ElDominio/rusefi/.junie/ts-readme.md

- files: `firmware/tunerstudio/readme.md`
- TunerStudio Help Documentation: `.junie/ts-help-topic.md`
- TunerStudio Persistence: `firmware/tunerstudio/readme-persistence.md`
- Validation: Scan `firmware/tunerstudio/generated/rusefi_uaefi.ini` to verify final field names, gauge mappings, and output channel logic.
- UI Pattern: Prefer wrapping 3D tables/curves into a `dialog` with `border` layout, placing the table (West) and a status `panel` (East) side-by-side. The status panel should contain relevant gauges and calibration fields (e.g., offsets, PID status).
- TS templating: Names defined in `rusefi_config.txt` using `#define SOME_NAME "String Value"` can be used in `tunerstudio.template.ini` as `@@SOME_NAME@@`.
- Dialog/Panel validation: The build tool strictly validates that all referenced panels exist. Suffixes starting with `@@` (used for conditional visibility) are automatically ignored during name comparison.
- [UserDefined] section: Dialog and panel definitions should generally be placed in this section of the template to maintain organization.
- Gauge templates (`firmware/tunerstudio/gauge_declarations.ini`, `[GaugeConfigurations]`): `name = channel, title, units, Lo, Hi, LoD, LoW, HiW, HiD, vd, ld`. Lo/Hi are the scale limits; below LoD or above HiD TunerStudio renders the danger (error) color, below LoW / above HiW the warning color; vd/ld are value/label decimal places. To flag an out-of-range value as error with no warning band, set LoD=LoW and HiW=HiD (e.g. raw 5V sensor gauges use 0.2/0.2 and 4.8/4.8 so <0.2V or >4.8V shows as error). Source of truth: "EFI Analytics ECU Definition files" PDF at https://www.efianalytics.com/TunerStudio/docs/ (section 12, GaugeConfigurations).
