ElDominio/rusefi/firmware/controllers/lua/generated/value_lookup_generated.md

### startButtonSuppressOnStartUpMs
null

### launchRpm
The target engine speed (RPM) to maintain during launch.

### rpmHardLimit
set rpm_hard_limit X

### engineSnifferRpmThreshold
Engine sniffer would be disabled above this rpm\nset engineSnifferRpmThreshold X

### ltitEnabled
Enable LTIT (Long Term Idle Trim) learning

### useMetricOnInterface

### useLambdaOnInterface

### multisparkMaxRpm
Disable multispark above this engine speed.

### maxAcRpm
Above this RPM, disable AC. Set to 0 to disable check.

### maxAcTps
Above this TPS, disable AC. Set to 0 to disable check.

### maxAcClt
Above this CLT, disable AC to prevent overheating the engine. Set to 0 to disable check.

### compressionRatio
Just for reference really, not taken into account by any logic at this point

### idlePositionMin
Voltage when the idle valve is closed.\nYou probably don't have one of these!

### idlePositionMax
Voltage when the idle valve is open.\nYou probably don't have one of these!\n1 volt = 1000 units

### ltitEmaAlpha
EMA filter constant for LTIT (0-255)

### ltitStableRpmThreshold
RPM range to consider stable idle

### ltitStableTime
Minimum time of stable idle before learning

### ltitCorrectionRate
LTIT learning rate

### ltitIgnitionOnDelay
Delay after ignition ON before LTIT learning/application

### ltitIgnitionOffSaveDelay
Delay after ignition OFF before LTIT save

### ltitClampMin
Minimum LTIT multiplicative correction value

### ltitClampMax
Maximum LTIT multiplicative correction value

### ltitSmoothingIntensity
LTIT table regional smoothing intensity (0=no smoothing)

### ltitIntegratorThreshold
Minimum threshold of PID integrator for LTIT correction

### launchFuelAdderPercent
Fuel enrichment adder percentage.

### etbJamTimeout
Time after which the throttle is considered jammed.

### primingTriggerTeeth
Number of primary trigger teeth to see (since ignition-on) before firing the priming pulse. Counting is raw and does not require trigger sync. Only used when 'primeOnTriggerTeeth' is enabled.

### multisparkMaxSparkingAngle
This parameter sets the latest that the last multispark can occur after the main ignition event. For example, if the ignition timing is 30 degrees BTDC, and this parameter is set to 45, no multispark will ever be fired after 15 degrees ATDC.

### multisparkMaxExtraSparkCount
Configures the maximum number of extra sparks to fire (does not include main spark)

### vvtControlMinRpm

### injector.flow
This is your injector flow at the fuel pressure used in the vehicle\nSee units setting below

### injectorSecondary.flow
This is your injector flow at the fuel pressure used in the vehicle\nSee units setting below

### isForcedInduction
Does the vehicle have a turbo or supercharger?

### useFordRedundantTps
On some Ford and Toyota vehicles one of the throttle sensors is not linear on the full range, i.e. in the specific range of the positions we effectively have only one sensor.

### enableKline

### overrideTriggerGaps

### chtSensorPulldown

### useLinearChtSensor

### enableTrailingSparks
Enable secondary spark outputs that fire after the primary (rotaries, twin plug engines).

### etb_use_two_wires
TLE7209 and L6205 use two-wire mode. TLE9201 and VNH2SP30 do NOT use two wire mode.

### isDoubleSolenoidIdle
Subaru/BMW style where default valve position is somewhere in the middle. First solenoid opens it more while second can close it more than default position.

### useEeprom

### useCicPidForIdle
Switch between Industrial and Cic PID implementation

### useTLE8888_cranking_hack

### kickStartCranking
Kick-start cranking mode: below 800 RPM both coils are charged right at the trigger mark and fired a dwell-time later, normal spark scheduling is suppressed.

### useSeparateIdleTablesForCrankingTaper
This uses separate ignition timing and VE tables not only for idle conditions, also during the postcranking-to-idle taper transition (See also afterCrankingIACtaperDuration).

### launchControlEnabled

### antiLagEnabled

### useRunningMathForCranking
For cranking either use the specified fixed base fuel mass, or use the normal running math (VE table). Note: in 'Fuel Map' (running math) mode the base mass already reflects the flex-adjusted stoich ratio, so the cranking flex multipliers act as ADDITIONAL enrichment on top of that - do not re-apply the full ethanol correction there.

### crankingAirAmountEnabled
Enable CLT-based cranking air amount table. During cranking, open-loop valve position is taken from this table instead of the running idle tables.

### crankingIdleRpmFlareEnabled
Enable CLT-based cranking idle RPM flare. An RPM adder from the table is applied during cranking, tapering to zero as the engine transitions to idle.

### displayLogicLevelsInEngineSniffer
Shall we display real life signal or just the part consumed by trigger decoder.\nApplies to both trigger and cam/vvt input.

### useTLE8888_stepper

### usescriptTableForCanSniffingFiltering

### verboseCan
Print incoming and outgoing first bus CAN messages in rusEFI console

### artificialTestMisfire
Experimental setting that will cause a misfire\nDO NOT ENABLE.

### useFordRedundantPps
On some Ford and Toyota vehicles one of the pedal sensors is not linear on the full range, i.e. in the specific range of the positions we effectively have only one sensor.

### cltSensorPulldown

### iatSensorPulldown

### allowIdenticalPps

### overrideVvtTriggerGaps

### useSpiImu
If enabled - use onboard SPI Accelerometer, otherwise listen for CAN messages

### enableStagedInjection

### useIdleAdvanceWhileCoasting

### tpsErrorDetectionTooLow
TPS error detection: what throttle % is unrealistically low?\nAlso used for accelerator pedal error detection if so equipped.

### tpsErrorDetectionTooHigh
TPS error detection: what throttle % is unrealistically high?\nAlso used for accelerator pedal error detection if so equipped.

### cranking.rpm
This sets the RPM limit below which the ECU will use cranking fuel and ignition logic, typically this is around 350-450rpm. \nset cranking_rpm X

### ignitionDwellForCrankingMs
Dwell duration while cranking

### etbRevLimitRange
RPM below the hard RPM limit at which the ETB rev limiter PID starts managing throttle position. Below this window throttle control is normal.

### etbRevLimitSeedTps
Throttle position the ETB rev limiter PID seeds itself with as soon as it engages, so it starts near the right operating point instead of ramping up from zero.

### etbRevLimitKp
Proportional gain for the ETB rev limiter PID.

### etbRevLimitKi
Integral gain for the ETB rev limiter PID.

### etbRevLimitKd
Derivative gain for the ETB rev limiter PID.

### map.sensor.lowValue
kPa/psi value at low volts

### map.sensor.highValue
kPa/psi value at high volts

### clt.config.tempC_1

### clt.config.tempC_2

### clt.config.tempC_3

### clt.config.resistance_1

### clt.config.resistance_2

### clt.config.resistance_3

### clt.config.bias_resistor
Pull-up resistor value on your board

### iat.config.tempC_1

### iat.config.tempC_2

### iat.config.tempC_3

### iat.config.resistance_1

### iat.config.resistance_2

### iat.config.resistance_3

### iat.config.bias_resistor
Pull-up resistor value on your board

### launchTimingRetard
The target absolute ignition timing value (e.g., -10 means -10 degrees, not 10 degrees of retard relative to base timing).

### idleMaximumAirmass
Maximum commanded airmass for the idle controller.

### alternator_iTermMin
iTerm min value

### alternator_iTermMax
iTerm max value

### displacement
@@DISPLACEMENT_TOOLTIP@@

### triggerSimulatorRpm

### cylindersCount
Number of cylinder the engine has.

### justATempTest
null

### mapSyncThreshold
Delta kPa/psi for MAP sync

### cylinderBore
@@CYLINDER_BORE_TOOLTIP@@

### ALSMaxTPS

### boostControlMinRpm
Minimum RPM to enable boost control. Use this to avoid solenoid noise at idle, and help spool in some cases.

### boostControlMinTps
Minimum TPS to enable boost control. Use this to avoid solenoid noise at idle, and help spool in some cases.

### boostControlMinMap
Minimum MAP to enable boost control. Use this to avoid solenoid noise at idle, and help spool in some cases.

### crankingTimingAngle
Ignition advance angle used during engine cranking, 5-10 degrees will work as a base setting for most engines.\nThere is tapering towards running timing advance\nset cranking_timing_angle X

### gapTrackingLengthOverride
How many consecutive gap rations have to match expected ranges for sync to happen

### maxIdleVss
Above this speed, disable closed loop idle control. Set to 0 to disable (allow closed loop idle at any speed).

### camDecoder2jzPrecision
Allowed range around detection position

### minOilPressureAfterStart
Expected oil pressure after starting the engine. If oil pressure does not reach this level within 5 seconds of engine start, fuel will be cut. Set to 0 to disable and always allow starting.

### fixedModeTiming
This value is the ignition timing used when in 'fixed timing' mode, i.e. constant timing\nThis mode is useful when adjusting distributor location.

### globalTriggerAngleOffset
Angle between Top Dead Center (TDC) and the first trigger event.\nPositive value in case of synchronization point before TDC and negative in case of synchronization point after TDC\n.Knowing this angle allows us to control timing and other angles in reference to TDC.\nHOWTO:\n1: Switch to fixed timing mode on 'ignition setting' dialog\n2: use an actual timing light to calibrate\n3: add/subtract until timing light confirms desired fixed timing value!'

### analogInputDividerCoefficient
Ratio/coefficient of input voltage dividers on your PCB. For example, use '2' if your board divides 5v into 2.5v. Use '1.66' if your board divides 5v into 3v.

### vbattDividerCoeff
This is the ratio of the resistors for the battery voltage, measure the voltage at the battery and then adjust this number until the gauge matches the reading.

### fanOnTemperature
Cooling fan turn-on temperature threshold, in Celsius

### fanOffTemperature
Cooling fan turn-off temperature threshold, in Celsius

### fan2OnTemperature
Cooling fan turn-on temperature threshold, in Celsius

### fan2OffTemperature
Cooling fan turn-off temperature threshold, in Celsius

### disableFan1AtSpeed
null

### disableFan2AtSpeed
null

### disableFan1AtSpeedHysteresis
Hysteresis below the disable-at-speed threshold before the fan is allowed back on. Prevents rapid on/off cycling at the threshold speed.

### disableFan2AtSpeedHysteresis
Hysteresis below the disable-at-speed threshold before the fan is allowed back on. Prevents rapid on/off cycling at the threshold speed.

### disableFan1WhenStopped
Inhibit operation of this fan while the engine is not running.

### disableFan2WhenStopped
Inhibit operation of this fan while the engine is not running.

### fan1PwmEnabled
Enable PWM mode for Fan 1. When enabled, the fan output is driven by the PWM curve instead of on/off relay logic.

### fan2PwmEnabled
Enable PWM mode for Fan 2. When enabled, the fan output is driven by the PWM curve instead of on/off relay logic.

### fan1PwmFrequency
Fan 1 PWM frequency

### fan2PwmFrequency
Fan 2 PWM frequency

### fan1MinPwm
Minimum PWM output clamp (Fan 1)

### fan1MaxPwm
Maximum PWM output clamp (Fan 1)

### fan2MinPwm
Minimum PWM output clamp (Fan 2)

### fan2MaxPwm
Maximum PWM output clamp (Fan 2)

### fan1AcAdder
PWM adder when AC compressor is active (Fan 1)

### fan2AcAdder
PWM adder when AC compressor is active (Fan 2)

### fan1SoftStartSec
Soft-start ramp time ? how long to ramp from 0 to target PWM (Fan 1)

### fan2SoftStartSec
Soft-start ramp time ? how long to ramp from 0 to target PWM (Fan 2)

### wizardPanelToShow

### driveWheelRevPerKm
Number of revolutions per kilometer for the wheels your vehicle speed sensor is connected to. Use an online calculator to determine this based on your tire size.

### canSleepPeriodMs
CANbus thread period in ms

### byFirmwareVersion

### idle_derivativeFilterLoss
0.1 is a good default value

### trigger.customTotalToothCount

### trigger.customSkippedToothCount

### airByRpmTaper
Extra air taper amount

### boostControlSafeDutyCycle
Duty cycle to use in case of a sensor failure. This duty cycle should produce the minimum possible amount of boost. This duty is also used in case any of the minimum RPM/TPS/MAP conditions are not met.

### acrRevolutions

### calibrationBirthday
null

### adcVcc

### mapCamDetectionAnglePosition
Magic engine phase: we compare instant MAP at X to instant MAP at x+360 angle in one complete cycle

### afr.v1

### afr.value1

### afr.v2

### afr.value2

### etbSplit
TPS/PPS error threshold

### baroSensor.lowValue
kPa/psi value at low volts

### baroSensor.highValue
kPa/psi value at high volts

### idle.solenoidFrequency

### knockRetardAggression
Ignition timing to remove when a knock event occurs. Advice: 5% (mild), 10% (turbo/high comp.), 15% (high knock, e.g. GDI), 20% (spicy lump),

### knockRetardReapplyRate
After a knock event, reapply timing at this rate.

### vssGearRatio
Number of turns of your vehicle speed sensor per turn of the wheels. For example if your sensor is on the transmission output, enter your axle/differential ratio. If you are using a hub-mounted sensor, enter a value of 1.0.

### vssFilterReciprocal
Set this so your vehicle speed signal is responsive, but not noisy. Larger value give smoother but slower response.

### vssToothCount
Number of pulses output per revolution of the shaft where your VSS is mounted. For example, GM applications of the T56 output 17 pulses per revolution of the transmission output shaft.

### vssMaxAcceleration
Reject VSS pulses that imply a faster acceleration or deceleration than this, and dead-reckon speed from the last known rate of change instead. Helps reject a single noisy tooth. Set to 0 to disable.

### fuelPumpControl.pFactor

### fuelPumpControl.iFactor

### fuelPumpControl.dFactor

### fuelPumpControl.offset
Linear addition to PID logic\nAlso known as feedforward.

### fuelPumpControl.periodMs
PID dTime

### fuelPumpControl.minValue
Output Min Duty Cycle

### fuelPumpControl.maxValue
Output Max Duty Cycle

### gapVvtTrackingLengthOverride
How many consecutive VVT gap rations have to match expected ranges for sync to happen

### idle_antiwindupFreq
0.1 is a good default value

### mc33_t_min_boost
Minimum allowed time for the boost phase. If the boost target current is reached before this time elapses, it is assumed that the injector has failed short circuit.

### finalGearRatio
Ratio between the wheels and your transmission output.

### tcuInputSpeedSensorTeeth
null

### fordInjectorSmallPulseSlope

### lambdaProtectionMinRpm

### lambdaProtectionMinLoad

### is_enabled_spi_1

### is_enabled_spi_2

### is_enabled_spi_3

### isSdCardEnabled

### rusefiVerbose29b
Use 11 bit (standard) or 29 bit (extended) IDs for rusEFI verbose CAN format.

### rethrowHardFault

### verboseQuad

### useStepperIdle
This setting should only be used if you have a stepper motor idle valve and a stepper motor driver installed.

### lambdaProtectionEnable

### verboseTLE8888

### enableVerboseCanTx
CAN broadcast using custom rusEFI protocol

### externalRusEfiGdiModule

### measureMapOnlyInOneCylinder
Useful for individual intakes

### stepperForceParkingEveryRestart

### isFasterEngineSpinUpEnabled
If enabled, RPM is estimated from ~90 degrees of rotation using tooth timestamps collected even before trigger sync, and fuel/ignition scheduling starts as soon as the trigger syncs (sequential ignition temporarily runs as wasted spark until full phase sync). As soon as the trigger syncs plus 90 degrees rotation, fuel and ignition events will occur. If disabled, worst case may require up to 4 full crank rotations before any events are scheduled.

### coastingFuelCutEnabled
This setting disables fuel injection while the engine is in overrun, this is useful as a fuel saving measure and to prevent back firing.

### useIacTableForCoasting
Override the IAC position during overrun conditions to help reduce engine breaking, this can be helpful for large engines in light weight cars or engines that have trouble returning to idle.

### useNoiselessTriggerDecoder

### useIdleTimingPidControl

### disableEtbWhenEngineStopped
Allows disabling the ETB when the engine is stopped. You may not like the power draw or PWM noise from the motor, so this lets you turn it off until it's necessary.

### is_enabled_spi_4

### pauseEtbControl
Disable the electronic throttle motor and DC idle motor for testing.\nThis mode is for testing ETB/DC idle position sensors, etc without actually driving the throttle.

### verboseKLine

### idleIncrementalPidCic

### enableAemXSeries
AEM X-Series or rusEFI Wideband

### modeledFlowIdle

### isTuningDetectorEnabled

### useAbsolutePressureForLagTime

### idleReturnTargetRamp
Ramp the idle target down from the entry threshold over N seconds when returning to idle. Helps prevent overshooting (below) the idle target while returning to idle from coasting.

### useInjectorFlowLinearizationTable

### useHbridgesToDriveIdleStepper
If enabled we use two H-bridges to drive stepper idle air valve

### multisparkEnable

### enableLaunchRetard
Enables absolute ignition timing control during launch (sets timing to the "Absolute Timing at Launch" value).

### canInputBCM

### consumeObdSensors
This property is useful if using rusEFI as TCM or BCM only

### enableCanVss
Read VSS from OEM CAN bus according to selected CAN vehicle configuration.

### stftIgnoreErrorMagnitude
If enabled, adjust at a constant rate instead of a rate proportional to the current lambda error. This mode may be easier to tune, and more tolerant of sensor noise.

### vvtBooleanForVerySpecialCases

### enableSoftwareKnock

### verboseVVTDecoding
Verbose info in console below engineSnifferRpmThreshold

### invertCamVVTSignal

### alphaNUseIat
When set to yes, it enables intake air temperature-based corrections for Alpha-N tuning strategies.

### knockBankCyl1

### knockBankCyl2

### knockBankCyl3

### knockBankCyl4

### knockBankCyl5

### knockBankCyl6

### knockBankCyl7

### knockBankCyl8

### knockBankCyl9

### knockBankCyl10

### knockBankCyl11

### knockBankCyl12

### tcuEnabled

### useRawOutputToDriveIdleStepper
If enabled we use four Push-Pull outputs to directly drive stepper idle air valve coils

### verboseCan2
Print incoming and outgoing second bus CAN messages in rusEFI console

### mainRelayDisableTime
Time after ignition turn-off before the main relay is disabled.

### verboseCanBaseAddress

### mc33_hvolt
Boost Voltage

### minimumBoostClosedLoopMap
Minimum MAP before closed loop boost is enabled. Use to prevent misbehavior upon entering boost.

### initialIgnitionCutPercent
The percentage of ignition events to cut when entering the launch control window (e.g., at Launch RPM minus Launch Control Window).

### finalIgnitionCutPercentBeforeLaunch
The percentage of ignition events to cut when the engine speed reaches the end of the corrections RPM (Launch RPM minus Launch Corrections End RPM). Between the start of the window and the end of corrections RPM, the cut percentage interpolates linearly from initial to final cut percentage.

### idlePidRpmUpperLimit
How far above idle speed do we consider idling, i.e. coasting detection threshold.\nFor example, if target = 800, this param = 200, then anything below 1000 RPM is considered idle.

### applyNonlinearBelowPulse
Apply nonlinearity correction below a pulse of this duration. Pulses longer than this duration will receive no adjustment.

### torqueReductionArmingRpm
Since torque reduction pin is usually shared with launch control, most people have an RPM where behavior under that is Launch Control, over that is Flat Shift/Torque Reduction

### stoichRatioSecondary
Stoichiometric ratio for your secondary fuel. This value is used when the Flex Fuel sensor indicates E100, typically 9.0

### etbMaximumPosition
Maximum allowed ETB position. Some throttles go past fully open, so this allows you to limit it to fully open.

### sdCardLogFrequency
Rate the ECU will log to the SD card, in hz (log lines per second).

### launchCorrectionsEndRpm
The RPM difference below the Launch RPM at which corrections (timing retard interpolation and/or ignition cut ramp) reach their final/maximum target. For example, if Launch RPM is 4000, and this is 50, corrections reach their final target at 3950 RPM.

### lambdaProtectionRestoreRpm

### mapMinBufferLength
This many MAP samples are used to estimate the current MAP. This many samples are considered, and the minimum taken. Recommended value is 1 for single-throttle engines, and your number of cylinders for individual throttle bodies.

### idlePidDeactivationTpsThreshold
Below this throttle position, the engine is considered idling. If you have an electronic throttle, this checks accelerator pedal position instead of throttle position, and should be set to 1-2%.

### stepperParkingExtraSteps

### startCrankingDuration
Maximum time to crank starter when start/stop button is pressed

### lambdaProtectionMinTps

### lambdaProtectionTimeout
Only respond once lambda is out of range for this period of time. Use to avoid transients triggering lambda protection when not needed

### disableLaunchWithClutchUp
When Launch Control is NOT activated by Clutch Up, use the Clutch Up switch to positively confirm the clutch has been released and disable launch.

### boostPid.pFactor

### boostPid.iFactor

### boostPid.dFactor

### boostPid.offset
Linear addition to PID logic\nAlso known as feedforward.

### boostPid.periodMs
PID dTime

### boostPid.minValue
Output Min Duty Cycle

### boostPid.maxValue
Output Max Duty Cycle

### boostPwmFrequency

### tpsAccelLookback
How long to look back for TPS-based acceleration enrichment. Increasing this time will trigger enrichment for longer when a throttle position change occurs.

### tpsDecelEnleanmentThreshold
For decel we simply multiply delta of TPS and tFor decel we do not use table?!

### tpsDecelEnleanmentMultiplier
Magic multiplier, we multiply delta of TPS and get fuel squirt duration

### noFuelTrimAfterDfcoTime
Pause closed loop fueling after deceleration fuel cut occurs. Set this to a little longer than however long is required for normal fueling behavior to resume after fuel cut.

### noFuelTrimAfterAccelTime
Pause closed loop fueling after acceleration fuel occurs. Set this to a little longer than however long is required for normal fueling behavior to resume after fuel accel.

### launchSpeedThreshold
Launch disabled above this speed if setting is above zero

### launchRpmWindow
The RPM window before the Launch RPM where launch control strategies (like retard/cut) begin to activate. For example, if Launch RPM is 4000 and Window is 500, activation starts at 3500 RPM.

### triggerEventsTimeoutMs

### ppsExpAverageAlpha
A higher alpha (closer to 1) means the EMA reacts more quickly to changes in the data.\n'100%' means no filtering, 98% would be some filtering.

### mapExpAverageAlpha
A higher alpha (closer to 1) means the EMA reacts more quickly to changes in the data.\n'1' means no filtering, 0.98 would be some filtering.

### magicNumberAvailableForDevTricks
null

### turbochargerFilter
null

### launchTpsThreshold

### launchActivateDelay

### stft.maxIdleRegionRpm
Below this RPM, the idle region is active, idle+300 would be a good value

### stft.maxOverrunLoad
Below this engine load, the overrun region is active\nWhen tuning by MAP the units are kPa/psi, e.g. 30 would mean 30kPa. When tuning TPS, 30 would be 30%

### stft.minPowerLoad
Above this engine load, the power region is active\nWhen tuning by MAP the units are kPa/psi

### stft.deadband
When close to correct AFR, pause correction. This can improve stability by not changing the adjustment if the error is extremely small, but is not required.

### stft.minClt
Minimum coolant temperature before closed loop operation is allowed.

### stft.minAfr
Below this AFR, correction is paused

### stft.maxAfr
Above this AFR, correction is paused

### stft.startupDelay
Time after startup before closed loop operation is allowed.

### ltft.enabled
Enables lambda sensor long term fuel corrections data gathering into LTFT trim tables

### ltft.correctionEnabled
Apply LTFT trims into fuel calculation on top of VE table.\nWe do not adjust VE table automatically, please click 'Apply to VE' if you want to adjust your VE tables and reset trims.

### ltft.deadband
When close to correct AFR, pause correction. This can improve stability by not changing the adjustment if the error is extremely small, but is not required.

### ltft.maxAdd
Maximum % that the long term fuel trim can add

### ltft.maxRemove
Maximum % that the long term fuel trim can remove

### widebandOnSecondBus
Select which bus the wideband controller is attached to.

### fuelClosedLoopCorrectionEnabled
Enables lambda sensor closed loop feedback for fuelling.

### alwaysWriteSdCard
Write SD card log even when powered by USB

### knockDetectionUseDoubleFrequency
Second harmonic (aka double) is usually quieter background noise

### yesUnderstandLocking
Unlocking only via rusEFI console using 'unlock PICODEBUG' command. Use 'reset to default firmware' if pincode is lost.

### silentTriggerError
Sometimes we have a performance issue while printing error

### useLinearCltSensor

### canReadEnabled
enable can_read/disable can_read

### canWriteEnabled
enable can_write/disable can_write. See also can1ListenMode

### useLinearIatSensor

### enableOilPressureProtect

### tachPulseDurationAsDutyCycle
Treat milliseconds value as duty cycle value, i.e. 0.5ms would become 50%

### isAlternatorControlEnabled
This enables smart alternator control and activates the extra alternator settings.

### alternatorBaseDutyUseTable
Select base duty source: a 2D table (indexed by target voltage and RPM) or the legacy scalar offset in the PID settings.

### invertPrimaryTriggerSignal
https://wiki.rusefi.com/Trigger-Configuration-Guide\nThis setting flips the signal from the primary engine speed sensor.

### invertSecondaryTriggerSignal
https://wiki.rusefi.com/Trigger-Configuration-Guide\nThis setting flips the signal from the secondary engine speed sensor.

### cutFuelOnHardLimit
When enabled, this option cuts the fuel supply when the RPM limit is reached. Cutting fuel provides a smoother limiting action; however, it may lead to slightly higher combustion chamber temperatures since unburned fuel is not present to cool the combustion process.

### cutSparkOnHardLimit
When selected, this option cuts the spark to limit RPM. Cutting spark can produce flames from the exhaust due to unburned fuel igniting in the exhaust system. Additionally, this unburned fuel can help cool the combustion chamber, which may be beneficial in high-performance applications.\nBe careful enabling this: some engines are known to self-disassemble their valvetrain with a spark cut. Fuel cut is much safer.

### launchFuelCutEnable

### launchSparkCutEnable
Enables or disables ignition/spark cut during launch control.

### torqueReductionEnabled

### camSyncOnSecondCrankRevolution
When we sync cam sensor is that first or second full engine revolution of the four stroke cycle?

### limitTorqueReductionTime

### verboseIsoTp
Are you a developer troubleshooting TS over CAN ISO/TP?

### engineSnifferFocusOnInputs
In this mode only trigger events go into engine sniffer and not coils/injectors etc

### twoStroke

### skippedWheelOnCam
Where is your primary skipped wheel located?

### etbNeutralPosition
Expected neutral position

### isInjectionEnabled

### isIgnitionEnabled

### isCylinderCleanupEnabled
When enabled if TPS is held above 95% no fuel is injected while cranking to clear excess fuel from the cylinders.

### complexWallModel
Should we use tables to vary tau/beta based on CLT/MAP, or just with fixed values?

### isMapAveragingEnabled

### useSeparateAdvanceForIdle
This activates a separate ignition timing table for idle conditions, this can help idle stability by using ignition retard and advance either side of the desired idle speed. Extra advance at low idle speeds will prevent stalling and extra retard at high idle speeds can help reduce engine power and slow the idle speed.

### isWaveAnalyzerEnabled

### useSeparateVeForIdle
This activates a separate fuel table for Idle, this allows fine tuning of the idle fuelling.

### verboseTriggerSynchDetails
Verbose info in console below engineSnifferRpmThreshold

### hondaK

### twoWireBatchIgnition
This is needed if your coils are individually wired (COP) and you wish to use batch ignition (Wasted Spark).

### useFixedBaroCorrFromMap
Read MAP sensor on ECU start-up to use as baro value.

### useSeparateAdvanceForCranking
In Constant mode, timing is automatically tapered to running as RPM increases.\nIn Table mode, the "Cranking ignition advance" table is used directly.

### useAdvanceCorrectionsForCranking
This enables the various ignition corrections during cranking (IAT, CLT and PID idle).\nYou probably don't need this.

### flexCranking
Enable flex-fuel compensation for engine start. When on (and a flex fuel sensor is present) the cranking coolant multiplier and the priming pulse mass each come from a 2D table over coolant and ethanol % (crankingFuelFlexTable / primeFlexTable, 4-row ethanol axis) instead of their 1D coolant curves. When off, the 1D curves (crankingFuelCoef / primeValues) are used.

### flexFuelTransientComp
Enable flex-fuel transient fueling compensation (acceleration enrichment and wall wetting tau/beta) based on ethanol content and coolant temperature.

### useIacPidMultTable
This flag allows to use a special 'PID Multiplier' table (0.0-1.0) to compensate for nonlinear nature of IAC-RPM controller

### isBoostControlEnabled

### launchSmoothRetard
Gradually interpolates the ignition timing from the base timing table value down to the target "Absolute Timing at Launch" value, starting from the beginning of the launch window.

### isPhaseSyncRequiredForIgnition
Some engines are OK running semi-random sequential while other engine require phase synchronization

### useCltBasedRpmLimit
If enabled, use a curve for RPM limit (based on coolant temperature) instead of a constant value.

### forceO2Heating
If enabled, don't wait for engine start to heat O2 sensors.\nWARNING: this will reduce the life of your sensor, as condensation in the exhaust from a cold start can crack the sensing element.

### invertVvtControlIntake
If increased VVT duty cycle increases the indicated VVT angle, set this to 'advance'. If it decreases, set this to 'retard'. Most intake cams use 'advance', and most exhaust cams use 'retard'.

### invertVvtControlExhaust
If increased VVT duty cycle increases the indicated VVT angle, set this to 'advance'. If it decreases, set this to 'retard'. Most intake cams use 'advance', and most exhaust cams use 'retard'.

### useBiQuadOnAuxSpeedSensors

### stepper_dc_use_two_wires

### watchOutForLinearTime

### sdCardConditionalLogging
Only write the SD log while trigger conditions are met (start/stop). Off = always log, the current behavior.

### useCompensatedMap
Compensated MAP: in Speed Density mode, normalize MAP by barometric pressure before it is used as a table load axis.\nMAP_ref = MAP / (baro / 101.325 kPa) feeds the VE lookup and the fuel/spark load axes, so the same table cells are hit regardless of altitude (WOT reads ~100 kPa at any elevation).\nThe physical air mass calculation still uses actual MAP. Requires a barometric pressure sensor; without a valid baro reading no compensation is applied.\nWorks together with the Barometric pressure correction table, which serves a different goal: this setting keeps table lookups stable across altitude, while the baro table multiplies fueling for exhaust-side scavenging effects. Either or both can be used.

### sdLogStartRpm
Start logging at/above this RPM

### sdLogStopRpm
Stop logging below this RPM. Set below 'start' for hysteresis

### sdLogStopDelay
Keep logging this many seconds after RPM drops below the stop threshold

### sdLogMinTps
Also require TPS at/above this to start logging (0 = ignore)

### sdLogMinMap
Also require MAP at/above this to start logging (0 = ignore)

### sdLogMinVss
Also require vehicle speed at/above this to start logging (0 = ignore)

### rpmRateSmoothingPct
Only used by First Order RPM mode. Smoothing applied to the RPM rate of change (the slope used to extrapolate RPM between cycles) each engine cycle. 0% = fully raw: the slope is replaced by the latest cycle-to-cycle measurement every cycle (most responsive, but cycle-to-cycle combustion/measurement noise passes straight through). Higher % blends in more of the previous slope, smoothing that noise out at the cost of slower response to genuine acceleration/deceleration. Capped at 95%: at 100% the slope would never incorporate a new measurement and would freeze permanently.

### engineChartSize

### turboSpeedSensorMultiplier

### acIdleRpmAdder
RPM added on top of the normal CLT-based idle target while A/C is enabled. Some cars need the extra speed to keep the AC efficient while idling.

### warningPeriod
set warningPeriod X

### knockDetectionWindowStart

### idleStepperReactionTime

### idleStepperTotalSteps

### torqueReductionArmingApp
Pedal position to realize that we need to reduce torque when the trigger pin is triggered

### referenceTorqueForGenerator
Reference Torque value

### referenceMapForGenerator
kPa/psi value at which Reference Torque is archived

### referenceVeForGenerator
null

### tachPulseDuractionMs
Duration in ms or duty cycle depending on selected mode

### wwaeTau
Length of time the deposited wall fuel takes to dissipate after the start of acceleration.

### alternatorControl.pFactor

### alternatorControl.iFactor

### alternatorControl.dFactor

### alternatorControl.offset
Linear addition to PID logic\nAlso known as feedforward.

### alternatorControl.periodMs
PID dTime

### alternatorControl.minValue
Output Min Duty Cycle

### alternatorControl.maxValue
Output Max Duty Cycle

### etb.pFactor

### etb.iFactor

### etb.dFactor

### etb.offset
Linear addition to PID logic\nAlso known as feedforward.

### etb.periodMs
PID dTime

### etb.minValue
Output Min Duty Cycle

### etb.maxValue
Output Max Duty Cycle

### airTaperRpmRange
RPM range above upper limit for extra air taper

### tachPulsePerRev

### mapErrorDetectionTooLow
kPa/psi value which is too low to be true

### mapErrorDetectionTooHigh
kPa/psi value which is too high to be true

### multisparkSparkDuration
How long to wait for the spark to fire before recharging the coil for another spark.

### multisparkDwell
This sets the dwell time for subsequent sparks. The main spark's dwell is set by the dwell table.

### idleRpmPid.pFactor

### idleRpmPid.iFactor

### idleRpmPid.dFactor

### idleRpmPid.offset
Linear addition to PID logic\nAlso known as feedforward.

### idleRpmPid.periodMs
PID dTime

### idleRpmPid.minValue
Output Min Duty Cycle

### idleRpmPid.maxValue
Output Max Duty Cycle

### wwaeBeta
0 = No fuel settling on port walls 1 = All the fuel settling on port walls setting this to 0 disables the wall wetting enrichment.

### throttlePedalUpVoltage

### throttlePedalWOTVoltage
Pedal in the floor

### startUpFuelPumpDuration
on IGN voltage detection turn fuel pump on to build fuel pressure

### mafFilterParameter
larger value = larger intake manifold volume

### idlePidRpmDeadZone
If the RPM closer to target than this value, disable closed loop idle correction to prevent oscillation

### mc33810DisableRecoveryMode
See Over/Undervoltage Shutdown/Retry bit in documentation

### mc33810Gpgd0Mode

### mc33810Gpgd1Mode

### mc33810Gpgd2Mode

### mc33810Gpgd3Mode

### enableExtendedCanBroadcast
Send out board statistics

### luaCanRxWorkaround
global_can_data performance hack

### flexSensorInverted

### useHardSkipInTraction

### tractionControlUseLuaGauge
Use a Lua gauge as a traction control multiplier input

### useAuxSpeedForSlipRatio
Use Aux Speed 1 as one of speeds for wheel slip ratio?

### useVssAsSecondWheelSpeed
VSS and Aux Speed 1 or Aux Speed 1 with Aux Speed 2?

### is_enabled_spi_5

### is_enabled_spi_6

### enableAemXSeriesEgt
AEM X-Series EGT gauge kit or rusEFI EGT sensor from Wideband controller

### startRequestPinInverted

### tcu_rangeSensorPulldown

### devBit01

### tcuInputSpeedSensorSharedWithVss
Input speed sensor is the same physical sensor as the main VSS

### devBit1

### devBit2

### devBit3

### devBit4

### devBit5

### devBit6

### devBit7

### invertExhaustCamVVTSignal

### enableKnockSpectrogram
"Available via TS Plugin see https://rusefi.com/s/knock"

### enableKnockSpectrogramFilter

### iacByTpsTaper
This value is an added for base idle value. Idle Value added when coasting and transitioning into idle.

### coastingFuelCutVssLow
Below this speed, disable DFCO. Use this to prevent jerkiness from fuel enable/disable in low gears.

### coastingFuelCutVssHigh
Above this speed, allow DFCO. Use this to prevent jerkiness from fuel enable/disable in low gears.

### tpsAccelEnrichmentThreshold
Maximum change delta of TPS percentage over the 'length'. Actual TPS change has to be above this value in order for TPS/TPS acceleration to kick in.

### totalGearsCount
Number of forward gears, shared by GearDetector (any count) and the TCU's Automatic mode (currently hardcoded to a 4-gear GEAR_1..GEAR_4 state machine, 5-10 gear support planned for a future release). Configured together with the per-gear ratios in the Speed Sensor dialog.

### fan1ExtraIdle
Additional idle % when fan #1 is active

### uartConsoleSerialSpeed
Band rate for primary TTL

### throttlePedalSecondaryUpVoltage

### throttlePedalSecondaryWOTVoltage
Pedal in the floor

### mc33_hpfp_i_peak

### mc33_hpfp_i_hold

### mc33_hpfp_i_hold_off
How long to deactivate power when hold current is reached before applying power again

### mc33_hpfp_max_hold
Maximum amount of time the solenoid can be active before assuming a programming error

### stepperDcInvertedPins
Enable if DC-motor driver (H-bridge) inverts the signals (eg. RZ7899 on Hellen boards)

### canOpenBLT
Allow OpenBLT on Primary CAN

### can2OpenBLT
Allow OpenBLT on Secondary CAN

### injectorFlowAsMassFlow
Select whether to configure injector flow in volumetric flow (default, cc/min) or mass flow (g/s).

### boardUseCanTerminator

### kLineDoHondaSend

### can1ListenMode
ListenMode is about acknowledging CAN traffic on the protocol level. Different from canWriteEnabled

### can2ListenMode

### camDecoder2jzPosition
Angle of tooth detection within engine phase cycle

### benchTestOnTime
Duration of each test pulse

### lambdaProtectionRestoreTps

### lambdaProtectionRestoreLoad

### boostCutPressure
Specifies the boost pressure allowed before triggering a cut. Setting this to 0 will DISABLE overboost cut.

### fixedTiming
Fixed timing, useful for TDC testing

### mapLowValueVoltage
MAP voltage for low point

### mapHighValueVoltage
MAP voltage for low point

### egoValueShift
EGO value correction

### tChargeMinRpmMinTps

### tChargeMinRpmMaxTps

### tChargeMaxRpmMinTps

### tChargeMaxRpmMaxTps

### minimumIgnitionTiming
Minimim timing advance allowed. No spark on any cylinder will ever fire after this angle BTDC. For example, setting -10 here means no spark ever fires later than 10 deg ATDC. Note that this only concerns the primary spark: any trailing sparks or multispark may violate this constraint.

### maximumIgnitionTiming
Maximum timing advance allowed. No spark on any cylinder will ever fire before this angle BTDC. For example, setting 45 here means no spark ever fires earlier than 45 deg BTDC

### alternatorPwmFrequency

### fan2ExtraIdle
Additional idle % when fan #2 is active

### primingDelay
Delay to allow fuel pressure to build before firing the priming pulse.

### fuelReferencePressure
This is the pressure at which your injector flow is known.\nFor example if your injectors flow 400cc/min at 3.5 bar, enter 350kpa/50.7psi here.\nThis is gauge pressure/in reference to atmospheric.

### auxTempSensor1.config.tempC_1

### auxTempSensor1.config.tempC_2

### auxTempSensor1.config.tempC_3

### auxTempSensor1.config.resistance_1

### auxTempSensor1.config.resistance_2

### auxTempSensor1.config.resistance_3

### auxTempSensor1.config.bias_resistor
Pull-up resistor value on your board

### auxTempSensor2.config.tempC_1

### auxTempSensor2.config.tempC_2

### auxTempSensor2.config.tempC_3

### auxTempSensor2.config.resistance_1

### auxTempSensor2.config.resistance_2

### auxTempSensor2.config.resistance_3

### auxTempSensor2.config.bias_resistor
Pull-up resistor value on your board

### knockSamplingDuration

### etbFreq

### etbWastegatePid.pFactor

### etbWastegatePid.iFactor

### etbWastegatePid.dFactor

### etbWastegatePid.offset
Linear addition to PID logic\nAlso known as feedforward.

### etbWastegatePid.periodMs
PID dTime

### etbWastegatePid.minValue
Output Min Duty Cycle

### etbWastegatePid.maxValue
Output Max Duty Cycle

### stepperMinDutyCycle
Use to limit the current when the stepper motor is idle, not moving (100% = no limit)

### stepperMaxDutyCycle
Use to limit the max.current through the stepper motor (100% = no limit)

### idlePidActivationTime

### vvtControlMinClt
Minimum coolant temperature to activate VVT

### vvtIntake_iTermMin
VVT intake cam PID: iTerm min value

### vvtIntake_iTermMax
VVT intake cam PID: iTerm max value

### vvtExhaust_iTermMin
VVT exhaust cam PID: iTerm min value

### vvtExhaust_iTermMax
VVT exhaust cam PID: iTerm max value

### oilPressure.v1

### oilPressure.value1

### oilPressure.v2

### oilPressure.value2

### auxFrequencyFilter

### coastingFuelCutRpmHigh
This sets the RPM above which fuel cut is active.

### coastingFuelCutRpmLow
This sets the RPM below which fuel cut is deactivated, this prevents jerking or issues transitioning to idle

### coastingFuelCutTps
Throttle position below which fuel cut is active. With an electronic throttle enabled, this checks against pedal position.

### coastingFuelCutClt
Fuel cutoff is disabled when the engine is cold.

### pidExtraForLowRpm
Increases PID reaction for RPM<target by adding extra percent to PID-error

### coastingFuelCutMap
MAP value above which fuel injection is re-enabled.

### highPressureFuel.v1

### highPressureFuel.value1

### highPressureFuel.v2

### highPressureFuel.value2

### lowPressureFuel.v1

### lowPressureFuel.value1

### lowPressureFuel.v2

### lowPressureFuel.value2

### tChargeAirCoefMin
Heat transfer coefficient at zero flow.\n0 means the air charge is fully heated to the same temperature as CLT.\n1 means the air charge gains no heat, and enters the cylinder at the temperature measured by IAT.

### tChargeAirCoefMax
Heat transfer coefficient at high flow, as defined by "max air flow".\n0 means the air charge is fully heated to the same temperature as CLT.\n1 means the air charge gains no heat, and enters the cylinder at the temperature measured by IAT.

### tChargeAirFlowMax
High flow point for heat transfer estimation.\nSet this to perhaps 50-75% of your maximum airflow at wide open throttle.

### tChargeAirIncrLimit
Maximum allowed rate of increase allowed for the estimated charge temperature

### tChargeAirDecrLimit
Maximum allowed rate of decrease allowed for the estimated charge temperature

### etb_iTermMin
iTerm min value

### etb_iTermMax
iTerm max value

### idleTimingPid.pFactor

### idleTimingPid.iFactor

### idleTimingPid.dFactor

### idleTimingPid.offset
Linear addition to PID logic\nAlso known as feedforward.

### idleTimingPid.periodMs
PID dTime

### idleTimingPid.minValue
Output Min Duty Cycle

### idleTimingPid.maxValue
Output Max Duty Cycle

### idleTimingSoftEntryTime
When entering idle, and the PID settings are aggressive, it's good to make a soft entry upon entering closed loop

### tpsAccelFractionPeriod
A delay in cycles between fuel-enrich. portions

### tpsAccelFractionDivisor
A fraction divisor: 1 or less = entire portion at once, or split into diminishing fractions

### idlerpmpid_iTermMin
iTerm min value

### stoichRatioPrimary
Stoichiometric ratio for your primary fuel. When Flex Fuel is enabled, this value is used when the Flex Fuel sensor indicates E0.\nE0 = 14.7\nE10 = 14.1\nE85 = 9.9\nE100 = 9.0

### idlerpmpid_iTermMax
iTerm max value

### etbIdleThrottleRange
This sets the range of the idle control on the ETB. At 100% idle position, the value specified here sets the base ETB position. Can also be interpreted as the maximum allowed TPS% Opening for Idle Control.

### triggerCompCenterVolt
Trigger comparator center point voltage

### triggerCompHystMin
Trigger comparator hysteresis voltage (Min)

### triggerCompHystMax
Trigger comparator hysteresis voltage (Max)

### triggerCompSensorSatRpm
VR-sensor saturation RPM

### mc33_i_boost
Boost Current

### mc33_i_peak
Peak Current

### mc33_i_hold
Hold Current

### mc33_t_max_boost
Maximum allowed boost phase time. If the injector current doesn't reach the threshold before this time elapses, it is assumed that the injector is missing or has failed open circuit.

### mc33_t_peak_off

### mc33_t_peak_tot
Peak phase duration

### mc33_t_bypass

### mc33_t_hold_off

### mc33_t_hold_tot
Hold phase duration

### maxCamPhaseResolveRpm
Below this RPM, use camshaft information to synchronize the crank's position for full sequential operation. Use this if your cam sensor does weird things at high RPM. Set to 0 to disable, and always use cam to help sync crank.

### dfcoDelay
Delay before cutting fuel. Set to 0 to cut immediately with no delay. May cause rumbles and pops out of your exhaust...

### acDelay
Delay before engaging the AC compressor. Set to 0 to engage immediately with no delay. Use this to prevent bogging at idle when AC engages.

### fordInjectorSmallPulseBreakPoint

### etbJamDetectThreshold
Threshold in ETB error (target vs. actual) above which the jam timer is started. If the timer reaches the time specified in the jam detection timeout period, the throttle is considered jammed, and engine operation limited.

### hpfpCamLobes

### acLowRpmLimit
Low engine speed for A/C. Larger engines can survive lower values

### hpfpMinAngle
If the requested activation time is below this angle, don't bother running the pump

### hpfpPumpVolume
Size of the pump chamber in cc. Typical Bosch HDP5 has a 9.0mm diameter, typical BMW N* stroke is 4.4mm.

### hpfpActivationAngle
How long to keep the valve activated (in order to allow the pump to build pressure and keep the valve open on its own)\nhttps://rusefi.com/forum/viewtopic.php?t=2192

### issFilterReciprocal

### hpfpPidP

### hpfpPidI

### hpfpPid_iTermMin
iTerm min value

### hpfpPid_iTermMax
iTerm max value

### hpfpTargetDecay
The fastest rate the target pressure can be reduced by. This is because HPFP have no way to bleed off pressure other than injecting fuel.

### vvtActivationDelayMs
We need to give engine time to build oil pressure without diverting it to VVT

### acrDisablePhase
During revolution where ACR should be disabled at what specific angle to disengage

### auxLinear1.v1

### auxLinear1.value1

### auxLinear1.v2

### auxLinear1.value2

### auxLinear2.v1

### auxLinear2.value1

### auxLinear2.v2

### auxLinear2.value2

### etbMinimumPosition
Set a minimum allowed target position to avoid slamming/driving against the hard mechanical stop in the throttle.

### tuneHidingKey

### torqueReductionActivationTemperature

### ALSMinRPM

### ALSMaxRPM

### ALSMaxDuration

### ALSMinCLT

### ALSMaxCLT

### alsMinTimeBetween

### alsEtbPosition

### acRelayAlternatorDutyAdder

### customSentTpsMin
null

### ALSIdleAdd

### ALSEtbAdd

### ALSSkipRatio

### acPressureEnableHyst
Hysterisis: if Pressure High Disable is 240kpa, and acPressureEnableHyst is 20, when the ECU sees 240kpa, A/C will be disabled, and stay disabled until 240-20=220kpa is reached

### tpsSecondaryMaximum
For Ford TPS, use 53%. For Toyota ETCS-i, use ~65%

### ppsSecondaryMaximum
For Toyota ETCS-i, use ~69%

### customSentTpsMax
null

### kLineBaudRate
null

### hpfpPeakPos
Crank angle ATDC of first lobe peak

### kLinePeriodUs

### rpmSoftLimitTimingRetard
Degrees of timing REMOVED from actual timing during soft RPM limit window

### rpmSoftLimitFuelAdded
% of fuel ADDED during window

### rpmHardLimitHyst
Sets a buffer below the RPM hard limit, helping avoid rapid cycling of cut actions by defining a range within which RPM must drop before cut actions are re-enabled.\nHysterisis: if the hard limit is 7200rpm and rpmHardLimitHyst is 200rpm, then when the ECU sees 7200rpm, fuel/ign will cut, and stay cut until 7000rpm (7200-200) is reached

### rpmSoftLimitRange
Width of the RPM window below the RPM hard limit over which the Soft RPM Limit's timing retard and fuel added ramp from zero up to their full configured value at the hard limit. Independent of RPM limit hysteresis, which only controls when cut actions re-enable.

### benchTestOffTime
Time between bench test pulses

### boostCutPressureHyst
Defines a pressure range below the cut limit at which boost can resume, providing smoother control over boost cut actions.\nFor example: if hard cut is 240kpa, and boost cut hysteresis is 20, when the ECU sees 240kpa, fuel/ign will cut, and stay cut until 240-20=220kpa is reached

### benchTestCount
How many test bench pulses do you want

### iacByTpsHoldTime
How long initial idle adder is held before starting to decay.

### iacByTpsDecayTime
How long it takes to remove initial IAC adder to return to normal idle.

### canVssScaling
Scale the reported vehicle speed value from CAN. Example: Parameter set to 1.1, CAN VSS reports 50kph, ECU will report 55kph instead.

### oilTempSensor.config.tempC_1

### oilTempSensor.config.tempC_2

### oilTempSensor.config.tempC_3

### oilTempSensor.config.resistance_1

### oilTempSensor.config.resistance_2

### oilTempSensor.config.resistance_3

### oilTempSensor.config.bias_resistor
Pull-up resistor value on your board

### fuelTempSensor.config.tempC_1

### fuelTempSensor.config.tempC_2

### fuelTempSensor.config.tempC_3

### fuelTempSensor.config.resistance_1

### fuelTempSensor.config.resistance_2

### fuelTempSensor.config.resistance_3

### fuelTempSensor.config.bias_resistor
Pull-up resistor value on your board

### ambientTempSensor.config.tempC_1

### ambientTempSensor.config.tempC_2

### ambientTempSensor.config.tempC_3

### ambientTempSensor.config.resistance_1

### ambientTempSensor.config.resistance_2

### ambientTempSensor.config.resistance_3

### ambientTempSensor.config.bias_resistor
Pull-up resistor value on your board

### compressorDischargeTemperature.config.tempC_1

### compressorDischargeTemperature.config.tempC_2

### compressorDischargeTemperature.config.tempC_3

### compressorDischargeTemperature.config.resistance_1

### compressorDischargeTemperature.config.resistance_2

### compressorDischargeTemperature.config.resistance_3

### compressorDischargeTemperature.config.bias_resistor
Pull-up resistor value on your board

### chtSensor.config.tempC_1

### chtSensor.config.tempC_2

### chtSensor.config.tempC_3

### chtSensor.config.resistance_1

### chtSensor.config.resistance_2

### chtSensor.config.resistance_3

### chtSensor.config.bias_resistor
Pull-up resistor value on your board

### eotEstK0
EOT-from-CHT/IAT estimation: base delta. The head/block runs this many deg C hotter than the oil at zero IAT influence.

### eotEstK1
EOT-from-CHT/IAT estimation: CHT coefficient. This fraction of the current CHT reading is added to the delta (hotter head = harder to reject heat into the oil).

### eotEstK2
EOT-from-CHT/IAT estimation: IAT coefficient. Additional deg C of delta per deg C of intake air temperature (cooler incoming air increases the delta).

### eotEstK3
EOT-from-CHT/IAT estimation: oil pressure coefficient. Additional deg C of delta per kPa of oil pressure. Higher pressure means more oil flow and better convective heat transfer, typically shrinking the delta (negative value).

### eotEstTauHeat
EOT-from-CHT/IAT estimation: heating time factor in seconds. Short blips barely register while sustained load integrates fully.

### eotEstTauCool
EOT-from-CHT/IAT estimation: cooling time factor in seconds. How long it takes for the delta to decay after load drops. Usually longer than heating because oil retains heat after load disappears.

### eotEstFallbackEot
Fallback EOT value used when the CHT sensor or oil pressure reads invalid.

### pad_eot_reserved

### speedometerPulsePerKm
Number of speedometer pulses per kilometer travelled.

### ignKeyAdcDivider
null

### tractionControlHoldTime
Traction control hold time. When traction control is active, the peak drop values are held for this duration.

### tractionControlDecayTime
Traction control decay time. After the hold time expires, values decay back to the current table value over this duration.

### maxInjectorDutyInstant
This sets an immediate limit on injector duty cycle. If this threshold is reached, the system will immediately cut the injectors.

### maxInjectorDutySustained
This limit allows injectors to operate up to the specified duty cycle percentage for a short period (as defined by the delay). After this delay, if the duty cycle remains above the limit, it will trigger a cut.

### maxInjectorDutySustainedTimeout
Timeout period for duty cycle over the sustained limit to trigger duty cycle protection.

### auxSpeed1Multiplier
null

### brakeMeanEffectivePressureDifferential
null

### tunerStudioSerialSpeed
Secondary TTL channel baud rate

### anotherCiTest
null

### tcu_rangeSensorBiasResistor

### mc33810Nomi
Nominal coil charge current, 0.25A step

### mc33810Maxi
Maximum coil charge current, 1A step

### acPressure.v1

### acPressure.value1

### acPressure.v2

### acPressure.value2

### minAcPressure
value of A/C pressure in kPa/psi before that compressor is disengaged

### maxAcPressure
value of A/C pressure in kPa/psi after that compressor is disengaged

### clutchPressure.v1

### clutchPressure.value1

### clutchPressure.v2

### clutchPressure.value2

### minimumOilPressureTimeout
Delay before cutting fuel due to low oil pressure. Use this to ignore short pressure blips and sensor noise.

### auxLinear3.v1

### auxLinear3.value1

### auxLinear3.v2

### auxLinear3.value2

### auxLinear4.v1

### auxLinear4.value1

### auxLinear4.v2

### auxLinear4.value2

### engineShutDownPeriod

### knockSuppressMinTps
Below TPS value all knock suppression will be disabled.

### knockFuelTrimAggression
Fuel to odd when a knock event occurs. Advice: 5% (mild), 10% (turbo/high comp.), 15% (high knock, e.g. GDI), 20% (spicy lump),

### knockFuelTrimReapplyRate
After a knock event, reapply fuel at this rate.

### knockFuelTrim
Maximum Amount of Fuel trim when knock

### knockSpectrumSensitivity

### knockFrequency
"Estimated knock frequency, ignore cylinderBore if this one > 0"

### secondaryInjectorFuelReferencePressure
This is the pressure at which your injector flow is known.\nFor example if your injectors flow 400cc/min at 3.5 bar, enter 350kpa here.

### nitrousControlEnabled

### vvlControlEnabled

### exhaustCutoutEnabled

### exhaustCutoutShowOpenState

### exhaustCutoutInvertedOutput

### exhaustCutoutKeyOnTestEnabled

### exhaustCutoutEngineOnTestEnabled

### useEngineStateMachine
Centralized Engine State Machine. When enabled, state detection is driven by a single priority-ordered evaluator. When disabled, each controller manages its own state detection.

### cdvControlEnabled

### cdvUseClutchExit
Deactivate CDV solenoid when clutch pedal is released

### luaLimiterEnabled

### cdvSmartMode
Clutch Delay Valve activation mode. Simple: activate on launch/pre-launch entry. Smart: also require clutch pressure to be inside the configured window (cdvSmartMinPressure/cdvSmartMaxPressure) before activating, and deactivate immediately on leaving the window.

### cutEtbOnRpmLimit
Uses Electronic Throttle Limiting (a PID) to try to hold engine RPM about 50rpm below the hard RPM limit, instead of (or in addition to) cutting fuel/spark at the limit. This is a real distinction from the hard RPM limit: the hard limit only cuts, while this tries to actively manage throttle to stay just under it.

### coastingFuelCutRequiresGear
When enabled, overrun fuel cut will not engage while the transmission is in neutral (DetectedGear sensor reads neutral).\nRequires the gear ratio table (Total Gear Count / gear ratios) to be configured: if it is not set up, the detected gear always reads neutral and fuel cut will never engage.

### eotFromIatCht
Use CHT/IAT sensors to estimate oil temperature (EOT) via first-order thermal model. Disable if a real oil temp sensor is wired.

### primeOnTriggerTeeth
When enabled, the priming pulse fires after 'primingTriggerTeeth' raw primary trigger teeth are seen since ignition-on, instead of after the fixed 'primingDelay'. Tooth counting does not require trigger sync, and (like the fixed-delay mode) the pulse still only fires once per key cycle.

### nitrousLuaGaugeArmingValue

### nitrousMinimumTps

### nitrousMinimumClt

### nitrousMaximumMap

### nitrousMaximumAfr

### nitrousActivationRpm

### nitrousDeactivationRpm

### nitrousDeactivationRpmWindow

### dfcoRetardDeg
Retard timing by this amount during DFCO. Smooths the transition back from fuel cut. After fuel is restored, ramp timing back in over the period specified.

### dfcoRetardRampInTime
Smooths the transition back from fuel cut. After fuel is restored, ramp timing back in over the period specified.

### nitrousFuelAdderPercent

### nitrousIgnitionRetard
Retard timing to remove from actual final timing (after all corrections) due to additional air.

### nitrousMinimumVehicleSpeed

### fuelLevelAveragingAlpha
Exponential Average Alpha filtering parameter

### fuelLevelUpdatePeriodSec
How often do we update fuel level gauge

### fuelLevelLowThresholdVoltage
Error below specified value

### fuelLevelHighThresholdVoltage
Error above specified value

### afrExpAverageAlpha
A higher alpha (closer to 1) means the EMA reacts more quickly to changes in the data.\n'1' means no filtering, 0.98 would be some filtering.

### sparkHardwareLatencyCorrection
Compensates for trigger delay due to belt stretch, or other electromechanical issues. beware that raising this value advances ignition timing!

### maxOilPressureTimeout
Delay before cutting fuel due to extra high oil pressure. Use this to ignore short pressure blips and sensor noise.

### wastegatePositionOpenedVoltage
Voltage when the wastegate is fully open

### wastegatePositionClosedVoltage
Voltage when the wastegate is closed

### vvlController.fuelAdderPercent

### vvlController.ignitionRetard
Retard timing to remove from actual final timing (after all corrections) due to additional air.

### vvlController.minimumTps

### vvlController.minimumClt

### vvlController.maximumMap

### vvlController.maximumAfr

### vvlController.activationRpm

### vvlController.deactivationRpm

### vvlController.deactivationRpmWindow

### rotationalIdleController.enabled
rotational idle enable feature

### rotationalIdleController.auto_engage
Automatic engagement of rotational idle

### rotationalIdleController.max_tps
Engage rotational idle under this Driver Intent.

### rotationalIdleController.auto_engage_clt_enable
Rotational Idle Auto engage CLT

### rotationalIdleController.auto_engage_clt
Rotational Idle Auto engage CLT.

### launchRpmThreshold
Launch RPM Threshold: when above 0, launch only engages if the activation switch (button/clutch) is pressed at or below this RPM, and stays latched while held - even past this RPM. This lets a standing launch (switch pressed low, revved up) coexist with flat shift / torque reduction (switch blipped high during an upshift). 0 disables the gate (legacy behavior).

### popsAndBangsEnabled
Enable pops and bangs mode. WARNING: will damage catalytic converters and reduce turbocharger life.

### dwellDutyModeEnabled
Dwell Duty Mode: when enabled, ignores the RPM/voltage dwell tables and computes dwell as a fixed percentage of the time between consecutive ignition pulses. Required for Ford TFI modules that expect a 50% duty cycle square wave.

### dwellDutyPercent
Dwell Duty Mode: percentage of the inter-spark interval used as coil dwell time. 50 = half the interval between pulses (standard TFI target).

### tcu_shiftTime

### tcuIdleShiftToFirstEnabled

### tcuIdleShiftToFirstMaxVss
Idle-shift VSS threshold. A value of 0 disables the speed check entirely, so only the idle RPM/TPS condition is required.

### cel_battery_min_v
"Minimum Battery Voltage"

### cel_battery_max_v
"Maximum Battery Voltage"

### cel_map_min_v
"Minimum MAP V"

### cel_map_max_v
"Maximum MAP V"

### cel_iat_min_v
"Minimum IAT V"

### cel_iat_max_v
"Maximum IAT V"

### cel_tps_min_v
"Minimum TPS V"

### cel_tps_max_v
"Maximum TPS V"

### dynoRpmStep
@@DYNO_RPM_STEP_TOOLTIP@@

### dynoSaeTemperatureC
@@DYNO_SAE_TEMPERATURE_C_TOOLTIP@@

### dynoSaeRelativeHumidity
@@DYNO_SAE_RELATIVE_HUMIDITY_TOOLTIP@@

### dynoSaeBaro
@@DYNO_SAE_BARO_TOOLTIP@@

### dynoCarWheelDiaInch
@@DYNO_CAR_WHEEL_DIA_INCH_TOOLTIP@@

### dynoCarWheelAspectRatio
@@DYNO_CAR_WHEEL_ASPECT_RATIO_TOOLTIP@@

### dynoCarWheelTireWidthMm
@@DYNO_CAR_WHEEL_TIRE_WIDTH_TOOLTIP@@

### dynoCarGearPrimaryReduction
@@DYNO_CAR_GEAR_PRIMARY_REDUCTION_TOOLTIP@@

### dynoCarGearRatio
@@DYNO_CAR_GEAR_RATIO_TOOLTIP@@

### dynoCarGearFinalDrive
@@DYNO_CAR_GEAR_FINAL_DRIVE_TOOLTIP@@

### dynoCarCarMassKg
@@DYNO_CAR_CAR_MASS_TOOLTIP@@

### dynoCarCargoMassKg
@@DYNO_CAR_CARGO_MASS_TOOLTIP@@

### dynoCarCoeffOfDrag
@@DYNO_CAR_COEFF_OF_DRAG_TOOLTIP@@

### dynoCarFrontalAreaM2
@@DYNO_CAR_FRONTAL_AREA_TOOLTIP@@

### wizardNumberOfCylinders

### wizardFiringOrder

### wizardMapSensorType

### wizardCrankTrigger

### wizardCamTrigger

### wizardInjectorFlow

### wizardDisplacement

### wizardCltSensor

### wizardTps

### wizardIgnitionOutputs

### wizardInjectorOutputs
