ElDominio/rusefi/firmware/config/boards/fw-custom-paralela-master/generated/canned-tunes/COUPE-BK2-comparing-against-current-COUPE-BK2-default.md

# COUPE-BK2-comparing-against-current-COUPE-BK2-default

// canned tune https://rusefi.com/online/view.php?msq=1507

```
    // default 0.0
    engineConfiguration->cylinderBankSelect[0] = 1;
    // default 0.0
    engineConfiguration->cylinderBankSelect[1] = 1;
    // default 0.0
    engineConfiguration->cylinderBankSelect[2] = 1;
    // default 0.0
    engineConfiguration->cylinderBankSelect[3] = 1;
    // default 0.0
    engineConfiguration->cylinderBankSelect[4] = 1;
    // default 0.0
    engineConfiguration->cylinderBankSelect[5] = 1;
    // default 0.0
    engineConfiguration->cylinderBankSelect[6] = 1;
    // default 0.0
    engineConfiguration->cylinderBankSelect[7] = 1;
    // default 0.0
    engineConfiguration->cylinderBankSelect[8] = 1;
    // default 0.0
    engineConfiguration->cylinderBankSelect[9] = 1;
    // default 0.0
    engineConfiguration->cylinderBankSelect[10] = 1;
    // default 0.0
    engineConfiguration->cylinderBankSelect[11] = 1;
    // default "Normal"
    engineConfiguration->clutchDownPinInverted = false;
    // default "Normal"
    engineConfiguration->clutchUpPinInverted = false;
    // default 300.0
    engineConfiguration->idle.solenoidFrequency = 200;
    // default "false"
    engineConfiguration->stepperDcInvertedPins = true;
    // default 0.0
    engineConfiguration->idleTimingPid.dFactor = 5.0E-5;
    // default 20.0
    engineConfiguration->knockRetardAggression = 0;
    // default 3.0
    engineConfiguration->knockRetardReapplyRate = 0;
    // default "Executor"
    engineConfiguration->debugMode = DBG_22;
    // default 200.0
    engineConfiguration->rpmSoftLimitWindowSize = 0;
    // default 4.0
    engineConfiguration->rpmSoftLimitTimingRetard = 0;
    // default 250.0
    engineConfiguration->etbRevLimitRange = 0;
    // default 2000.0
    engineConfiguration->boostControlMinRpm = 0;
    // default 30.0
    engineConfiguration->boostControlMinTps = 0;
    // default 110.0
    engineConfiguration->boostControlMinMap = 0;
    // default 1.0
    engineConfiguration->etbJamTimeout = 0;

	coupleBK2cannedtpsTspCorrValuesBins();
	coupleBK2cannedtpsTspCorrValues();
	coupleBK2cannedprimeBins();
	coupleBK2cannedprimeValues();
	coupleBK2cannedmap_samplingAngleBins();
	coupleBK2cannedmap_samplingWindowBins();
	coupleBK2cannedvrThreshold1_rpmBins();
	coupleBK2cannedvrThreshold2_rpmBins();
	coupleBK2cannedcltRevLimitRpmBins();
	coupleBK2cannedcltIdleCorrBins();
	coupleBK2cannedcltIdleCorr();
	coupleBK2cannedcltCrankingCorr();
	coupleBK2cannedcltIdleRpm();
	coupleBK2cannedidleAdvanceBins();
	coupleBK2cannedidleAdvance();
	coupleBK2cannedignBlends1_blendBins();
	coupleBK2cannedignBlends1_blendValues();
	coupleBK2cannedignBlends2_blendBins();
	coupleBK2cannedignBlends2_blendValues();
	coupleBK2cannedignBlends3_blendBins();
	coupleBK2cannedignBlends3_blendValues();
	coupleBK2cannedignBlends4_blendBins();
	coupleBK2cannedignBlends4_blendValues();
	coupleBK2cannedveBlends1_blendBins();
	coupleBK2cannedveBlends1_blendValues();
	coupleBK2cannedveBlends2_blendBins();
	coupleBK2cannedveBlends2_blendValues();
	coupleBK2cannedveBlends3_blendBins();
	coupleBK2cannedveBlends3_blendValues();
	coupleBK2cannedveBlends4_blendBins();
	coupleBK2cannedveBlends4_blendValues();
	coupleBK2cannedtpsTpsAccelTable();
	coupleBK2cannedboostRpmBins();
	coupleBK2cannedboostTableOpenLoop();
	coupleBK2cannedscriptTable4RpmBins();
	coupleBK2cannedscriptTable4();
	coupleBK2cannedignitionRpmBins();
	coupleBK2cannedignitionLoadBins();
	coupleBK2cannedignBlends1_rpmBins();
	coupleBK2cannedignBlends1_loadBins();
	coupleBK2cannedignBlends2_rpmBins();
	coupleBK2cannedignBlends2_loadBins();
	coupleBK2cannedignBlends3_rpmBins();
	coupleBK2cannedignBlends3_loadBins();
	coupleBK2cannedignBlends4_rpmBins();
	coupleBK2cannedignBlends4_loadBins();
	coupleBK2cannedveBlends1_rpmBins();
	coupleBK2cannedveBlends1_loadBins();
	coupleBK2cannedveBlends2_rpmBins();
	coupleBK2cannedveBlends2_loadBins();
	coupleBK2cannedveBlends3_rpmBins();
	coupleBK2cannedveBlends3_loadBins();
	coupleBK2cannedveBlends4_rpmBins();
	coupleBK2cannedveBlends4_loadBins();
	coupleBK2cannedveRpmBins();
	coupleBK2cannedveLoadBins();
	coupleBK2cannedfuelTrimRpmBins();
	coupleBK2cannedfuelTrimLoadBins();
	coupleBK2cannedignTrimRpmBins();
	coupleBK2cannedignTrimLoadBins();
	coupleBK2cannedpedalToTpsRpmBins();
	coupleBK2cannedpedalToTpsTable();
	coupleBK2cannedlambdaTable();
	coupleBK2cannedtcuSolenoidTable();
	coupleBK2cannedhpfpTargetRpmBins();
	coupleBK2cannedhpfpCompensationRpmBins();
	coupleBK2cannedpostCrankingFactor();
```
