ElDominio/rusefi/firmware/config/boards/fw-custom-paralela-master/generated/controllers/lua/generated/value_lookup_generated.md

### startButtonSuppressOnStartUpMs
null

### launchRpm
A secondary Rev limit engaged by the driver to help launch the vehicle faster

### rpmHardLimit
set rpm_hard_limit X

### engineSnifferRpmThreshold
Engine sniffer would be disabled above this rpm\nset engineSnifferRpmThreshold X

### ltitEnabled
Enable LTIT (Long Term Idle Trim) learning

### useMetricOnInterface

### useLambdaOnInterface

### multisparkMaxRpm
Disable multispark above this engine speed.

### maxAcRpm
Above this RPM, disable AC. Set to 0 to disable check.

### maxAcTps
Above this TPS, disable AC. Set to 0 to disable check.

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

### compressionRatio
Just for reference really, not taken into account by any logic at this point

### idlePositionMin
Voltage when the idle valve is closed.\nYou probably don't have one of these!

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

### ltitEmaAlpha
EMA filter constant for LTIT (0-255)

### ltitStableRpmThreshold
RPM range to consider stable idle

### ltitStableTime
Minimum time of stable idle before learning

### ltitCorrectionRate
LTIT learning rate

### ltitIgnitionOnDelay
Delay after ignition ON before LTIT learning/application

### ltitIgnitionOffSaveDelay
Delay after ignition OFF before LTIT save

### ltitClampMin
Minimum LTIT multiplicative correction value

### ltitClampMax
Maximum LTIT multiplicative correction value

### ltitSmoothingIntensity
LTIT table regional smoothing intensity (0=no smoothing)

### ltitIntegratorThreshold
Minimum threshold of PID integrator for LTIT correction

### launchFuelAdderPercent

### etbJamTimeout
Time after which the throttle is considered jammed.

### acIdleExtraOffset
Additional idle % while A/C is active

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

### multisparkMaxExtraSparkCount
Configures the maximum number of extra sparks to fire (does not include main spark)

### vvtControlMinRpm

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

### isForcedInduction
Does the vehicle have a turbo or supercharger?

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

### enableKline

### overrideTriggerGaps

### enableFan1WithAc
Turn on this fan when AC is on.

### enableFan2WithAc
Turn on this fan when AC is on.

### enableTrailingSparks
Enable secondary spark outputs that fire after the primary (rotaries, twin plug engines).

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

### useEeprom

### useCicPidForIdle
Switch between Industrial and Cic PID implementation

### useTLE8888_cranking_hack

### kickStartCranking

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

### launchControlEnabled

### antiLagEnabled

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

### useTLE8888_stepper

### usescriptTableForCanSniffingFiltering

### verboseCan
Print incoming and outgoing first bus CAN messages in rusEFI console

### artificialTestMisfire
Experimental setting that will cause a misfire\nDO NOT ENABLE.

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

### cltSensorPulldown

### iatSensorPulldown

### allowIdenticalPps

### overrideVvtTriggerGaps

### useSpiImu
If enabled - use onboard SPI Accelerometer, otherwise listen for CAN messages

### enableStagedInjection

### useIdleAdvanceWhileCoasting

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

### ignitionDwellForCrankingMs
Dwell duration while cranking

### etbRevLimitStart
Once engine speed passes this value, start reducing ETB angle.

### etbRevLimitRange
This far above 'Soft limiter start', fully close the throttle. At the bottom of the range, throttle control is normal. At the top of the range, the throttle is fully closed.

### map.sensor.lowValue
kPa/psi value at low volts

### map.sensor.highValue
kPa/psi value at high volts

### clt.config.tempC_1

### clt.config.tempC_2

### clt.config.tempC_3

### clt.config.resistance_1

### clt.config.resistance_2

### clt.config.resistance_3

### clt.config.bias_resistor
Pull-up resistor value on your board

### iat.config.tempC_1

### iat.config.tempC_2

### iat.config.tempC_3

### iat.config.resistance_1

### iat.config.resistance_2

### iat.config.resistance_3

### iat.config.bias_resistor
Pull-up resistor value on your board

### launchTimingRetard

### idleMaximumAirmass
Maximum commanded airmass for the idle controller.

### alternator_iTermMin
iTerm min value

### alternator_iTermMax
iTerm max value

### displacement
@@DISPLACEMENT_TOOLTIP@@

### triggerSimulatorRpm

### cylindersCount
Number of cylinder the engine has.

### justATempTest
null

### mapSyncThreshold
Delta kPa/psi for MAP sync

### cylinderBore
@@CYLINDER_BORE_TOOLTIP@@

### ALSMaxTPS

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

### gapTrackingLengthOverride
How many consecutive gap rations have to match expected ranges for sync to happen

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

### camDecoder2jzPrecision
Allowed range around detection position

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

### fanOnTemperature
Cooling fan turn-on temperature threshold, in Celsius

### fanOffTemperature
Cooling fan turn-off temperature threshold, in Celsius

### fan2OnTemperature
Cooling fan turn-on temperature threshold, in Celsius

### fan2OffTemperature
Cooling fan turn-off temperature threshold, in Celsius

### disableFan1AtSpeed
null

### disableFan2AtSpeed
null

### disableFan1WhenStopped
Inhibit operation of this fan while the engine is not running.

### disableFan2WhenStopped
Inhibit operation of this fan while the engine is not running.

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

### fan1PwmFrequency
Fan 1 PWM frequency

### fan2PwmFrequency
Fan 2 PWM frequency

### fan1MinPwm
Minimum PWM output clamp (Fan 1)

### fan1MaxPwm
Maximum PWM output clamp (Fan 1)

### fan2MinPwm
Minimum PWM output clamp (Fan 2)

### fan2MaxPwm
Maximum PWM output clamp (Fan 2)

### fan1AcAdder
PWM adder when AC compressor is active (Fan 1)

### fan2AcAdder
PWM adder when AC compressor is active (Fan 2)

### fan1SoftStartSec
Soft-start ramp time ? how long to ramp from 0 to target PWM (Fan 1)

### fan2SoftStartSec
Soft-start ramp time ? how long to ramp from 0 to target PWM (Fan 2)

### wizardPanelToShow

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

### canSleepPeriodMs
CANbus thread period in ms

### byFirmwareVersion

### idle_derivativeFilterLoss
0.1 is a good default value

### trigger.customTotalToothCount

### trigger.customSkippedToothCount

### airByRpmTaper
Extra air taper amount

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

### acrRevolutions

### calibrationBirthday
null

### adcVcc

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

### afr.v1

### afr.value1

### afr.v2

### afr.value2

### etbSplit
TPS/PPS error threshold

### baroSensor.lowValue
kPa/psi value at low volts

### baroSensor.highValue
kPa/psi value at high volts

### idle.solenoidFrequency

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

### knockRetardReapplyRate
After a knock event, reapply timing at this rate.

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

### gapVvtTrackingLengthOverride
How many consecutive VVT gap rations have to match expected ranges for sync to happen

### idle_antiwindupFreq
0.1 is a good default value

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

### finalGearRatio
Ratio between the wheels and your transmission output.

### tcuInputSpeedSensorTeeth
null

### fordInjectorSmallPulseSlope

### lambdaProtectionMinRpm

### lambdaProtectionMinLoad

### is_enabled_spi_1

### is_enabled_spi_2

### is_enabled_spi_3

### isSdCardEnabled

### rusefiVerbose29b
Use 11 bit (standard) or 29 bit (extended) IDs for rusEFI verbose CAN format.

### rethrowHardFault

### verboseQuad

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

### lambdaProtectionEnable

### verboseTLE8888

### enableVerboseCanTx
CAN broadcast using custom rusEFI protocol

### externalRusEfiGdiModule

### measureMapOnlyInOneCylinder
Useful for individual intakes

### stepperForceParkingEveryRestart

### isFasterEngineSpinUpEnabled
If enabled, try to fire the engine before a full engine cycle has been completed using RPM estimated from the last 90 degrees of engine rotation. As soon as the trigger syncs plus 90 degrees rotation, fuel and ignition events will occur. If disabled, worst case may require up to 4 full crank rotations before any events are scheduled.

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

### useNoiselessTriggerDecoder

### useIdleTimingPidControl

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

### is_enabled_spi_4

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

### verboseKLine

### idleIncrementalPidCic

### enableAemXSeries
AEM X-Series or rusEFI Wideband

### modeledFlowIdle

### isTuningDetectorEnabled

### useAbsolutePressureForLagTime

### verboseCanBaseAddress

### mc33_hvolt
Boost Voltage

### minimumBoostClosedLoopMap
Minimum MAP before closed loop boost is enabled. Use to prevent misbehavior upon entering boost.

### initialIgnitionCutPercent

### finalIgnitionCutPercentBeforeLaunch

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

### sdCardLogFrequency
Rate the ECU will log to the SD card, in hz (log lines per second).

### launchCorrectionsEndRpm

### lambdaProtectionRestoreRpm

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

### stepperParkingExtraSteps

### startCrankingDuration
Maximum time to crank starter when start/stop button is pressed

### lambdaProtectionMinTps

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

### useInjectorFlowLinearizationTable

### useHbridgesToDriveIdleStepper
If enabled we use two H-bridges to drive stepper idle air valve

### multisparkEnable

### enableLaunchRetard

### canInputBCM

### consumeObdSensors
This property is useful if using rusEFI as TCM or BCM only

### enableCanVss
Read VSS from OEM CAN bus according to selected CAN vehicle configuration.

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

### vvtBooleanForVerySpecialCases

### enableSoftwareKnock

### verboseVVTDecoding
Verbose info in console below engineSnifferRpmThreshold

### invertCamVVTSignal

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

### knockBankCyl1

### knockBankCyl2

### knockBankCyl3

### knockBankCyl4

### knockBankCyl5

### knockBankCyl6

### knockBankCyl7

### knockBankCyl8

### knockBankCyl9

### knockBankCyl10

### knockBankCyl11

### knockBankCyl12

### tcuEnabled

### canBroadcastUseChannelTwo

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

### verboseCan2
Print incoming and outgoing second bus CAN messages in rusEFI console

### boostPid.pFactor

### boostPid.iFactor

### boostPid.dFactor

### boostPid.offset
Linear addition to PID logic\nAlso known as feedforward.

### boostPid.periodMs
PID dTime

### boostPid.minValue
Output Min Duty Cycle

### boostPid.maxValue
Output Max Duty Cycle

### boostPwmFrequency

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

### tpsDecelEnleanmentMultiplier
Magic multiplier, we multiply delta of TPS and get fuel squirt duration

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

### launchSpeedThreshold
Launch disabled above this speed if setting is above zero

### launchRpmWindow
Starting Launch RPM window to activate (subtracts from Launch RPM)

### triggerEventsTimeoutMs

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

### magicNumberAvailableForDevTricks
null

### turbochargerFilter
null

### launchTpsThreshold

### launchActivateDelay

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

### stft.minClt
Minimum coolant temperature before closed loop operation is allowed.

### stft.minAfr
Below this AFR, correction is paused

### stft.maxAfr
Above this AFR, correction is paused

### stft.startupDelay
Time after startup before closed loop operation is allowed.

### ltft.enabled
Enables lambda sensor long term fuel corrections data gathering into LTFT trim tables

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

### ltft.maxAdd
Maximum % that the long term fuel trim can add

### ltft.maxRemove
Maximum % that the long term fuel trim can remove

### widebandOnSecondBus
Select which bus the wideband controller is attached to.

### fuelClosedLoopCorrectionEnabled
Enables lambda sensor closed loop feedback for fuelling.

### alwaysWriteSdCard
Write SD card log even when powered by USB

### knockDetectionUseDoubleFrequency
Second harmonic (aka double) is usually quieter background noise

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

### silentTriggerError
Sometimes we have a performance issue while printing error

### useLinearCltSensor

### canReadEnabled
enable can_read/disable can_read

### canWriteEnabled
enable can_write/disable can_write. See also can1ListenMode

### useLinearIatSensor

### enableOilPressureProtect

### tachPulseDurationAsDutyCycle
Treat milliseconds value as duty cycle value, i.e. 0.5ms would become 50%

### isAlternatorControlEnabled
This enables smart alternator control and activates the extra alternator settings.

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

### launchFuelCutEnable

### launchSparkCutEnable
This is the Cut Mode normally used

### torqueReductionEnabled

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

### limitTorqueReductionTime

### verboseIsoTp
Are you a developer troubleshooting TS over CAN ISO/TP?

### engineSnifferFocusOnInputs
In this mode only trigger events go into engine sniffer and not coils/injectors etc

### twoStroke

### skippedWheelOnCam
Where is your primary skipped wheel located?

### etbNeutralPosition
Expected neutral position

### isInjectionEnabled

### isIgnitionEnabled

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

### alwaysInstantRpm
RPM is measured based on last 720 degrees while instant RPM is measured based on the last 90 degrees of crank revolution

### isMapAveragingEnabled

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

### isWaveAnalyzerEnabled

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

### verboseTriggerSynchDetails
Verbose info in console below engineSnifferRpmThreshold

### hondaK

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

### useFixedBaroCorrFromMap
Read MAP sensor on ECU start-up to use as baro value.

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

### flexCranking
Enable a second cranking table to use for E100 flex fuel, interpolating between the two based on flex fuel sensor.

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

### isBoostControlEnabled

### launchSmoothRetard
Interpolates the Ignition Retard from 0 to 100% within the RPM Range

### isPhaseSyncRequiredForIgnition
Some engines are OK running semi-random sequential while other engine require phase synchronization

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

### useBiQuadOnAuxSpeedSensors

### sdTriggerLog
'Trigger' mode will write a high speed log of trigger events (warning: uses lots of space!). 'Full MLG' mode will write a standard MLG of sensors, engine function, etc. similar to the one captured in TunerStudio.

### stepper_dc_use_two_wires

### watchOutForLinearTime

### sdTriggerLogCsv

### engineChartSize

### turboSpeedSensorMultiplier

### acIdleRpmTarget
Idle target speed when A/C is enabled. Some cars need the extra speed to keep the AC efficient while idling.

### warningPeriod
set warningPeriod X

### knockDetectionWindowStart

### idleStepperReactionTime

### idleStepperTotalSteps

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

### referenceTorqueForGenerator
Reference Torque value

### referenceMapForGenerator
kPa/psi value at which Reference Torque is archived

### referenceVeForGenerator
null

### tachPulseDuractionMs
Duration in ms or duty cycle depending on selected mode

### wwaeTau
Length of time the deposited wall fuel takes to dissipate after the start of acceleration.

### alternatorControl.pFactor

### alternatorControl.iFactor

### alternatorControl.dFactor

### alternatorControl.offset
Linear addition to PID logic\nAlso known as feedforward.

### alternatorControl.periodMs
PID dTime

### alternatorControl.minValue
Output Min Duty Cycle

### alternatorControl.maxValue
Output Max Duty Cycle

### etb.pFactor

### etb.iFactor

### etb.dFactor

### etb.offset
Linear addition to PID logic\nAlso known as feedforward.

### etb.periodMs
PID dTime

### etb.minValue
Output Min Duty Cycle

### etb.maxValue
Output Max Duty Cycle

### airTaperRpmRange
RPM range above upper limit for extra air taper

### tachPulsePerRev

### mapErrorDetectionTooLow
kPa/psi value which is too low to be true

### mapErrorDetectionTooHigh
kPa/psi value which is too high to be true

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

### idleRpmPid.pFactor

### idleRpmPid.iFactor

### idleRpmPid.dFactor

### idleRpmPid.offset
Linear addition to PID logic\nAlso known as feedforward.

### idleRpmPid.periodMs
PID dTime

### idleRpmPid.minValue
Output Min Duty Cycle

### idleRpmPid.maxValue
Output Max Duty Cycle

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

### throttlePedalUpVoltage

### throttlePedalWOTVoltage
Pedal in the floor

### startUpFuelPumpDuration
on IGN voltage detection turn fuel pump on to build fuel pressure

### mafFilterParameter
larger value = larger intake manifold volume

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

### mc33810DisableRecoveryMode
See Over/Undervoltage Shutdown/Retry bit in documentation

### mc33810Gpgd0Mode

### mc33810Gpgd1Mode

### mc33810Gpgd2Mode

### mc33810Gpgd3Mode

### enableExtendedCanBroadcast
Send out board statistics

### luaCanRxWorkaround
global_can_data performance hack

### flexSensorInverted

### useHardSkipInTraction

### useAuxSpeedForSlipRatio
Use Aux Speed 1 as one of speeds for wheel slip ratio?

### useVssAsSecondWheelSpeed
VSS and Aux Speed 1 or Aux Speed 1 with Aux Speed 2?

### is_enabled_spi_5

### is_enabled_spi_6

### enableAemXSeriesEgt
AEM X-Series EGT gauge kit or rusEFI EGT sensor from Wideband controller

### startRequestPinInverted

### tcu_rangeSensorPulldown

### devBit01

### devBit0

### devBit1

### devBit2

### devBit3

### devBit4

### devBit5

### devBit6

### devBit7

### invertExhaustCamVVTSignal

### enableKnockSpectrogram
"Available via TS Plugin see https://rusefi.com/s/knock"

### enableKnockSpectrogramFilter

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

### totalGearsCount

### fan1ExtraIdle
Additional idle % when fan #1 is active

### uartConsoleSerialSpeed
Band rate for primary TTL

### throttlePedalSecondaryUpVoltage

### throttlePedalSecondaryWOTVoltage
Pedal in the floor

### mc33_hpfp_i_peak

### mc33_hpfp_i_hold

### mc33_hpfp_i_hold_off
How long to deactivate power when hold current is reached before applying power again

### mc33_hpfp_max_hold
Maximum amount of time the solenoid can be active before assuming a programming error

### stepperDcInvertedPins
Enable if DC-motor driver (H-bridge) inverts the signals (eg. RZ7899 on Hellen boards)

### canOpenBLT
Allow OpenBLT on Primary CAN

### can2OpenBLT
Allow OpenBLT on Secondary CAN

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

### boardUseCanTerminator

### kLineDoHondaSend

### can1ListenMode
ListenMode is about acknowledging CAN traffic on the protocol level. Different from canWriteEnabled

### can2ListenMode

### camDecoder2jzPosition
Angle of tooth detection within engine phase cycle

### benchTestOnTime
Duration of each test pulse

### lambdaProtectionRestoreTps

### lambdaProtectionRestoreLoad

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

### fixedTiming
Fixed timing, useful for TDC testing

### mapLowValueVoltage
MAP voltage for low point

### mapHighValueVoltage
MAP voltage for low point

### egoValueShift
EGO value correction

### tChargeMinRpmMinTps

### tChargeMinRpmMaxTps

### tChargeMaxRpmMinTps

### tChargeMaxRpmMaxTps

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

### alternatorPwmFrequency

### fan2ExtraIdle
Additional idle % when fan #2 is active

### primingDelay
Delay to allow fuel pressure to build before firing the priming pulse.

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

### auxTempSensor1.config.tempC_1

### auxTempSensor1.config.tempC_2

### auxTempSensor1.config.tempC_3

### auxTempSensor1.config.resistance_1

### auxTempSensor1.config.resistance_2

### auxTempSensor1.config.resistance_3

### auxTempSensor1.config.bias_resistor
Pull-up resistor value on your board

### auxTempSensor2.config.tempC_1

### auxTempSensor2.config.tempC_2

### auxTempSensor2.config.tempC_3

### auxTempSensor2.config.resistance_1

### auxTempSensor2.config.resistance_2

### auxTempSensor2.config.resistance_3

### auxTempSensor2.config.bias_resistor
Pull-up resistor value on your board

### knockSamplingDuration

### etbFreq

### etbWastegatePid.pFactor

### etbWastegatePid.iFactor

### etbWastegatePid.dFactor

### etbWastegatePid.offset
Linear addition to PID logic\nAlso known as feedforward.

### etbWastegatePid.periodMs
PID dTime

### etbWastegatePid.minValue
Output Min Duty Cycle

### etbWastegatePid.maxValue
Output Max Duty Cycle

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

### stepperMaxDutyCycle
Use to limit the max.current through the stepper motor (100% = no limit)

### idlePidActivationTime

### vvtControlMinClt
Minimum coolant temperature to activate VVT

### oilPressure.v1

### oilPressure.value1

### oilPressure.v2

### oilPressure.value2

### auxFrequencyFilter

### coastingFuelCutRpmHigh
This sets the RPM above which fuel cut is active.

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

### coastingFuelCutClt
Fuel cutoff is disabled when the engine is cold.

### pidExtraForLowRpm
Increases PID reaction for RPM<target by adding extra percent to PID-error

### coastingFuelCutMap
MAP value above which fuel injection is re-enabled.

### highPressureFuel.v1

### highPressureFuel.value1

### highPressureFuel.v2

### highPressureFuel.value2

### lowPressureFuel.v1

### lowPressureFuel.value1

### lowPressureFuel.v2

### lowPressureFuel.value2

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

### tChargeAirIncrLimit
Maximum allowed rate of increase allowed for the estimated charge temperature

### tChargeAirDecrLimit
Maximum allowed rate of decrease allowed for the estimated charge temperature

### etb_iTermMin
iTerm min value

### etb_iTermMax
iTerm max value

### idleTimingPid.pFactor

### idleTimingPid.iFactor

### idleTimingPid.dFactor

### idleTimingPid.offset
Linear addition to PID logic\nAlso known as feedforward.

### idleTimingPid.periodMs
PID dTime

### idleTimingPid.minValue
Output Min Duty Cycle

### idleTimingPid.maxValue
Output Max Duty Cycle

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

### tpsAccelFractionPeriod
A delay in cycles between fuel-enrich. portions

### tpsAccelFractionDivisor
A fraction divisor: 1 or less = entire portion at once, or split into diminishing fractions

### idlerpmpid_iTermMin
iTerm min value

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

### idlerpmpid_iTermMax
iTerm max value

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

### triggerCompCenterVolt
Trigger comparator center point voltage

### triggerCompHystMin
Trigger comparator hysteresis voltage (Min)

### triggerCompHystMax
Trigger comparator hysteresis voltage (Max)

### triggerCompSensorSatRpm
VR-sensor saturation RPM

### mc33_i_boost
Boost Current

### mc33_i_peak
Peak Current

### mc33_i_hold
Hold Current

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

### mc33_t_peak_off

### mc33_t_peak_tot
Peak phase duration

### mc33_t_bypass

### mc33_t_hold_off

### mc33_t_hold_tot
Hold phase duration

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

### fordInjectorSmallPulseBreakPoint

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

### hpfpCamLobes

### acLowRpmLimit
Low engine speed for A/C. Larger engines can survive lower values

### hpfpMinAngle
If the requested activation time is below this angle, don't bother running the pump

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

### issFilterReciprocal

### hpfpPidP

### hpfpPidI

### hpfpPid_iTermMin
iTerm min value

### hpfpPid_iTermMax
iTerm max value

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

### vvtActivationDelayMs
We need to give engine time to build oil pressure without diverting it to VVT

### acrDisablePhase
During revolution where ACR should be disabled at what specific angle to disengage

### auxLinear1.v1

### auxLinear1.value1

### auxLinear1.v2

### auxLinear1.value2

### auxLinear2.v1

### auxLinear2.value1

### auxLinear2.v2

### auxLinear2.value2

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

### tuneHidingKey

### torqueReductionActivationTemperature

### ALSMinRPM

### ALSMaxRPM

### ALSMaxDuration

### ALSMinCLT

### ALSMaxCLT

### alsMinTimeBetween

### alsEtbPosition

### acRelayAlternatorDutyAdder

### customSentTpsMin
null

### ALSIdleAdd

### ALSEtbAdd

### ALSSkipRatio

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

### tpsSecondaryMaximum
For Ford TPS, use 53%. For Toyota ETCS-i, use ~65%

### ppsSecondaryMaximum
For Toyota ETCS-i, use ~69%

### customSentTpsMax
null

### kLineBaudRate
null

### hpfpPeakPos
Crank angle ATDC of first lobe peak

### kLinePeriodUs

### rpmSoftLimitTimingRetard
Degrees of timing REMOVED from actual timing during soft RPM limit window

### rpmSoftLimitFuelAdded
% of fuel ADDED during window

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

### benchTestOffTime
Time between bench test pulses

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

### benchTestCount
How many test bench pulses do you want

### iacByTpsHoldTime
How long initial idle adder is held before starting to decay.

### iacByTpsDecayTime
How long it takes to remove initial IAC adder to return to normal idle.

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

### oilTempSensor.config.tempC_1

### oilTempSensor.config.tempC_2

### oilTempSensor.config.tempC_3

### oilTempSensor.config.resistance_1

### oilTempSensor.config.resistance_2

### oilTempSensor.config.resistance_3

### oilTempSensor.config.bias_resistor
Pull-up resistor value on your board

### fuelTempSensor.config.tempC_1

### fuelTempSensor.config.tempC_2

### fuelTempSensor.config.tempC_3

### fuelTempSensor.config.resistance_1

### fuelTempSensor.config.resistance_2

### fuelTempSensor.config.resistance_3

### fuelTempSensor.config.bias_resistor
Pull-up resistor value on your board

### ambientTempSensor.config.tempC_1

### ambientTempSensor.config.tempC_2

### ambientTempSensor.config.tempC_3

### ambientTempSensor.config.resistance_1

### ambientTempSensor.config.resistance_2

### ambientTempSensor.config.resistance_3

### ambientTempSensor.config.bias_resistor
Pull-up resistor value on your board

### compressorDischargeTemperature.config.tempC_1

### compressorDischargeTemperature.config.tempC_2

### compressorDischargeTemperature.config.tempC_3

### compressorDischargeTemperature.config.resistance_1

### compressorDischargeTemperature.config.resistance_2

### compressorDischargeTemperature.config.resistance_3

### compressorDischargeTemperature.config.bias_resistor
Pull-up resistor value on your board

### speedometerPulsePerKm
Number of speedometer pulses per kilometer travelled.

### ignKeyAdcDivider
null

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

### maxInjectorDutySustainedTimeout
Timeout period for duty cycle over the sustained limit to trigger duty cycle protection.

### auxSpeed1Multiplier
null

### brakeMeanEffectivePressureDifferential
null

### tunerStudioSerialSpeed
Secondary TTL channel baud rate

### anotherCiTest
null

### tcu_rangeSensorBiasResistor

### mc33810Nomi
Nominal coil charge current, 0.25A step

### mc33810Maxi
Maximum coil charge current, 1A step

### acPressure.v1

### acPressure.value1

### acPressure.v2

### acPressure.value2

### minAcPressure
value of A/C pressure in kPa/psi before that compressor is disengaged

### maxAcPressure
value of A/C pressure in kPa/psi after that compressor is disengaged

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

### auxLinear3.v1

### auxLinear3.value1

### auxLinear3.v2

### auxLinear3.value2

### auxLinear4.v1

### auxLinear4.value1

### auxLinear4.v2

### auxLinear4.value2

### engineShutDownPeriod

### knockSuppressMinTps
Below TPS value all knock suppression will be disabled.

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

### knockFuelTrimReapplyRate
After a knock event, reapply fuel at this rate.

### knockFuelTrim
Maximum Amount of Fuel trim when knock

### knockSpectrumSensitivity

### knockFrequency
"Estimated knock frequency, ignore cylinderBore if this one > 0"

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

### nitrousControlEnabled

### vvlControlEnabled

### nitrousLuaGaugeArmingValue

### nitrousMinimumTps

### nitrousMinimumClt

### nitrousMaximumMap

### nitrousMaximumAfr

### nitrousActivationRpm

### nitrousDeactivationRpm

### nitrousDeactivationRpmWindow

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

### nitrousFuelAdderPercent

### nitrousIgnitionRetard
Retard timing to remove from actual final timing (after all corrections) due to additional air.

### nitrousMinimumVehicleSpeed

### fuelLevelAveragingAlpha
Exponential Average Alpha filtering parameter

### fuelLevelUpdatePeriodSec
How often do we update fuel level gauge

### fuelLevelLowThresholdVoltage
Error below specified value

### fuelLevelHighThresholdVoltage
Error above specified value

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

### idleReturnTargetRampDuration
idle return target ramp duration

### wastegatePositionOpenedVoltage
Voltage when the wastegate is fully open

### wastegatePositionClosedVoltage
Voltage when the wastegate is closed

### vvlController.fuelAdderPercent

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

### vvlController.minimumTps

### vvlController.minimumClt

### vvlController.maximumMap

### vvlController.maximumAfr

### vvlController.activationRpm

### vvlController.deactivationRpm

### vvlController.deactivationRpmWindow

### rotationalIdleController.enabled
rotational idle enable feature

### rotationalIdleController.auto_engage
Automatic engagement of rotational idle

### rotationalIdleController.max_tps
Engage rotational idle under this Driver Intent.

### rotationalIdleController.auto_engage_clt_enable
Rotational Idle Auto engage CLT

### rotationalIdleController.auto_engage_clt
Rotational Idle Auto engage CLT.

### tcu_shiftTime

### cel_battery_min_v
"Minimum Battery Voltage"

### cel_battery_max_v
"Maximum Battery Voltage"

### cel_map_min_v
"Minimum MAP V"

### cel_map_max_v
"Maximum MAP V"

### cel_iat_min_v
"Minimum IAT V"

### cel_iat_max_v
"Maximum IAT V"

### cel_tps_min_v
"Minimum TPS V"

### cel_tps_max_v
"Maximum TPS V"

### dynoRpmStep
@@DYNO_RPM_STEP_TOOLTIP@@

### dynoSaeTemperatureC
@@DYNO_SAE_TEMPERATURE_C_TOOLTIP@@

### dynoSaeRelativeHumidity
@@DYNO_SAE_RELATIVE_HUMIDITY_TOOLTIP@@

### dynoSaeBaro
@@DYNO_SAE_BARO_TOOLTIP@@

### dynoCarWheelDiaInch
@@DYNO_CAR_WHEEL_DIA_INCH_TOOLTIP@@

### dynoCarWheelAspectRatio
@@DYNO_CAR_WHEEL_ASPECT_RATIO_TOOLTIP@@

### dynoCarWheelTireWidthMm
@@DYNO_CAR_WHEEL_TIRE_WIDTH_TOOLTIP@@

### dynoCarGearPrimaryReduction
@@DYNO_CAR_GEAR_PRIMARY_REDUCTION_TOOLTIP@@

### dynoCarGearRatio
@@DYNO_CAR_GEAR_RATIO_TOOLTIP@@

### dynoCarGearFinalDrive
@@DYNO_CAR_GEAR_FINAL_DRIVE_TOOLTIP@@

### dynoCarCarMassKg
@@DYNO_CAR_CAR_MASS_TOOLTIP@@

### dynoCarCargoMassKg
@@DYNO_CAR_CARGO_MASS_TOOLTIP@@

### dynoCarCoeffOfDrag
@@DYNO_CAR_COEFF_OF_DRAG_TOOLTIP@@

### dynoCarFrontalAreaM2
@@DYNO_CAR_FRONTAL_AREA_TOOLTIP@@

### wizardNumberOfCylinders

### wizardFiringOrder

### wizardMapSensorType

### wizardCrankTrigger

### wizardCamTrigger

### wizardInjectorFlow
