ElDominio/rusefi/unit_tests/test_results/happy-3n.logicdata.csv

Time[s] | Channel 0 | Channel 1 | Channel 2 | Channel 3 | Channel 4 | Channel 5 | Channel 6 | Channel 7
0.000000000 | 1 | 0 | 0 | 0 | 0 | 1 | 1 | 0
0.005143000 | 1 | 0 | 0 | 0 | 0 | 0 | 1 | 0
0.006302000 | 1 | 0 | 0 | 0 | 0 | 0 | 0 | 0
0.009508500 | 1 | 0 | 0 | 0 | 0 | 0 | 0 | 0
0.010597500 | 1 | 0 | 0 | 0 | 0 | 0 | 0 | 0
0.012569500 | 1 | 0 | 0 | 0 | 0 | 0 | 0 | 0
0.013658000 | 1 | 0 | 0 | 0 | 0 | 0 | 0 | 0
0.014238500 | 1 | 0 | 0 | 0 | 0 | 0 | 0 | 0
0.015045500 | 1 | 0 | 0 | 0 | 0 | 0 | 0 | 0
0.017027000 | 1 | 0 | 0 | 0 | 0 | 0 | 0 | 0
0.017744000 | 1 | 0 | 0 | 0 | 0 | 0 | 0 | 0
0.020481500 | 1 | 0 | 0 | 0 | 0 | 0 | 0 | 0
0.021122500 | 1 | 0 | 0 | 0 | 0 | 0 | 0 | 0
0.024028000 | 1 | 0 | 0 | 0 | 0 | 0 | 0 | 0
0.024744500 | 1 | 0 | 0 | 0 | 0 | 0 | 0 | 0
0.027910500 | 1 | 0 | 0 | 0 | 0 | 0 | 0 | 0
0.028652000 | 1 | 0 | 0 | 0 | 0 | 0 | 0 | 0
0.031910000 | 1 | 0 | 0 | 0 | 0 | 0 | 0 | 0
0.032688000 | 1 | 0 | 0 | 0 | 0 | 0 | 0 | 0
0.035896500 | 1 | 0 | 0 | 0 | 0 | 0 | 0 | 0
0.036860000 | 1 | 0 | 0 | 0 | 0 | 0 | 0 | 0
0.040052000 | 1 | 0 | 0 | 0 | 0 | 0 | 0 | 0
0.041146500 | 1 | 0 | 0 | 0 | 0 | 0 | 0 | 0
0.044274500 | 1 | 0 | 0 | 0 | 0 | 0 | 0 | 0
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
