ElDominio/rusefi/unit_tests/test_results/happy.logicdata.csv

Time[s] | Channel 0 | Channel 1 | Channel 2 | Channel 3 | Channel 4 | Channel 5 | Channel 6 | Channel 7
0.000000000 | 0 | 0 | 0 | 0 | 0 | 1 | 1 | 0
0.000132500 | 0 | 0 | 0 | 0 | 0 | 1 | 0 | 0
0.000157000 | 1 | 0 | 0 | 0 | 0 | 1 | 0 | 0
0.000452000 | 0 | 0 | 0 | 0 | 0 | 1 | 0 | 0
0.000670500 | 1 | 0 | 0 | 0 | 0 | 1 | 0 | 0
0.001072500 | 0 | 0 | 0 | 0 | 0 | 1 | 0 | 0
0.001183500 | 1 | 0 | 0 | 0 | 0 | 1 | 0 | 0
0.001452000 | 0 | 0 | 0 | 0 | 0 | 1 | 0 | 0
0.001603000 | 1 | 0 | 0 | 0 | 0 | 1 | 0 | 0
0.002565000 | 1 | 0 | 0 | 0 | 0 | 1 | 1 | 0
0.002685500 | 0 | 0 | 0 | 0 | 0 | 1 | 1 | 0
0.002772000 | 1 | 0 | 0 | 0 | 0 | 1 | 1 | 0
0.004270000 | 1 | 0 | 0 | 0 | 0 | 0 | 1 | 0
0.008784500 | 1 | 0 | 0 | 0 | 0 | 0 | 1 | 0
0.009725000 | 1 | 0 | 0 | 0 | 0 | 0 | 1 | 0
0.010154000 | 0 | 0 | 0 | 0 | 0 | 0 | 1 | 0
0.011757000 | 0 | 0 | 0 | 0 | 0 | 0 | 1 | 0
0.014957500 | 0 | 0 | 0 | 0 | 0 | 0 | 1 | 0
0.015893000 | 1 | 0 | 0 | 0 | 0 | 0 | 1 | 0
0.018003000 | 1 | 0 | 0 | 0 | 0 | 0 | 1 | 0
0.021571500 | 1 | 0 | 0 | 0 | 0 | 0 | 1 | 0
0.021692000 | 0 | 0 | 0 | 0 | 0 | 0 | 1 | 0
0.025354500 | 0 | 0 | 0 | 0 | 0 | 0 | 1 | 0
0.026807500 | 1 | 0 | 0 | 0 | 0 | 0 | 1 | 0
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
