ElDominio/rusefi/unit_tests/test_results/not-great-3.logicdata.csv

Time[s] | Channel 0 | Channel 1 | Channel 2 | Channel 3 | Channel 4 | Channel 5 | Channel 6 | Channel 7
0.000000000 | 0 | 0 | 0 | 0 | 0 | 1 | 1 | 0
0.000127000 | 1 | 0 | 0 | 0 | 0 | 1 | 1 | 0
0.000438000 | 1 | 0 | 0 | 0 | 0 | 0 | 1 | 0
0.000438500 | 1 | 0 | 0 | 0 | 0 | 0 | 0 | 0
0.004776500 | 1 | 0 | 0 | 0 | 0 | 0 | 0 | 0
0.005622500 | 1 | 0 | 0 | 0 | 0 | 0 | 0 | 0
0.008042000 | 1 | 0 | 0 | 0 | 0 | 0 | 0 | 0
0.011339000 | 1 | 0 | 0 | 0 | 0 | 0 | 0 | 0
0.013078000 | 1 | 0 | 0 | 0 | 0 | 0 | 0 | 0
0.013661500 | 1 | 0 | 0 | 0 | 0 | 0 | 0 | 0
0.014509500 | 1 | 0 | 0 | 0 | 0 | 0 | 0 | 0
0.016537000 | 1 | 0 | 0 | 0 | 0 | 0 | 0 | 0
0.018228500 | 1 | 0 | 0 | 0 | 0 | 0 | 0 | 0
0.019847500 | 1 | 0 | 0 | 0 | 0 | 0 | 0 | 0
0.022304000 | 1 | 0 | 0 | 0 | 0 | 0 | 0 | 0
0.022988000 | 1 | 0 | 0 | 0 | 0 | 0 | 0 | 0
0.026492500 | 1 | 0 | 0 | 0 | 0 | 0 | 0 | 0
0.026593000 | 1 | 0 | 0 | 0 | 0 | 0 | 0 | 0
0.030531500 | 1 | 0 | 0 | 0 | 0 | 0 | 0 | 0
0.030759500 | 1 | 0 | 0 | 0 | 0 | 0 | 0 | 0
0.034640500 | 1 | 0 | 0 | 0 | 0 | 0 | 0 | 0
0.034965500 | 1 | 0 | 0 | 0 | 0 | 0 | 0 | 0
0.038693500 | 1 | 0 | 0 | 0 | 0 | 0 | 0 | 0
0.039083500 | 1 | 0 | 0 | 0 | 0 | 0 | 0 | 0
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
