ElDominio/rusefi/firmware/config/boards/mega100/suprapnp/MCU.kicad_sch

## KiCad design firmware/config/boards/mega100/suprapnp/MCU.kicad_sch (2025-05-04, last stored version)

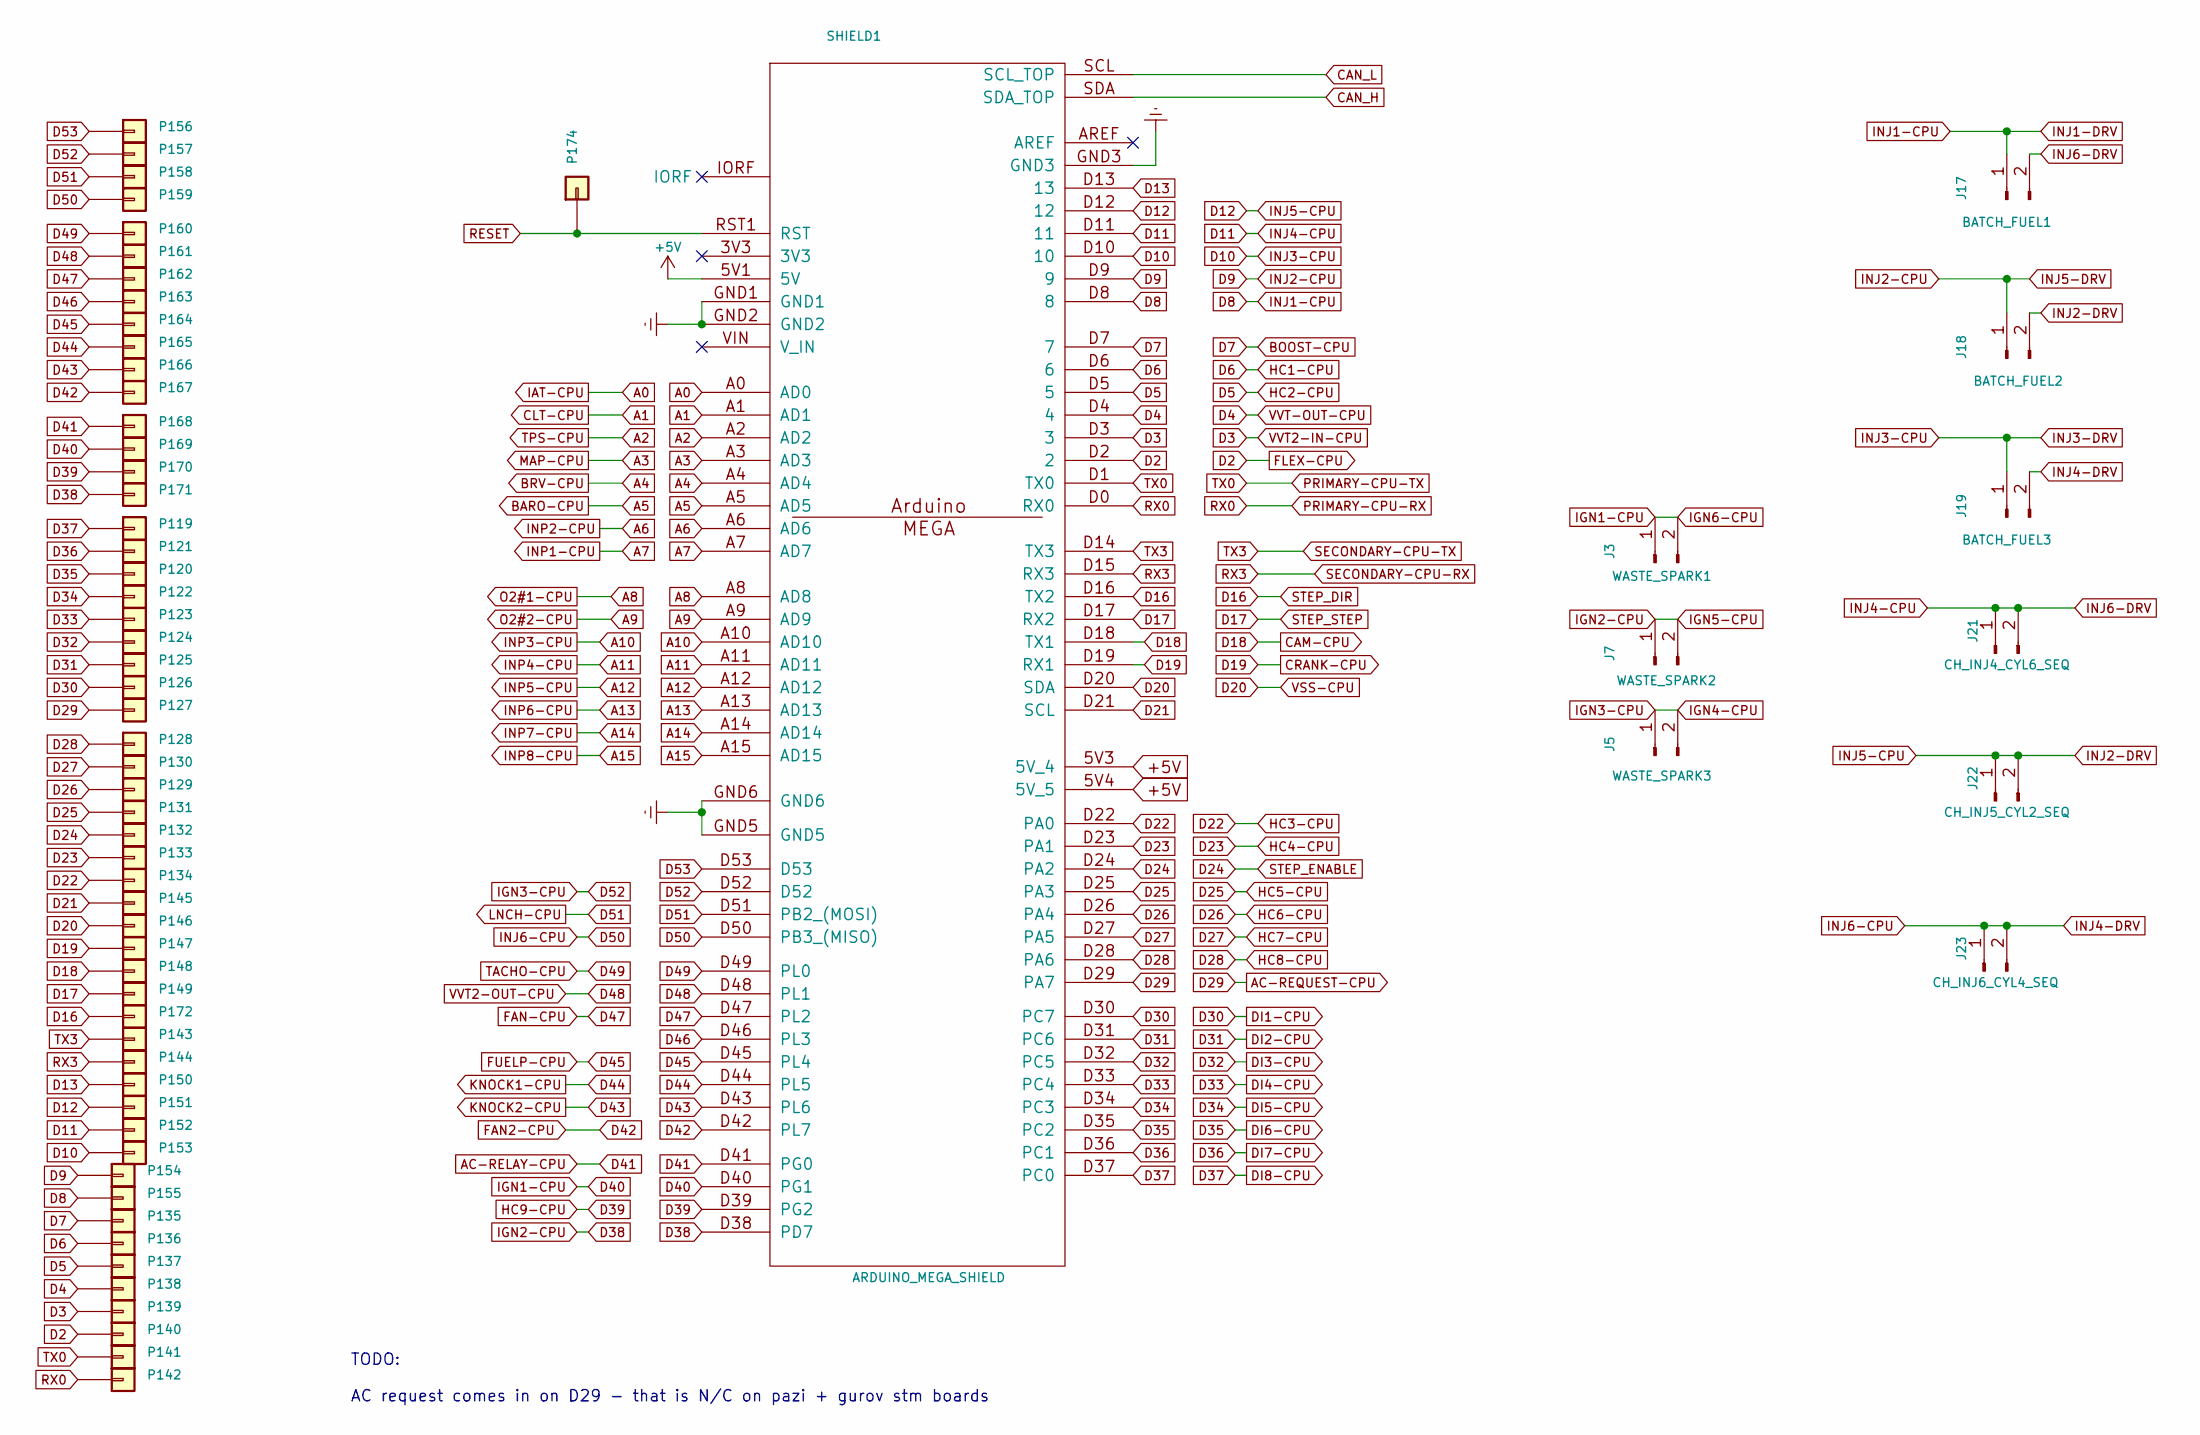
[picture p6: schematic MCU.kicad_sch]

Parts:
J3: WASTE_SPARK1; PinHeader_1x02_P2.54mm_Vertical
J5: WASTE_SPARK3; PinHeader_1x02_P2.54mm_Vertical
J7: WASTE_SPARK2; PinHeader_1x02_P2.54mm_Vertical
J17: BATCH_FUEL1; PinHeader_1x02_P2.54mm_Vertical
J18: BATCH_FUEL2; PinHeader_1x02_P2.54mm_Vertical
J19: BATCH_FUEL3; PinHeader_1x02_P2.54mm_Vertical
J21: CH_INJ4_CYL6_SEQ; PinHeader_1x02_P2.54mm_Vertical
J22: CH_INJ5_CYL2_SEQ; PinHeader_1x02_P2.54mm_Vertical
J23: CH_INJ6_CYL4_SEQ; PinHeader_1x02_P2.54mm_Vertical
P119, P123, P125, P127, P130, P131, P132, P133, P156, P164, P165, P169, P170: PRI TX; TestPoint_THTPad_1.5x1.5mm_Drill0.7mm
P120, P171: D38; TestPoint_THTPad_1.5x1.5mm_Drill0.7mm
P121: D36; TestPoint_THTPad_1.5x1.5mm_Drill0.7mm
P122: D34; TestPoint_THTPad_1.5x1.5mm_Drill0.7mm
P124: D32; TestPoint_THTPad_1.5x1.5mm_Drill0.7mm
P126: D30; TestPoint_THTPad_1.5x1.5mm_Drill0.7mm
P128: D28; TestPoint_THTPad_1.5x1.5mm_Drill0.7mm
P129: D26; TestPoint_THTPad_1.5x1.5mm_Drill0.7mm
P134: D22; TestPoint_THTPad_1.5x1.5mm_Drill0.7mm
P135: D7; TestPoint_THTPad_1.5x1.5mm_Drill0.7mm
P136: D6; TestPoint_THTPad_1.5x1.5mm_Drill0.7mm
P137: D5; TestPoint_THTPad_1.5x1.5mm_Drill0.7mm
P138: D4; TestPoint_THTPad_1.5x1.5mm_Drill0.7mm
P139: D3; TestPoint_THTPad_1.5x1.5mm_Drill0.7mm
P140: D2; TestPoint_THTPad_1.5x1.5mm_Drill0.7mm
P141: D1; TestPoint_THTPad_1.5x1.5mm_Drill0.7mm
P142: D0; TestPoint_THTPad_1.5x1.5mm_Drill0.7mm
P143: D14; TestPoint_THTPad_1.5x1.5mm_Drill0.7mm
P144: D15; TestPoint_THTPad_1.5x1.5mm_Drill0.7mm
P145: D21; TestPoint_THTPad_1.5x1.5mm_Drill0.7mm
P146: D20; TestPoint_THTPad_1.5x1.5mm_Drill0.7mm
P147: D19; TestPoint_THTPad_1.5x1.5mm_Drill0.7mm
P148: D18; TestPoint_THTPad_1.5x1.5mm_Drill0.7mm
P149: D17; TestPoint_THTPad_1.5x1.5mm_Drill0.7mm
P150: D13; TestPoint_THTPad_1.5x1.5mm_Drill0.7mm
P151: D12; TestPoint_THTPad_1.5x1.5mm_Drill0.7mm
P152: D11; TestPoint_THTPad_1.5x1.5mm_Drill0.7mm
P153: D10; TestPoint_THTPad_1.5x1.5mm_Drill0.7mm
P154: D9; TestPoint_THTPad_1.5x1.5mm_Drill0.7mm
P155: D8; TestPoint_THTPad_1.5x1.5mm_Drill0.7mm
P157: D52; TestPoint_THTPad_1.5x1.5mm_Drill0.7mm
P158: D51; TestPoint_THTPad_1.5x1.5mm_Drill0.7mm
P159: D50; TestPoint_THTPad_1.5x1.5mm_Drill0.7mm
P160: D49; TestPoint_THTPad_1.5x1.5mm_Drill0.7mm
P161: D48; TestPoint_THTPad_1.5x1.5mm_Drill0.7mm
P162: D47; TestPoint_THTPad_1.5x1.5mm_Drill0.7mm
P163: D46; TestPoint_THTPad_1.5x1.5mm_Drill0.7mm
P166: D43; TestPoint_THTPad_1.5x1.5mm_Drill0.7mm
P167: D42; TestPoint_THTPad_1.5x1.5mm_Drill0.7mm
P168: D41; TestPoint_THTPad_1.5x1.5mm_Drill0.7mm
P172: D16; TestPoint_THTPad_1.5x1.5mm_Drill0.7mm
P174: RST1; TestPoint_THTPad_1.5x1.5mm_Drill0.7mm
SHIELD1: ARDUINO_MEGA_SHIELD; Arduino_Mega2560_R3_Shield; MPN DNP

Connections:
+5V: SHIELD1.5V1 (5V), SHIELD1.5V3 (5V_4), SHIELD1.5V4 (5V_5)
A0: SHIELD1.A0 (AD0)
A1: SHIELD1.A1 (AD1)
A2: SHIELD1.A2 (AD2)
A3: SHIELD1.A3 (AD3)
A4: SHIELD1.A4 (AD4)
A5: SHIELD1.A5 (AD5)
A6: SHIELD1.A6 (AD6)
A7: SHIELD1.A7 (AD7)
A8: SHIELD1.A8 (AD8)
A9: SHIELD1.A9 (AD9)
A10: SHIELD1.A10 (AD10)
A11: SHIELD1.A11 (AD11)
A12: SHIELD1.A12 (AD12)
A13: SHIELD1.A13 (AD13)
A14: SHIELD1.A14 (AD14)
A15: SHIELD1.A15 (AD15)
AC-RELAY-CPU: P168.1, SHIELD1.D41 (PG0)
AC-REQUEST-CPU: P127.1, SHIELD1.D29 (PA7)
BOOST-CPU: P135.1, SHIELD1.D7 (7)
CAM-CPU: P148.1, SHIELD1.D18 (TX1)
CAN_H: SHIELD1.SDA (SDA_TOP)
CAN_L: SHIELD1.SCL (SCL_TOP)
CRANK-CPU: P147.1, SHIELD1.D19 (RX1)
D2: P140.1, SHIELD1.D2 (2)
D3: P139.1, SHIELD1.D3 (3)
D4: P138.1, SHIELD1.D4 (4)
D5: P137.1, SHIELD1.D5 (5)
D6: P136.1, SHIELD1.D6 (6)
D8: J17.1, P155.1, SHIELD1.D8 (8)
D9: J18.1, P154.1, SHIELD1.D9 (9)
D10: J19.1, P153.1, SHIELD1.D10 (10)
D11: J17.2, J21.1, J21.2, P152.1, SHIELD1.D11 (11)
D12: J18.2, J22.1, J22.2, P151.1, SHIELD1.D12 (12)
D13: P150.1, SHIELD1.D13 (13)
D16: P172.1, SHIELD1.D16 (TX2)
D17: P149.1, SHIELD1.D17 (RX2)
D20: P146.1, SHIELD1.D20 (SDA)
D21: P145.1, SHIELD1.D21 (SCL)
D22: P134.1, SHIELD1.D22 (PA0)
D23: P133.1, SHIELD1.D23 (PA1)
D24: P132.1, SHIELD1.D24 (PA2)
D25: P131.1, SHIELD1.D25 (PA3)
D26: P129.1, SHIELD1.D26 (PA4)
D27: P130.1, SHIELD1.D27 (PA5)
D28: P128.1, SHIELD1.D28 (PA6)
D30: P126.1, SHIELD1.D30 (PC7)
D31: P125.1, SHIELD1.D31 (PC6)
D32: P124.1, SHIELD1.D32 (PC5)
D33: P123.1, SHIELD1.D33 (PC4)
D34: P122.1, SHIELD1.D34 (PC3)
D35: P120.1, SHIELD1.D35 (PC2)
D36: P121.1, SHIELD1.D36 (PC1)
D37: P119.1, SHIELD1.D37 (PC0)
D38: J7.1, J7.2, P171.1, SHIELD1.D38 (PD7)
D39: P170.1, SHIELD1.D39 (PG2)
D40: J3.1, J3.2, P169.1, SHIELD1.D40 (PG1)
D42: P167.1, SHIELD1.D42 (PL7)
D43: P166.1, SHIELD1.D43 (PL6)
D44: P165.1, SHIELD1.D44 (PL5)
D45: P164.1, SHIELD1.D45 (PL4)
D46: P163.1, SHIELD1.D46 (PL3)
D47: P162.1, SHIELD1.D47 (PL2)
D48: P161.1, SHIELD1.D48 (PL1)
D49: P160.1, SHIELD1.D49 (PL0)
D50: J19.2, J23.1, J23.2, P159.1, SHIELD1.D50 (PB3_(MISO))
D51: P158.1, SHIELD1.D51 (PB2_(MOSI))
D52: J5.1, J5.2, P157.1, SHIELD1.D52
D53: P156.1, SHIELD1.D53
Earth: SHIELD1.GND1, SHIELD1.GND2, SHIELD1.GND3, SHIELD1.GND5, SHIELD1.GND6
PRIMARY-CPU-RX: P142.1, SHIELD1.D0 (RX0)
PRIMARY-CPU-TX: P141.1, SHIELD1.D1 (TX0)
RESET: P174.1, SHIELD1.RST1 (RST)
RX3: P144.1, SHIELD1.D15 (RX3)
SECONDARY-CPU-TX: P143.1, SHIELD1.D14 (TX3)

Notes on the sheet:
TODO: AC request comes in on D29 - that is N/C on pazi + gurov stm boards
