ElDominio/rusefi/firmware/config/boards/mega100/suprapnp/analog1.kicad_sch

## KiCad design firmware/config/boards/mega100/suprapnp/analog1.kicad_sch (2025-05-04, last stored version)

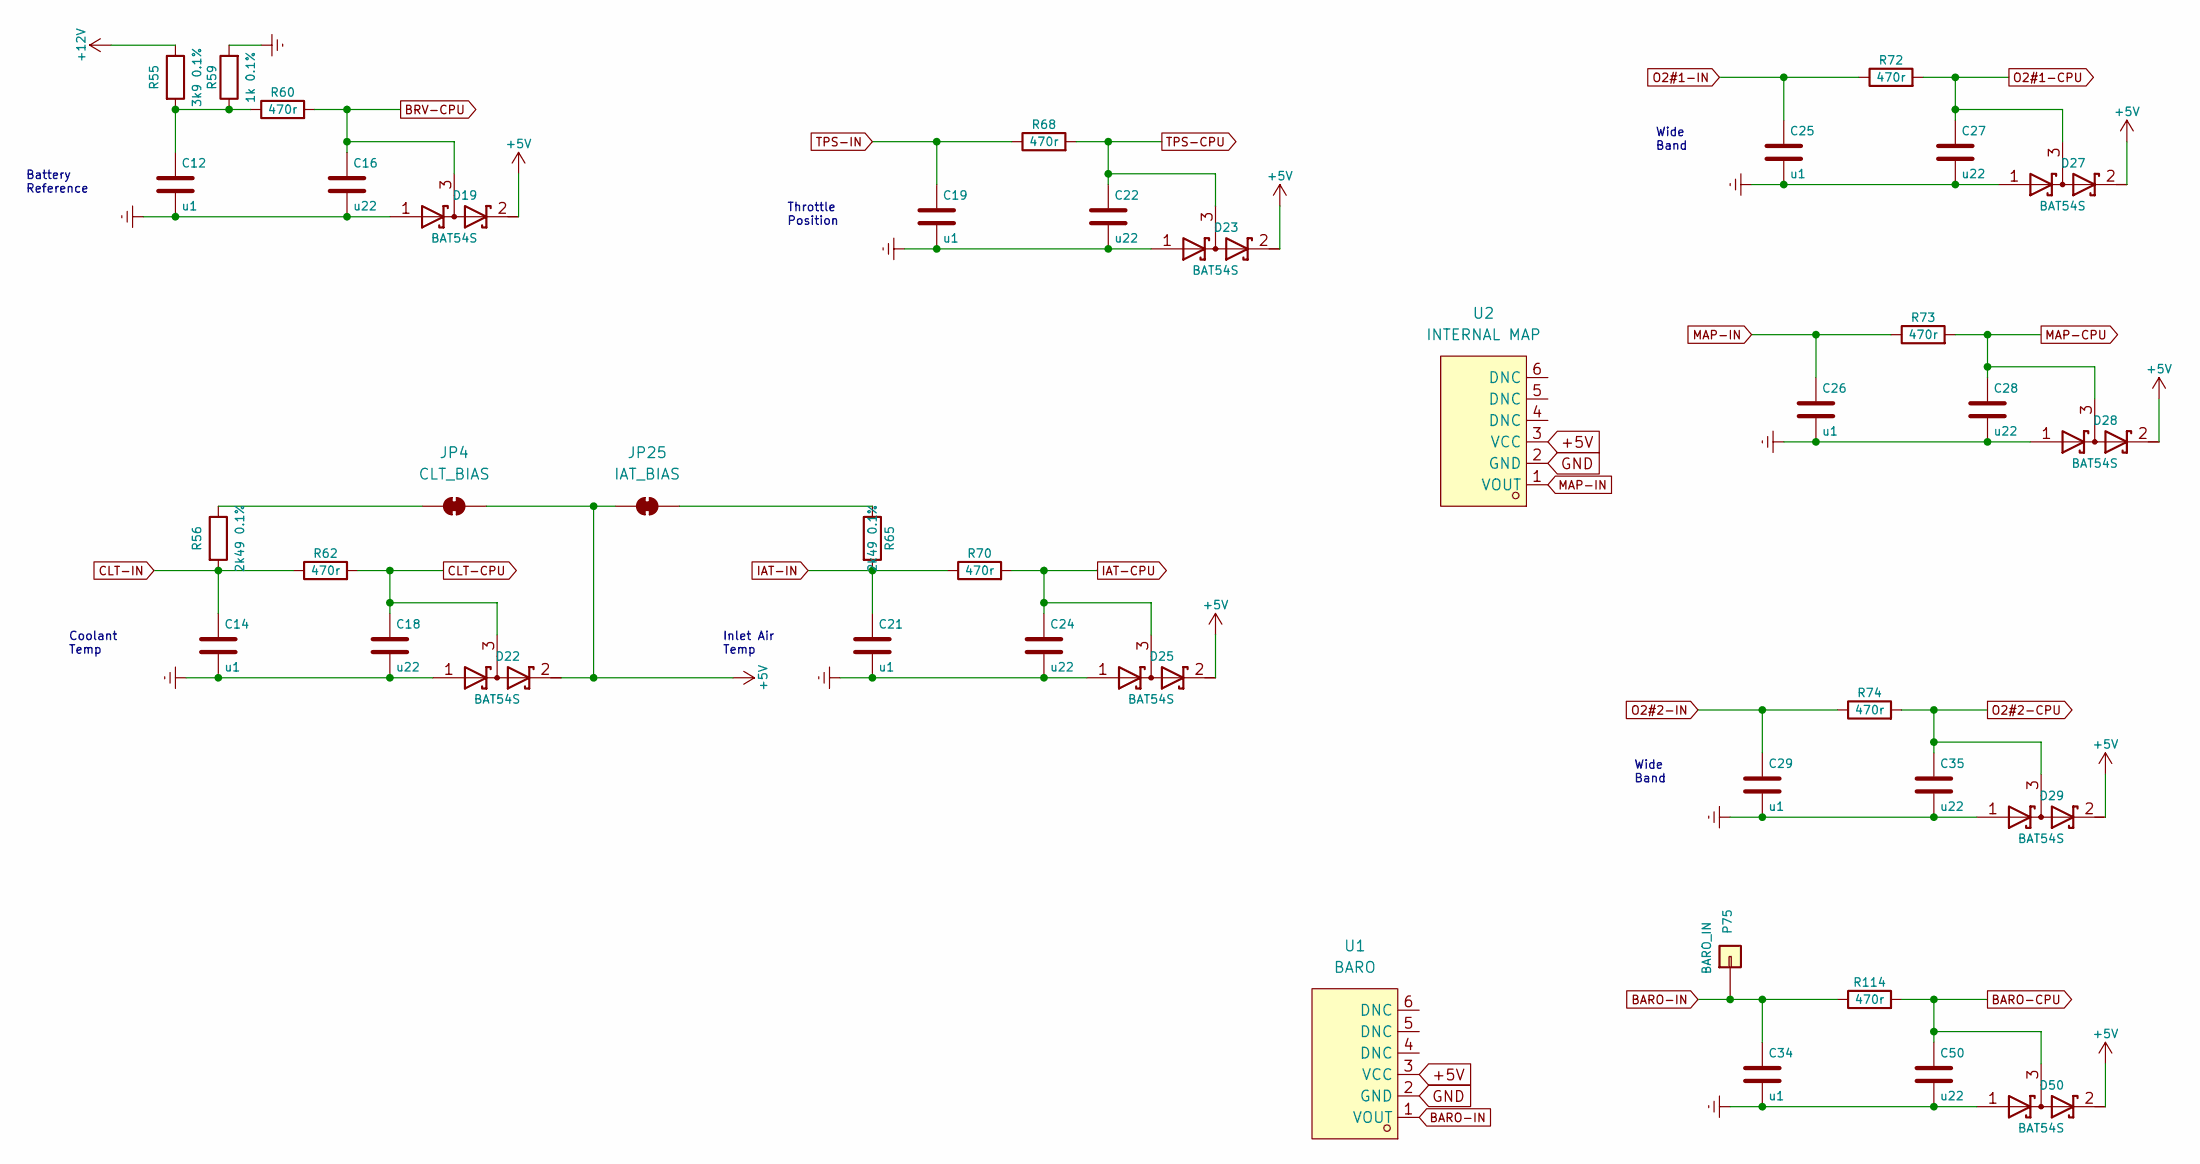
[picture p7: schematic analog1.kicad_sch]

Parts:
C12, C14, C19, C21, C25, C26, C29, C34: u1; C0805; MPN CL21B104KBFNNNE; LCSC C136621
C16, C18, C22, C24, C27, C28, C35, C50: u22; C0805; MPN CL21B224KBFNNNE; LCSC C5378
D19, D22, D23, D25, D27, D28, D29, D50: BAT54S; SOT-23-3_L3.0-W1.7-P0.95-LS2.9-BR; MPN BAT54S,215; LCSC C47546
JP4: CLT_BIAS; SolderJumper-2_P1.3mm_Bridged_Pad1.0x1.5mm
JP25: IAT_BIAS; SolderJumper-2_P1.3mm_Bridged_Pad1.0x1.5mm
P75: BARO_IN; TestPoint_THTPad_1.5x1.5mm_Drill0.7mm
R55: 3k9 0.1%; R0805; MPN ERA6AEB392V; LCSC C473293
R56, R65: 2k49 0.1%; R0805; MPN C515727; LCSC C515727
R59: 1k 0.1%; R0805; MPN C110774; LCSC C110774
R60, R62, R68, R70, R72, R73, R74, R114: 470r; R0805; MPN C17710; LCSC C17710
U1: BARO; SENSOR-TH_MPX4250AP; LCSC Part C2802676
U2: INTERNAL MAP; SENSOR-TH_MPX4250AP; LCSC Part C2802676

Connections:
+5V: D19.2 (K), D22.2 (K), D23.2 (K), D25.2 (K), D27.2 (K), D28.2 (K), D29.2 (K), D50.2 (K), JP4.2 (B), JP25.1 (A), U1.3 (VCC), U2.3 (VCC)
+12V: R55.1
BARO-CPU: C50.1, D50.3 (common), R114.2
BARO-IN: C34.1, P75.1, R114.1, U1.1 (VOUT)
BRV-CPU: C16.1, D19.3 (common), R60.2
CLT-CPU: C18.1, D22.3 (common), R62.2
CLT-IN: C14.1, R56.2, R62.1
Earth: C12.2, C14.2, C16.2, C18.2, C19.2, C21.2, C22.2, C24.2, C25.2, C26.2, C27.2, C28.2, C29.2, C34.2, C35.2, C50.2, D19.1 (A), D22.1 (A), D23.1 (A), D25.1 (A), D27.1 (A), D28.1 (A), D29.1 (A), D50.1 (A), R59.2
GND: U1.2 (GND), U2.2 (GND)
IAT-CPU: C24.1, D25.3 (common), R70.2
IAT-IN: C21.1, R65.2, R70.1
MAP-CPU: C28.1, D28.3 (common), R73.2
MAP-IN: C26.1, R73.1, U2.1 (VOUT)
unnamed: C12.1, R55.2, R59.1, R60.1
unnamed: JP4.1 (A), R56.1
unnamed: JP25.2 (B), R65.1
O2#1-CPU: C27.1, D27.3 (common), R72.2
O2#1-IN: C25.1, R72.1
O2#2-CPU: C35.1, D29.3 (common), R74.2
O2#2-IN: C29.1, R74.1
TPS-CPU: C22.1, D23.3 (common), R68.2
TPS-IN: C19.1, R68.1

Notes on the sheet:
Wide Band
Coolant Temp
Throttle Position
Inlet Air Temp
Battery Reference
