ElDominio/rusefi/firmware/config/boards/mega100/suprapnp/analog_aux.kicad_sch

## KiCad design firmware/config/boards/mega100/suprapnp/analog_aux.kicad_sch (2025-05-04, last stored version)

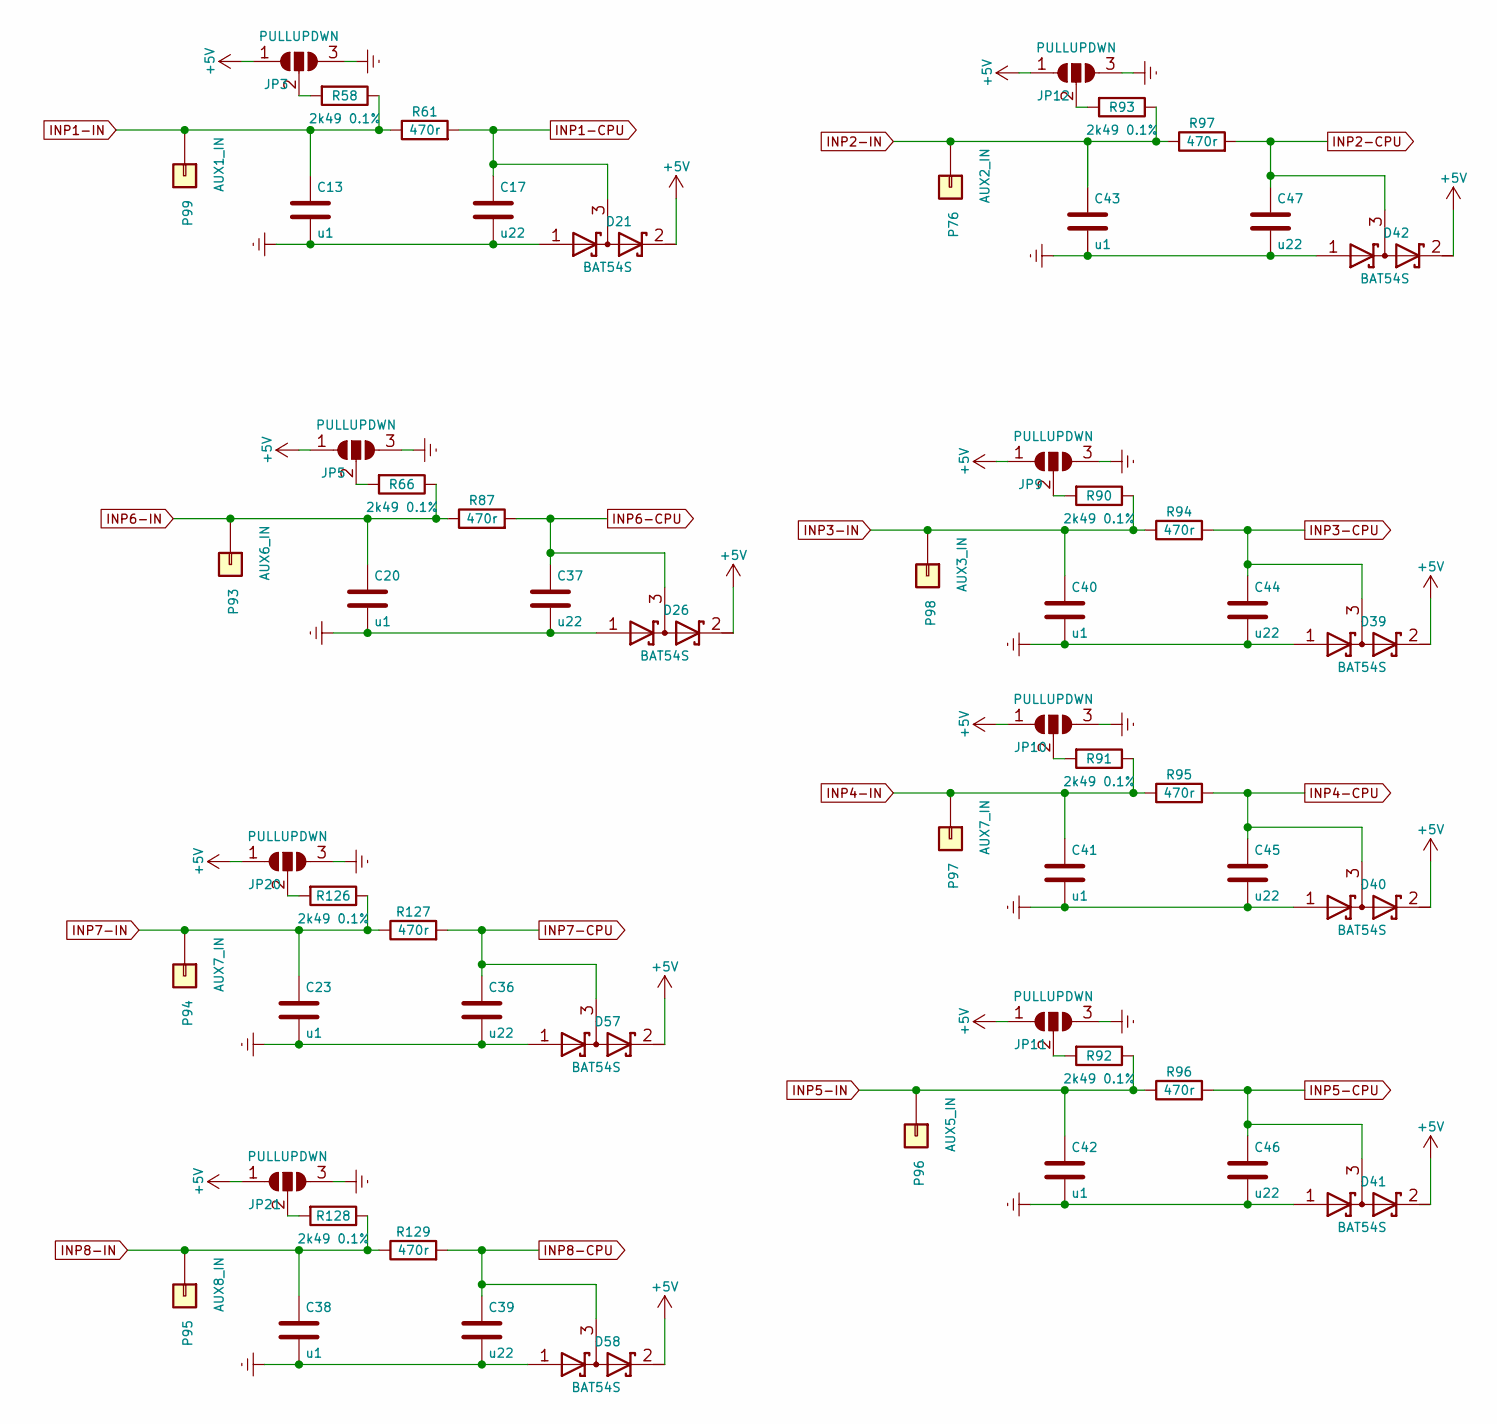
[picture p8: schematic analog_aux.kicad_sch]

Parts:
C13, C20, C23, C38, C40, C41, C42, C43: u1; C0805; MPN CL21B104KBFNNNE; LCSC C136621
C17, C36, C37, C39, C44, C45, C46, C47: u22; C0805; MPN CL21B224KBFNNNE; LCSC C5378
D21, D26, D39, D40, D41, D42, D57, D58: BAT54S; SOT-23-3_L3.0-W1.7-P0.95-LS2.9-BR; MPN BAT54S,215; LCSC C47546
JP3, JP5, JP9, JP10, JP11, JP12, JP20, JP21: PULLUPDWN; SolderJumper-3_P1.3mm_Open_Pad1.0x1.5mm_NumberLabels; MPN DNP
P76: AUX2_IN; TestPoint_THTPad_1.5x1.5mm_Drill0.7mm
P93: AUX6_IN; TestPoint_THTPad_1.5x1.5mm_Drill0.7mm
P94, P97: AUX7_IN; TestPoint_THTPad_1.5x1.5mm_Drill0.7mm
P95: AUX8_IN; TestPoint_THTPad_1.5x1.5mm_Drill0.7mm
P96: AUX5_IN; TestPoint_THTPad_1.5x1.5mm_Drill0.7mm
P98: AUX3_IN; TestPoint_THTPad_1.5x1.5mm_Drill0.7mm
P99: AUX1_IN; TestPoint_THTPad_1.5x1.5mm_Drill0.7mm
R58, R66, R90, R91, R92, R93, R126, R128: 2k49 0.1%; R0805; MPN C515727; LCSC C515727
R61, R87, R94, R95, R96, R97, R127, R129: 470r; R0805; MPN C17710; LCSC C17710

Connections:
+5V: D21.2 (K), D26.2 (K), D39.2 (K), D40.2 (K), D41.2 (K), D42.2 (K), D57.2 (K), D58.2 (K), JP3.1 (A), JP5.1 (A), JP9.1 (A), JP10.1 (A), JP11.1 (A), JP12.1 (A), JP20.1 (A), JP21.1 (A)
Earth: C13.2, C17.2, C20.2, C23.2, C36.2, C37.2, C38.2, C39.2, C40.2, C41.2, C42.2, C43.2, C44.2, C45.2, C46.2, C47.2, D21.1 (A), D26.1 (A), D39.1 (A), D40.1 (A), D41.1 (A), D42.1 (A), D57.1 (A), D58.1 (A), JP3.3 (B), JP5.3 (B), JP9.3 (B), JP10.3 (B), JP11.3 (B), JP12.3 (B), JP20.3 (B), JP21.3 (B)
INP1-CPU: C17.1, D21.3 (common), R61.2
INP1-IN: C13.1, P99.1, R58.1, R61.1
INP2-CPU: C47.1, D42.3 (common), R97.2
INP2-IN: C43.1, P76.1, R93.1, R97.1
INP3-CPU: C44.1, D39.3 (common), R94.2
INP3-IN: C40.1, P98.1, R90.1, R94.1
INP4-CPU: C45.1, D40.3 (common), R95.2
INP4-IN: C41.1, P97.1, R91.1, R95.1
INP5-CPU: C46.1, D41.3 (common), R96.2
INP5-IN: C42.1, P96.1, R92.1, R96.1
INP6-CPU: C37.1, D26.3 (common), R87.2
INP6-IN: C20.1, P93.1, R66.1, R87.1
INP7-CPU: C36.1, D57.3 (common), R127.2
INP7-IN: C23.1, P94.1, R126.1, R127.1
INP8-CPU: C39.1, D58.3 (common), R129.2
INP8-IN: C38.1, P95.1, R128.1, R129.1
unnamed: JP3.2 (C), R58.2
unnamed: JP5.2 (C), R66.2
unnamed: JP9.2 (C), R90.2
unnamed: JP10.2 (C), R91.2
unnamed: JP11.2 (C), R92.2
unnamed: JP12.2 (C), R93.2
unnamed: JP20.2 (C), R126.2
unnamed: JP21.2 (C), R128.2
