ElDominio/rusefi/firmware/config/boards/mega100/suprapnp/digital_inputs.kicad_sch

## KiCad design firmware/config/boards/mega100/suprapnp/digital_inputs.kicad_sch (2025-05-04, last stored version)

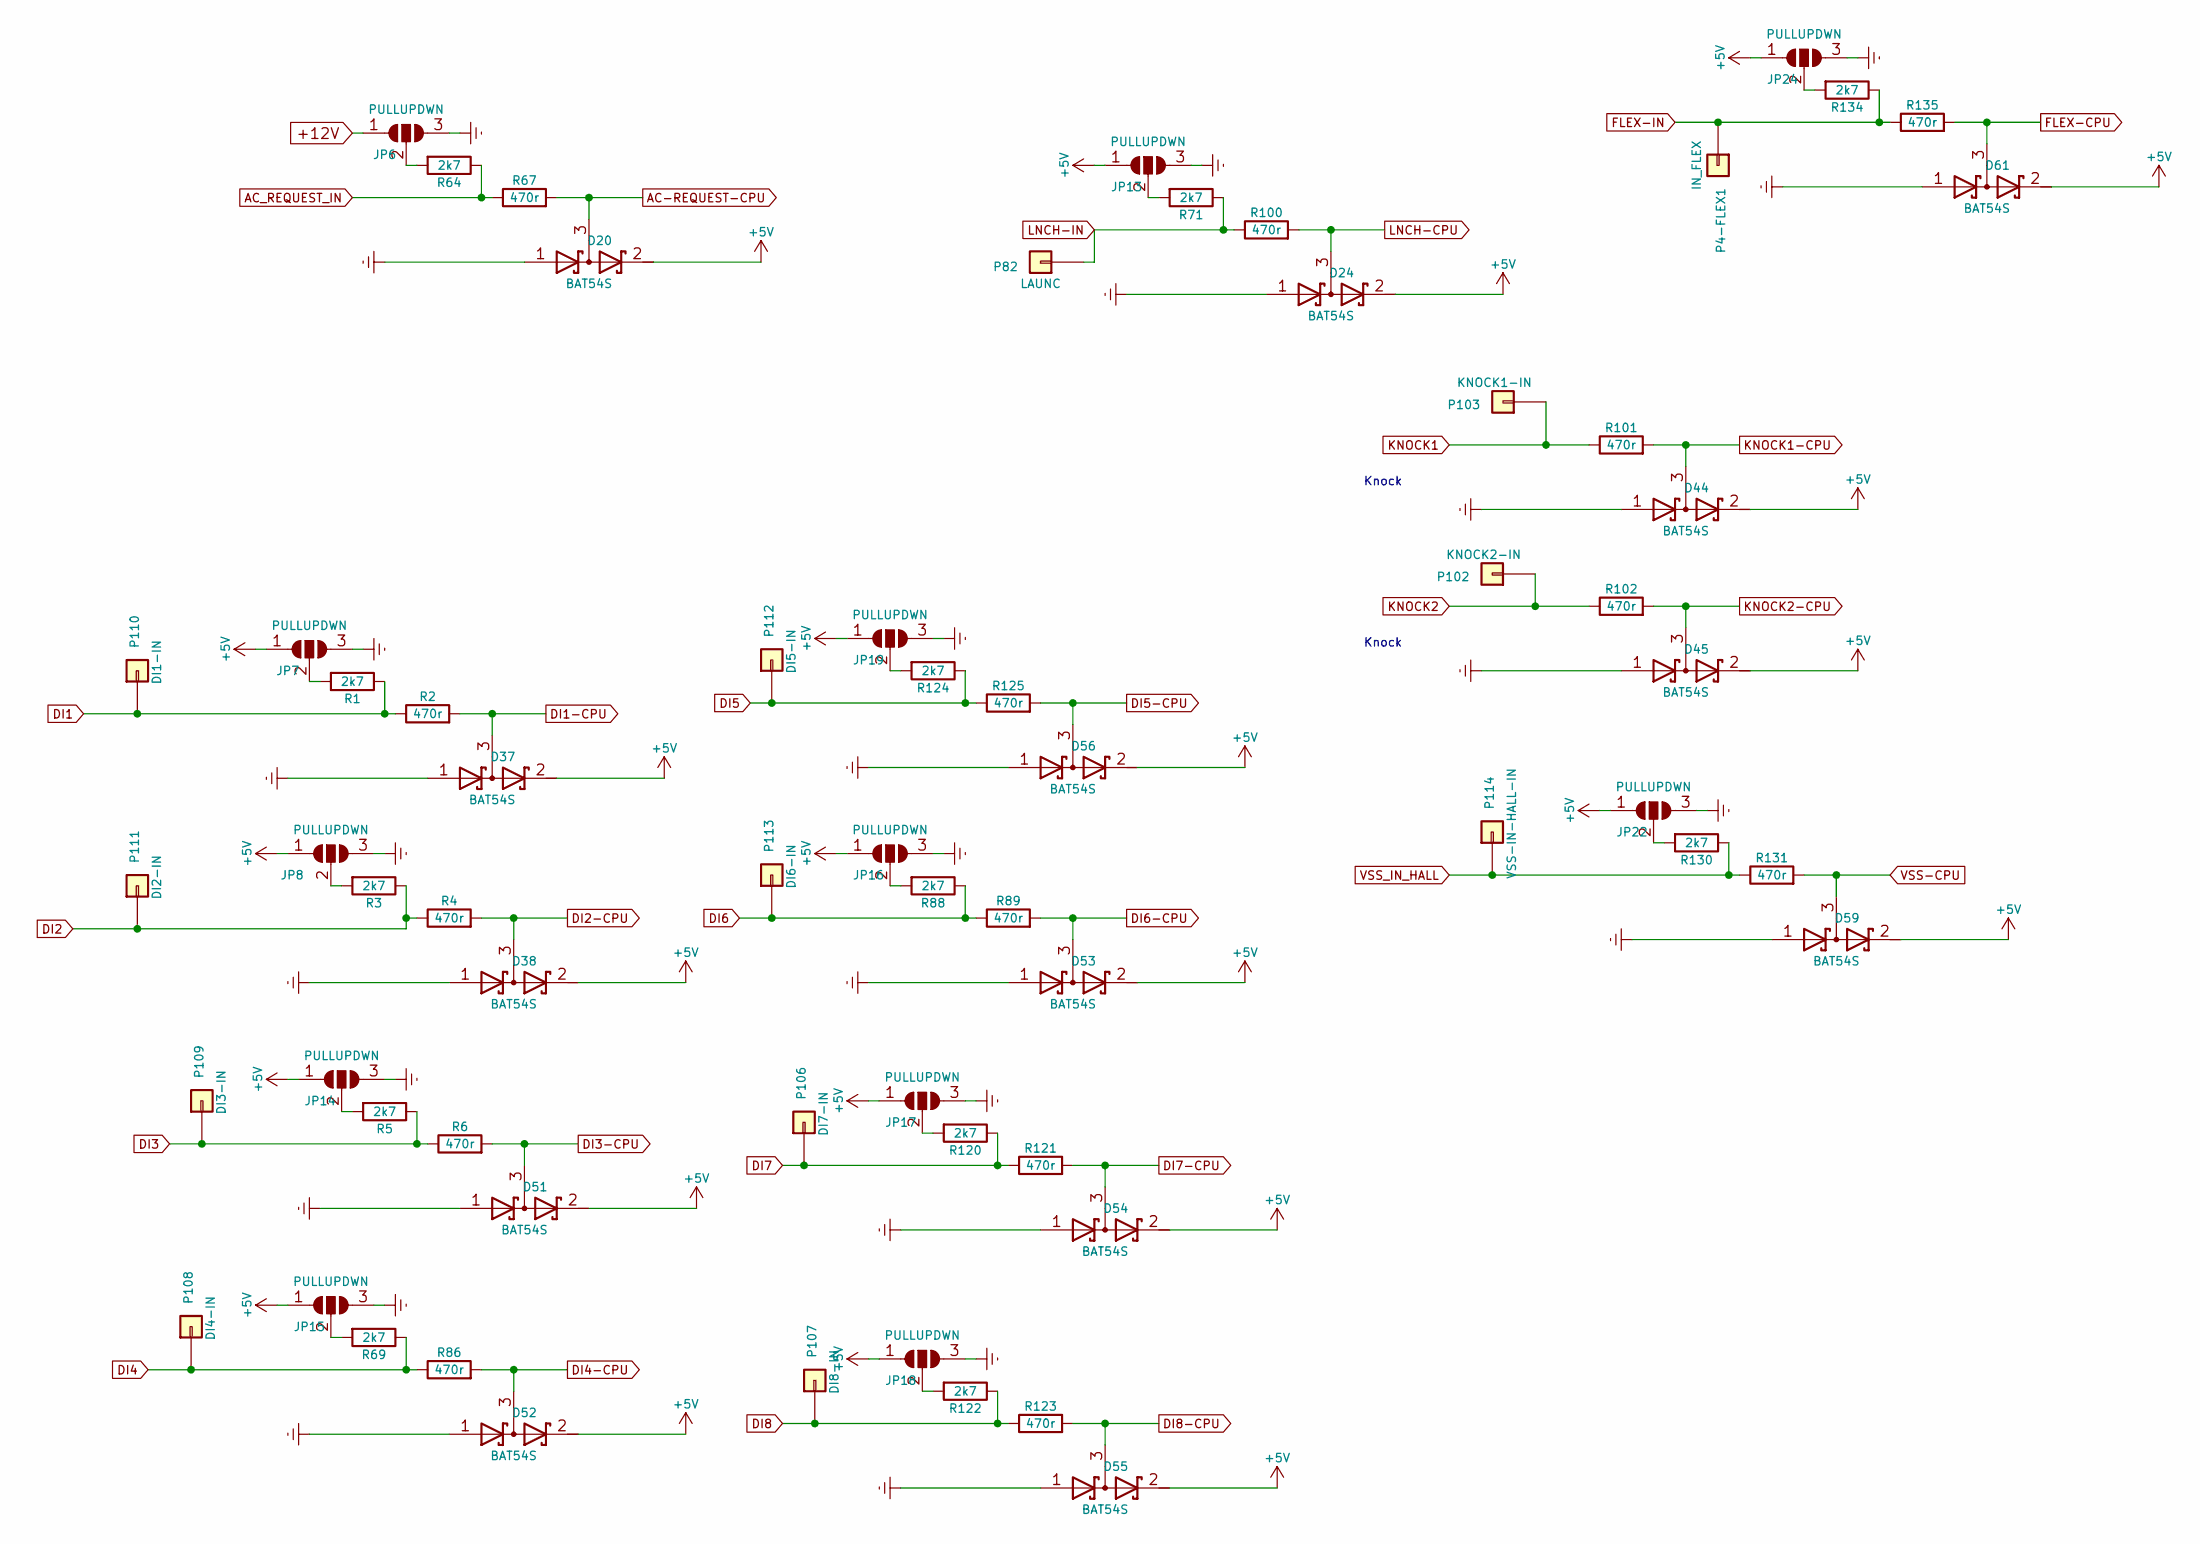
[picture p9: schematic digital_inputs.kicad_sch]

Parts:
D20, D24, D37, D38, D44, D45, D51, D52, D53, D54, D55, D56, D59, D61: BAT54S; SOT-23-3_L3.0-W1.7-P0.95-LS2.9-BR; MPN BAT54S,215; LCSC C47546
JP6, JP7, JP8, JP13, JP14, JP15, JP16, JP17, JP18, JP19, JP22, JP24: PULLUPDWN; SolderJumper-3_P1.3mm_Open_Pad1.0x1.5mm_NumberLabels; MPN DNP
P4-FLEX1: IN_FLEX; TestPoint_THTPad_1.5x1.5mm_Drill0.7mm
P82: LAUNC; TestPoint_THTPad_1.5x1.5mm_Drill0.7mm
P102: KNOCK2-IN; TestPoint_THTPad_1.5x1.5mm_Drill0.7mm
P103: KNOCK1-IN; TestPoint_THTPad_1.5x1.5mm_Drill0.7mm
P106: DI7-IN; TestPoint_THTPad_1.5x1.5mm_Drill0.7mm
P107: DI8-IN; TestPoint_THTPad_1.5x1.5mm_Drill0.7mm
P108: DI4-IN; TestPoint_THTPad_1.5x1.5mm_Drill0.7mm
P109: DI3-IN; TestPoint_THTPad_1.5x1.5mm_Drill0.7mm
P110: DI1-IN; TestPoint_THTPad_1.5x1.5mm_Drill0.7mm
P111: DI2-IN; TestPoint_THTPad_1.5x1.5mm_Drill0.7mm
P112: DI5-IN; TestPoint_THTPad_1.5x1.5mm_Drill0.7mm
P113: DI6-IN; TestPoint_THTPad_1.5x1.5mm_Drill0.7mm
P114: VSS-IN-HALL-IN; TestPoint_THTPad_1.5x1.5mm_Drill0.7mm
R1, R3, R5, R64, R69, R71, R88, R120, R122, R124, R130, R134: 2k7; R0603; MPN C13167; LCSC C13167
R2, R4, R6, R67, R86, R89, R100, R101, R102, R121, R123, R125, R131, R135: 470r; R0805; MPN C17710; LCSC C17710

Connections:
+5V: D20.2 (K), D24.2 (K), D37.2 (K), D38.2 (K), D44.2 (K), D45.2 (K), D51.2 (K), D52.2 (K), D53.2 (K), D54.2 (K), D55.2 (K), D56.2 (K), D59.2 (K), D61.2 (K), JP7.1 (A), JP8.1 (A), JP13.1 (A), JP14.1 (A), JP15.1 (A), JP16.1 (A), JP17.1 (A), JP18.1 (A), JP19.1 (A), JP22.1 (A), JP24.1 (A)
+12V: JP6.1 (A)
AC-REQUEST-CPU: D20.3 (common), R67.2
AC_REQUEST_IN: R64.1, R67.1
DI1: P110.1, R1.1, R2.1
DI1-CPU: D37.3 (common), R2.2
DI2: P111.1, R3.1, R4.1
DI2-CPU: D38.3 (common), R4.2
DI3: P109.1, R5.1, R6.1
DI3-CPU: D51.3 (common), R6.2
DI4: P108.1, R69.1, R86.1
DI4-CPU: D52.3 (common), R86.2
DI5: P112.1, R124.1, R125.1
DI5-CPU: D56.3 (common), R125.2
DI6: P113.1, R88.1, R89.1
DI6-CPU: D53.3 (common), R89.2
DI7: P106.1, R120.1, R121.1
DI7-CPU: D54.3 (common), R121.2
DI8: P107.1, R122.1, R123.1
DI8-CPU: D55.3 (common), R123.2
Earth: D20.1 (A), D24.1 (A), D37.1 (A), D38.1 (A), D44.1 (A), D45.1 (A), D51.1 (A), D52.1 (A), D53.1 (A), D54.1 (A), D55.1 (A), D56.1 (A), D59.1 (A), D61.1 (A), JP6.3 (B), JP7.3 (B), JP8.3 (B), JP13.3 (B), JP14.3 (B), JP15.3 (B), JP16.3 (B), JP17.3 (B), JP18.3 (B), JP19.3 (B), JP22.3 (B), JP24.3 (B)
FLEX-CPU: D61.3 (common), R135.2
FLEX-IN: P4-FLEX1.1, R134.1, R135.1
KNOCK1: P103.1, R101.1
KNOCK1-CPU: D44.3 (common), R101.2
KNOCK2: P102.1, R102.1
KNOCK2-CPU: D45.3 (common), R102.2
LNCH-CPU: D24.3 (common), R100.2
LNCH-IN: P82.1, R71.1, R100.1
unnamed: JP6.2 (C), R64.2
unnamed: JP7.2 (C), R1.2
unnamed: JP8.2 (C), R3.2
unnamed: JP13.2 (C), R71.2
unnamed: JP14.2 (C), R5.2
unnamed: JP15.2 (C), R69.2
unnamed: JP16.2 (C), R88.2
unnamed: JP17.2 (C), R120.2
unnamed: JP18.2 (C), R122.2
unnamed: JP19.2 (C), R124.2
unnamed: JP22.2 (C), R130.2
unnamed: JP24.2 (C), R134.2
VSS-CPU: D59.3 (common), R131.2
VSS_IN_HALL: P114.1, R130.1, R131.1

Notes on the sheet:
Knock
