ElDominio/rusefi/firmware/config/boards/mega100/suprapnp/extra-pins.kicad_sch

## KiCad design firmware/config/boards/mega100/suprapnp/extra-pins.kicad_sch (2025-05-04, last stored version)

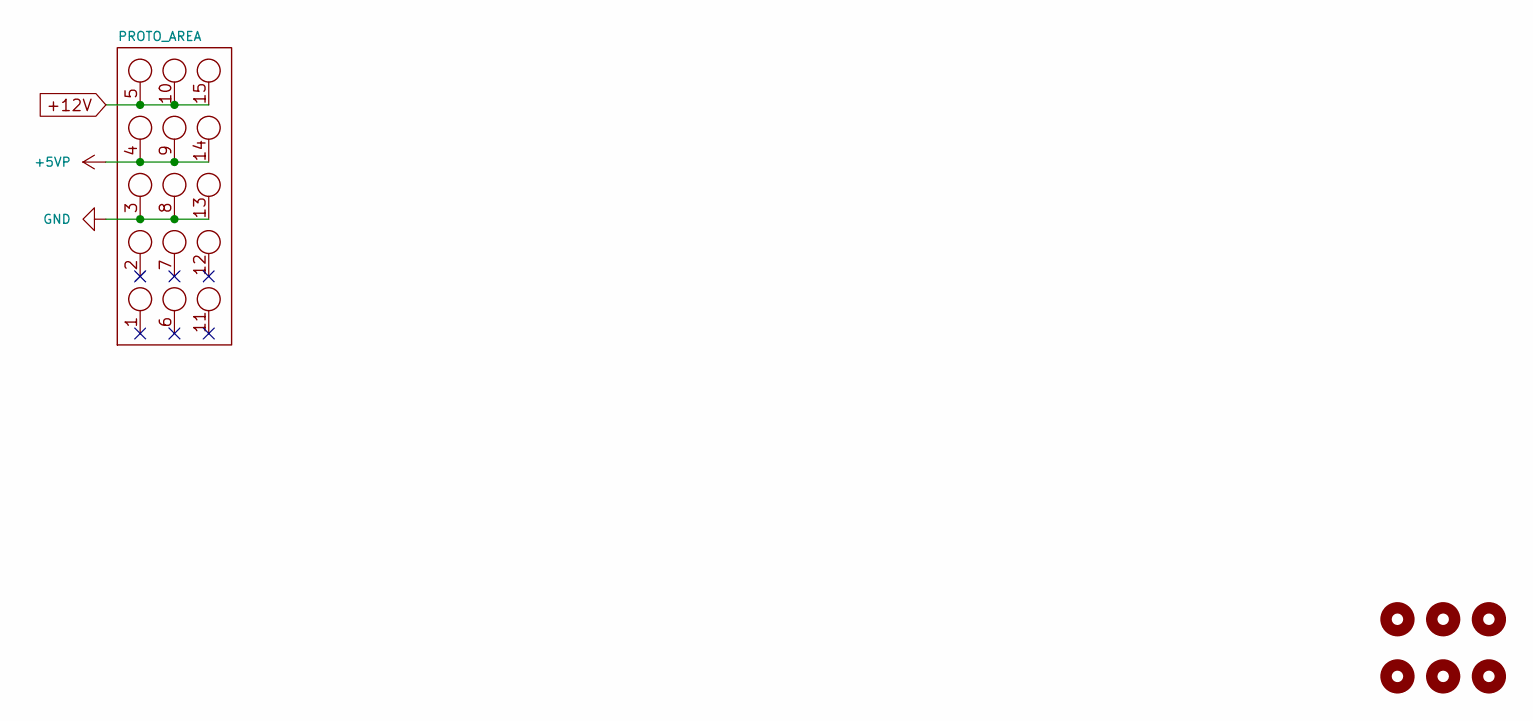
[picture p10: schematic extra-pins.kicad_sch]

Parts:
G1: PROTO_AREA
H1, H2, H3, H4, H5, H6: MountingHole; MountingHole_4.5mm

Connections:
+5VP: G1.4, G1.9, G1.14
+12V: G1.5, G1.10, G1.15
GND: G1.3, G1.8, G1.13
