ElDominio/rusefi/firmware/config/boards/mega100/suprapnp/igniton.kicad_sch

## KiCad design firmware/config/boards/mega100/suprapnp/igniton.kicad_sch (2025-05-04, last stored version)

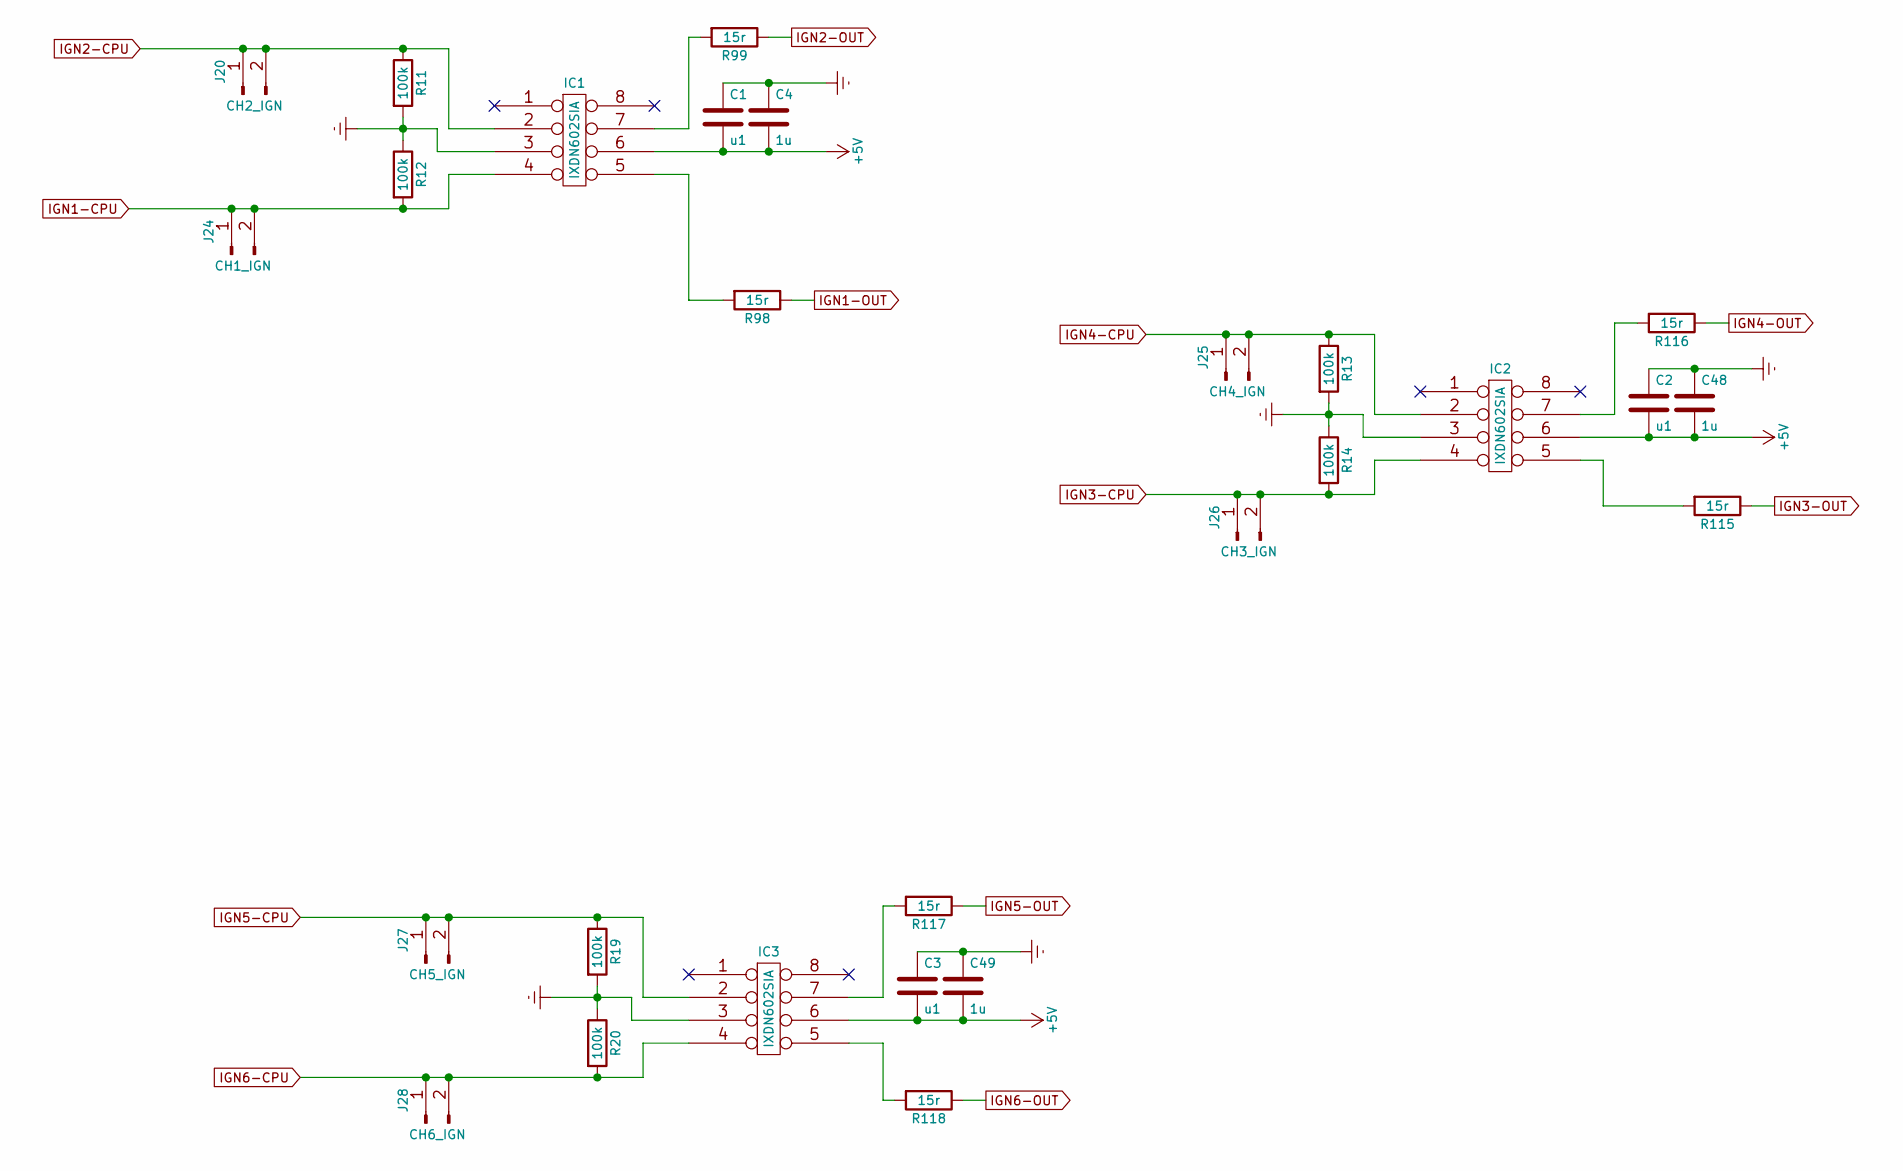
[picture p11: schematic igniton.kicad_sch]

Parts:
C1, C2, C3: u1; C0805; MPN CL21B104KBFNNNE; LCSC C136621
C4, C48, C49: 1u; C0805; MPN CL21B105KBFNNNE; LCSC C28323
IC1, IC2, IC3: IXDN602SIA; SOIC-8_L4.9-W3.9-P1.27-LS6.0-BL; MPN IXDN602SIA; LCSC C431679
J20: CH2_IGN; PinHeader_1x02_P2.54mm_Vertical
J24: CH1_IGN; PinHeader_1x02_P2.54mm_Vertical
J25: CH4_IGN; PinHeader_1x02_P2.54mm_Vertical
J26: CH3_IGN; PinHeader_1x02_P2.54mm_Vertical
J27: CH5_IGN; PinHeader_1x02_P2.54mm_Vertical
J28: CH6_IGN; PinHeader_1x02_P2.54mm_Vertical
R11, R12, R13, R14, R19, R20: 100k; R0603; MPN C25803; LCSC C25803
R98, R99, R115, R116, R117, R118: 15r; R2512; MPN C5713426; LCSC C5713426

Connections:
+5V: C1.2, C2.2, C3.2, C4.2, C48.2, C49.2, IC1.6, IC2.6, IC3.6
Earth: C1.1, C2.1, C3.1, C4.1, C48.1, C49.1, IC1.3, IC2.3, IC3.3, R11.2, R12.1, R13.2, R14.1, R19.2, R20.1
IGN1-CPU: IC1.4, J24.1, J24.2, R12.2
IGN1-OUT: R98.1
IGN2-CPU: IC1.2, J20.1, J20.2, R11.1
IGN2-OUT: R99.1
IGN3-CPU: IC2.4, J26.1, J26.2, R14.2
IGN3-OUT: R115.1
IGN4-CPU: IC2.2, J25.1, J25.2, R13.1
IGN4-OUT: R116.1
IGN5-CPU: IC3.2, J27.1, J27.2, R19.1
IGN5-OUT: R117.1
IGN6-CPU: IC3.4, J28.1, J28.2, R20.2
IGN6-OUT: R118.1
unnamed: IC1.5, R98.2
unnamed: IC1.7, R99.2
unnamed: IC2.5, R115.2
unnamed: IC2.7, R116.2
unnamed: IC3.5, R118.2
unnamed: IC3.7, R117.2
