ElDominio/rusefi/firmware/config/boards/mega100/suprapnp/injectors.kicad_sch

## KiCad design firmware/config/boards/mega100/suprapnp/injectors.kicad_sch (2025-05-04, last stored version)

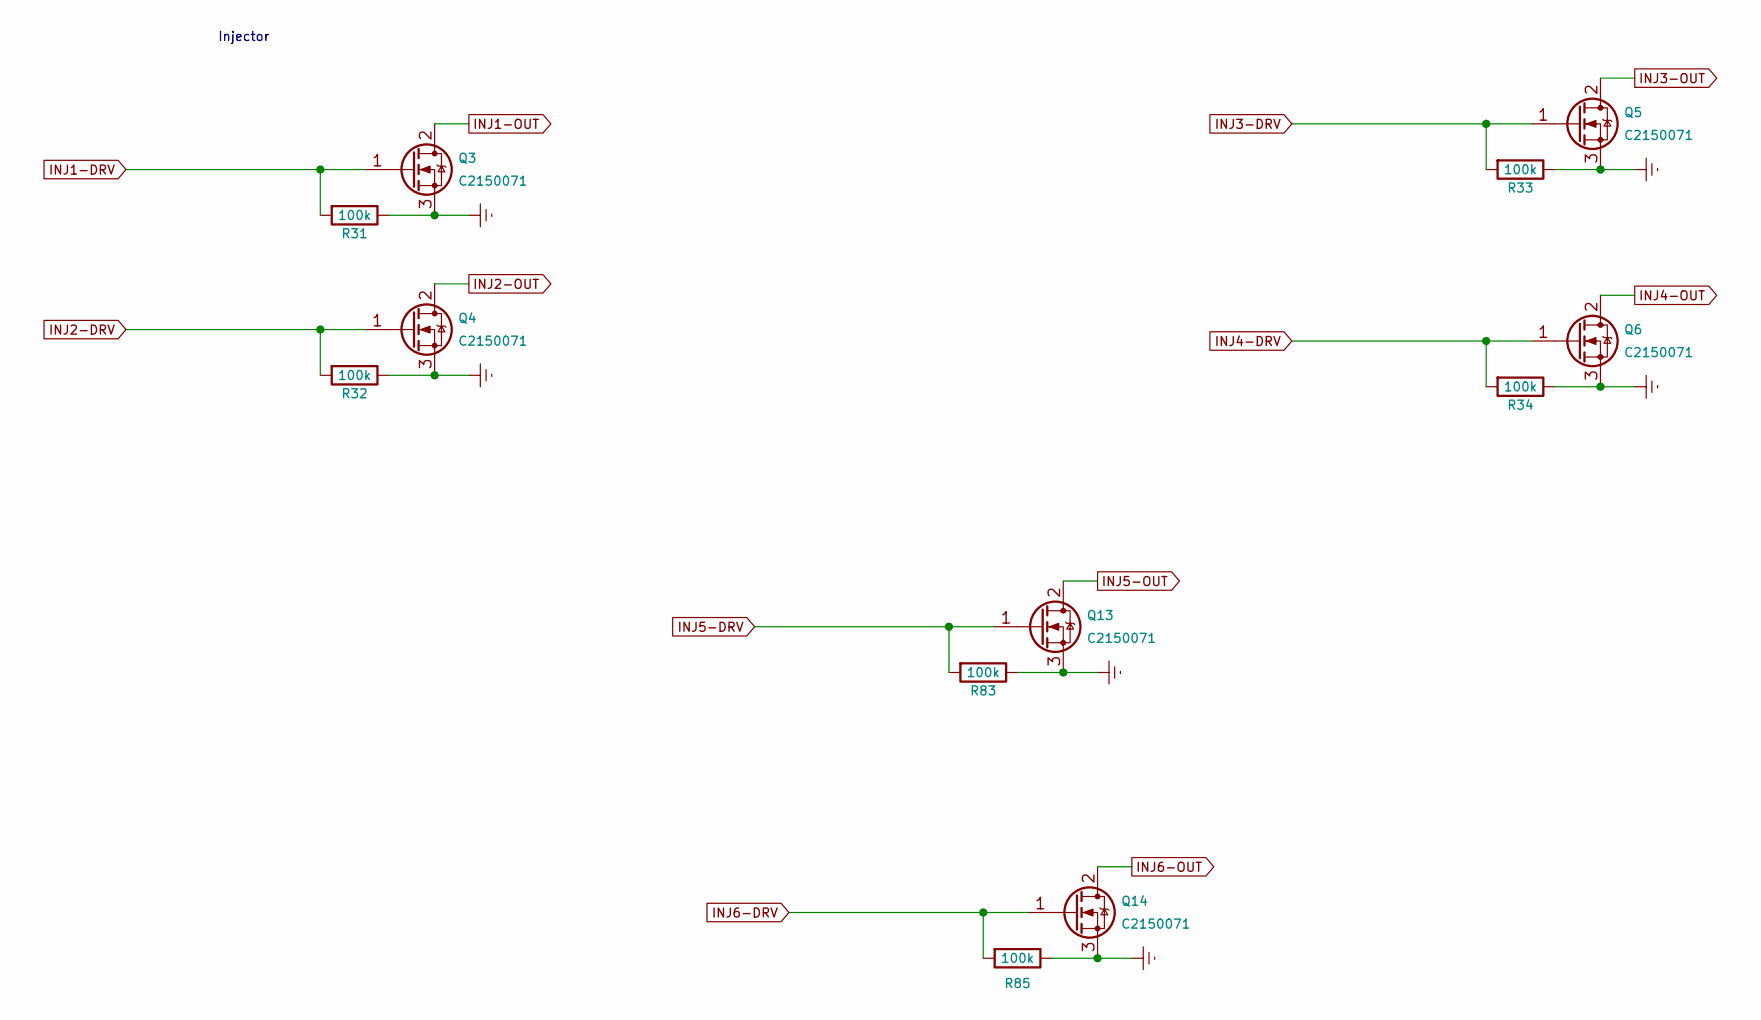
[picture p12: schematic injectors.kicad_sch]

Parts:
Q3, Q4, Q5, Q6, Q13, Q14: C2150071; TO-252-2_L6.5-W6.2-P4.57-LS10.0-BR-CW; MPN C2150071; LCSC C2150071
R31, R32, R33, R34, R83, R85: 100k; R0603; MPN C25803; LCSC C25803

Connections:
Earth: Q3.3 (S), Q4.3 (S), Q5.3 (S), Q6.3 (S), Q13.3 (S), Q14.3 (S), R31.1, R32.1, R33.1, R34.1, R83.1, R85.1
INJ1-DRV: Q3.1 (G), R31.2
INJ1-OUT: Q3.2 (D)
INJ2-DRV: Q4.1 (G), R32.2
INJ2-OUT: Q4.2 (D)
INJ3-DRV: Q5.1 (G), R33.2
INJ3-OUT: Q5.2 (D)
INJ4-DRV: Q6.1 (G), R34.2
INJ4-OUT: Q6.2 (D)
INJ5-DRV: Q13.1 (G), R83.2
INJ5-OUT: Q13.2 (D)
INJ6-DRV: Q14.1 (G), R85.2
INJ6-OUT: Q14.2 (D)

Notes on the sheet:
Injector
