ElDominio/rusefi/firmware/config/boards/mega100/suprapnp/main-connector.kicad_sch

## KiCad design firmware/config/boards/mega100/suprapnp/main-connector.kicad_sch (2025-05-04, last stored version)

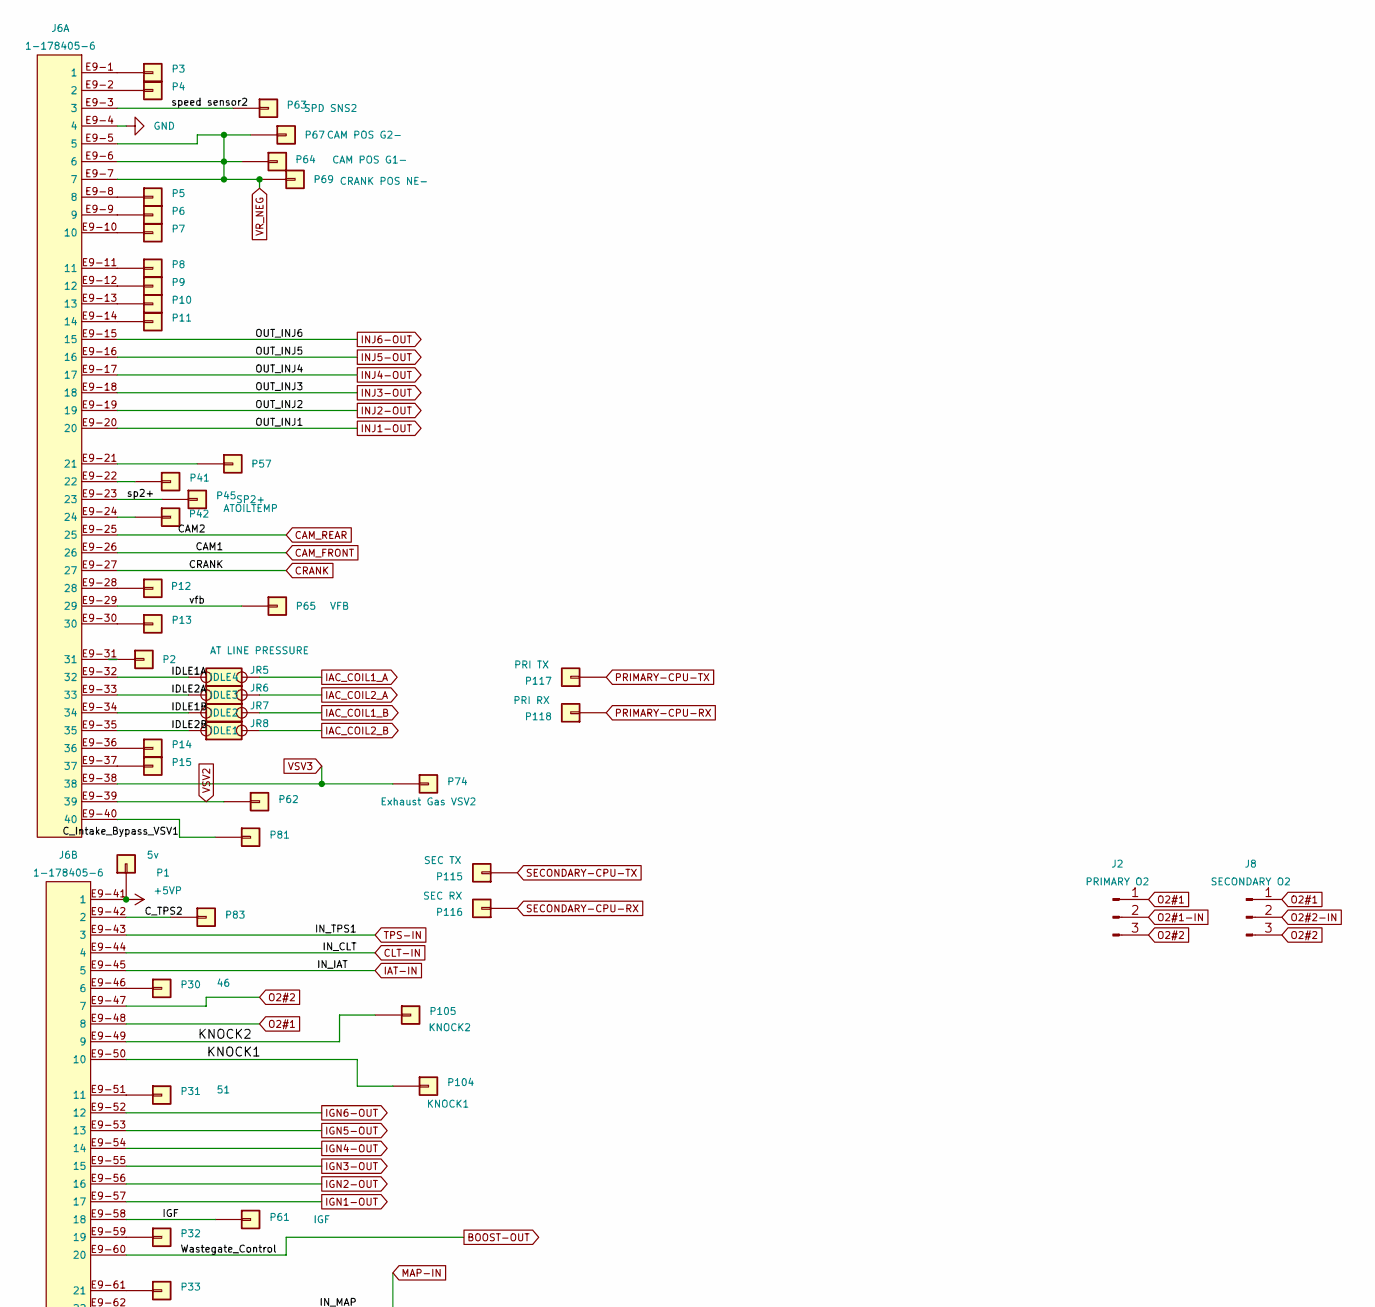
[picture p13: schematic main-connector.kicad_sch, part in row 1, column 1]

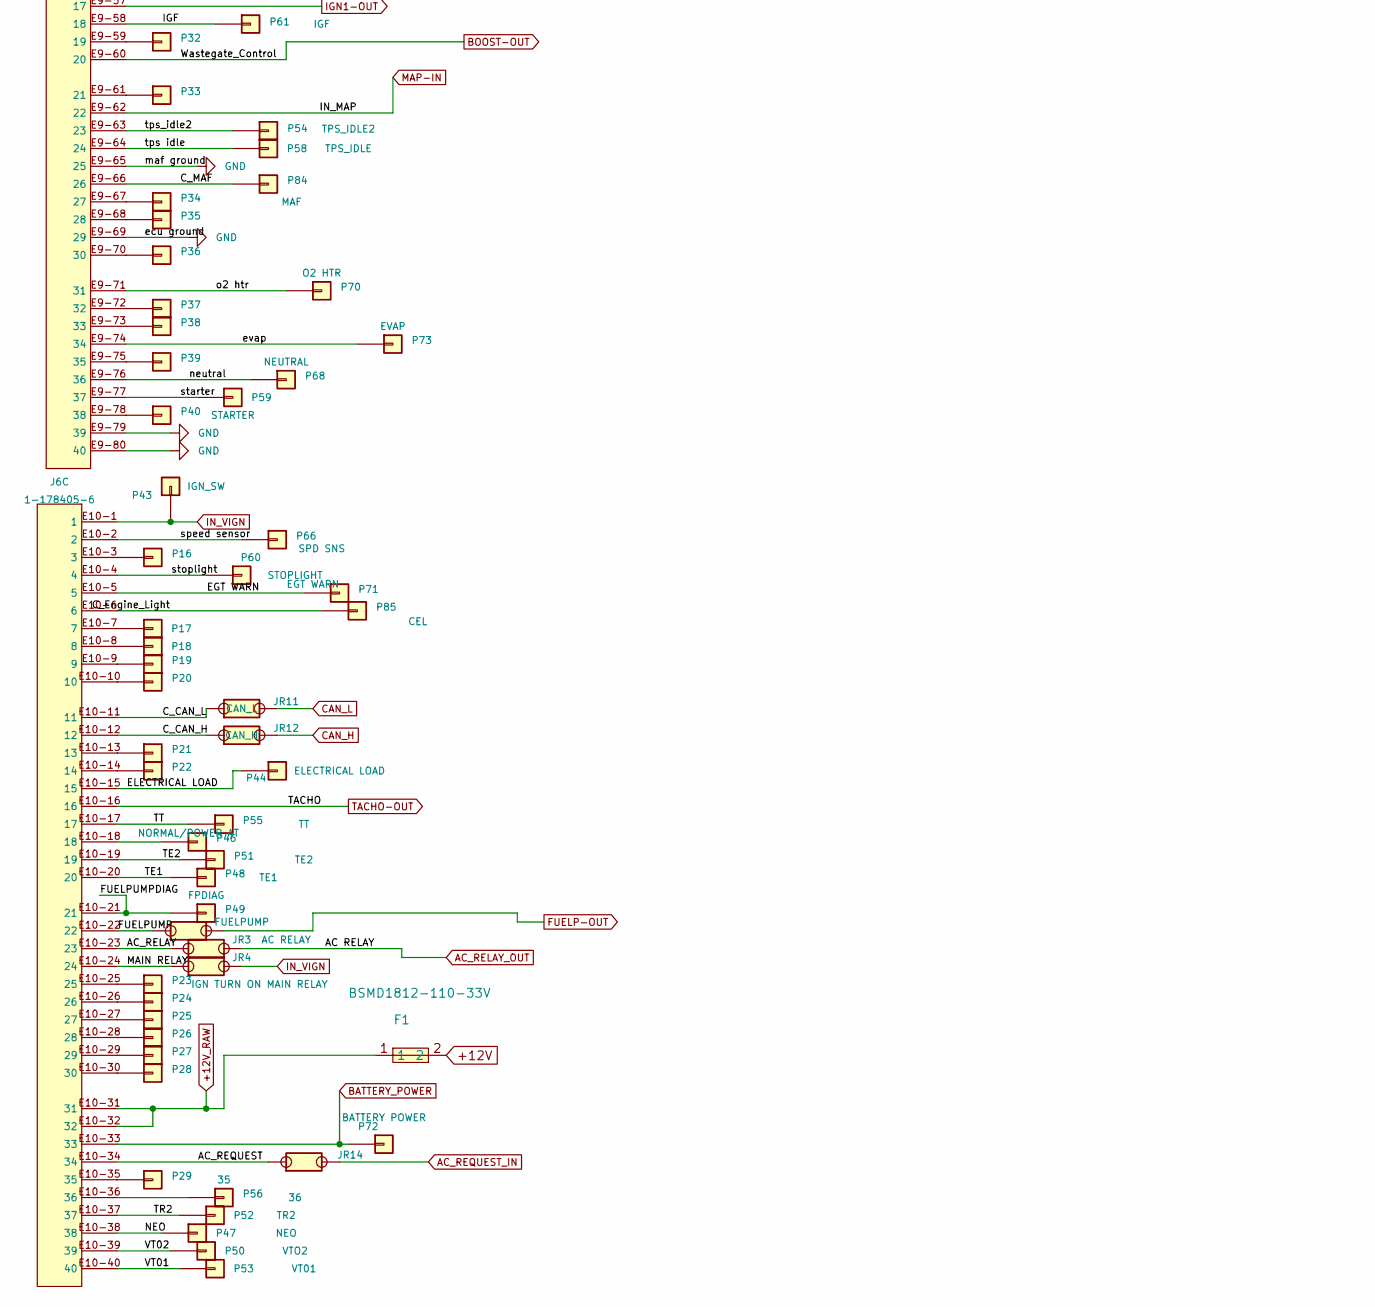
[picture p14: schematic main-connector.kicad_sch, part in row 2, column 1]

Parts:
F1: BSMD1812-110-33V; F1812; LCSC Part C883150
J2: PRIMARY O2; PinHeader_1x03_P2.54mm_Vertical
J6: 1-178405-6; TE-1-178405-6
J8: SECONDARY O2; PinHeader_1x03_P2.54mm_Vertical
JR1: FUELPUMP; PAD-0805-PAD; LCSC C17477
JR3: AC RELAY; PAD-0805-PAD; LCSC C17477
JR4: IGN TURN ON MAIN RELAY; PAD-0805-PAD; LCSC C17477
JR5: IDLE4; PAD-0805-PAD; LCSC C17477
JR6: IDLE3; PAD-0805-PAD; LCSC C17477
JR7: IDLE2; PAD-0805-PAD; LCSC C17477
JR8: IDLE1; PAD-0805-PAD; LCSC C17477
JR11: CAN_L; PAD-0805-PAD; LCSC C17477
JR12: CAN_H; PAD-0805-PAD; LCSC C17477
JR14: AC_REQUEST; PAD-0805-PAD; LCSC C17477
P1: 5v; TestPoint_THTPad_1.5x1.5mm_Drill0.7mm
P2: AT LINE PRESSURE; TestPoint_THTPad_1.5x1.5mm_Drill0.7mm
P3, P4, P5, P6, P7, P8, P9, P10, P11, P12, P13, P14, P15, P16, P17, P18, P19, P20, P21, P22, P23, P24, P25, P26, P27, P28, P32, P33, P34, P35, P36, P37, P38, P39, P40, P41, P57: Pad; TestPoint_THTPad_1.5x1.5mm_Drill0.7mm
P29: 35; TestPoint_THTPad_1.5x1.5mm_Drill0.7mm
P30: 46; PAD-TH
P31: 51; TestPoint_THTPad_1.5x1.5mm_Drill0.7mm
P42: ATOILTEMP; TestPoint_THTPad_1.5x1.5mm_Drill0.7mm
P43: IGN_SW; TestPoint_THTPad_1.5x1.5mm_Drill0.7mm
P44: ELECTRICAL LOAD; TestPoint_THTPad_1.5x1.5mm_Drill0.7mm
P45: SP2+; TestPoint_THTPad_1.5x1.5mm_Drill0.7mm
P46: NORMAL/POWER AT; TestPoint_THTPad_1.5x1.5mm_Drill0.7mm
P47: NEO; TestPoint_THTPad_1.5x1.5mm_Drill0.7mm
P48: TE1; TestPoint_THTPad_1.5x1.5mm_Drill0.7mm
P49: FPDIAG; TestPoint_THTPad_1.5x1.5mm_Drill0.7mm
P50: VTO2; TestPoint_THTPad_1.5x1.5mm_Drill0.7mm
P51: TE2; TestPoint_THTPad_1.5x1.5mm_Drill0.7mm
P52: TR2; TestPoint_THTPad_1.5x1.5mm_Drill0.7mm
P53: VT01; TestPoint_THTPad_1.5x1.5mm_Drill0.7mm
P54: TPS_IDLE2; TestPoint_THTPad_1.5x1.5mm_Drill0.7mm
P55: TT; TestPoint_THTPad_1.5x1.5mm_Drill0.7mm
P56: 36; TestPoint_THTPad_1.5x1.5mm_Drill0.7mm
P58: TPS_IDLE; TestPoint_THTPad_1.5x1.5mm_Drill0.7mm
P59: STARTER; TestPoint_THTPad_1.5x1.5mm_Drill0.7mm
P60: STOPLIGHT; TestPoint_THTPad_1.5x1.5mm_Drill0.7mm
P61: IGF; TestPoint_THTPad_1.5x1.5mm_Drill0.7mm
P62: Exhaust Gas VSV2; TestPoint_THTPad_1.5x1.5mm_Drill0.7mm
P63: SPD SNS2; TestPoint_THTPad_1.5x1.5mm_Drill0.7mm
P64: CAM POS G1-; TestPoint_THTPad_1.5x1.5mm_Drill0.7mm
P65: VFB; TestPoint_THTPad_1.5x1.5mm_Drill0.7mm
P66: SPD SNS; TestPoint_THTPad_1.5x1.5mm_Drill0.7mm
P67: CAM POS G2-; TestPoint_THTPad_1.5x1.5mm_Drill0.7mm
P68: NEUTRAL; TestPoint_THTPad_1.5x1.5mm_Drill0.7mm
P69: CRANK POS NE-; TestPoint_THTPad_1.5x1.5mm_Drill0.7mm
P70: O2 HTR; TestPoint_THTPad_1.5x1.5mm_Drill0.7mm
P71: EGT WARN; TestPoint_THTPad_1.5x1.5mm_Drill0.7mm
P72: BATTERY POWER; TestPoint_THTPad_1.5x1.5mm_Drill0.7mm
P73: EVAP; TestPoint_THTPad_1.5x1.5mm_Drill0.7mm
P74: Exhaust Bypass VSV3; TestPoint_THTPad_1.5x1.5mm_Drill0.7mm
P81: Intake Bypass VSV1; TestPoint_THTPad_1.5x1.5mm_Drill0.7mm
P83: TPS2; TestPoint_THTPad_1.5x1.5mm_Drill0.7mm
P84: MAF; TestPoint_THTPad_1.5x1.5mm_Drill0.7mm
P85: CEL; TestPoint_THTPad_1.5x1.5mm_Drill0.7mm
P104: KNOCK1; TestPoint_THTPad_1.5x1.5mm_Drill0.7mm
P105: KNOCK2; TestPoint_THTPad_1.5x1.5mm_Drill0.7mm
P115: SEC TX; TestPoint_THTPad_1.5x1.5mm_Drill0.7mm
P116: SEC RX; TestPoint_THTPad_1.5x1.5mm_Drill0.7mm
P117: PRI TX; TestPoint_THTPad_1.5x1.5mm_Drill0.7mm
P118: PRI RX; TestPoint_THTPad_1.5x1.5mm_Drill0.7mm

Connections:
+5VP: J6.E9-41 (1), P1.1
+12V: F1.2
+12V_RAW: F1.1, J6.E10-31 (31), J6.E10-32 (32)
AC_RELAY: J6.E10-23 (23), JR3.1
AC_RELAY_OUT: JR3.2
AC_REQUEST: J6.E10-34 (34), JR14.1
AC_REQUEST_IN: JR14.2
BATTERY_POWER: J6.E10-33 (33), P72.1
BOOST-OUT: J6.E9-60 (20)
CAM_FRONT: J6.E9-26 (26)
CAM_REAR: J6.E9-25 (25)
CAN_H: JR12.2
CAN_L: JR11.2
CLT-IN: J6.E9-44 (4)
CRANK: J6.E9-27 (27)
C_CAN_H: J6.E10-12 (12), JR12.1
C_CAN_L: J6.E10-11 (11), JR11.1
C_Engine_Light: J6.E10-6 (6), P85.1
C_Intake_Bypass_VSV1: J6.E9-40 (40), P81.1
C_MAF: J6.E9-66 (26), P84.1
C_TPS2: J6.E9-42 (2), P83.1
EGT WARN: J6.E10-5 (5), P71.1
ELECTRICAL LOAD: J6.E10-15 (15), P44.1
FUELP-OUT: JR1.2
FUELPUMP: J6.E10-22 (22), JR1.1
FUELPUMPDIAG: J6.E10-21 (21), P49.1
GND: J6.E9-4 (4), J6.E9-65 (25), J6.E9-69 (29), J6.E9-79 (39), J6.E9-80 (40)
IAC_COIL1_A: JR5.2
IAC_COIL1_B: JR7.2
IAC_COIL2_A: JR6.2
IAC_COIL2_B: JR8.2
IAT-IN: J6.E9-45 (5)
IDLE1A: J6.E9-32 (32), JR5.1
IDLE1B: J6.E9-34 (34), JR7.1
IDLE2A: J6.E9-33 (33), JR6.1
IDLE2B: J6.E9-35 (35), JR8.1
IGF: J6.E9-58 (18), P61.1
IGN1-OUT: J6.E9-57 (17)
IGN2-OUT: J6.E9-56 (16)
IGN3-OUT: J6.E9-55 (15)
IGN4-OUT: J6.E9-54 (14)
IGN5-OUT: J6.E9-53 (13)
IGN6-OUT: J6.E9-52 (12)
INJ1-OUT: J6.E9-20 (20)
INJ2-OUT: J6.E9-19 (19)
INJ3-OUT: J6.E9-18 (18)
INJ4-OUT: J6.E9-17 (17)
INJ5-OUT: J6.E9-16 (16)
INJ6-OUT: J6.E9-15 (15)
IN_VIGN: J6.E10-1 (1), JR4.2, P43.1
KNOCK1: J6.E9-50 (10), P104.1
KNOCK2: J6.E9-49 (9), P105.1
MAIN RELAY: J6.E10-24 (24), JR4.1
MAP-IN: J6.E9-62 (22)
NEO: J6.E10-38 (38), P47.1
unnamed: J6.E9-1 (1), P3.1
unnamed: J6.E9-2 (2), P4.1
unnamed: J6.E9-8 (8), P5.1
unnamed: J6.E9-9 (9), P6.1
unnamed: J6.E9-10 (10), P7.1
unnamed: J6.E9-11 (11), P8.1
unnamed: J6.E9-12 (12), P9.1
unnamed: J6.E9-13 (13), P10.1
unnamed: J6.E9-14 (14), P11.1
unnamed: J6.E9-21 (21), P57.1
unnamed: J6.E9-22 (22), P41.1
unnamed: J6.E9-24 (24), P42.1
unnamed: J6.E9-28 (28), P12.1
unnamed: J6.E9-30 (30), P13.1
unnamed: J6.E9-31 (31), P2.1
unnamed: J6.E9-36 (36), P14.1
unnamed: J6.E9-37 (37), P15.1
unnamed: J6.E9-46 (6), P30.1
unnamed: J6.E9-51 (11), P31.1
unnamed: J6.E9-59 (19), P32.1
unnamed: J6.E9-61 (21), P33.1
unnamed: J6.E9-67 (27), P34.1
unnamed: J6.E9-68 (28), P35.1
unnamed: J6.E9-70 (30), P36.1
unnamed: J6.E9-72 (32), P37.1
unnamed: J6.E9-73 (33), P38.1
unnamed: J6.E9-75 (35), P39.1
unnamed: J6.E9-78 (38), P40.1
unnamed: J6.E10-3 (3), P16.1
unnamed: J6.E10-7 (7), P17.1
unnamed: J6.E10-8 (8), P18.1
unnamed: J6.E10-9 (9), P19.1
unnamed: J6.E10-10 (10), P20.1
unnamed: J6.E10-13 (13), P21.1
unnamed: J6.E10-14 (14), P22.1
unnamed: J6.E10-18 (18), P46.1
unnamed: J6.E10-25 (25), P23.1
unnamed: J6.E10-26 (26), P24.1
unnamed: J6.E10-27 (27), P25.1
unnamed: J6.E10-28 (28), P26.1
unnamed: J6.E10-29 (29), P27.1
unnamed: J6.E10-30 (30), P28.1
unnamed: J6.E10-35 (35), P29.1
unnamed: J6.E10-36 (36), P56.1
O2#1: J2.1, J6.E9-48 (8), J8.1
O2#1-IN: J2.2
O2#2: J2.3, J6.E9-47 (7), J8.3
O2#2-IN: J8.2
PRIMARY-CPU-RX: P118.1
PRIMARY-CPU-TX: P117.1
SECONDARY-CPU-RX: P116.1
SECONDARY-CPU-TX: P115.1
TACHO-OUT: J6.E10-16 (16)
TE1: J6.E10-20 (20), P48.1
TE2: J6.E10-19 (19), P51.1
TPS-IN: J6.E9-43 (3)
TR2: J6.E10-37 (37), P52.1
TT: J6.E10-17 (17), P55.1
VR_NEG: J6.E9-5 (5), J6.E9-6 (6), J6.E9-7 (7), P64.1, P67.1, P69.1
VSV2: J6.E9-39 (39), P62.1
VSV3: J6.E9-38 (38), P74.1
VT01: J6.E10-40 (40), P53.1
VT02: J6.E10-39 (39), P50.1
evap: J6.E9-74 (34), P73.1
neutral: J6.E9-76 (36), P68.1
o2 htr: J6.E9-71 (31), P70.1
sp2+: J6.E9-23 (23), P45.1
speed sensor: J6.E10-2 (2), P66.1
speed sensor2: J6.E9-3 (3), P63.1
starter: J6.E9-77 (37), P59.1
stoplight: J6.E10-4 (4), P60.1
tps idle: J6.E9-64 (24), P58.1
tps_idle2: J6.E9-63 (23), P54.1
vfb: J6.E9-29 (29), P65.1
