ElDominio/rusefi/firmware/config/boards/mega100/suprapnp/outputs.kicad_sch

## KiCad design firmware/config/boards/mega100/suprapnp/outputs.kicad_sch (2025-05-04, last stored version)

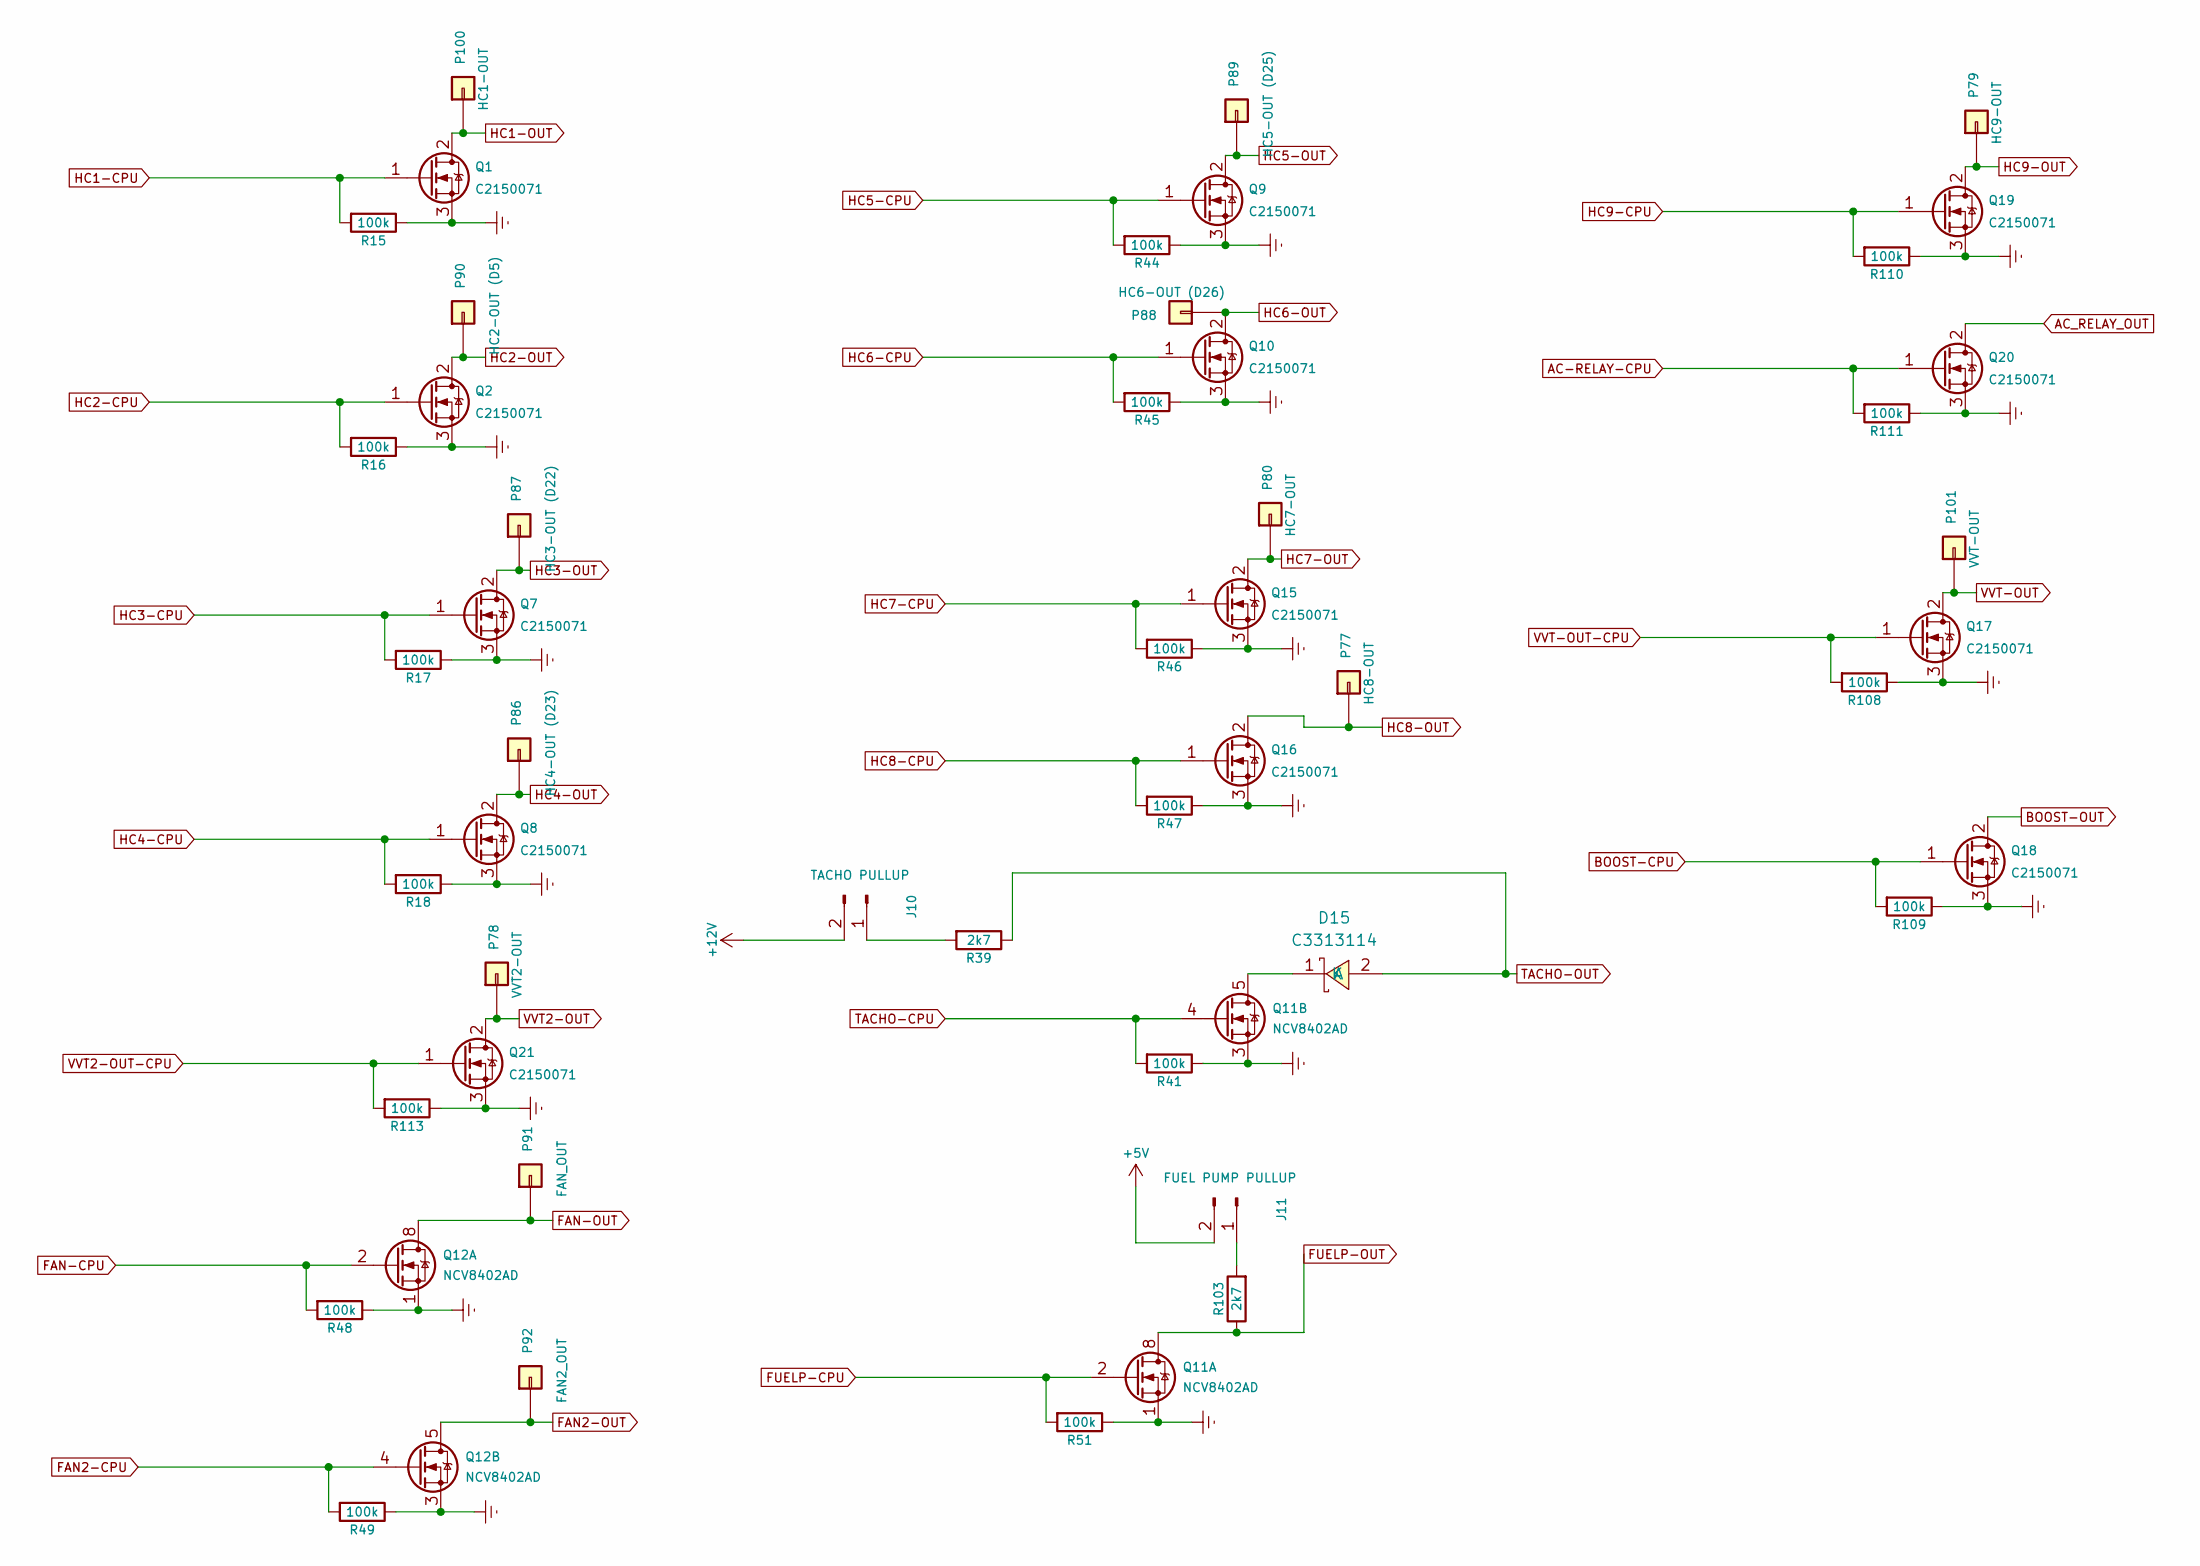
[picture p15: schematic outputs.kicad_sch]

Parts:
D15: C3313114; SOD-523_L1.2-W0.8-LS1.6-RD; LCSC Part C3313114
J10: TACHO PULLUP; PinHeader_1x02_P2.54mm_Vertical
J11: FUEL PUMP PULLUP; PinHeader_1x02_P2.54mm_Vertical
P77: HC8-OUT; TestPoint_THTPad_1.5x1.5mm_Drill0.7mm
P78: VVT2-OUT; TestPoint_THTPad_1.5x1.5mm_Drill0.7mm
P79: HC9-OUT; TestPoint_THTPad_1.5x1.5mm_Drill0.7mm
P80: HC7-OUT; TestPoint_THTPad_1.5x1.5mm_Drill0.7mm
P86: HC4-OUT (D23); TestPoint_THTPad_1.5x1.5mm_Drill0.7mm
P87: HC3-OUT (D22); TestPoint_THTPad_1.5x1.5mm_Drill0.7mm
P88: HC6-OUT (D26); TestPoint_THTPad_1.5x1.5mm_Drill0.7mm
P89: HC5-OUT (D25); TestPoint_THTPad_1.5x1.5mm_Drill0.7mm
P90: HC2-OUT (D5); TestPoint_THTPad_1.5x1.5mm_Drill0.7mm
P91: FAN_OUT; TestPoint_THTPad_1.5x1.5mm_Drill0.7mm
P92: FAN2_OUT; TestPoint_THTPad_1.5x1.5mm_Drill0.7mm
P100: HC1-OUT; TestPoint_THTPad_1.5x1.5mm_Drill0.7mm
P101: VVT-OUT; TestPoint_THTPad_1.5x1.5mm_Drill0.7mm
Q1, Q2, Q7, Q8, Q9, Q10, Q15, Q16, Q17, Q18, Q19, Q20, Q21: C2150071; TO-252-2_L6.5-W6.2-P4.57-LS10.0-BR-CW; MPN C2150071; LCSC C2150071
Q11, Q12: NCV8402AD; SOIC-8_L4.9-W3.9-P1.27-LS6.0-BL; MPN NCV8402ADDR2G; LCSC C109030
R15, R16, R17, R18, R41, R44, R45, R46, R47, R48, R49, R51, R108, R109, R110, R111, R113: 100k; R0603; MPN C25803; LCSC C25803
R39, R103: 2k7; R0603; MPN C13167; LCSC C13167

Connections:
+5V: J11.2
+12V: J10.2
AC-RELAY-CPU: Q20.1 (G), R111.2
AC_RELAY_OUT: Q20.2 (D)
BOOST-CPU: Q18.1 (G), R109.2
BOOST-OUT: Q18.2 (D)
Earth: Q1.3 (S), Q2.3 (S), Q7.3 (S), Q8.3 (S), Q9.3 (S), Q10.3 (S), Q11.1 (S1), Q11.3 (S2), Q12.1 (S1), Q12.3 (S2), Q15.3 (S), Q16.3 (S), Q17.3 (S), Q18.3 (S), Q19.3 (S), Q20.3 (S), Q21.3 (S), R15.1, R16.1, R17.1, R18.1, R41.1, R44.1, R45.1, R46.1, R47.1, R48.1, R49.1, R51.1, R108.1, R109.1, R110.1, R111.1, R113.1
FAN2-CPU: Q12.4 (G2), R49.2
FAN2-OUT: P92.1, Q12.5 (D2), Q12.6 (D2)
FAN-CPU: Q12.2 (G1), R48.2
FAN-OUT: P91.1, Q12.7 (D1), Q12.8 (D1)
FUELP-CPU: Q11.2 (G1), R51.2
FUELP-OUT: Q11.7 (D1), Q11.8 (D1), R103.1
HC1-CPU: Q1.1 (G), R15.2
HC1-OUT: P100.1, Q1.2 (D)
HC2-CPU: Q2.1 (G), R16.2
HC2-OUT: P90.1, Q2.2 (D)
HC3-CPU: Q7.1 (G), R17.2
HC3-OUT: P87.1, Q7.2 (D)
HC4-CPU: Q8.1 (G), R18.2
HC4-OUT: P86.1, Q8.2 (D)
HC5-CPU: Q9.1 (G), R44.2
HC5-OUT: P89.1, Q9.2 (D)
HC6-CPU: Q10.1 (G), R45.2
HC6-OUT: P88.1, Q10.2 (D)
HC7-CPU: Q15.1 (G), R46.2
HC7-OUT: P80.1, Q15.2 (D)
HC8-CPU: Q16.1 (G), R47.2
HC8-OUT: P77.1, Q16.2 (D)
HC9-CPU: Q19.1 (G), R110.2
HC9-OUT: P79.1, Q19.2 (D)
unnamed: D15.1 (K), Q11.5 (D2), Q11.6 (D2)
unnamed: J10.1, R39.2
unnamed: J11.1, R103.2
TACHO-CPU: Q11.4 (G2), R41.2
TACHO-OUT: D15.2 (A), R39.1
VVT2-OUT: P78.1, Q21.2 (D)
VVT2-OUT-CPU: Q21.1 (G), R113.2
VVT-OUT: P101.1, Q17.2 (D)
VVT-OUT-CPU: Q17.1 (G), R108.2
