ElDominio/rusefi/firmware/config/boards/mega100/suprapnp/power_supply.kicad_sch

## KiCad design firmware/config/boards/mega100/suprapnp/power_supply.kicad_sch (2025-05-04, last stored version)

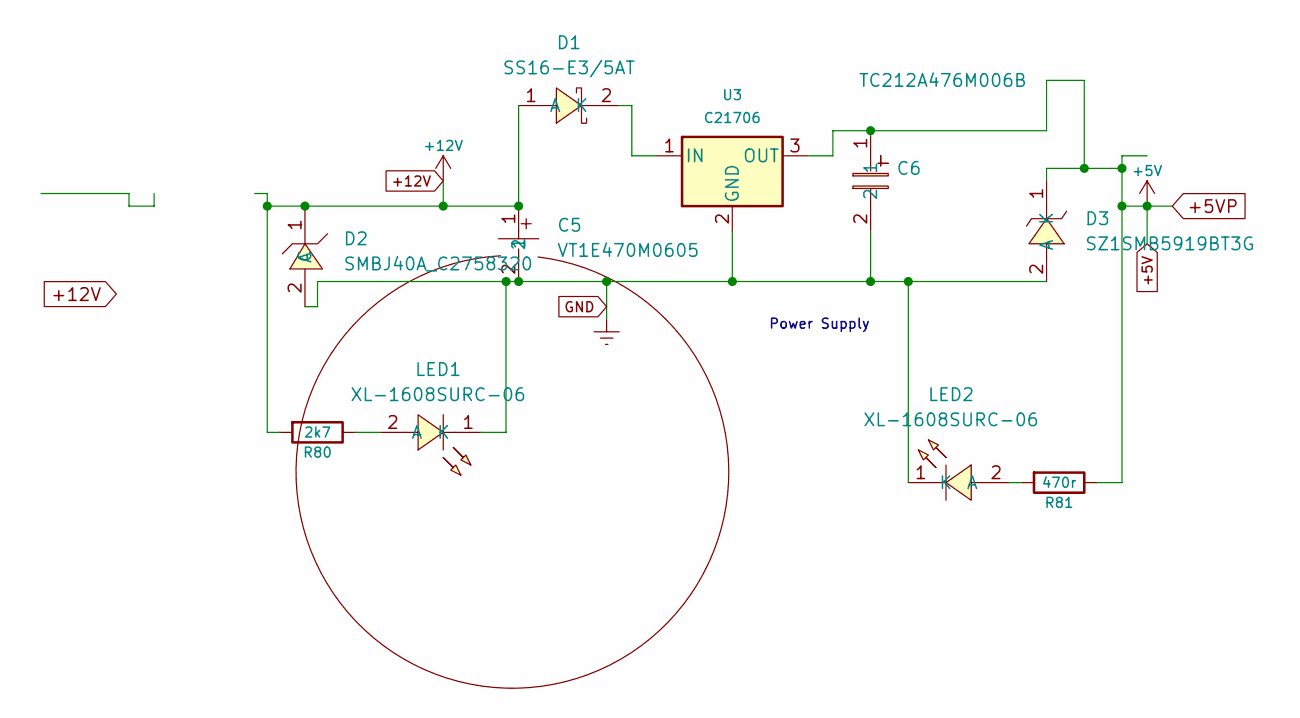
[picture p16: schematic power_supply.kicad_sch]

Parts:
C5: VT1E470M0605; CAP-SMD_BD6.3-L6.6-W6.6-FD; LCSC Part C141425
C6: TC212A476M006B; CAP-SMD_L3.2-W1.6-FD; LCSC Part C726165
D1: SS16-E3/5AT; SMA_L4.4-W2.8-LS5.4-R-RD; LCSC Part C511401
D2: SMBJ40A_C2758320; SMB_L4.6-W3.6-LS5.3-RD; LCSC Part C2758320
D3: SZ1SMB5919BT3G; SMB_L4.6-W3.6-LS5.3-RD; LCSC Part C463423
LED1, LED2: XL-1608SURC-06; LED0603-RD_RED; LCSC Part C5355446
R80: 2k7; R0603; MPN C13167; LCSC C13167
R81: 470r; R0805; MPN C17710; LCSC C17710
U3: C21706; TO-252-2_L6.5-W6.2-P4.57-LS10.0-BR-CW; LCSC C21706

Connections:
+5V: C6.1, D3.1 (K), R81.1, U3.3 (OUT)
+12V: C5.1, D1.1 (A), D2.1 (C), R80.2
Earth: C5.2, C6.2, D2.2 (A), D3.2 (A), LED1.1 (K), LED2.1 (K), U3.2 (GND)
unnamed: D1.2 (K), U3.1 (IN)
unnamed: LED1.2 (A), R80.1
unnamed: LED2.2 (A), R81.2

Notes on the sheet:
Power Supply
