ElDominio/rusefi/firmware/config/boards/mega100/suprapnp/trigger_input.kicad_sch

## KiCad design firmware/config/boards/mega100/suprapnp/trigger_input.kicad_sch (2025-05-04, last stored version)

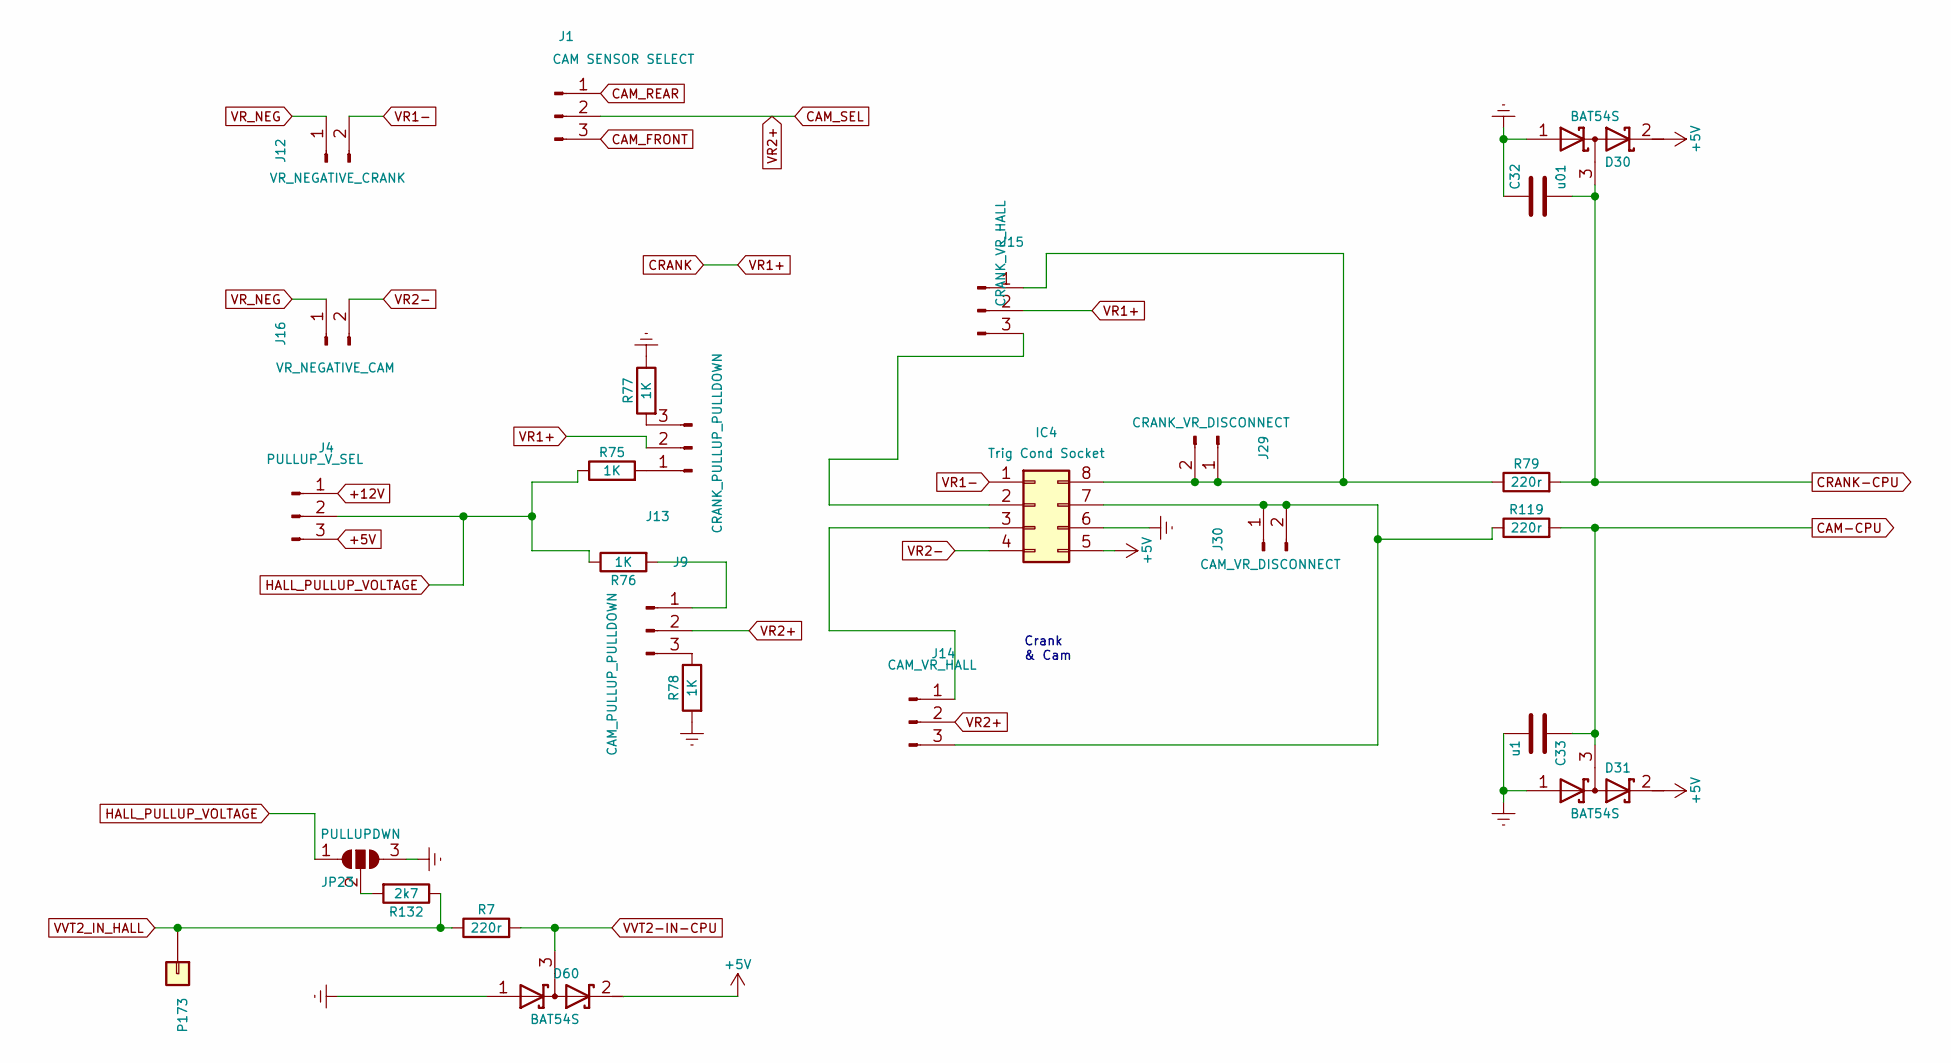
[picture p17: schematic trigger_input.kicad_sch]

Parts:
C32: u01; C0805; MPN CL21B103KBCNNNC; LCSC C84715
C33: u1; C0805; MPN CL21B104KBFNNNE; LCSC C136621
D30, D31, D60: BAT54S; SOT-23-3_L3.0-W1.7-P0.95-LS2.9-BR; MPN BAT54S,215; LCSC C47546
IC4: Trig Cond Socket; DIP-8_W7.62mm_Socket
J1: CAM SENSOR SELECT; PinHeader_1x03_P2.54mm_Vertical
J4: PULLUP_V_SEL; PinHeader_1x03_P2.54mm_Vertical
J9: CAM_PULLUP_PULLDOWN; PinHeader_1x03_P2.54mm_Vertical
J12: VR_NEGATIVE_CRANK; PinHeader_1x02_P2.54mm_Vertical
J13: CRANK_PULLUP_PULLDOWN; PinHeader_1x03_P2.54mm_Vertical
J14: CAM_VR_HALL; PinHeader_1x03_P2.54mm_Vertical
J15: CRANK_VR_HALL; PinHeader_1x03_P2.54mm_Vertical
J16: VR_NEGATIVE_CAM; PinHeader_1x02_P2.54mm_Vertical
J29: CRANK_VR_DISCONNECT; PinHeader_1x02_P2.54mm_Vertical
J30: CAM_VR_DISCONNECT; PinHeader_1x02_P2.54mm_Vertical
JP23: PULLUPDWN; SolderJumper-3_P1.3mm_Open_Pad1.0x1.5mm_NumberLabels; MPN DNP
P173: VVT2_IN_HALL; TestPoint_THTPad_1.5x1.5mm_Drill0.7mm
R7, R79, R119: 220r; R0805; MPN C17557; LCSC C17557
R75, R76, R77, R78: 1K; R0805; MPN C17513; LCSC C17513
R132: 2k7; R0603; MPN C13167; LCSC C13167

Connections:
+5V: D30.2 (K), D31.2 (K), D60.2 (K), IC4.5, J4.3
+12V: J4.1
CAM-CPU: C33.1, D31.3 (common), R119.2
CAM_FRONT: J1.3
CAM_REAR: J1.1
CAM_SEL: J1.2, J9.2, J14.2
CRANK: J13.2, J15.2
CRANK-CPU: C32.2, D30.3 (common), R79.2
Earth: C32.1, C33.2, D30.1 (A), D31.1 (A), D60.1 (A), IC4.6, JP23.3 (B), R77.1, R78.2
HALL_PULLUP_VOLTAGE: J4.2, JP23.1 (A), R75.1, R76.1
unnamed: IC4.2, J15.3
unnamed: IC4.3, J14.1
unnamed: IC4.7, J14.3, J30.1, J30.2, R119.1
unnamed: IC4.8, J15.1, J29.1, J29.2, R79.1
unnamed: J9.1, R76.2
unnamed: J9.3, R78.1
unnamed: J13.1, R75.2
unnamed: J13.3, R77.2
unnamed: JP23.2 (C), R132.2
VR1-: IC4.1, J12.2
VR2-: IC4.4, J16.2
VR_NEG: J12.1, J16.1
VVT2-IN-CPU: D60.3 (common), R7.2
VVT2_IN_HALL: P173.1, R7.1, R132.1

Notes on the sheet:
Crank & Cam
