ElDominio/rusefi/firmware/integration/config_page_6.txt

! TunerStudio page 6 — alphax custom features.
! These settings live outside the main engine_configuration_s image (page 1) to keep
! page 1 under the 64 KB TS page limit and to isolate non-mainline custom features.
! See controllers/custom_page.cpp and controllers/extra_flash_pages.cpp.
!
! Fields are ordered for natural C alignment (the generator inserts alignmentFill
! automatically): bits, then bytes, then uint16, then 4-byte floats.

! The isolated page generator does not inherit page-1 #defines, so re-declare the ones we use.
#define CLT_UPPER_LIMIT 250
#define MAP_UPPER_LIMIT 650
#define UNITS_KMH_TO_MPH 0.62137119
#define LUA_LIMITER_CURVE_SIZE 8
#define LAUNCH_POWER_RAMP_CURVE_SIZE 8
#define BURST_KNOCK_RPM_SIZE 8
#define BURST_KNOCK_TPS_RATE_SIZE 8
#define WOT_ENRICHMENT_SIZE 8
#define SPORT_PEDAL_SIZE 8
#define INJ_CURVE_SIZE 12
#define VVT_ADV_DISTANCE_SIZE 9
#define VVT_ADV_OILP_SIZE 6

! Custom types re-declared for the isolated page generator (see config_page_4.txt header).
! The C++ enums themselves are defined in headers (e.g. rusefi_enums.h) and shared;
! these declarations only drive the TS .ini for page 6.
custom switch_input_pin_e 2 bits, U16, @OFFSET@, [0:8], $switch_input_pin_e_list
custom output_pin_e 2 bits, U16, @OFFSET@, [0:8], $output_pin_e_list
custom pin_input_mode_e 1 bits, U08, @OFFSET@, [0:2], $pin_input_mode_e_enum
custom pin_output_mode_e 1 bits, U08, @OFFSET@, [0:1], $pin_output_mode_e_enum

#define lua_gauge_e_enum "Lua Gauge 1", "Lua Gauge 2", "Lua Gauge 3", "Lua Gauge 4", "Lua Gauge 5", "Lua Gauge 6", "Lua Gauge 7", "Lua Gauge 8"
custom lua_gauge_e 1 bits, S08, @OFFSET@, [0:2], @@lua_gauge_e_enum@@
#define lua_gauge_meaning_e_enum "greater than", "less than"
custom lua_gauge_meaning_e 1 bits, S08, @OFFSET@, [3:3], @@lua_gauge_meaning_e_enum@@

#define exhaust_cutout_activation_e_enum "OFF", "Switch", "Sport Mode", "Auto + Sport Mode"
custom exhaust_cutout_activation_e 1 bits, U08, @OFFSET@, [0:1], @@exhaust_cutout_activation_e_enum@@
#define exhaust_cutout_behavior_e_enum "Always Closed", "Always Open", "Auto"
custom exhaust_cutout_behavior_e 1 bits, U08, @OFFSET@, [0:1], @@exhaust_cutout_behavior_e_enum@@
#define exhaust_cutout_output_mode_e_enum "Digital", "PWM", "H-Bridge"
custom exhaust_cutout_output_mode_e 1 bits, U08, @OFFSET@, [0:1], @@exhaust_cutout_output_mode_e_enum@@

#define sm_clutch_switch_e_enum "None", "Clutch Up", "Clutch Down", "INVALID"
custom sm_clutch_switch_e 1 bits, U08, @OFFSET@, [0:1], @@sm_clutch_switch_e_enum@@
#define sm_shift_detection_mode_e_enum "RPM Rate", "VSS Rate (needs VSS sensor)", "INVALID", "INVALID"
custom sm_shift_detection_mode_e 1 bits, U08, @OFFSET@, [0:1], @@sm_shift_detection_mode_e_enum@@
#define pops_and_bangs_cutout_inhibit_e_enum "Off", "Inhibit Unless Cutout Open"
custom pops_and_bangs_cutout_inhibit_e 1 bits, U08, @OFFSET@, [0:1], @@pops_and_bangs_cutout_inhibit_e_enum@@
#define eco_mode_switch_mode_e_enum "Off", "Inhibit"
custom eco_mode_switch_mode_e 1 bits, U08, @OFFSET@, [0:1], @@eco_mode_switch_mode_e_enum@@
#define sport_pedal_activation_e_enum "OFF", "Switch", "Sport Mode"
custom sport_pedal_activation_e 1 bits, U08, @OFFSET@, [0:1], @@sport_pedal_activation_e_enum@@
#define sport_mode_activation_e_enum "OFF", "Switch", "LuaGauge"
custom sport_mode_activation_e 1 bits, U08, @OFFSET@, [0:1], @@sport_mode_activation_e_enum@@
#define limiter_adder_source_e_enum "LuaGauge", "Sport Mode"
custom limiter_adder_source_e 1 bits, U08, @OFFSET@, [0:0], @@limiter_adder_source_e_enum@@
#define fan_ac_mode_e_enum "Disabled", "Relay", "Pressure"
custom fan_ac_mode_e 1 bits, U08, @OFFSET@, [0:1], @@fan_ac_mode_e_enum@@
#define oil_life_temp_source_e_enum "Oil Temp (EOT)", "Coolant Temp (CLT)"
custom oil_life_temp_source_e 1 bits, U08, @OFFSET@, [0:1], @@oil_life_temp_source_e_enum@@

custom fuel_pump_mode_e 1 bits, U08, @OFFSET@, [0:1], "Single", "Dual", "PWM"

#define imrc_mode_e_enum "Disabled", "Solenoid", "H-Bridge"
custom imrc_mode_e 1 bits, U08, @OFFSET@, [0:1], @@imrc_mode_e_enum@@

#define wheel_speed_source_e_enum "None", "Vehicle Speed", "Front Axle", "Rear Axle", "Output Shaft Speed", "Aux Speed 1", "Aux Speed 2"
custom wheel_speed_source_e 1 bits, U08, @OFFSET@, [0:2], @@wheel_speed_source_e_enum@@

#define main_speed_sensor_source_e_enum "None", "Output Shaft Speed", "Front Axle", "Rear Axle"
custom main_speed_sensor_source_e 1 bits, U08, @OFFSET@, [0:1], @@main_speed_sensor_source_e_enum@@
#define wheel_speed_sensor_mode_e_enum "None", "Physical Pin", "CAN / Lua"
custom wheel_speed_sensor_mode_e 1 bits, U08, @OFFSET@, [0:1], @@wheel_speed_sensor_mode_e_enum@@

struct_no_prefix page6_s

	! --- Downshift Blipper (automated rev-match on a clutch-in single-gear downshift) ---
	! Requires an Electronic Throttle Body, a calibrated Gear Detector (gear ratios + final
	! drive), a VSS sensor, and the Engine State Machine downshift detection.
	bit downshiftBlipperEnabled,"enabled","disabled";Downshift Blipper: master enable. Blips the ETB to rev-match a single-gear (N to N-1) downshift.
	bit downshiftBlipperRequireBrake,"yes","no";Downshift Blipper: require the brake pedal to be pressed before a blip is allowed (heel-and-toe behavior).
	bit downshiftBlipperRequireSportMode,"enabled","disabled";Downshift Blipper: require Sport Mode to be active for a blip to start. While Sport Mode is off, blips cannot start, and an in-progress blip is immediately ramped closed.

	uint8_t downshiftBlipperDriverTpsThreshold;Downshift Blipper: driver pedal % above which the blipper disables (driver is manually blipping).;"%", 1, 0, 0, 100, 0
	uint8_t downshiftBlipperMaxTpsLimit;Downshift Blipper: maximum throttle % the closed-loop PID hold is allowed to command. Does not limit the open-loop ramp-up phase, which targets etbMaximumPosition.;"%", 1, 0, 0, 100, 0
	uint8_t downshiftBlipperAlignmentPad;unused

	uint16_t downshiftBlipperMaxTimeMs;Downshift Blipper: maximum duration of an active blip before it is force-terminated (safety timeout).;"ms", 1, 0, 0, 5000, 0
	uint16_t downshiftBlipperLockoutTimeMs;Downshift Blipper: lockout after a blip during which another blip cannot start (anti-chatter).;"ms", 1, 0, 0, 5000, 0
	uint16_t downshiftBlipperMinRpm;Downshift Blipper: minimum engine RPM required to start a blip.;"rpm", 1, 0, 0, 15000, 0
	uint16_t downshiftBlipperMaxRpm;Downshift Blipper: blip is blocked when the computed target RPM exceeds this, to prevent over-rev.;"rpm", 1, 0, 0, 15000, 0
	uint16_t downshiftBlipRampOpenMs;Downshift Blipper: time to ramp the ETB open to etbMaximumPosition (open-loop) at blip start.;"ms", 1, 0, 0, 500, 0
	uint16_t downshiftBlipRampCloseMs;Downshift Blipper: time to ramp the ETB back to the pedal target after the blip cuts.;"ms", 1, 0, 0, 500, 0
	uint16_t downshiftBlipOpenLoopWindowRpm;Downshift Blipper: once RPM is within this many RPM of the target, hand off from the open-loop ramp (etbMaximumPosition) to the closed-loop PID hold.;"rpm", 1, 0, 0, 2000, 0
	uint16_t downshiftBlipperMinVss;Downshift Blipper: minimum vehicle speed to allow blipping.;{bitStringValue(velocityUnitsLabels, useMetricOnInterface)}, {useMetricOnInterface ? 1 : @@UNITS_KMH_TO_MPH@@}, 0, 0, 300, 0

	float downshiftBlipperKp;Downshift Blipper: PID proportional gain. Error is normalized to per-100-RPM units, output is throttle %.;"", 1, 0, 0, 1000, 3
	float downshiftBlipperKi;Downshift Blipper: PID integral gain.;"", 1, 0, 0, 1000, 3
	float downshiftBlipperKd;Downshift Blipper: PID derivative gain.;"", 1, 0, 0, 1000, 3

	! --- TPS-to-RPM Feed Forward Curve (shared by Downshift Blipper + Upshift RPM Hold) ---
	! Throttle % required at neutral (clutch in) to sustain each RPM. Used as an additive
	! feed-forward seed for both the downshift rev-match PID and the upshift RPM-hold PID, so
	! each PID only corrects the residual error instead of building the throttle from zero.
	! When left at zero the feed-forward term is zero and both PIDs behave exactly as before.
	float[10] tpsRpmFeedForwardBins;TPS-to-RPM Feed Forward: RPM bins (curve X).;"rpm", 1, 0, 0, 20000, 0
	float[10] tpsRpmFeedForwardValues;TPS-to-RPM Feed Forward: throttle % at neutral for each RPM bin (curve Y).;"%", 1, 0, 0, 100, 1

	! --- Upshift RPM Hold (inverse of the Downshift Blipper) ---
	! On a clutch-in upshift the Engine State Machine raises engineSmIsUpshifting; this module
	! briefly commands the ETB to HOLD engine RPM at the incoming (higher) gear's matched speed
	! instead of letting it free-fall through the shift, so the clutch re-engages smoothly.
	! Requires an Electronic Throttle Body, a calibrated Gear Detector, a VSS sensor, and the
	! Engine State Machine upshift detection. Shares the TPS-to-RPM Feed Forward curve above.
	bit upshiftRpmHoldEnabled,"enabled","disabled";Upshift RPM Hold: master enable. Holds the ETB to keep engine RPM at the next-higher gear's matched speed during a single-gear (N to N+1) upshift.

	uint8_t upshiftRpmHoldDriverTpsThreshold;Upshift RPM Hold: driver pedal % above which the hold disables (driver is back on the throttle).;"%", 1, 0, 0, 100, 0
	uint8_t upshiftRpmHoldMaxTpsLimit;Upshift RPM Hold: maximum throttle % the PID is allowed to command.;"%", 1, 0, 0, 100, 0

	uint16_t upshiftRpmHoldMaxTimeMs;Upshift RPM Hold: maximum duration of an active hold before it is force-terminated (safety timeout).;"ms", 1, 0, 0, 2000, 0
	uint16_t upshiftRpmHoldLockoutTimeMs;Upshift RPM Hold: lockout after a hold during which another hold cannot start (anti-chatter).;"ms", 1, 0, 0, 5000, 0
	uint16_t upshiftRpmHoldMinRpm;Upshift RPM Hold: minimum engine RPM required to start a hold.;"rpm", 1, 0, 0, 15000, 0
	uint16_t upshiftRpmHoldMaxRpm;Upshift RPM Hold: a hold is blocked from starting if engine RPM at the shift exceeds this (over-rev safety, e.g. a missed/late shift near the limiter).;"rpm", 1, 0, 0, 15000, 0
	uint16_t upshiftRpmHoldRampDownMs;Upshift RPM Hold: time to ramp the ETB to the first PID value at hold start.;"ms", 1, 0, 0, 500, 0
	uint16_t upshiftRpmHoldRampUpMs;Upshift RPM Hold: time to ramp the ETB back to the pedal target after the hold ends.;"ms", 1, 0, 0, 500, 0
	uint16_t upshiftRpmHoldMinVss;Upshift RPM Hold: minimum vehicle speed to allow a hold.;{bitStringValue(velocityUnitsLabels, useMetricOnInterface)}, {useMetricOnInterface ? 1 : @@UNITS_KMH_TO_MPH@@}, 0, 0, 300, 0

	float upshiftRpmHoldKp;Upshift RPM Hold: PID proportional gain. Error is normalized to per-100-RPM units, output is throttle %.;"", 1, 0, 0, 1000, 3
	float upshiftRpmHoldKi;Upshift RPM Hold: PID integral gain.;"", 1, 0, 0, 1000, 3
	float upshiftRpmHoldKd;Upshift RPM Hold: PID derivative gain.;"", 1, 0, 0, 1000, 3

	! --- Exhaust Cutout Control ---
	exhaust_cutout_output_mode_e exhaustCutoutOutputMode;Exhaust cutout output type: Digital on/off, PWM, or H-Bridge motor
	exhaust_cutout_activation_e exhaustCutoutActivationMode;Exhaust cutout activation mode. Switch/Sport Mode pick the input for the behavior below; Auto + Sport Mode bypasses the behavior and auto-opens (RPM/TPS/MAP triggers) only while Sport Mode is active.
	exhaust_cutout_behavior_e exhaustCutoutBehaviorLow;Cutout behavior when switch is OFF or Sport Mode is inactive (Switch/Sport Mode activation modes only)
	exhaust_cutout_behavior_e exhaustCutoutBehaviorHigh;Cutout behavior when switch is ON or Sport Mode is active (Switch/Sport Mode activation modes only)

	switch_input_pin_e exhaustCutoutSwitchPin;Hardware switch input pin
	pin_input_mode_e exhaustCutoutSwitchPinMode;

	output_pin_e exhaustCutoutOutputPin;Cutout output pin (digital) or H-Bridge IN1 (Open direction)
	pin_output_mode_e exhaustCutoutOutputPinMode;

	output_pin_e exhaustCutoutHBridgePin2;H-Bridge IN2 pin (Close direction)
	pin_output_mode_e exhaustCutoutHBridgePin2Mode;

	output_pin_e exhaustCutoutLedPin;Status LED output pin
	pin_output_mode_e exhaustCutoutLedPinMode;

	uint16_t exhaustCutoutOpenRpm;RPM threshold to open cutout (0 to disable);"rpm", 1, 0, 0, 20000, 0
	uint8_t exhaustCutoutOpenTps;TPS threshold to open cutout (0 to disable);"%", 1, 0, 0, 100, 0
	uint8_t autoscale exhaustCutoutTpsDelayS;Anti-blip: TPS must exceed threshold for this long before opening;"s", 0.1, 0, 0, 25, 1
	float exhaustCutoutOpenMapKpa;MAP/Boost threshold to open cutout (0 to disable);"kPa", 1, 0, 0, 500, 1
	uint8_t autoscale exhaustCutoutClosingDelayS;Hold-open time after triggers clear;"s", 0.1, 0, 0, 25, 1
	uint8_t autoscale exhaustCutoutMoveDurationS;H-Bridge motor drive time (de-energizes after). Also controls LED blink duration and actuator test step duration.;"s", 0.1, 0, 0, 5, 1

	uint16_t exhaustCutoutPwmFrequency;PWM output frequency (PWM mode only);"Hz", 1, 0, 1, 10000, 0
	uint8_t autoscale exhaustCutoutPwmOpenDuty;PWM duty when cutout is OPEN (PWM mode only);"%", 1, 0, 0, 100, 0
	uint8_t autoscale exhaustCutoutPwmClosedDuty;PWM duty when cutout is CLOSED (PWM mode only);"%", 1, 0, 0, 100, 0

	uint16_t exhaustCutoutHBridgePwmFrequency;H-Bridge IN1/IN2 PWM frequency (H-Bridge mode only);"Hz", 1, 0, 1, 10000, 0
	uint8_t autoscale exhaustCutoutHBridgeDutyCycle;H-Bridge motor drive duty cycle (H-Bridge mode only);"%", 1, 0, 0, 100, 0

	! --- Sport Mode (Engine State Machine) ---
	! Global "driver wants aggressive behavior" flag, fed to Ghost Cam / Sport Pedal / Exhaust
	! Cutout / Pops & Bangs / Downshift Blip / Limiter Adders as an activation source. Limp mode
	! out-votes Sport Mode (protective); Sport Mode out-votes Eco Mode (mutually exclusive).
	sport_mode_activation_e smSportModeActivationMode;Sport Mode: activation source. OFF disables; Switch reads a hardware switch pin; LuaGauge compares a Lua gauge against a threshold.
	switch_input_pin_e smSportModeSwitchPin;Sport Mode: hardware switch input pin (Switch mode).
	pin_input_mode_e smSportModeSwitchPinMode;
	lua_gauge_e smSportModeLuaGauge;Sport Mode: Lua gauge used as the activation source (LuaGauge mode).
	lua_gauge_meaning_e smSportModeLuaGaugeMeaning;Sport Mode: Lua gauge comparison direction.
	float smSportModeLuaGaugeThreshold;Sport Mode: Lua gauge activation threshold (LuaGauge mode).;"", 1, 0, -30000, 30000, 3

	! --- Engine State Machine thresholds + shift detection (enable bit stays in page 1) ---
	uint8_t smWotTpsThreshold;Engine SM: TPS threshold above which the engine is at Wide Open Throttle.;"%", 1, 0, 50, 100, 0
	uint8_t smTransientHoldoffCallbacks;Engine SM: slow-callback periods (50 ms each) to hold the Transient state after the accel-enrichment threshold drops. 0 = no hold-off.;"callbacks", 1, 0, 0, 20, 0

	bit stateBasedStft,"enabled","disabled";Engine SM: drive STFT region selection from the live SM state (Idle/Overrun/WOT/Cruise) instead of the RPM/load region thresholds. The per-region STFT settings (time constant, max add/remove) are reused unchanged.
	bit smSecondClutchSwitchAvailable,"yes","no";Engine SM: a second clutch switch is also wired (e.g. both Clutch-Up and Clutch-Down, not just whichever is selected below). Lets shift detection open the window on the earliest available press edge and close it on the earliest available release edge, instead of relying solely on the configured switch's own edges.
	bit smRelatchOnClutchDown,"enabled","disabled";Engine SM: while the shift latch (smShiftLatchTimeMs) is active, a fresh Clutch-Down full-press resets it back to the full duration instead of letting it expire -- keeps Upshifting/Downshifting asserted through a flurry of quick consecutive shifts. Requires smSecondClutchSwitchAvailable (both Clutch-Up and Clutch-Down wired).

	sm_clutch_switch_e smUpshiftClutchSwitch;Engine SM: Clutch switch that signals an upshift. 'Clutch Up' opens the shift window when the pedal leaves rest (falling edge, drivetrain still locked) and closes it when the pedal returns to rest; 'Clutch Down' opens the window on full press and closes it on release. Flat-shift torque reduction always overrides this.
	sm_clutch_switch_e smDownshiftClutchSwitch;Engine SM: Clutch switch that signals a downshift.
	sm_shift_detection_mode_e smShiftDetectionMode;Engine SM: Signal source for the shift-direction accumulator. RPM Rate: accumulates positive/negative based on engine RPM rate of change. VSS Rate: accumulates based on vehicle speed rate of change (needs VSS sensor).
	int16_t smAccelRateThreshold;Engine SM: RPM/s rate threshold to enter the Accelerating state. Also the accumulator gain normalizer while accelerating -- at exactly this rate the accumulator climbs at smAccumulatorGain pct/s, faster rates climb proportionally faster. 0 disables the Accelerating state.;"RPM/s", 1, 0, 0, 10000, 0
	int16_t smDecelRateThreshold;Engine SM: RPM/s rate threshold to enter the Decelerating state (RPM falling faster than this). Also the accumulator normalizer in Overrun. 0 disables the Decelerating state.;"RPM/s", 1, 0, 0, 10000, 0
	uint16_t smRpmRateWindowMs;Engine SM: Time window used to compute RPM rate of change (RPM/s, "RPM/t") for Accelerating/Decelerating state detection and the RPM-rate shift-accumulator signal. Larger values smooth out sensor/tooth noise at the cost of slower response, smaller values track faster but are noisier. Internally floored to one slow-callback tick (50 ms). smAccelRateThreshold/smDecelRateThreshold stay in RPM/s regardless of this setting and do not need re-tuning when it changes.;"ms", 1, 0, 0, 1000, 0
	uint16_t smShiftLatchTimeMs;Engine SM: once shift direction is confirmed, hold Upshifting/Downshifting true for at least this long. 0 = no latch.;"ms", 1, 0, 0, 2000, 0
	uint16_t smShiftMinVss;Engine SM: VSS Rate mode only -- minimum vehicle speed. Below this the accumulator decays instead of accumulating. 0 = no minimum.;{bitStringValue(velocityUnitsLabels, useMetricOnInterface)}, {useMetricOnInterface ? 1 : @@UNITS_KMH_TO_MPH@@}, 0, 0, 300, 0
	int8_t smAccumulatorUpshiftThreshold;Engine SM: Accumulator must reach or exceed this value (0..100) to confirm an upshift. The accumulator runs from -100 to +100.;"", 1, 0, 0, 100, 0
	int8_t smAccumulatorDownshiftThreshold;Engine SM: Accumulator must reach or fall below the negative of this value (0..100) to confirm a downshift.;"", 1, 0, 0, 100, 0
	uint16_t smAccelHoldMs;Engine SM: once the Accelerating rate threshold is met, hold the Accelerating state for at least this long after the rate drops back below threshold. A fresh threshold crossing during the hold resets it back to the full duration. Broken immediately by a lift into the Coasting/Overrun phase, so a stale hold can never mask Overrun/DFCO. 0 = no hold (raw signal, legacy behavior).;"ms", 1, 0, 0, 5000, 0
	float smAccumulatorGain;Engine SM: Accumulator climb rate in %/s per 1x threshold ratio. At exactly the threshold rate, the accumulator changes by this many %/s. Larger = faster response.;"%/s", 1, 0, 0, 200, 1
	float smAccumulatorDecayRate;Engine SM: Rate at which the accumulator decays toward 0 (%/s) when the signal is within the ±threshold dead-band. Larger = faster decay.;"%/s", 1, 0, 0, 200, 1

	uint16_t smAccumulatorSnapTimeMs;Engine SM: once continuously in the Accelerating state for this long, a still-negative accumulator (left over from a prior decel run) is forced to 0 instead of waiting for it to decay/climb across zero on its own. Symmetrically, once continuously in Decelerating or Overrun for this long, a still-positive accumulator is forced to 0. Lets a same-gear direction reversal (e.g. a long overrun immediately followed by acceleration) shed a large stale opposite-sign accumulator quickly, rather than needing an equally long run the other way to null it out and risking a stale shift-direction call (e.g. a spurious downshift blip on clutch-in right after tipping back into the throttle). 0 = disabled (legacy decay/cross-only behavior).;"ms", 1, 0, 0, 10000, 0

	! --- Limp Mode (Engine State Machine sub-feature) ---
	! These limits are enforced only while the state machine has latched the Limp state.
	! Limp mode is triggered by an ETB jam (see limp_manager.cpp reportEtbJammed ->
	! EngineStateMachine::reportLimpCondition) or by the CEL escalating to flashing
	! (isCelBlinkingActive(), see check_engine_light.cpp) -- the same points-gated
	! celBlinkPointsThreshold the CEL itself uses, not a separate DTC-severity threshold.
	uint8_t limpModeEtbLimit;Limp Mode: maximum electronic throttle opening % allowed while limp mode is active.;"%", 1, 0, 0, 100, 0
	uint8_t limpModeTimingReduction;Limp Mode: ignition timing pulled (retarded) while limp mode is active.;"deg", 1, 0, 0, 30, 0
	uint8_t limpModeAfrEnrichment;Limp Mode: target mixture enrichment (richer) while limp mode is active. 0 = no enrichment.;"%", 1, 0, 0, 30, 0
	uint16_t limpModeRevLimit;Limp Mode: hard RPM limit enforced while limp mode is active. 0 = no limp rev limit.;"rpm", 1, 0, 0, 15000, 0
	uint16_t limpModeBoostLimit;Limp Mode: maximum closed-loop boost target while limp mode is active. 0 = no limp boost limit.;"kPa", 1, 0, 0, 500, 0

	! --- Misfire Detection (Engine State Machine sub-feature) ---
	! Tooth-timing misfire detection, active only while the SM reports Idle (lowest rotating
	! inertia = strongest combustion-torque signal). Each cylinder's expansion-stroke segment
	! time is measured and compared against ONE shared engine-wide baseline (a slow rolling
	! average of healthy segments) -- detection is NOT cylinder-specific. A firing is "flagged"
	! when its segment exceeds the adaptive threshold: baseline + misfireK * wobble, where
	! "wobble" is a second slow EMA tracking the typical spread of clean-firing durations
	! around the baseline. This self-calibrates sensitivity to the engine's own noise floor --
	! a smooth engine (low wobble) gets a tight threshold automatically; a lumpy cam or rough
	! idle (high wobble) gets a looser threshold and avoids false positives. To reject one-off
	! noise, a flagged firing is only counted once at least misfireConsecutiveCount flagged
	! firings have occurred within the last misfireWindowFirings firings (any cylinder). When
	! the cumulative counted total reaches misfireCountThreshold the generic OBD random/
	! multiple-cylinder misfire DTC (P0300) is thrown and held until power cycle. Misfire
	! detection's job ends at throwing that DTC -- whether/how the check-engine light itself
	! reacts to an active DTC is handled generically elsewhere (see Check Engine Triggering).
	! Set misfireCountThreshold to 0 to disable throwing the DTC entirely (monitor-only mode).
	bit misfireDetectionEnabled,"enabled","disabled";Misfire Detection: master enable. Detects misfires at idle (only while the Engine State Machine reports the Idle state) and throws the generic misfire DTC (OBD P0300) once the count threshold is reached. Detection is engine-wide, not per-cylinder.
	uint8_t misfireConsecutiveCount;Misfire Detection: minimum number of flagged firings that must fall within the recent-firings window (misfireWindowFirings) before a misfire is actually counted. This is a rate test over the whole engine, not one cylinder. Higher rejects more sporadic noise, but it must stay low enough relative to the window size and cylinder count to still trip on a single dead cylinder (a single dead cylinder produces roughly misfireWindowFirings divided by cylindersCount flags per window). Recommended N (with the matching window below) -- 4-cyl: 3, 6-cyl: 2, 8-cyl: 2.;"events", 1, 0, 1, 20, 0
	uint8_t misfireWindowFirings;Misfire Detection: length, in recent firings across all cylinders, of the sliding window the misfireConsecutiveCount rate test runs over. About two engine cycles is a good starting point. Recommended M (with the matching N above) -- 4-cyl: 12, 6-cyl: 12, 8-cyl: 16.;"firings", 1, 0, 1, 32, 0
	uint16_t misfireCountThreshold;Misfire Detection: total counted misfire events (engine-wide, accumulated since key-on) required before the misfire DTC (P0300) is thrown. Set to 0 to monitor only -- the misfireTotalCount gauge still accumulates but no DTC is ever set.;"events", 1, 0, 0, 10000, 0
	float misfireK;Misfire Detection: K multiplier for the wobble-based threshold. Threshold = baseline + K * wobble, where wobble is the engine's own rolling spread of clean-firing durations. Lower K is more sensitive. 3.0 is a good starting point for most engines.;"", 1, 0, 0.5, 20, 1
	float misfireWindowStart;Misfire Detection: window start, in degrees after each cylinder's TDC, where the expansion-torque deceleration is measured.;"deg", 1, 0, 0, 360, 0
	float misfireWindowEnd;Misfire Detection: window end, in degrees after each cylinder's TDC.;"deg", 1, 0, 0, 360, 0
	float misfireEmaAlphaDecel;Misfire Detection: EMA alpha when the segment line is ABOVE the baseline on the graph (longer duration, engine slowing). Controls how fast the baseline chases upward.;"", 1, 0, 0.001, 1, 3
	float misfireEmaAlphaAccel;Misfire Detection: EMA alpha when the segment line is BELOW the baseline on the graph (shorter duration, engine recovering). Controls how fast the baseline chases downward.;"", 1, 0, 0.001, 1, 3
	float misfireWobbleAlphaRise;Misfire Detection: wobble EMA alpha when the wobble line is climbing on the graph (spread increasing). Controls how fast the wobble chases upward.;"", 1, 0, 0.001, 1, 3
	float misfireWobbleAlphaFall;Misfire Detection: wobble EMA alpha when the wobble line is falling on the graph (spread decreasing). Controls how fast the wobble chases downward.;"", 1, 0, 0.001, 1, 3
	uint16_t misfireSettleCycles;Misfire Detection: firing events to wait after entering idle before flagging begins. The baseline and wobble update normally during this period. Set 0 to start immediately.;"cycles", 1, 0, 0, 5000, 0

	! --- Eco Mode (Engine State Machine sub-feature) ---
	! Fuel-economy overlay. Engages once the engine has been in the Cruising state continuously for
	! ecoModeCruisingTime AND MAP is at or below ecoModeMapLimit AND RPM is at or below ecoModeMaxRpm,
	! and drops instantly on leaving Cruising or exceeding the MAP/RPM limit (a tip-in into
	! Transient/WOT, or load/RPM creeping up while still nominally "cruising"). Once eco engages,
	! ecoModeEngageLockTime holds it forced active and ignores further state/MAP/VSS/RPM
	! re-evaluation for that long, so the torque-delivery step from eco's own AFR/timing/VVT/
	! throttle changes isn't misread as leaving Cruising and immediately dropped again -- Limp mode,
	! Sport Mode and the Inhibit switch still override the lock instantly (safety/driver intent
	! wins). While active it overrides target AFR, adds/pulls ignition timing, optionally retargets
	! the intake/exhaust VVT cams, scales the throttle target, and can hold a lower absolute
	! alternator charging target (when smart alternator control is enabled). A manual switch / Lua
	! gauge can Inhibit (block) eco; Limp mode and Sport Mode both out-vote eco entirely (Sport Mode
	! and Eco Mode are mutually exclusive).
	bit ecoModeEnabled,"enabled","disabled";Eco Mode: master enable. Engages after sustained cruising to bias fuel/timing/throttle for economy.
	bit ecoModeVvtOverride,"enabled","disabled";Eco Mode: also override the intake/exhaust VVT cam targets while active (engines with VVT only).

	eco_mode_switch_mode_e ecoModeSwitchMode;Eco Mode: how the manual switch / Lua gauge acts. Off ignores the switch. Inhibit blocks eco while asserted.
	switch_input_pin_e ecoModeSwitchPin;Eco Mode: hardware switch input pin (used by Inhibit).
	pin_input_mode_e ecoModeSwitchPinMode;
	lua_gauge_e ecoModeLuaGauge;Eco Mode: Lua gauge used as the switch source.
	lua_gauge_meaning_e ecoModeLuaGaugeMeaning;

	uint16_t ecoModeCruisingTime;Eco Mode: continuous time in the Cruising state before eco engages.;"sec", 1, 0, 0, 600, 0
	uint16_t ecoModeMapLimit;Eco Mode: MAP must be at or below this for eco to engage. Exceeding it drops eco instantly, just like leaving Cruising. 0 disables the MAP gate.;"kPa", 1, 0, 0, @@MAP_UPPER_LIMIT@@, 0
	uint16_t ecoModeMinVss;Eco Mode: minimum vehicle speed for eco to engage. Below this the cruise timer is reset and eco cannot activate — catches low-speed crawls that the Accelerating state alone misses. 0 disables.;{bitStringValue(velocityUnitsLabels, useMetricOnInterface)}, {useMetricOnInterface ? 1 : @@UNITS_KMH_TO_MPH@@}, 0, 0, 300, 0
	uint16_t ecoModeMaxRpm;Eco Mode: engine RPM must be at or below this for eco to engage. Exceeding it drops eco instantly, just like leaving Cruising. 0 disables the RPM gate.;"RPM", 1, 0, 0, 15000, 0

	float ecoModeEngageLockTime;Eco Mode: once eco engages, force it to stay active and ignore state/MAP/VSS/RPM changes for this long, so the torque-delivery step from eco's own AFR/timing/VVT/throttle changes doesn't get misread as leaving Cruising and drop eco right back off. Limp/Sport/Inhibit still override instantly. 0 disables the lock (instant re-evaluation, legacy behavior).;"sec", 1, 0, 0, 2, 2
	float ecoModeLuaGaugeValue;Eco Mode: Lua gauge threshold for the switch source.;"", 1, 0, -30000, 30000, 3
	float ecoTargetAfr;Eco Mode: absolute target AFR while active (leaner = more economy).;"afr", 1, 0, 10, 20, 1
	float ecoTimingAdder;Eco Mode: ignition timing added (+) or pulled (-) while active.;"deg", 1, 0, -15, 15, 1
	float ecoVvtIntakeTarget;Eco Mode: intake cam VVT target while active (when VVT override enabled).;"deg", 1, 0, -360, 360, 1
	float ecoVvtExhaustTarget;Eco Mode: exhaust cam VVT target while active (when VVT override enabled).;"deg", 1, 0, -360, 360, 1
	float ecoThrottleMult;Eco Mode: throttle target multiplier while active.;"mult", 1, 0, 0.8, 1.2, 2
	float ecoAlternatorVoltageTarget;Eco Mode: absolute alternator voltage target while active (lower = less alternator drag). 0 disables the override and uses the normal voltage target table. Requires smart alternator control.;"volts", 1, 0, 0, 30, 1

	! --- Pops and Bangs (enable bit stays in page 1) ---
	uint8_t autoscale popsAndBangsDelay;Delay after overrun starts before pops and bangs activates.;"sec", 0.1, 0, 0, 10, 1
	uint8_t autoscale popsAndBangsDuration;Duration of pops and bangs mode. 0 = indefinitely active (DFCO will never engage).;"sec", 0.1, 0, 0, 10, 1
	uint8_t popsAndBangsAirAdd;Additional idle / ETB % while pops and bangs is active.;"%", 1, 0, 0, 100, 0

	uint16_t popsAndBangsRpmHigh;Activate above this RPM.;"rpm", 1, 0, 0, 15000, 0
	uint16_t popsAndBangsRpmLow;Deactivate below this RPM.;"rpm", 1, 0, 0, 15000, 0
	uint16_t popsAndBangsRpmMax;Never activate above this RPM.;"rpm", 1, 0, 0, 15000, 0

	int16_t popsAndBangsCltMin;Do not activate below this coolant temperature (cold engine protection).;{bitStringValue(unitsLabels, useMetricOnInterface)}, {useMetricOnInterface ? 1 : 1.8}, {useMetricOnInterface ? 0 : 17.77777}, {useMetricOnInterface ? -100 : -148}, {useMetricOnInterface ? @@CLT_UPPER_LIMIT@@ : @@CLT_UPPER_LIMIT@@ * 1.8 + 32}, 0
	int16_t popsAndBangsCltMax;Do not activate above this coolant temperature (overheating protection).;{bitStringValue(unitsLabels, useMetricOnInterface)}, {useMetricOnInterface ? 1 : 1.8}, {useMetricOnInterface ? 0 : 17.77777}, {useMetricOnInterface ? -100 : -148}, {useMetricOnInterface ? @@CLT_UPPER_LIMIT@@ : @@CLT_UPPER_LIMIT@@ * 1.8 + 32}, 0

	float popsAndBangsTimingOverride;Flat ignition timing override when pops and bangs is active.;"deg", 1, 0, -60, 60, 1
	float popsAndBangsVeOverride;VE override percentage when pops and bangs is active.;"%", 1, 0, 0, 150, 0

	bit popsAndBangsRequireSportMode,"enabled","disabled";Pops and Bangs: require Sport Mode to be active for pops and bangs to activate.

	pops_and_bangs_cutout_inhibit_e popsAndBangsCutoutInhibitMode;Off ignores exhaust cutout state. Inhibit blocks pops and bangs unless the exhaust cutout is open. Requires Exhaust Cutout to be enabled.

	! --- Pops and Bangs spark cut (charge the exhaust with raw fuel, then re-light) ---
	! While P&B is active fuel keeps flowing (DFCO is inhibited); these settings periodically
	! skip spark so the unburned charge dumps into the hot exhaust and ignites on the next spark.
	bit popsAndBangsSparkCutEnabled,"enabled","disabled";P&B spark cut: periodically cut spark so raw fuel charges the exhaust, then re-light it for louder pops and bangs.
	bit popsAndBangsCutDurationAuto,"automatic","manual";P&B spark cut: pick a fresh random cut duration within 20-500ms each cycle instead of the fixed duration below.
	uint8_t popsAndBangsCutEveryRevs;P&B spark cut: open a spark-cut window once every this many crank revolutions.;"rev", 1, 0, 1, 100, 0
	uint8_t popsAndBangsCutPercent;P&B spark cut: fraction of sparks to cut while a window is open (hard cut, consecutive skips allowed so fuel can accumulate). 0 = no cut.;"%", 1, 0, 0, 100, 0
	uint16_t popsAndBangsCutDurationMs;P&B spark cut: how long each spark-cut window lasts (ignored when automatic).;"ms", 1, 0, 20, 500, 0

	! --- Clutch Delay Valve (enable/clutch-exit/smart-mode bits + solenoid pin stay in page 1) ---
	! Simple mode: CDV activates on launch/pre-launch entry. Smart mode: additionally requires
	! clutch pressure (SensorType::ClutchPressure) to be inside [cdvSmartMinPressure,
	! cdvSmartMaxPressure] before activating, and leaving that window deactivates it immediately.
	! In Smart mode cdvExitDelay is instead a max-active-duration safety timer counting from
	! when the CDV solenoid turned on (Simple mode keeps counting from launch exit).
	uint8_t autoscale cdvExitDelay;Simple mode: seconds after launch control exits before deactivating CDV solenoid (0 = deactivate immediately). Smart mode: maximum seconds the CDV solenoid may stay active before a safety timeout forces it off (0 = deactivate immediately).;"s", 0.1, 0, 0, 10, 1
	uint16_t cdvExitVss;Deactivate CDV above this vehicle speed. Set 0 to disable.;{bitStringValue(velocityUnitsLabels, useMetricOnInterface)}, {useMetricOnInterface ? 1 : @@UNITS_KMH_TO_MPH@@}, 0, 0, 300, 0
	uint16_t cdvSmartMinPressure;Smart mode: clutch pressure must be at or above this for the CDV to activate/stay active.;"kPa", 1, 0, 0, 4000, 0
	uint16_t cdvSmartMaxPressure;Smart mode: clutch pressure must be at or below this for the CDV to activate/stay active.;"kPa", 1, 0, 0, 4000, 0

	! --- Off-Idle RPM Adder ---
	int16_t offIdleRpmAdder;RPM added to closed-loop idle target when returning from off-idle (Running/Coasting) conditions. PID chases this elevated target to prevent stalling.;"RPM", 1, 0, 0, 1000, 0
	uint8_t autoscale offIdleWaitTime;Time to wait after RPM stabilizes before starting the off-idle adder decay.;"sec", 0.1, 0, 0, 10, 1
	uint8_t autoscale offIdleRpmAdderDecayTime;Time over which the off-idle RPM adder linearly decays from max to zero after the wait expires.;"sec", 0.1, 0, 0, 10, 1
	uint8_t autoscale offIdleRpmStabilityThreshold;RPM rate-of-change (RPM/s) below which RPM is considered stable when returning to idle. Transition from Stabilizing to Waiting occurs when dRPM/s falls below this value.;"RPM/s", 10, 0, 0, 2550, 0

	! --- Limiter Adders (enable bit stays in page 1) ---
	lua_gauge_e luaLimiterGaugeSelect;Lua gauge used as the limiter input axis (LuaGauge source only).
	limiter_adder_source_e limiterAdderSource;Limiter Adders: input source. LuaGauge interpolates the curves below off a Lua gauge value. Sport Mode applies a single flat adder while Sport Mode is active.

	! --- Advanced / PWM Fuel Pump (relay pins stay in page 1) ---
	fuel_pump_mode_e fuelPumpMode;Fuel pump output mode: Single relay, Dual relay with secondary activation, or PWM pressure control
	uint16_t secondaryFpActivationRpm;Secondary pump activates above this RPM (Dual mode);"rpm", 1, 0, 0, 8000, 0
	uint16_t secondaryFpActivationLoad;Secondary pump activates above this fueling load (Dual mode). In Speed Density mode this is MAP in kPa - set above 100 kPa to use boost as the trigger threshold.;"kPa", 1, 0, 0, @@MAP_UPPER_LIMIT@@, 0
	uint16_t secondaryFpRpmHysteresis;Secondary pump deactivates when RPM drops this far below activation threshold (Dual mode);"rpm", 1, 0, 0, 2000, 0
	uint16_t secondaryFpLoadHysteresis;Secondary pump deactivates when load drops this far below activation threshold (Dual mode);"kPa", 1, 0, 0, @@MAP_UPPER_LIMIT@@, 0
	uint8_t secondaryFpActivationTps;Secondary pump activates above this TPS (Dual mode);"%", 1, 0, 0, 100, 0
	uint8_t secondaryFpTpsHysteresis;Secondary pump deactivates when TPS drops this far below activation threshold (Dual mode);"%", 1, 0, 0, 50, 0
	uint16_t fuelPumpPwmFrequency;Fuel pump PWM frequency (PWM mode);"Hz", 1, 0, 10, 3000, 0
	uint8_t fuelPumpMinDuty;Minimum PWM duty - keeps pump spinning at low demand (PWM mode);"%", 1, 0, 0, 100, 0
	uint8_t fuelPumpMaxDuty;Maximum PWM duty - also held during prime (PWM mode);"%", 1, 0, 0, 100, 0
	int16_t fuelPump_iTermMin;PID integrator lower limit (PWM mode);"", 1, 0, -30000, 30000, 0
	int16_t fuelPump_iTermMax;PID integrator upper limit (PWM mode);"", 1, 0, -30000, 30000, 0

	! --- Aggressive Pressure Relief (PWM mode, returnless fuel systems) ---
	! On a returnless system the pump can only add fuel to the rail, never remove it - once
	! demand drops, excess pressure can only bleed off as the injectors consume it down, and
	! at low injected mass that happens too slowly for the PID's I-term to usefully chase
	! (it just winds down against a pump that already has no authority to help, then overshoots
	! low once pressure finally catches up). While this is enabled and injected fuel mass is
	! below fuelPumpReliefMaxInjectedMass, relief engages once pressure rises more than
	! fuelPumpReliefEngageOverpressure above target - pump duty is held at fuelPumpMinDuty
	! (bypassing PID output, PID reset) so pressure drains via consumption alone. Once engaged,
	! relief stays latched (hysteresis) until pressure falls back to within
	! fuelPumpReliefRecoverOverpressure of target, at which point normal PID control resumes.
	! fuelPumpReliefRecoverOverpressure should be set lower than fuelPumpReliefEngageOverpressure
	! (0 = resume only once pressure is back at or below target) to avoid chattering in/out of
	! relief right at the engage point.
	bit fuelPumpAggressiveRelief,"enabled","disabled";Aggressive Pressure Relief: master enable (PWM mode, intended for returnless fuel systems - see comment above).
	uint16_t fuelPumpReliefMaxInjectedMass;Aggressive Pressure Relief: only engages while injected fuel mass per cycle is below this (low consumption = pressure won't drop fast regardless of pump duty).;"mg", 1, 0, 0, 2000, 0
	uint16_t fuelPumpReliefEngageOverpressure;Aggressive Pressure Relief: pressure must exceed target by more than this to engage relief.;"kPa", 1, 0, 0, 500, 0
	uint16_t fuelPumpReliefRecoverOverpressure;Aggressive Pressure Relief: once engaged, relief stays on until pressure is back within this much of target (should be less than the engage value above).;"kPa", 1, 0, 0, 500, 0

	! --- Launch Power Ramp (Advanced) ---
	! After launch control releases at WOT (car leaves the line), retard ignition timing per the
	! curve below and ramp it back to zero over up to 5 seconds. The WOT gate reuses smWotTpsThreshold
	! (Engine SM WOT threshold) against DriverThrottleIntent. Time-based: once started it runs the curve
	! to completion regardless of throttle. Independent of the Clutch Delay Valve.
	bit launchPowerRampEnabled,"enabled","disabled";Launch Power Ramp: master enable. After a WOT launch release, removes ignition timing per the curve and ramps it back to zero over up to 5s.
	float[LAUNCH_POWER_RAMP_CURVE_SIZE] launchPowerRampTimeBins;Launch Power Ramp: elapsed time since launch release (curve X).;"s", 1, 0, 0, 5, 1
	float[LAUNCH_POWER_RAMP_CURVE_SIZE] launchPowerRampRetardValues;Launch Power Ramp: ignition timing removed at each time point (curve Y).;"deg", 1, 0, 0, 30, 1

	! --- Burst Knock (transient ignition timing pull) ---
	! Timing-side mirror of the TPS/TPS acceleration fuel enrichment. On a throttle-stab transient
	! (reuses the TPS accel-enrichment delta/threshold) this pulls ignition timing per the
	! TPS-rate(Y) x RPM(X) table, holds it for the duration of the stab, then decays the pull
	! linearly back to zero over burstKnockDecayTime. Feed-forward knock margin during tip-in.
	bit burstKnockEnabled,"enabled","disabled";Burst Knock: master enable. Pulls ignition timing on a TPS-rate transient, then decays it back to zero.
	uint8_t autoscale burstKnockDecayTime;Burst Knock: time over which the pulled timing linearly decays back to zero after the transient ends.;"s", 0.1, 0, 0, 10, 1
	float[BURST_KNOCK_RPM_SIZE] burstKnockRpmBins;Burst Knock: RPM axis (table X).;"rpm", 1, 0, 0, 15000, 0
	float[BURST_KNOCK_TPS_RATE_SIZE] burstKnockTpsRateBins;Burst Knock: TPS rate-of-change axis (table Y).;"%/s", 1, 0, 0, 30000, 0
	float[BURST_KNOCK_TPS_RATE_SIZE x BURST_KNOCK_RPM_SIZE] burstKnockRetardTable;Burst Knock: ignition timing removed (deg) at each TPS-rate x RPM cell.;"deg", 1, 0, 0, 30, 1

	! --- WOT Time Enrichment (richen target AFR after prolonged WOT) ---
	! Once the engine is held at Wide Open Throttle (Engine SM WOT state), a timer counts the
	! elapsed seconds (capped at 30 s). The curve below maps that time to an AFR adder that is
	! added to the target AFR (negative values richen). The adder resets the moment WOT ends.
	bit wotEnrichmentEnabled,"enabled","disabled";WOT Enrichment: master enable. Adds an AFR adder to the target after prolonged time at WOT.
	float[WOT_ENRICHMENT_SIZE] wotEnrichmentTimeBins;WOT Enrichment: elapsed time at WOT (curve X).;"s", 1, 0, 0, 30, 1
	float[WOT_ENRICHMENT_SIZE] wotEnrichmentAfrAdder;WOT Enrichment: AFR added to target at each time point (negative = richer) (curve Y).;"afr", 1, 0, -10, 10, 1

	! --- Sport Pedal (ETB pedal-to-throttle ratio shaping) ---
	! Electronic-throttle only. While active, the ETB throttle target is multiplied by an 8-cell
	! curve indexed by accelerator pedal position, letting the driver reshape the pedal-to-throttle
	! ratio (e.g. a more aggressive "sport" tip-in). The multiplied target is always clamped to 100%
	! so an aggressive multiplier can never command throttle over-travel. Activation mirrors the
	! Exhaust Cutout control (switch input or Sport Mode) since opening cutouts and a sportier pedal
	! feel are usually wanted together.
	sport_pedal_activation_e sportPedalActivationMode;Sport Pedal: activation source. OFF disables the feature; Switch uses a hardware switch input; Sport Mode follows the global Sport Mode flag. ETB only.

	switch_input_pin_e sportPedalSwitchPin;Sport Pedal: hardware switch input pin (Switch mode). One switch state activates sport pedal, the other deactivates it (polarity set by the pin mode below).
	pin_input_mode_e sportPedalSwitchPinMode;

	float[SPORT_PEDAL_SIZE] sportPedalPedalBins;Sport Pedal: accelerator pedal position axis (curve X).;"%", 1, 0, 0, 100, 0
	float[SPORT_PEDAL_SIZE] sportPedalMultValues;Sport Pedal: throttle target multiplier applied at each pedal position (curve Y). Result is clamped to 100%.;"mult", 1, 0, 0, 5, 2

	! --- Limiter Adders (add curves + Sport Mode single-value adders) ---
	float[LUA_LIMITER_CURVE_SIZE] luaLimiterRpmAddBins;;"value", 1, 0, -10000, 10000, 2
	float[LUA_LIMITER_CURVE_SIZE] luaLimiterRpmAdd;;"RPM", 1, 0, -10000, 10000, 0
	float[LUA_LIMITER_CURVE_SIZE] luaLimiterBoostAddBins;;"value", 1, 0, -10000, 10000, 2
	float[LUA_LIMITER_CURVE_SIZE] luaLimiterBoostAdd;;"kPa", 1, 0, -1000, 1000, 1
	float limiterAdderSportModeRpmAdd;Limiter Adders: flat RPM adder applied while Sport Mode is active (Sport Mode source only).;"RPM", 1, 0, -10000, 10000, 0
	float limiterAdderSportModeBoostAdd;Limiter Adders: flat boost (kPa) adder applied while Sport Mode is active (Sport Mode source only).;"kPa", 1, 0, -1000, 1000, 1

	! --- Engine Temperature Overlay (Engine State Machine sub-feature) ---
	! Classifies CLT into three mutually-exclusive bands published as overlay bits each slow
	! callback: engineSmIsCold (below smColdTempThreshold), engineSmIsOperating (between the
	! two thresholds), engineSmIsHot (above smHotTempThreshold). When no CLT sensor is valid
	! the engine is treated as Operating (no false Cold/Hot triggering).
	int16_t smColdTempThreshold;Engine Temperature Overlay: CLT below this is Cold engine. Between this and smHotTempThreshold is Operating temperature.;{bitStringValue(unitsLabels, useMetricOnInterface)}, {useMetricOnInterface ? 1 : 1.8}, {useMetricOnInterface ? 0 : 17.77777}, {useMetricOnInterface ? -40 : -40}, {useMetricOnInterface ? @@CLT_UPPER_LIMIT@@ : @@CLT_UPPER_LIMIT@@ * 1.8 + 32}, 0
	int16_t smHotTempThreshold;Engine Temperature Overlay: CLT above this is Hot engine. Below smColdTempThreshold is Cold, between both is Operating temperature.;{bitStringValue(unitsLabels, useMetricOnInterface)}, {useMetricOnInterface ? 1 : 1.8}, {useMetricOnInterface ? 0 : 17.77777}, {useMetricOnInterface ? -40 : -40}, {useMetricOnInterface ? @@CLT_UPPER_LIMIT@@ : @@CLT_UPPER_LIMIT@@ * 1.8 + 32}, 0

	! --- Quick Warmup (Engine State Machine sub-feature) ---
	! Active only while the SM reports Cold AND Idle simultaneously. Retards ignition timing,
	! overrides the closed-loop lambda target, and adds a feed-forward throttle offset so the
	! idle controller can hold the RPM target even when closed-loop idle is disabled. Exits
	! automatically when the SM leaves the Cold state (CLT rises above smColdTempThreshold).
	! The Idle SM state excludes cranking and the after-start stabilization window, so this
	! never fires until the engine has settled. With no valid CLT sensor the SM treats the
	! engine as Operating, so the feature stays inactive.
	bit quickWarmupEnabled,"enabled","disabled";Quick Warmup: master enable. Retards timing, richens the lambda target, and adds a throttle feed-forward at cold idle to heat the exhaust and aid catalyst light-off.
	int8_t autoscale quickWarmupEtbOffset;Quick Warmup: feed-forward throttle position (%) added to the open-loop idle target while active. Compensates for the torque loss from timing retard and a richer mixture. Applied even when closed-loop idle is disabled.;"%", 0.1, 0, -12.5, 12.5, 1
	float quickWarmupTimingRetard;Quick Warmup: ignition timing pulled while active. Use a negative value to retard (e.g. -8 deg retards timing by 8 degrees). Positive values advance timing.;"deg", 1, 0, -30, 10, 1
	float quickWarmupLambdaTarget;Quick Warmup: absolute lambda target while active. Values below 1.0 richen the mixture (e.g. 0.95 = 5 percent rich). Applied as a hard override over the normal lambda table.;"lambda", 1, 0, 0.7, 1.2, 2

	! --- Fan A/C Control Mode ---
	! This is the single switch that decides whether each radiator fan reacts to the A/C
	! compressor — there is no separate "enable for AC" elsewhere. 'Disabled' never runs the
	! fan for A/C. 'Relay' turns the fan on whenever the A/C compressor relay is active.
	! 'Pressure' (EFI_AC_PRESSURE_FAN) uses a high-side pressure sensor threshold instead: the
	! fan turns ON above fanNAcPressureOn and OFF below fanNAcPressureOff (hysteresis band
	! prevents rapid cycling). Requires SensorType::AcPressure to be wired. Pressure is the
	! command in this mode: the fan follows the sensor reading regardless of whether the A/C
	! compressor is currently engaged (eg static high-side heat soak with the clutch open).
	fan_ac_mode_e fan1AcMode;Fan 1: A/C fan control mode. 'Disabled' never runs the fan for A/C. 'Relay' turns the fan on whenever the A/C compressor is active. 'Pressure' uses the high-side pressure thresholds below, independent of compressor state, and requires an A/C pressure sensor.
	fan_ac_mode_e fan2AcMode;Fan 2: A/C fan control mode. 'Disabled' never runs the fan for A/C. 'Relay' turns the fan on whenever the A/C compressor is active. 'Pressure' uses the high-side pressure thresholds below, independent of compressor state, and requires an A/C pressure sensor.
	uint16_t fan1AcPressureOn;Fan 1: A/C high-side pressure above which fan 1 turns on (pressure mode only).;"kPa", 1, 0, 0, 4000, 0
	uint16_t fan1AcPressureOff;Fan 1: A/C high-side pressure below which fan 1 turns off (hysteresis lower bound). Must be less than fan1AcPressureOn.;"kPa", 1, 0, 0, 4000, 0
	uint16_t fan2AcPressureOn;Fan 2: A/C high-side pressure above which fan 2 turns on (pressure mode only).;"kPa", 1, 0, 0, 4000, 0
	uint16_t fan2AcPressureOff;Fan 2: A/C high-side pressure below which fan 2 turns off (hysteresis lower bound). Must be less than fan2AcPressureOn.;"kPa", 1, 0, 0, 4000, 0

	! Dwell Duty Mode moved to the main engine_configuration_s (rusefi_config.txt) when this
	! feature was ported onto master -- see ignition_state.cpp. No longer duplicated here.
	uint8_t[4] dwellDutyPad_unused;unused

	! --- Check Engine Triggering (MODULE_CHECK_ENGINE_LIGHT) ---
	! celPointsTotal sums a point for every currently-active check across the whole CheckEngineLight
	! module, not just the ones below: the TPS Circuit checks below (each worth a flat 1 point,
	! individually enabled here), Misfire Detection (misfire_detection.cpp keeps its own latch/DTC
	! path but also contributes a point here while latched), and CheckEngineLight's own
	! battery/MAP/IAT/TPS voltage-range checks (check_engine_light.cpp) -- those raise/clear their
	! DTCs immediately and unconditionally via addError()/removeError(), unrelated to
	! celPointsThreshold, but each also contributes a point here while its DTC is active. Every
	! slow-callback tick this combined total is summed and compared against the two thresholds
	! below. Reaching
	! celPointsThreshold (the lower of the two) raises the matching OBD code(s) via addError() and
	! lights the CEL solid -- the standard, less-urgent fault path. Reaching celBlinkPointsThreshold
	! (must be set higher) escalates that already-active DTC to a flashing CEL instead of the
	! normal digit-blink-out, matching OBD-II convention where a flashing MIL signals a more
	! critical, actively-damaging condition than a steady one. Set either threshold to 0 to disable
	! that stage. See check_engine_light.md.
	!
	! celDebounceTimeSec is shared by every check on this page: each check's trip condition must
	! hold continuously for this long before it trips, and be continuously clear for this long
	! before it untrips. TPS Circuit Intermittent also uses it as its flip-counting window.
	!
	! TPS Circuit Low/High (OBD_TPS1_Range_Performance) is implemented -- reuses the same TPS1
	! signal-out-of-range detection as the existing sensor_checker.cpp warning, just debounced
	! through celDebounceTimeSec and wired into addError()/celPointsTotal instead of only the
	! transient warning log. Deliberately a different OBD code than CheckEngineLight's own
	! OBD_TPS1_Primary_Low/High (raw-voltage range check on the Tps1Primary ADC channel) so the two
	! checks don't fight over the same DTC.
	! TPS Circuit Intermittent (P0124) is implemented -- trips when the TPS1 signal flips between
	! ok/fault at least tpsIntermittentFlipCount times within celDebounceTimeSec.
	!
	! Oil Pressure Low, Coolant Temp High, and AFR/Lambda Lean-or-Rich are reserved here (enable
	! bit only) but not yet evaluated -- their check-specific threshold fields will be added when
	! each is implemented. System Voltage Low/High is already implemented, but as one of
	! CheckEngineLight's always-on voltage-range checks above, not through voltageCelEnable below --
	! that bit remains reserved for a possible future check-specific variant.
	bit tpsCircuitCelEnable,"enabled","disabled";Check Engine Triggering: TPS Circuit Low/High. Detects the TPS1 signal stuck out of its expected electrical range.
	bit tpsIntermittentCelEnable,"enabled","disabled";Check Engine Triggering: TPS Circuit Intermittent (P0124). Detects the TPS1 signal repeatedly flipping in/out of range.
	bit oilPressureLowCelEnable,"enabled","disabled";Check Engine Triggering: Oil Pressure Low. Not yet implemented -- reserved.
	bit cltHighCelEnable,"enabled","disabled";Check Engine Triggering: Coolant Temp High. Not yet implemented -- reserved.
	bit afrCelEnable,"enabled","disabled";Check Engine Triggering: AFR/Lambda Lean or Rich. Not yet implemented -- reserved.
	bit voltageCelEnable,"enabled","disabled";Check Engine Triggering: reserved for a possible future check-specific System Voltage variant. CheckEngineLight's own always-on battery voltage-range check (Settings dialog) already covers this independently.

	uint8_t celPointsThreshold;Check Engine Triggering: total tripped-check points required to raise the OBD code(s) and light the CEL solid (the standard, less-urgent fault path). 0 = never trigger from points.;"points", 1, 0, 0, 100, 0
	uint8_t celBlinkPointsThreshold;Check Engine Triggering: total tripped-check points required to escalate an already-active DTC to a flashing CEL -- more critical than solid. Should be set higher than celPointsThreshold. 0 = never escalate to blink.;"points", 1, 0, 0, 100, 0
	uint8_t autoscale celDebounceTimeSec;Check Engine Triggering: shared continuous-confirm time for every check on this page (trip and untrip both require the condition to hold for this long). Also the flip-counting window for TPS Circuit Intermittent.;"s", 0.1, 0, 0, 25, 1
	uint8_t tpsIntermittentFlipCount;Check Engine Triggering -- TPS Circuit Intermittent: number of ok/fault flips within celDebounceTimeSec required to trip.;"flips", 1, 0, 2, 10, 0

	! --- Malfunction Indicator KOEO bulb check (MODULE_MIL) ---
	! Independent of Check Engine Triggering above: when enabled, the CEL output lights solid
	! while the engine is stopped (Key-On-Engine-Off), mimicking the classic OBD-II bulb-check.
	! It goes off once the engine starts, unless an active DTC or Check Engine Triggering
	! escalation takes over the output. See modules/malfunction_indicator/malfunction_indicator.cpp.
	bit celOnKoeo,"on","off";Check Engine light: light solid at Key-On-Engine-Off as a bulb check, off once the engine starts (unless a DTC is active).

	! --- Injector Small Pulse % Correction Curve (EFI_INJ_PERCENT_CURVE) ---
	! Nonlinear injector flow correction using a user-supplied pulsewidth vs. percent-adder
	! curve (as provided by Injector Dynamics and similar suppliers). The X axis is the
	! effective pulsewidth (after dead time subtraction) in ms; the Y axis is the percentage
	! to add to that effective PW. Example: at 0.25 ms effective PW with 41.6% correction,
	! the injector is commanded for 0.25 * 1.416 = 0.354 ms effective open time, then dead
	! time is added on top as normal. The last X bin acts as the cutoff: above that effective
	! PW, no correction is applied regardless of the Y value in that cell.
	float[INJ_CURVE_SIZE] injectorSmallPulseCurveBins;Injector % Correction Curve: effective pulsewidth axis (ms). The last bin is the cutoff — no correction above it.;"ms", 1, 0, 0, 10, 3
	float[INJ_CURVE_SIZE] injectorSmallPulseCurveValues;Injector % Correction Curve: percent adder at each effective PW. Example: 41.6 adds 41.6%% of the effective PW. Set all to 0 to disable while keeping the mode selected.;"%", 1, 0, -100, 500, 1

	! --- Rolling Launch Control (EFI_ROLLING_LAUNCH) ---
	! A driver-held button (hardware switch and/or the setRollingLaunchTrigger Lua call) that, while
	! the car is moving (VSS >= rollingLaunchMinVss) and above rollingLaunchMinArmRpm, snapshots the
	! current RPM at the press edge and holds the engine there via the shared hard spark limiter so
	! the turbo can be spooled. The hold ceiling is capturedRpm + rollingLaunchRpmWindow, clamped to
	! rollingLaunchMaxRpm. While held it also pulls a flat rollingLaunchTimingRetard and adds
	! rollingLaunchFuelAdderPercent fuel. On release the hold ends immediately and the pulled timing
	! decays linearly back to zero over rollingLaunchRampOutTime so boost is eased in, not slammed.
	! Requires EFI_LAUNCH_CONTROL (shares the hard spark limiter).
	bit rollingLaunchEnabled,"enabled","disabled";Rolling Launch: master enable. Holds engine RPM at a captured target while a button is held and the car is moving, to spool the turbo.

	switch_input_pin_e rollingLaunchActivatePin;Rolling Launch: hardware switch input pin. Active state (per the pin mode below) engages the hold. Also OR-ed with the setRollingLaunchTrigger Lua call.
	pin_input_mode_e rollingLaunchActivatePinMode;

	uint8_t rollingLaunchTimingRetard;Rolling Launch: flat ignition timing pulled (retarded) while the hold is active, to build boost.;"deg", 1, 0, 0, 30, 0
	uint8_t rollingLaunchFuelAdderPercent;Rolling Launch: extra fuel added (richer) while the hold is active.;"%", 1, 0, 0, 50, 0
	uint8_t autoscale rollingLaunchRampOutTime;Rolling Launch: time over which the pulled timing decays linearly back to zero after the button is released.;"s", 0.1, 0, 0, 10, 1

	uint16_t rollingLaunchRpmWindow;Rolling Launch: RPM added to the captured (press-edge) RPM to set the hold target. e.g. press at 3500 with 500 here holds at 4000.;"rpm", 1, 0, 0, 4000, 0
	uint16_t rollingLaunchMinArmRpm;Rolling Launch: minimum engine RPM required at the press edge to arm. Prevents engaging while lugging.;"rpm", 1, 0, 0, 15000, 0
	uint16_t rollingLaunchMaxRpm;Rolling Launch: absolute ceiling the captured hold target is clamped to, regardless of where the button is pressed (over-rev safety).;"rpm", 1, 0, 0, 15000, 0
	uint16_t rollingLaunchMinVss;Rolling Launch: minimum vehicle speed required to arm. This is the "rolling" gate -- below it the button does nothing.;{bitStringValue(velocityUnitsLabels, useMetricOnInterface)}, {useMetricOnInterface ? 1 : @@UNITS_KMH_TO_MPH@@}, 0, 0, 300, 0

	! --- Intake Manifold Runner Control (EFI_IMRC) ---
	! Controls solenoid-driven or H-Bridge-driven intake manifold runners based on RPM, TPS, and MAP
	! trigger conditions. In Solenoid mode, up to two solenoids are driven identically at configurable
	! PWM duty cycles for open and closed positions. In H-Bridge mode, a single H-Bridge positions
	! the runner actuator motor (same logic as Exhaust Cutout H-Bridge mode).
	! Trigger conditions are OR-ed: any one tripping causes the runner change.
	! The imrcInvert bit selects whether the runners OPEN (default) or CLOSE when triggered.
	imrc_mode_e imrcMode;Intake Manifold Runner Control mode: Disabled, Solenoid (up to 2 solenoids), or H-Bridge motor.
	bit imrcInvert,"CLOSE runners on trigger","OPEN runners on trigger";When set, runners CLOSE when trigger conditions are met (and OPEN otherwise). Default: OPEN on trigger.

	uint16_t imrcRpmThreshold;IMRC: RPM above which to trigger runner change (0 to disable);"rpm", 1, 0, 0, 20000, 0
	uint8_t imrcTpsThreshold;IMRC: TPS % above which to trigger (0 to disable);"%", 1, 0, 0, 100, 0
	uint8_t autoscale imrcSolenoidOpenDuty;IMRC Solenoid: PWM duty cycle when runners are OPEN;"%", 1, 0, 0, 100, 0
	uint8_t autoscale imrcSolenoidClosedDuty;IMRC Solenoid: PWM duty cycle when runners are CLOSED;"%", 1, 0, 0, 100, 0
	uint8_t autoscale imrcHBridgeDutyCycle;IMRC H-Bridge: motor drive duty cycle;"%", 1, 0, 0, 100, 0
	uint8_t autoscale imrcHBridgeMoveDurationS;IMRC H-Bridge: motor drive time (de-energizes after);"s", 0.1, 0, 0, 5, 1
	uint8_t imrcAlignPad;unused

	float imrcMapKpaThreshold;IMRC: MAP/Boost kPa above which to trigger (0 to disable);"kPa", 1, 0, 0, 500, 1

	output_pin_e imrcSolenoid1Pin;IMRC Solenoid: output pin for solenoid 1
	pin_output_mode_e imrcSolenoid1PinMode;

	output_pin_e imrcSolenoid2Pin;IMRC Solenoid: output pin for solenoid 2 (optional; leave unassigned to use only one solenoid)
	pin_output_mode_e imrcSolenoid2PinMode;

	output_pin_e imrcHBridgePin1;IMRC H-Bridge: IN1 pin (drives runners open)
	pin_output_mode_e imrcHBridgePin1Mode;

	output_pin_e imrcHBridgePin2;IMRC H-Bridge: IN2 pin (drives runners closed)
	pin_output_mode_e imrcHBridgePin2Mode;

	uint16_t imrcSolenoidFrequency;IMRC Solenoid: PWM frequency;"Hz", 1, 0, 1, 10000, 0
	uint16_t imrcHBridgeFrequency;IMRC H-Bridge: PWM frequency;"Hz", 1, 0, 1, 10000, 0

	! --- Ghost Cam Mode (EFI_GHOST_CAM) ---
	! Switch or Sport Mode activated idle lope effect. Only active in the Idle SM state; any other
	! state kills ghost cam immediately. VVT cam angle overrides create the overlap lope; ignition
	! and AFR are secondary. On deactivation, CLID and CLII integrators reset to zero for a clean
	! re-entry to normal idle.
	bit ghostCamEnabled,"enabled","disabled";Ghost Cam: master enable.
	bit ghostCamActivationSource,"Sport Mode","Switch";Ghost Cam: activation source. Switch = hardware switch pin; Sport Mode = follows the global Sport Mode flag. Only the selected source is checked.

	switch_input_pin_e ghostCamActivatePin;Ghost Cam: hardware switch pin. Asserting this pin while idle conditions are met engages ghost cam.
	pin_input_mode_e ghostCamActivatePinMode;

	int8_t ghostCamCltMin;Ghost Cam: minimum coolant temperature required to activate. Below this the mode cannot engage.;"°C", 1, 0, -40, 120, 0
	uint8_t autoscale ghostCamIdleBaseDuty;Ghost Cam: open-loop IAC base duty override. Replaces the CLT-table idle position while active (CLID correction still adds on top).;"%", 1, 0, 0, 100, 1

	uint16_t ghostCamIdleRpm;Ghost Cam: idle RPM target override. Fed directly to CLID and CLII as the RPM setpoint.;"rpm", 1, 0, 0, 3000, 0
	float ghostCamTargetAfr;Ghost Cam: AFR target override. STFT stays active and chases this target — rich overshoot creates the lope effect.;"AFR", 1, 0, 8, 20, 1
	float ghostCamIntakeCamAngle;Ghost Cam: VVT intake cam target angle override. The primary lope mechanism on VVT engines — cam overlap creates the choppy idle.;"deg", 1, 0, -60, 60, 1
	float ghostCamExhaustCamAngle;Ghost Cam: VVT exhaust cam target angle override.;"deg", 1, 0, -60, 60, 1

	float ghostCamTimingPid_pFactor;Ghost Cam: idle ignition timing PID proportional gain (degrees advance per rpm error).;"", 1, 0, -10000, 10000, 4
	float ghostCamTimingPid_iFactor;Ghost Cam: idle ignition timing PID integral gain.;"", 1, 0, -10000, 10000, 4
	float ghostCamTimingPid_dFactor;Ghost Cam: idle ignition timing PID derivative gain.;"", 1, 0, -10000, 10000, 4
	int16_t ghostCamTimingPid_minValue;Ghost Cam: idle ignition timing PID minimum output (max retard, degrees).;"deg", 1, 0, -30, 0, 0
	int16_t ghostCamTimingPid_maxValue;Ghost Cam: idle ignition timing PID maximum output (max advance, degrees).;"deg", 1, 0, 0, 30, 0

	! --- CLT Estimator (EFI_CHT_CLT_ESTIMATOR) ---
	! Competing-rate radiator model estimating coolant temp from CHT: CHT pulls the estimate up,
	! radiator airflow pulls it down toward the thermostat temperature. A lagged thermostat valve
	! (cubic function of CLT vs. thermostat temp, shaped by "spread" and delayed by "lag") reproduces
	! the real-world crossing/dip/recover hunting behavior around the setpoint instead of a smooth
	! monotonic approach. Coolant lag additionally delays how fast a change in airflow affects the
	! heat-rejection rate, modeling the coolant's own thermal mass/circulation delay. See
	! controllers/sensors/cht_clt_estimator.h.
	bit cltFromCht,"yes","no";Use CHT sensor to estimate CLT via a competing-rate thermal model. Disable if a real CLT sensor is wired. Formula: dCLT/dt = rHeat * (CHT - CLT) - rReject * iatFactor * valvePos * (CLT - cltEstThermostatTemp).

	int16_t cltEstThermostatTemp;CLT estimation: thermostat opening/regulation temperature. Coolant trends toward this value when radiator airflow dominates. Formula: valveTarget = clamp01(((CLT - cltEstThermostatTemp) / cltEstThermostatSpread)^3), and appears again as (CLT - cltEstThermostatTemp) in the rejection term of the main dCLT/dt equation.;"deg C", 1, 0, 40, 120, 0
	int16_t cltEstFallbackClt;Fallback CLT value used when the CHT sensor reads invalid. Formula: CLT = cltEstFallbackClt whenever CHT is invalid.;"deg C", 1, 0, -40, 200, 0
	int16_t cltEstRadiatorFailTemp;CLT estimation: CHT threshold above which the radiator is assumed to provide no cooling (boil-over / coolant loss). At or above this CHT, estimated CLT locks directly to CHT. Formula: if CHT >= cltEstRadiatorFailTemp then CLT = CHT (bypasses the ODE entirely).;"deg C", 1, 0, 40, 200, 0

	uint16_t cltEstThermostatLag;Thermostat lag (s). How long the physical thermostat valve takes to catch up to its target position. Larger values produce a more pronounced overshoot/dip/recover "hunt" around the thermostat temperature as CLT crosses it -- zero means the valve reacts instantly. Formula: valvePos += (valveTarget - valvePos) * (dt / cltEstThermostatLag).;"s", 1, 0, 0, 120, 0
	uint16_t cltEstCoolantLag;Coolant lag (s). How long a change in radiator airflow (fan on/off, ram-air) takes to actually affect the coolant's heat-rejection rate, due to the coolant's own thermal mass and circulation time. Distinct from the thermostat valve's own mechanical lag above -- zero means airflow acts on the rejection rate instantly. Formula: laggedAirflow += (airflow - laggedAirflow) * (dt / cltEstCoolantLag).;"s", 1, 0, 0, 120, 0

	float cltEstFan1Cfm;CLT estimation: airflow contributed by Fan 1 while running. PWM duty is not modeled, only relay on/off state. Formula: airflow = (fan1 relay on ? cltEstFan1Cfm : 0) + (fan2 relay on ? cltEstFan2Cfm : 0) + ramAirCfm.;"CFM", 1, 0, 0, 3000, 0
	float cltEstFan2Cfm;CLT estimation: airflow contributed by Fan 2 while running. PWM duty is not modeled, only relay on/off state. Formula: airflow = (fan1 relay on ? cltEstFan1Cfm : 0) + (fan2 relay on ? cltEstFan2Cfm : 0) + ramAirCfm.;"CFM", 1, 0, 0, 3000, 0
	float cltEstThermostatSpread;CLT estimation: thermostat valve opening spread. Degrees above the thermostat temperature over which the valve's target position goes from closed to fully open (cubic response -- barely moving near the setpoint, opening/closing rapidly away from it). Formula: valveTarget = clamp01(((CLT - cltEstThermostatTemp) / cltEstThermostatSpread)^3).;"deg C", 1, 0, 1, 60, 1

	float cltEstHeadTransferRate;CLT estimation: head-to-coolant heat-transfer rate at a reference CHT of 90 deg C. Higher means coolant trends toward CHT faster. Entered/displayed in thousandths of 1/s (e.g. 30 = 0.030 1/s) for a friendlier decimal precision. Formula: rHeat = clamp01(cltEstHeadTransferRate + cltEstHeadTransferGain * (CHT - 90)).;"x0.001 1/s", 1000, 0, 0, 1000, 1
	float cltEstHeadTransferGain;CLT estimation: how much the head-to-coolant transfer rate changes per degree C the head runs above (or below) the 90 deg C reference. Positive means a hotter head transfers heat into the coolant faster. Entered/displayed in thousandths of 1/s per C (e.g. 0.25 = 0.00025 1/s per C) for a friendlier decimal precision. Formula: rHeat = clamp01(cltEstHeadTransferRate + cltEstHeadTransferGain * (CHT - 90)).;"x0.001 1/s per C", 1000, 0, -10, 10, 2

	float cltEstRadiatorBaseRejection;CLT estimation: radiator heat-rejection rate at zero airflow (fans off, vehicle stopped) -- residual natural convection. Applied once the thermostat valve is open. Entered/displayed in thousandths of 1/s (e.g. 3.5 = 0.0035 1/s) for a friendlier decimal precision. Formula: rReject = clamp01(cltEstRadiatorBaseRejection + cltEstRadiatorAirflowGain * laggedAirflow).;"x0.001 1/s", 1000, 0, 0, 1000, 1
	float cltEstRadiatorAirflowGain;CLT estimation: how much the radiator heat-rejection rate increases per CFM of airflow through it -- effectively how big/effective the radiator is. Entered/displayed in thousandths of 1/s per CFM (e.g. 0.03 = 0.00003 1/s per CFM) for a friendlier decimal precision. Formula: rReject = clamp01(cltEstRadiatorBaseRejection + cltEstRadiatorAirflowGain * laggedAirflow).;"x0.001 1/s per CFM", 1000, 0, 0, 1, 2

	float cltEstVssMaxAirflow;CLT estimation: radiator ram-air airflow approached at high vehicle speed (the saturation point of the ram-air effect). Formula: ramAirCfm = cltEstVssMaxAirflow * (1 - exp(-VSS * ln(2) / cltEstVssHalfFlowSpeed)).;"CFM", 1, 0, 0, 3000, 0
	float cltEstVssHalfFlowSpeed;CLT estimation: vehicle speed at which ram-air airflow reaches half of cltEstVssMaxAirflow. Lower means ram-air builds up faster with speed. Formula: ramAirCfm = cltEstVssMaxAirflow * (1 - exp(-VSS * ln(2) / cltEstVssHalfFlowSpeed)).;"kph", 1, 0, 0, 400, 0

	int16_t cltEstRadiatorReferenceTemp;CLT estimation: intake/ambient air temp at which radiator effectiveness is defined as 100% (multiplier = 1.0). Set this to whatever air temp you consider "typical" -- the gain below then scales effectiveness up/down from there. Formula: iatFactor = clamp(0, 1 + cltEstRadiatorEffectivenessIatGain * (IAT - cltEstRadiatorReferenceTemp), 4).;"deg C", 1, 0, -40, 60, 0
	float cltEstRadiatorEffectivenessIatGain;CLT estimation: how much radiator effectiveness changes per degree C the intake/ambient air runs above (or below) the reference temp. Negative means hotter incoming air makes the radiator less effective. Entered/displayed as a percent per C (e.g. -2.5 = -0.025 ratio per C) for a friendlier decimal precision. Formula: iatFactor = clamp(0, 1 + cltEstRadiatorEffectivenessIatGain * (IAT - cltEstRadiatorReferenceTemp), 4).;"% per C", 100, 0, -10, 10, 2

	! --- Weighted Engine Oil Life Monitor (EFI_OIL_LIFE_MONITOR) ---
	! Tracks a weighted revolution counter (engine cycles x temperature-zone multiplier).
	! Primary source is user-selectable (oilLifePrimarySource); the other source is used
	! whenever the selected one is invalid. Either may be a real sensor or an estimated value
	! (EOT/CLT-from-CHT) transparently published under the same sensor type -- coolant-tier
	! multipliers are harsher since coolant under-represents true oil stress.
	! Zone thresholds (70/105/125 C) are FIXED in firmware; only the multipliers are tunable.
	! oilLifePercent = clamp(0,100, (1 - weightedRevs / (oilLifeRevsScaleMillions * 1e6)) * 100).
	! Persisted to flash ONLY on ignition-off (needs EFI_MAIN_RELAY_CONTROL); never during a run.
	bit oilLifeMonitorEnabled,"enabled","disabled";Oil Life Monitor: master enable.

	oil_life_temp_source_e oilLifePrimarySource;Oil Life Monitor: primary temperature source. Falls back to the other sensor if the selected one is invalid.

	uint8_t oilLifeRevsScaleMillions;Oil Life Monitor: millions of weighted revolutions for 0% oil life (e.g. 6 = 6,000,000 revs).;"M revs", 1, 0, 1, 100, 0

	float oilLifeMultOilCold;Oil Life Monitor: multiplier, oil temp below 70C (cold).;"x", 1, 0, 0.1, 10, 2
	float oilLifeMultOilOptimal;Oil Life Monitor: multiplier, oil temp 70-105C (optimal).;"x", 1, 0, 0.1, 10, 2
	float oilLifeMultOilHighHeat;Oil Life Monitor: multiplier, oil temp 105-125C (high heat).;"x", 1, 0, 0.1, 10, 2
	float oilLifeMultOilExtreme;Oil Life Monitor: multiplier, oil temp above 125C (extreme).;"x", 1, 0, 0.1, 10, 2
	float oilLifeMultCoolantCold;Oil Life Monitor: coolant-fallback multiplier, below 70C.;"x", 1, 0, 0.1, 10, 2
	float oilLifeMultCoolantOptimal;Oil Life Monitor: coolant-fallback multiplier, 70-105C.;"x", 1, 0, 0.1, 10, 2
	float oilLifeMultCoolantHighHeat;Oil Life Monitor: coolant-fallback multiplier, 105-125C.;"x", 1, 0, 0.1, 10, 2
	float oilLifeMultCoolantExtreme;Oil Life Monitor: coolant-fallback multiplier, above 125C.;"x", 1, 0, 0.1, 10, 2

	! --- VVT Advanced Mode ---
	! Opt-in replacement for both the fixed PID "offset" (relabeled "Hold Duty" in the VVT PID
	! dialogs, never used while Advanced Mode is enabled) AND the fixed PID "P factor" (also never
	! used while Advanced Mode is enabled). The feedforward baseline is a base duty vs. oil pressure
	! curve -- oil pressure is what actually moves the cam, so duty should track it directly rather
	! than being scaled by a separate multiplier. With no oil pressure sensor configured, the curve
	! is evaluated at 0 kPa (its leftmost bin). On top of the feedforward, the P+I+D trim runs with
	! a gain-scheduled P factor -- looked up from a distance-from-target curve every cycle, instead
	! of the fixed pid_s.pFactor -- so correction strength can be shaped by how far off target the
	! cam currently is; I and D still use the fixed auxPid iFactor/dFactor. The distance axis
	! includes an explicit zero bin so both curves interpolate smoothly through the target rather
	! than jumping across a gap. The P+I+D trim always runs on top of the feedforward -- if I trim
	! isn't wanted, set the fixed auxPid iFactor to 0.
	bit vvtAdvancedModeEnabled,"enabled","disabled";VVT Advanced Mode: master enable. Replaces the fixed PID offset (Hold Duty) with an oil-pressure-based base duty curve, and the fixed PID P factor with a distance-from-target P factor curve.

	float[VVT_ADV_DISTANCE_SIZE] vvtAdvDistanceBinsIntake;VVT Advanced Mode: intake distance-from-target axis (curve X), shared by the P factor curve below.;"deg", 1, 0, -40, 40, 0
	float[VVT_ADV_DISTANCE_SIZE] vvtAdvPFactorIntake;VVT Advanced Mode: intake PID P factor at each distance from target (curve Y). Replaces the fixed Intake PID "P factor" field. Entered/displayed x100 for friendlier decimal precision (e.g. 100 = 1.000 actual P factor, 0.1 = 0.001 actual).;"x100", 100, 0, -1000, 1000, 1
	float[VVT_ADV_OILP_SIZE] vvtAdvOilPressureBinsIntake;VVT Advanced Mode: intake oil pressure axis (curve X), shared by the base duty curve below.;"kPa", 1, 0, 0, 1000, 0
	float[VVT_ADV_OILP_SIZE] vvtAdvDutyIntake;VVT Advanced Mode: intake base duty cycle at each oil pressure (curve Y). Evaluated at 0 kPa if no oil pressure sensor is configured.;"%", 1, 0, -100, 100, 1

	float[VVT_ADV_DISTANCE_SIZE] vvtAdvDistanceBinsExhaust;VVT Advanced Mode: exhaust distance-from-target axis (curve X), shared by the P factor curve below.;"deg", 1, 0, -40, 40, 0
	float[VVT_ADV_DISTANCE_SIZE] vvtAdvPFactorExhaust;VVT Advanced Mode: exhaust PID P factor at each distance from target (curve Y). Replaces the fixed Exhaust PID "P factor" field. Entered/displayed x100 for friendlier decimal precision (e.g. 100 = 1.000 actual P factor, 0.1 = 0.001 actual).;"x100", 100, 0, -1000, 1000, 1
	float[VVT_ADV_OILP_SIZE] vvtAdvOilPressureBinsExhaust;VVT Advanced Mode: exhaust oil pressure axis (curve X), shared by the base duty curve below.;"kPa", 1, 0, 0, 1000, 0
	float[VVT_ADV_OILP_SIZE] vvtAdvDutyExhaust;VVT Advanced Mode: exhaust base duty cycle at each oil pressure (curve Y). Evaluated at 0 kPa if no oil pressure sensor is configured.;"%", 1, 0, -100, 100, 1

	! --- Wheel Speed Sensors (Main Speed Sensor source, Output Shaft Speed, Front/Rear Axle,
	! configurable Wheel Slip Ratio source) ---
	! Main Speed Sensor Source picks which of the three feeds SensorType::VehicleSpeed, replacing
	! the Speed Sensor dialog's pin/CAN choice for boards using this feature (see the "Main Speed
	! Sensor" dialog). Output Shaft Speed measures the transmission output shaft directly (pre-
	! differential) -- Gear Detection uses its RPM directly with no math when it's configured.
	! Front/Rear Axle and Output Shaft Speed each independently choose Physical Pin (own tooth
	! count/filter, plus a per-axle Wheel Revs/km for Front/Rear) or CAN/Lua (no pin config --
	! Sensor.new("WheelSpeedFront"):set(value) etc, typically fed from a CAN wheel-speed decode
	! done in a Lua script). The plausibility/glitch-rejection filter is shared: OSS, Front-
	! physical and Rear-physical each run their own filter instance, but all read the one
	! wheelSpeedMaxAccelPercent threshold below (expressed as %/sec of the current reading so the
	! same number is meaningful for both RPM and km/h). Wheel Slip Ratio can be computed from any
	! pair of the speed channels below instead of the fixed CAN-vendor or Aux-Speed-based calcs.
	main_speed_sensor_source_e mainSpeedSensorSource;Main Speed Sensor: which sensor feeds Vehicle Speed.

	uint8_t wheelSpeedMaxAccelPercent;Wheel Speed Sensors: shared glitch-rejection filter -- reject a reading implying more than this %/sec change, and dead-reckon from the last known rate instead. One shared threshold used independently by Output Shaft Speed, Front Axle (Physical Pin) and Rear Axle (Physical Pin). 0 disables.;"%/sec", 1, 0, 0, 200, 0

	wheel_speed_sensor_mode_e ossMode;Output Shaft Speed: input mode.
	switch_input_pin_e outputShaftSpeedSensorPin;Output Shaft Speed: hardware pulse input pin (e.g. a transmission-mounted hall sensor). Physical Pin mode only.
	uint8_t outputShaftSpeedSensorTeeth;Output Shaft Speed: number of sensor pulses per output-shaft revolution. Physical Pin mode only.;"", 1, 0, 1, 255, 0
	uint8_t ossFilterReciprocal;Output Shaft Speed: low-pass filter reciprocal (higher = more filtering, averaged over more teeth). Physical Pin mode only.;"", 1, 0, 3, 200, 0
	float ossRevPerKm;Output Shaft Speed: wheel revolutions per kilometer, used to convert OSS RPM into Vehicle Speed. Only used when Main Speed Sensor (Setup -> Vehicle Information) is set to Output Shaft Speed.;"revs/km", 1, 0, 100, 1000, 1

	wheel_speed_sensor_mode_e wheelSpeedFrontMode;Front Axle Speed: input mode.
	switch_input_pin_e wheelSpeedFrontPin;Front Axle Speed: hardware pulse input pin. Physical Pin mode only.
	uint8_t wheelSpeedFrontTeeth;Front Axle Speed: number of sensor pulses per wheel revolution. Physical Pin mode only.;"", 1, 0, 1, 255, 0
	uint8_t wheelSpeedFrontFilterReciprocal;Front Axle Speed: low-pass filter reciprocal. Physical Pin mode only.;"", 1, 0, 3, 200, 0
	float wheelSpeedFrontRevPerKm;Front Axle Speed: wheel revolutions per kilometer (tire size). Physical Pin mode only -- CAN/Lua mode feeds an already-final km/h value directly.;"revs/km", 1, 0, 100, 1000, 1

	wheel_speed_sensor_mode_e wheelSpeedRearMode;Rear Axle Speed: input mode.
	switch_input_pin_e wheelSpeedRearPin;Rear Axle Speed: hardware pulse input pin. Physical Pin mode only.
	uint8_t wheelSpeedRearTeeth;Rear Axle Speed: number of sensor pulses per wheel revolution. Physical Pin mode only.;"", 1, 0, 1, 255, 0
	uint8_t wheelSpeedRearFilterReciprocal;Rear Axle Speed: low-pass filter reciprocal. Physical Pin mode only.;"", 1, 0, 3, 200, 0
	float wheelSpeedRearRevPerKm;Rear Axle Speed: wheel revolutions per kilometer (tire size). Physical Pin mode only -- CAN/Lua mode feeds an already-final km/h value directly.;"revs/km", 1, 0, 100, 1000, 1

	wheel_speed_source_e wheelSlipRatioSource1;Wheel Slip Ratio: numerator source (e.g. Front Axle).
	wheel_speed_source_e wheelSlipRatioSource2;Wheel Slip Ratio: denominator source (e.g. Rear Axle).

end_struct
