ElDominio/rusefi/firmware/integration/LiveData.yaml

#
# see live_data.cpp - you would have to add a method manually!
#
# Here we facilitate monitoring by exposing model/transfer object of each individual controller. While some entries are only
# useful for monitoring the big idea is to bring calculation and monitoring as close to each other as possible by exposing
# many calculation fields directly
#
# here we have LiveData configuration file
# entry format, where 'key' is a unique ID:
# key: [NameOfJavaToGenerate.java, folder_where_key.txt_is located, (optional advanced options)]
# Naming convention: top level struct in .txt file should be called key_s
#
# technical debt: see docs_enums.mk where all the .txt files should be mentioned as well :(
#
Usages:
#  output_channels always goes first at least because it has protocol version at well-known offset
  - name: output_channels
    cppFileName: status_loop
    java: TsOutputs.java
    folder: console/binary
    prepend: integration/rusefi_config_shared.txt
    constexpr: "engine->outputChannels"

  - name: fuel_computer
    java: FuelComputer.java
    folder: controllers/algo/fuel
    prepend: integration/rusefi_config_shared.txt
    constexpr: "engine->fuelComputer"
    conditional_compilation: "EFI_ENGINE_CONTROL"

  - name: ignition_state
    folder: controllers/algo/ignition
    java: IgnitionState.java
    prepend: integration/rusefi_config_shared.txt
    constexpr: "engine->ignitionState"

  - name: knock_controller
    java: KnockController.java
    folder: controllers/engine_cycle
    prepend: integration/rusefi_config_shared.txt
    output_name: knock
    constexpr: "engine->module<KnockController>()"
    isPtr: true

  - name: prime_injection
    cppFileName: prime_injection
    java: PrimeController.java
    folder: controllers/engine_cycle
    prepend: integration/rusefi_config_shared.txt
    constexpr: "engine->module<PrimeController>()"
    isPtr: true

  - name: tcu_controller
    java: TcuController.java
    folder: controllers/tcu
    prepend: integration/rusefi_config_shared.txt
    conditional_compilation: "EFI_TCU"

  - name: throttle_model
    java: ThrottleModel.java
    folder: controllers/math
    output_name: throttle_model

  - name: high_pressure_fuel_pump
    java: HighPressureFuelPump.java
    folder: controllers/engine_cycle
    output_name: hpfp

  - name: injector_model
    java: InjectorModel.java
    folder: controllers/algo/fuel
    prepend: integration/rusefi_config_shared.txt
    constexpr: "engine->module<InjectorModelPrimary>()"
    isPtr: true
    # working around unmock() in simulator
    conditional_compilation: "EFI_PROD_CODE && EFI_IDLE_CONTROL"

  - name: launch_control_state
    cppFileName: launch_control
    java: LaunchControl.java
    folder: controllers/algo
    constexpr: "engine->launchController"
    conditional_compilation: "EFI_LAUNCH_CONTROL"

  - name: shift_torque_reduction_state
    cppFileName: shift_torque_reduction_controller
    java: ShiftTorqueReductionController.java
    folder: controllers/algo
    constexpr: "engine->shiftTorqueReductionController"
    conditional_compilation: "EFI_LAUNCH_CONTROL"

  - name: antilag_system_state
    cppFileName: antilag_system
    java: AntilagSystem.java
    folder: controllers/algo
    prepend: integration/rusefi_config_shared.txt
    output_name: als
    conditional_compilation: "FULL_SD_LOGS"

  - name: boost_control
    java: BoostControl.java
    folder: controllers/actuators
    prepend: integration/rusefi_config_shared.txt
    output_name: boost
    constexpr: "engine->module<BoostController>()"
    isPtr: true
    conditional_compilation: "EFI_ENGINE_CONTROL && EFI_BOOST_CONTROL"

  - name: ac_control
    java: AcControl.java
    folder: controllers/actuators
    prepend: integration/rusefi_config_shared.txt
    output_name: ac
    engineModule: AcController
    conditional_compilation: "FULL_SD_LOGS"

  - name: nitrous_control_state
    java: NitrousControl.java
    folder: controllers/algo
    prepend: integration/rusefi_config_shared.txt
    output_name: nitrous
    engineModule: NitrousController
    conditional_compilation: "EFI_ENGINE_CONTROL && EFI_LAUNCH_CONTROL"

  - name: fan_control
    java: FanControl.java
    folder: controllers/modules/fan_control
    output_name: [ "fan1", "fan2" ]
    constexpr: ["engine->module<FanControl1>()", "engine->module<FanControl2>()"]
    isPtr: true

  - name: fuel_pump_control
    cppFileName: fuel_pump
    java: FuelPump.java
    folder: controllers/modules/fuel_pump
    output_name: fuelPump
    engineModule: FuelPumpController

  - name: main_relay
    java: MainRelay.java
    folder: controllers/actuators
    output_name: mainRelay

  - name: exhaust_cutout
    java: ExhaustCutout.java
    folder: controllers/actuators
    prepend: integration/rusefi_config_shared.txt
    output_name: exhaustCutout
    engineModule: ExhaustCutoutController

  - name: imrc_controller
    java: ImrcController.java
    folder: controllers/actuators
    output_name: imrcController
    engineModule: ImrcController

  #todo: handle ETB pid and Idle pid which point at same pid_state.txt
  # - name: pid_state
  #   java: PidState.java
  #   folder: util/math

  - name: engine_state
    cppFileName: engine
    java: EngineState.java
    folder: controllers/algo
    prepend: integration/rusefi_config_shared.txt
    constexpr: "engine->engineState"

  - name: tps_accel_state
    cppFileName: accel_enrichment
    java: TpsAccelState.java
    folder: controllers/algo
    prepend: integration/rusefi_config_shared.txt

  - name: trigger_central
    java: TriggerCentral.java
    folder: controllers/trigger
    prepend: integration/rusefi_config_shared.txt
    constexpr: "engine->triggerCentral"
    conditional_compilation: "EFI_SHAFT_POSITION_INPUT"

  - name: trigger_state
    cppFileName: trigger_decoder
    java: TriggerState.java
    folder: controllers/trigger
    prepend: integration/rusefi_config_shared.txt
    conditional_compilation: "EFI_SHAFT_POSITION_INPUT && FULL_SD_LOGS"
    output_name: [ "trg", "vvt1i", "vvt1e", "vvt2i", "vvt2e" ]
    constexpr: [ "engine->triggerCentral.triggerState", "engine->triggerCentral.vvtState[0][0]","engine->triggerCentral.vvtState[0][1]","engine->triggerCentral.vvtState[1][0]","engine->triggerCentral.vvtState[1][1]"]

  - name: trigger_state_primary
    cppFileName: trigger_decoder
    java: TriggerStatePrimary.java
    folder: controllers/trigger
    prepend: integration/rusefi_config_shared.txt
    constexpr: [ "static_cast<trigger_state_primary_s&>(engine->triggerCentral.triggerState)" ]
    conditional_compilation: "EFI_SHAFT_POSITION_INPUT"

  - name: wall_fuel_state
    cppFileName: wall_fuel
    java: WallFuelState.java
    folder: controllers/algo

  - name: closed_loop_idle
    cppFileName: closed_loop_idle
    java: closed_loop_idle.java
    folder: controllers/math

  - name: live_data_example
    cppFileName: live_data_example
    java: live_data_example.java
    folder: controllers/modules/example_module

  - name: idle_state
    cppFileName: idle_thread
    java: IdleState.java
    folder: controllers/actuators
    prepend: integration/rusefi_config_shared.txt
    constexpr: "engine->module<IdleController>().unmock()"
    output_name: idle
# working around unmock() in simulator
    conditional_compilation: "EFI_PROD_CODE && EFI_IDLE_CONTROL"

  - name: electronic_throttle
    java: ElectronicThrottle.java
    folder: controllers/actuators
    prepend: integration/rusefi_config_shared.txt
    output_name: [ "etb1", "etb2" ]
    additional_headers: [ "electronic_throttle_impl.h" ]
    constexpr: ["getLiveDataConstexpr<electronic_throttle_s, 0>()", "getLiveDataConstexpr<electronic_throttle_s, 1>()"]
    isPtr: true
    conditional_compilation: "EFI_PROD_CODE && EFI_ELECTRONIC_THROTTLE_BODY && FULL_SD_LOGS"

  - name: wideband_state
    cppFileName: AemXSeriesLambda
    java: WidebandController.java
    folder: controllers/sensors/
    output_name: [ "wb1", "wb2" ]

  - name: dc_motors
    java: DcMotors.java
    folder: controllers/actuators
    prepend: integration/rusefi_config_shared.txt
    constexpr: "engine->dc_motors"

  - name: sent_state
    cppFileName: sent
    java: SentState.java
    folder: controllers/sensors
    prepend: integration/rusefi_config_shared.txt

  - name: vvt
    java: VvtState.java
    folder: controllers/actuators
    constexpr: "engine->module<VvtController1>()"
    isPtr: true
    conditional_compilation: "EFI_VVT_PID"

  - name: lambda_monitor
    java: LambdaMonitor.java
    folder: controllers/math
    constexpr: "engine->lambdaMonitor"
    conditional_compilation: "EFI_ENGINE_CONTROL && EFI_SHAFT_POSITION_INPUT"

  - name: mc33810_state
    cppFileName: mc33810
    java: Mc33810State.java
    folder: hw_layer/drivers/gpio/
    prepend: integration/rusefi_config_shared.txt
    constexpr: "mc33810getLiveData(0)"
    isPtr: true
    conditional_compilation: "EFI_PROD_CODE && (BOARD_MC33810_COUNT > 0)"

  - name: long_term_fuel_trim_state
    cppFileName: long_term_fuel_trim
    java: LongTermFuelTrim.java
    folder: controllers
    prepend: integration/rusefi_config_shared.txt

  - name: short_term_fuel_trim_state
    cppFileName: short_term_fuel_trim
    java: ShortTermFuelTrim.java
    folder: controllers/math
    prepend: integration/rusefi_config_shared.txt

  - name: vvl_controller_state
    java: VvlController.java
    folder: controllers/modules/vvl_controller
    prepend: integration/rusefi_config_shared.txt
    output_name: vvl
    engineModule: VvlController
    conditional_compilation: "MODULE_VVL_CONTROLLER"

  - name: cdv_controller_state
    java: CdvController.java
    folder: controllers/modules/cdv_controller
    prepend: integration/rusefi_config_shared.txt
    output_name: cdv
    engineModule: CdvController
    conditional_compilation: "MODULE_CDV_CONTROLLER"

  - name: launch_power_ramp_state
    java: LaunchPowerRamp.java
    folder: controllers/modules/launch_power_ramp
    prepend: integration/rusefi_config_shared.txt
    output_name: launch_power_ramp
    engineModule: LaunchPowerRamp
    conditional_compilation: "EFI_LAUNCH_POWER_RAMP"

  - name: rolling_launch_state
    java: RollingLaunch.java
    folder: controllers/modules/rolling_launch
    prepend: integration/rusefi_config_shared.txt
    output_name: rolling_launch
    engineModule: RollingLaunchControl
    conditional_compilation: "EFI_ROLLING_LAUNCH"

  - name: burst_knock_state
    java: BurstKnock.java
    folder: controllers/modules/burst_knock
    prepend: integration/rusefi_config_shared.txt
    output_name: burst_knock
    engineModule: BurstKnock
    conditional_compilation: "EFI_BURST_KNOCK"

  - name: wot_enrichment_state
    java: WotEnrichment.java
    folder: controllers/modules/wot_enrichment
    prepend: integration/rusefi_config_shared.txt
    output_name: wot_enrichment
    engineModule: WotEnrichment
    conditional_compilation: "EFI_WOT_ENRICHMENT"

  - name: check_engine_light_state
    java: CheckEngineTriggering.java
    folder: controllers/modules/check_engine_light
    prepend: integration/rusefi_config_shared.txt
    output_name: check_engine_light
    engineModule: CheckEngineTriggering
    conditional_compilation: "EFI_CHECK_ENGINE_TRIGGERING"

  - name: live_data_rotational_idle
    java: RotationalIdle.java
    folder: controllers/engine_cycle
    prepend: integration/rusefi_config_shared.txt
    output_name: live_data_rotational_idle
    conditional_compilation: "ROTATIONAL_IDLE_CONTROLLER"

  - name: engine_state_machine_state
    java: EngineStateMachine.java
    folder: controllers/algo
    prepend: integration/rusefi_config_shared.txt
    output_name: esm
    engineModule: EngineStateMachine

  - name: misfire_detection_state
    java: MisfireDetection.java
    folder: controllers/algo
    prepend: integration/rusefi_config_shared.txt
    output_name: misfire
    engineModule: MisfireController
    conditional_compilation: "EFI_ENGINE_CONTROL && EFI_MISFIRE_DETECTION"

  - name: downshift_blipper_state
    java: DownshiftBlipper.java
    folder: controllers/actuators
    prepend: integration/rusefi_config_shared.txt
    output_name: dsb
    engineModule: DownshiftBlipper
    conditional_compilation: "EFI_ELECTRONIC_THROTTLE_BODY"

  - name: upshift_rpm_hold_state
    java: UpshiftRpmHold.java
    folder: controllers/actuators
    prepend: integration/rusefi_config_shared.txt
    output_name: ush
    engineModule: UpshiftRpmHold
    conditional_compilation: "EFI_ELECTRONIC_THROTTLE_BODY"

  - name: dfco_state
    java: DfcoState.java
    folder: controllers/algo/fuel
    prepend: integration/rusefi_config_shared.txt
    output_name: dfco
    engineModule: DfcoController
