ElDominio/rusefi/firmware/controllers/algo/ignition/ignition_state.cpp

/**
 * @file ignition_state.cpp
 *
 * @date Mar 27, 2013
 * @author Andrey Belomutskiy, (c) 2012-2020
 *
 * This file is part of rusEfi - see http://rusefi.com
 *
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
 * You should have received a copy of the GNU General Public License along with this program.
 * If not, see <http://www.gnu.org/licenses/>.
 */

#include "pch.h"
#include "custom_page.h"

#include "idle_thread.h"
#include "launch_control.h"
#include "gppwm_channel.h"
#include "dfco.h"
#include "engine_state_machine.h"
#include "spark_logic.h"
#include "engine_math.h"

#if EFI_ENGINE_CONTROL
#if EFI_SHAFT_POSITION_INPUT

/**
 * @return ignition timing angle advance before TDC
 */
angle_t getRunningAdvance(float rpm, float engineLoad) {
	if (std::isnan(engineLoad)) {
		warning(ObdCode::CUSTOM_NAN_ENGINE_LOAD, "NaN engine load");
		return NAN;
	}

	efiAssert(ObdCode::CUSTOM_ERR_ASSERT, !std::isnan(engineLoad), "invalid el", NAN);

	// compute base ignition angle from main table
	float advanceAngle = IgnitionState::getInterpolatedIgnitionAngle(rpm, engineLoad);

#if EFI_PROD_CODE || EFI_UNIT_TEST
	bool secondIgnitionTableActive = false;

	const bool ignPinActive = isBrainPinValid(secondTablesGetState()->secondIgnitionTableInput) &&
		efiReadPin(secondTablesGetState()->secondIgnitionTableInput, secondTablesGetState()->secondIgnitionTableInputMode);

	if (ignPinActive) {
		// Hard switch: pin overrides everything, replace ignition table entirely
		advanceAngle = interpolate3d(
			secondTablesGetState()->secondIgnitionTable,
			secondTablesGetState()->secondIgnitionLoadBins, engineLoad,
			secondTablesGetState()->secondIgnitionRpmBins, rpm
		);
		secondIgnitionTableActive = true;
	} else {
		auto result = calculateBlend(
			secondTablesGetState()->secondIgnitionBlendParameter,
			secondTablesGetState()->secondIgnitionBlendBins, secondTablesGetState()->secondIgnitionBlendValues,
			secondTablesGetState()->secondIgnitionTable,
			secondTablesGetState()->secondIgnitionLoadBins, engineLoad,
			secondTablesGetState()->secondIgnitionRpmBins, rpm
		);
		if (result.Bias > 0) {
			advanceAngle = interpolateClamped(0, advanceAngle, 100, result.Value, result.Bias);
			secondIgnitionTableActive = true;
		}
		engine->outputChannels.secondIgnitionBlendParameter = result.BlendParameter;
		engine->outputChannels.secondIgnitionBlendBias = result.Bias;
	}
	engine->engineState.isSecondIgnitionTableActive = secondIgnitionTableActive;
#endif // EFI_PROD_CODE || EFI_UNIT_TEST

  engine->ignitionState.tractionAdvanceDrop = engine->tractionController.getAppliedTimingDrop();
  engine->engineState.tractionControlSparkSkip = engine->tractionController.getAppliedSparkSkip();
  engine->engineState.updateSparkSkip();

  advanceAngle += engine->ignitionState.tractionAdvanceDrop;

#if EFI_ANTILAG_SYSTEM
	if (engine->antilagController.isAntilagCondition) {
		float throttleIntent = Sensor::getOrZero(SensorType::DriverThrottleIntent);
		engine->antilagController.timingALSCorrection = interpolate3d(
			config->ALSTimingRetardTable,
			config->alsIgnRetardLoadBins, throttleIntent,
			config->alsIgnRetardrpmBins, rpm
		);
		advanceAngle += engine->antilagController.timingALSCorrection;
	}
#endif /* EFI_ANTILAG_SYSTEM */

	// Add any adjustments if configured
	for (size_t i = 0; i < efi::size(config->ignBlends); i++) {
		auto result = calculateBlend(config->ignBlends[i], rpm, engineLoad);

		engine->outputChannels.ignBlendParameter[i] = result.BlendParameter;
		engine->outputChannels.ignBlendBias[i] = result.Bias;
		engine->outputChannels.ignBlendOutput[i] = result.Value;
		engine->outputChannels.ignBlendYAxis[i] = result.TableYAxis;

		advanceAngle += result.Value;
	}

	// get advance from the separate table for Idle
#if EFI_IDLE_CONTROL
	if (engineConfiguration->useSeparateAdvanceForIdle &&
		(engine->module<IdleController>()->isIdlingOrTaper() || engine->module<IdleController>()->isCoastingAdvance())) {
		float idleAdvance = interpolate2d(rpm, config->idleAdvanceBins, config->idleAdvance);

		auto tps = Sensor::get(SensorType::DriverThrottleIntent);
		if (tps) {
			// interpolate between idle table and normal (running) table using TPS threshold
			// 0 TPS -> idle table
			// 1/2 threshold -> idle table
			// idle threshold -> normal table
			float idleThreshold = engineConfiguration->idlePidDeactivationTpsThreshold;
			advanceAngle = interpolateClamped(idleThreshold / 2, idleAdvance, idleThreshold, advanceAngle, tps.Value);
		}
	}
#endif

#if EFI_IDLE_CONTROL
	// reset ignition table dot, see #8198
	if(engineConfiguration->useSeparateAdvanceForIdle && engine->module<IdleController>()->isIdlingOrTaper()){
		engine->ignitionState.rpmForIgnitionIdleTableDot = rpm;
		engine->ignitionState.rpmForIgnitionTableDot = -1;
		engine->ignitionState.loadForIgnitionTableDot = -1;
	} else {
		engine->ignitionState.rpmForIgnitionIdleTableDot = -1;
		engine->ignitionState.rpmForIgnitionTableDot = rpm;
		engine->ignitionState.loadForIgnitionTableDot = engineLoad;
	}
#endif

#if EFI_LAUNCH_CONTROL
	if (engineConfiguration->launchControlEnabled && engineConfiguration->enableLaunchRetard) {
		const float launchAngle = engineConfiguration->launchTimingRetard;
		if (engine->launchController.isPreLaunchCondition) {
			const int launchRpm = engineConfiguration->launchRpm;
			const int smoothRetardStartRpm = (launchRpm - engineConfiguration->launchRpmWindow);
			const int smoothRetardEndRpm = (launchRpm - engineConfiguration->launchCorrectionsEndRpm);
			if (smoothRetardStartRpm <= rpm) {
				if (engineConfiguration->launchSmoothRetard && (rpm <= smoothRetardEndRpm)) {
					// https://github.com/rusefi/rusefi/issues/5611#issuecomment-2130431696
					return interpolateClamped(smoothRetardStartRpm, advanceAngle, smoothRetardEndRpm, launchAngle, rpm);
				} else {
					return launchAngle;
				}
			}
		} else if (engine->launchController.isLaunchCondition) {
			return launchAngle;
		}
	}
	if (engineConfiguration->torqueReductionEnabled
		&& engine->shiftTorqueReductionController.isFlatShiftConditionSatisfied
	) {
		return engine->shiftTorqueReductionController.getTorqueReductionIgnitionRetard();
	}
    if (engineConfiguration->nitrousControlEnabled && engine->module<NitrousController>()->isNitrousCondition) {
        advanceAngle -= engineConfiguration->nitrousIgnitionRetard;
    }
#endif /* EFI_LAUNCH_CONTROL */

#ifdef MODULE_VVL_CONTROLLER
	advanceAngle += engine->module<VvlController>().unmock().getTimingModifier();
#endif /* MODULE_VVL_CONTROLLER */

	return advanceAngle;
}

angle_t getCltTimingCorrection(float engineLoad) {
	const auto clt = Sensor::get(SensorType::Clt);

	if (!clt)
		return 0; // this error should be already reported somewhere else, let's just handle it

	return interpolate3d(
			config->ignitionCltCorrTable,
			config->ignitionCltCorrLoadBins, engineLoad,
			config->ignitionCltCorrTempBins, clt.Value
	);
}

void IgnitionState::updateAdvanceCorrections(float engineLoad) {
	cltTimingCorrection = getCltTimingCorrection(engineLoad);
}

angle_t getAdvanceCorrections(float engineLoad) {
	auto iat = Sensor::get(SensorType::Iat);

	if (!iat) {
		engine->ignitionState.timingIatCorrection = 0;
	} else {
		engine->ignitionState.timingIatCorrection = interpolate3d(
			config->ignitionIatCorrTable,
			config->ignitionIatCorrLoadBins, engineLoad,
			config->ignitionIatCorrTempBins, iat.Value
		);
	}

#if EFI_IDLE_CONTROL
	float instantRpm = engine->triggerCentral.instantRpm.getInstantRpm();

	engine->ignitionState.timingPidCorrection = engine->module<IdleController>()->getIdleTimingAdjustment(instantRpm);
#endif // EFI_IDLE_CONTROL

	engine->ignitionState.dfcoTimingRetard = engine->module<DfcoController>()->getTimingRetard();

#if EFI_VVT_COMPENSATION
	{
		float intakeAngle = engine->triggerCentral.getVVTPosition(0, 0);
		engine->ignitionState.vvtIntakeTimingCorrection = std::isnan(intakeAngle) ? 0 :
			interpolate3d(config->vvtIgnIntakeCorrTable,
				config->vvtIgnIntakeCorrVvtBins, intakeAngle,
				config->vvtIgnIntakeCorrRpmBins, Sensor::getOrZero(SensorType::Rpm));

		float exhaustAngle = engine->triggerCentral.getVVTPosition(0, 1);
		engine->ignitionState.vvtExhaustTimingCorrection = std::isnan(exhaustAngle) ? 0 :
			interpolate3d(config->vvtIgnExhaustCorrTable,
				config->vvtIgnExhaustCorrVvtBins, exhaustAngle,
				config->vvtIgnExhaustCorrRpmBins, Sensor::getOrZero(SensorType::Rpm));
	}
#endif // EFI_VVT_COMPENSATION

#if EFI_TUNER_STUDIO
	engine->outputChannels.multiSparkCounter = engine->engineState.multispark.count;
#endif /* EFI_TUNER_STUDIO */

	return engine->ignitionState.timingIatCorrection
		+ engine->ignitionState.cltTimingCorrection
#if EFI_VVT_COMPENSATION
		+ engine->ignitionState.vvtIntakeTimingCorrection
		+ engine->ignitionState.vvtExhaustTimingCorrection
#endif
		+ engine->ignitionState.timingPidCorrection
		- engine->ignitionState.dfcoTimingRetard
#if EFI_LAUNCH_POWER_RAMP
		- engine->module<LaunchPowerRamp>().unmock().getTimingRetard()
#endif // EFI_LAUNCH_POWER_RAMP
#if EFI_ROLLING_LAUNCH
		- engine->module<RollingLaunchControl>().unmock().getTimingRetard()
#endif // EFI_ROLLING_LAUNCH
#if EFI_BURST_KNOCK
		- engine->module<BurstKnock>().unmock().getTimingRetard()
#endif // EFI_BURST_KNOCK
		;
}

/**
 * @return ignition timing angle advance before TDC for Cranking
 */
angle_t getCrankingAdvance(float rpm, float engineLoad) {
	// get advance from the separate table for Cranking
	if (engineConfiguration->useSeparateAdvanceForCranking) {
		return interpolate2d(rpm, config->crankingAdvanceBins, config->crankingAdvance);
	}

	// Interpolate the cranking timing angle to the earlier running angle for faster engine start
	angle_t crankingToRunningTransitionAngle = getRunningAdvance(engineConfiguration->cranking.rpm, engineLoad);
	// interpolate not from zero, but starting from min. possible rpm detected
	return interpolateClamped(engine->rpmCalculator.getMinCrankingRpm(), engineConfiguration->crankingTimingAngle, engineConfiguration->cranking.rpm, crankingToRunningTransitionAngle, rpm);
}
#endif // EFI_ENGINE_CONTROL && EFI_SHAFT_POSITION_INPUT

angle_t IgnitionState::getAdvance(float rpm, float engineLoad) {
	if (std::isnan(engineLoad)) {
		return 0; // any error should already be reported
	}
  if (engineConfiguration->timingMode == TM_FIXED) {
		// fixed timing is the simple: cranking/running does not matter, no corrections!
		return engineConfiguration->fixedTiming;
	}

	angle_t angle;

	bool isCranking = engine->rpmCalculator.isCranking();
	if (isCranking) {
		angle = getCrankingAdvance(rpm, engineLoad);
		assertAngleRange(angle, "crAngle", ObdCode::CUSTOM_ERR_ANGLE_CR);
		efiAssert(ObdCode::CUSTOM_ERR_ASSERT, !std::isnan(angle), "cr_AngleN", 0);
	} else {
		angle = getRunningAdvance(rpm, engineLoad);

		if (std::isnan(angle)) {
			warning(ObdCode::CUSTOM_ERR_6610, "NaN angle from table");
			return 0;
		}
	}

	// Allow if we're either not cranking OR allowed to correct in cranking
	bool allowCorrections = !isCranking || engineConfiguration->useAdvanceCorrectionsForCranking;

	if (allowCorrections) {
		angle_t correction = getAdvanceCorrections(engineLoad);
		if (!std::isnan(correction)) { // correction could be NaN during settings update
			angle += correction;
		}
	}

	efiAssert(ObdCode::CUSTOM_ERR_ASSERT, !std::isnan(angle), "_AngleN5", 0);
	return angle;
}

angle_t IgnitionState::getWrappedAdvance(const float rpm, const float engineLoad) {
	bool isCranking = engine->rpmCalculator.isCranking();
	if (!isCranking && engine->module<EngineStateMachine>().unmock().engineSmIsPopsAndBangs) {
		popsAndBangsTimingActive = true;
		angle_t angle = getCustomPage()->popsAndBangsTimingOverride * luaTimingMult + luaTimingAdd;
		wrapAngle(angle, "getWrappedAdvance", ObdCode::CUSTOM_ERR_ADCANCE_CALC_ANGLE);
		return angle;
	}
	popsAndBangsTimingActive = false;
    angle_t angle = getAdvance(rpm, engineLoad) * luaTimingMult + luaTimingAdd;
    // Limp Mode: pull timing while limp is latched (skipped during cranking above).
    if (!isCranking && engine->module<EngineStateMachine>().unmock().engineSmIsLimp) {
        angle -= getCustomPage()->limpModeTimingReduction;
    }
    // Eco Mode: add (or pull) timing while the economy overlay is active.
    if (!isCranking && engine->module<EngineStateMachine>().unmock().engineSmIsEcoMode) {
        angle += getCustomPage()->ecoTimingAdder;
    }
    // Quick Warmup: pull timing when cold + idle to heat the exhaust and aid catalyst light-off.
    if (!isCranking && engine->module<EngineStateMachine>().unmock().engineSmIsQuickWarmup) {
        angle += getCustomPage()->quickWarmupTimingRetard;
    }
    wrapAngle(angle, "getWrappedAdvance", ObdCode::CUSTOM_ERR_ADCANCE_CALC_ANGLE);
    return angle;
}

#include "board_overrides.h"

std::optional<setup_custom_get_cylinder_ignition_trim_type> custom_board_getCylinderIgnitionTrim;

angle_t getCylinderIgnitionTrim(size_t cylinderNumber, float rpm, float ignitionLoad) {
	if (custom_board_getCylinderIgnitionTrim.has_value()) {
		return custom_board_getCylinderIgnitionTrim.value()(cylinderNumber, rpm, ignitionLoad);
	}
	return IgnitionState::getInterpolatedIgnitionTrim(cylinderNumber, rpm, ignitionLoad);
}

size_t getMultiSparkCount(float rpm) {
	// Compute multispark (if enabled)
	if (engineConfiguration->multisparkEnable
		&& rpm <= engineConfiguration->multisparkMaxRpm
		&& engineConfiguration->multisparkMaxExtraSparkCount > 0) {
		// For zero RPM, disable multispark.  We don't yet know the engine speed, so multispark may not be safe.
		if (rpm == 0) {
			return 0;
		}

		floatus_t multiDelay = 1000.0f * engineConfiguration->multisparkSparkDuration;
		floatus_t multiDwell = 1000.0f * engineConfiguration->multisparkDwell;

		// dwell times are below 10 seconds here so we use 32 bit type for performance reasons
		engine->engineState.multispark.delay = (uint32_t)USF2NT(multiDelay);
		engine->engineState.multispark.dwell = (uint32_t)USF2NT(multiDwell);

		constexpr float usPerDegreeAt1Rpm = 60e6 / 360;
		floatus_t usPerDegree = usPerDegreeAt1Rpm / rpm;

		// How long is there for sparks? The user configured an angle, convert to time.
		floatus_t additionalSparksUs = usPerDegree * engineConfiguration->multisparkMaxSparkingAngle;
		// How long does one spark take?
		floatus_t oneSparkTime = multiDelay + multiDwell;

		// How many sparks can we fit in the alloted time?
		float sparksFitInTime = additionalSparksUs / oneSparkTime;

		// Take the floor (convert to uint8_t) - we want to undershoot, not overshoot
		uint32_t floored = sparksFitInTime;

		// Allow no more than the maximum number of extra sparks
		return minI(floored, engineConfiguration->multisparkMaxExtraSparkCount);
	} else {
		return 0;
	}
}

void initIgnitionAdvanceControl() {
}

/**
 * @return Spark dwell time, in milliseconds. 0 if tables are not ready.
 */
floatms_t IgnitionState::getSparkDwell(float rpm, bool isCranking) {
	float dwellMs;
	if (isCranking) {
		dwellMs = engineConfiguration->ignitionDwellForCrankingMs;
	} else if (engineConfiguration->dwellDutyModeEnabled) {
		efiAssert(ObdCode::CUSTOM_ERR_ASSERT, !std::isnan(rpm), "invalid rpm", NAN);
		// Duty mode: dwell = duty% × (engine cycle duration / sparks per cycle).
		// Exact inverse of getCoilDutyCycle() — gives the dwell that produces the
		// requested duty on the coil output pin (e.g. 50% for Ford TFI modules).
		float intervalMs = getEngineCycleDuration(rpm) / getNumberOfSparks(getCurrentIgnitionMode());
		baseDwell = engineConfiguration->dwellDutyPercent / 100.0f * intervalMs;
		dwellVoltageCorrection = 1.0f;
		dwellMs = baseDwell;
	} else {
		efiAssert(ObdCode::CUSTOM_ERR_ASSERT, !std::isnan(rpm), "invalid rpm", NAN);

		baseDwell = interpolate2d(rpm, config->sparkDwellRpmBins, config->sparkDwellValues);
		dwellVoltageCorrection = interpolate2d(
				Sensor::getOrZero(SensorType::BatteryVoltage),
				config->dwellVoltageCorrVoltBins,
				config->dwellVoltageCorrValues
		);

		// for compat (table full of zeroes)
		if (dwellVoltageCorrection < 0.1f) {
			dwellVoltageCorrection = 1;
		}

		dwellMs = baseDwell * dwellVoltageCorrection;
	}

	if (std::isnan(dwellMs) || dwellMs <= 0) {
		// this could happen during engine configuration reset
		warning(ObdCode::CUSTOM_ERR_DWELL_DURATION, "invalid dwell: %.2f at rpm=%.0f", dwellMs, rpm);
		return 0;
	}
	return dwellMs;
}

void IgnitionState::updateDwell(float rpm, bool isCranking) {
	sparkDwell = getSparkDwell(rpm, isCranking);
	dwellDurationAngle = std::isnan(rpm) ? NAN : getDwell() / getOneDegreeTimeMs(rpm);
}

floatms_t IgnitionState::getDwell() const {
	return sparkDwell;
}

  angle_t IgnitionState::getTrailingSparkAngle(const float rpm, const float engineLoad){
	if (std::isnan(engineLoad)) {
		// default value from: https://github.com/rusefi/rusefi/commit/86683afca22ed1a8af8fd5ac9231442e2124646e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
		return 10;
	}
	return interpolate3d(
			config->trailingSparkTable,
			config->trailingSparkLoadBins, engineLoad,
			config->trailingSparkRpmBins, rpm
	);
}

angle_t IgnitionState::getSparkHardwareLatencyCorrection(){
	// time => degree
	angle_t correction = engineConfiguration->sparkHardwareLatencyCorrection / engine->rpmCalculator.oneDegreeUs;

	if (!std::isnan(correction)) {
		return correction;
	}
	return 0;
}

angle_t IgnitionState::getInterpolatedIgnitionAngle(const float rpm, const float ignitionLoad) {
	return interpolate3d(
		config->ignitionTable,
		config->ignitionLoadBins, ignitionLoad,
		config->ignitionRpmBins, rpm
	);
}

angle_t IgnitionState::getInterpolatedIgnitionTrim(
	const size_t cylinderNumber,
	const float rpm,
	const float ignitionLoad
) {
	return interpolate3d(
		config->ignTrims[cylinderNumber].table,
		config->ignTrimLoadBins, ignitionLoad,
		config->ignTrimRpmBins, rpm
	);
}

#endif // EFI_ENGINE_CONTROL
