ElDominio/rusefi/firmware/integration/config_page_4.txt

! note: PlainConfigHandler isolates the custom types created on rusefi_config.txt so we need to duplicate it here :c
custom switch_input_pin_e 2 bits, U16, @OFFSET@, [0:8], $switch_input_pin_e_list
custom pin_input_mode_e 1 bits, U08, @OFFSET@, [0:2], $pin_input_mode_e_enum
custom gppwm_channel_e 1 bits, U08, @OFFSET@, [0:5], $gppwm_channel_e_enum

struct_no_prefix page4_s
  ! note this is pretty similar to a blend table!
  uint16_t[VE_LOAD_COUNT x VE_RPM_COUNT] autoscale secondVeTable;;"%", 0.1, 0, 0, 999, 1
  uint16_t[VE_LOAD_COUNT] secondVeLoadBins;;{bitStringValue(veLoadUnitLabels, veLoadUnitIdx)}, {!(veOverrideMode == 1 || (veOverrideMode == 0 && fuelAlgorithm == 0)) || useMetricOnInterface ? 1 : @@UNITS_KPA_TO_PSI@@}, 0, 0, {veOverrideMode == 1 || (veOverrideMode == 0 && fuelAlgorithm == 0) ? (useMetricOnInterface ? @@MAP_UPPER_LIMIT@@ : @@MAP_UPPER_LIMIT@@ * @@UNITS_KPA_TO_PSI@@) : @@MAP_UPPER_LIMIT@@}, 0
  uint16_t[VE_RPM_COUNT] secondVeRpmBins;;"RPM",	   1, 0, 0, 18000, 0

  switch_input_pin_e secondVeTableInput;Pin that activates the second VE table (hard switch, overrides blend)
  pin_input_mode_e secondVeTableInputMode;

  gppwm_channel_e secondVeBlendParameter;Input that controls the blend ratio between primary and second VE table

  int16_t[BLEND_FACTOR_SIZE] autoscale secondVeBlendBins;;"", 0.1, 0, -3200, 3200, 1
  uint8_t[BLEND_FACTOR_SIZE] autoscale secondVeBlendValues;;"%", 0.5, 0, 0, 100, 1

  ! note this is pretty similar to a blend table!
  int16_t[IGN_LOAD_COUNT x IGN_RPM_COUNT] autoscale secondIgnitionTable;;"deg", 0.1, 0, -20, 90, 1
  uint16_t[IGN_LOAD_COUNT] secondIgnitionLoadBins;;{bitStringValue(ignLoadUnitLabels, ignLoadUnitIdx)}, {!(ignOverrideMode == 1 || (ignOverrideMode == 0 && fuelAlgorithm == 0)) || useMetricOnInterface ? 1 : @@UNITS_KPA_TO_PSI@@}, 0, 0, {ignOverrideMode == 1 || (ignOverrideMode == 0 && fuelAlgorithm == 0) ? (useMetricOnInterface ? @@MAP_UPPER_LIMIT@@ : @@MAP_UPPER_LIMIT@@ * @@UNITS_KPA_TO_PSI@@) : @@MAP_UPPER_LIMIT@@}, 0
  uint16_t[IGN_RPM_COUNT] secondIgnitionRpmBins;;"RPM",	   1, 0, 0, 18000, 0

  switch_input_pin_e secondIgnitionTableInput;Pin that activates the second ignition table (hard switch, overrides blend)
  pin_input_mode_e secondIgnitionTableInputMode;

  gppwm_channel_e secondIgnitionBlendParameter;Input that controls the blend ratio between primary and second ignition table

  int16_t[BLEND_FACTOR_SIZE] autoscale secondIgnitionBlendBins;;"", 0.1, 0, -3200, 3200, 1
  uint8_t[BLEND_FACTOR_SIZE] autoscale secondIgnitionBlendValues;;"%", 0.5, 0, 0, 100, 1

  uint8_t[TORQUE_CURVE_SIZE x TORQUE_CURVE_RPM_SIZE] autoscale torqueTable;;"Nm", 10, 0, 0, 255, 0
  uint16_t[TORQUE_CURVE_RPM_SIZE] torqueRpmBins;;"RPM", 1, 0, 0, 65000, 0
  uint16_t[TORQUE_CURVE_SIZE] torqueLoadBins;;"Load", 1, 0, 0, 65000, 0
end_struct
