ElDominio/rusefi/firmware/controllers/engine_controller.cpp

/**
 * @file    engine_controller.cpp
 * @brief   Controllers package entry point code
 *
 *
 *
 * @date Feb 7, 2013
 * @author Andrey Belomutskiy, (c) 2012-2020
 *
 * This file is part of rusEfi - see http://rusefi.com
 *
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
 * You should have received a copy of the GNU General Public License along with this program.
 * If not, see <http://www.gnu.org/licenses/>.
 */

#include "pch.h"


#include "trigger_central.h"
#include "script_impl.h"
#include "idle_thread.h"
#include "main_trigger_callback.h"
#include "flash_main.h"
#include "bench_test.h"
#include "mmc_card.h"
#include "electronic_throttle.h"
#include "trigger_emulator_algo.h"
#include "high_pressure_fuel_pump.h"
#include "malfunction_central.h"
#include "speed_density.h"
#include "local_version_holder.h"
#include "alternator_controller.h"
#include "fuel_pump.h"
#include "can_bench_test.h"
#include "engine_emulator.h"
#include "fuel_math.h"
#include "defaults.h"
#include "spark_logic.h"
#include "status_loop.h"
#include "aux_valves.h"
#include "accelerometer.h"
#include "vvt.h"
#include "boost_control.h"
#include "launch_control.h"
#include "speedometer.h"
#include "gppwm.h"
#include "date_stamp.h"
#include "wheel_slip_ratio_source.h"
#include "rusefi_lua.h"
#include "buttonshift.h"
#include "start_stop.h"
#include "dynoview.h"
#include "vr_pwm.h"
#include "adc_subscription.h"
#include "gc_generic.h"

#if EFI_TUNER_STUDIO
#include "tunerstudio.h"
#endif /* EFI_TUNER_STUDIO */

#if EFI_LOGIC_ANALYZER
#include "logic_analyzer.h"
#endif /* EFI_LOGIC_ANALYZER */

#include "periodic_task.h"
#include "board_overrides.h"

#ifdef MODULE_MAP_AVERAGING
#include "map_averaging.h"
#endif

#if ! EFI_UNIT_TEST
#include "init.h"
#include "mpu_util.h"
#endif /* EFI_UNIT_TEST */

#if !EFI_UNIT_TEST

/**
 * Would love to pass reference to configuration object into constructor but C++ does allow attributes after parenthesized initializer
 */
#ifdef EFI_IS_STM32F4
// Every STM32F4 target (F407 and F42x/43x alike) has plenty of real headroom in the
// regular RAM pool - confirmed via __heap_base__ on hellen154hyundai (~35KB free) and
// protorico-econoline (~51KB free) even without the F42x/43x family's extra SRAM3 bank -
// while CCM is a hard fixed 64k that AlphaXModuleList's relocation alone doesn't always
// clear on every board (e.g. alphax-s197-v2 still overflowed by 920 bytes after that
// split alone). Keep the rest of Engine (coreModules plus Engine's own state) out of
// that tight, easily-overflowed CCM pool entirely rather than trimming board-by-board.
// F7/H7 keep Engine CCM_OPTIONAL as before - their CCM-equivalent (DTCM) is 128k, not
// under the same pressure.
Engine ___engine;
#else
Engine ___engine CCM_OPTIONAL;
#endif
// NOT CCM_OPTIONAL - lives in regular RAM, not the fixed 64KB ram4 CCM region. See
// AlphaXModuleList's doc comment in engine.h.
AlphaXModuleList ___alphaXEngineModules;

#else // EFI_UNIT_TEST

Engine * engine;

#endif /* EFI_UNIT_TEST */

using namespace rusefi::stringutil;

void initDataStructures() {
#if EFI_ENGINE_CONTROL
	initFuelMap();
	initSpeedDensity();
	IgnitionEventList &events = engine->ignitionEvents;
	for (size_t i=0;i<efi::size(events.elements);i++) {
	  // above-zero value helps distinguish events
	  events.elements[i].sparkCounter = 1;
	}
  // above-zero value helps distinguish events
	engine->engineState.globalSparkCounter = 1;
#endif // EFI_ENGINE_CONTROL
}

#if !EFI_UNIT_TEST

static void doPeriodicSlowCallback();

class PeriodicFastController : public PeriodicTimerController {
	void PeriodicTask() override {
		engine->periodicFastCallback();
	}

	int getPeriodMs() override {
		return FAST_CALLBACK_PERIOD_MS;
	}
};

class PeriodicSlowController : public PeriodicTimerController {
	void PeriodicTask() override {
		doPeriodicSlowCallback();
	}

	int getPeriodMs() override {
		// no reason to have this configurable, looks like everyone is happy with 20Hz
		return SLOW_CALLBACK_PERIOD_MS;
	}
};

static PeriodicFastController fastController;
static PeriodicSlowController slowController;

class EngineStateBlinkingTask : public PeriodicTimerController {
	int getPeriodMs() override {
		return 50;
	}

	void PeriodicTask() override {
#if EFI_SHAFT_POSITION_INPUT
		bool is_running = engine->rpmCalculator.isRunning();
#else
		bool is_running = false;
#endif /* EFI_SHAFT_POSITION_INPUT */

		if (is_running) {
			// blink in running mode
			enginePins.runningLedPin.toggle();
		} else {
			bool is_cranking = engine->rpmCalculator.isCranking();
			enginePins.runningLedPin.setValue(is_cranking);
		}
	}
};

static EngineStateBlinkingTask engineStateBlinkingTask;

static void resetAccel() {
	engine->module<TpsAccelEnrichment>()->resetAE();

#if EFI_ENGINE_CONTROL
	for (size_t i = 0; i < efi::size(engine->injectionEvents.elements); i++)
	{
		engine->injectionEvents.elements[i].getWallFuel().resetWF();
	}
#endif // EFI_ENGINE_CONTROL
}

static void doPeriodicSlowCallback() {
#if EFI_SHAFT_POSITION_INPUT
	efiAssertVoid(ObdCode::CUSTOM_ERR_6661, getCurrentRemainingStack() > 64, "lowStckOnEv");

	slowStartStopButtonCallback();

	engine->rpmCalculator.onSlowCallback();
	if (engine->rpmCalculator.isStopped()) {
		resetAccel();
	}
#endif /* EFI_SHAFT_POSITION_INPUT */

	engine->periodicSlowCallback();

#if EFI_TCU
	if (engineConfiguration->tcuEnabled && engineConfiguration->gearControllerMode != GearControllerMode::None) {
		if (engine->gearController == NULL) {
			initGearController();
		} else if (engine->gearController->getMode() != engineConfiguration->gearControllerMode) {
			initGearController();
		}
		engine->gearController->update();
	}
#endif // EFI_TCU

	tryResetWatchdog();

#if EFI_PROD_CODE
	// single-shot reset all counter after 5 second of happines
	static unsigned int slow_counter = 5 * 1000 / SLOW_CALLBACK_PERIOD_MS;
	if ((slow_counter) && (--slow_counter == 0)) {
		errorHandlerResetCounters();
	}
#endif // EFI_PROD_CODE
}

void initPeriodicEvents() {
	slowController.start();
	fastController.start();
}

char * getPinNameByAdcChannel(const char *msg, adc_channel_e hwChannel, char *buffer, size_t bufferSize) {
#if HAL_USE_ADC
	if (!isAdcChannelValid(hwChannel)) {
		snprintf(buffer, bufferSize, "NONE");
	} else {
		const char *name = portname(getAdcChannelPort(msg, hwChannel));
		snprintf(buffer, bufferSize, "%s%d", name ? name : "null", getAdcChannelPin(hwChannel));
	}
#else
  UNUSED(msg);
  UNUSED(hwChannel);
	snprintf(buffer, bufferSize, "NONE");
#endif /* HAL_USE_ADC */
	return buffer;
}

#if EFI_PROD_CODE
static void printSensorInfo() {
#if HAL_USE_ADC
	// Print info about analog mappings
	AdcSubscription::PrintInfo();
#endif // HAL_USE_ADC

	// Print info about all sensors
	Sensor::showAllSensorInfo();
}
#endif // EFI_PROD_CODE

#define isOutOfBounds(offset) ((offset<0) || (offset) >= (int) sizeof(engine_configuration_s))

static void getShort(int offset) {
	if (isOutOfBounds(offset))
		return;
	uint16_t *ptr = (uint16_t *) (&((char *) engineConfiguration)[offset]);
	uint16_t value = *ptr;
	/**
	 * this response is part of rusEfi console API
	 */
	efiPrintf("short%s%d is %d", CONSOLE_DATA_PROTOCOL_TAG, offset, value);
}

static void getByte(int offset) {
	if (isOutOfBounds(offset))
		return;
	uint8_t *ptr = (uint8_t *) (&((char *) engineConfiguration)[offset]);
	uint8_t value = *ptr;
	/**
	 * this response is part of rusEfi console API
	 */
	efiPrintf("byte%s%d is %d", CONSOLE_DATA_PROTOCOL_TAG, offset, value);
}

static void setBit(const char *offsetStr, const char *bitStr, const char *valueStr) {
	int offset = atoi(offsetStr);
	if (absI(offset) == absI(ATOI_ERROR_CODE)) {
		efiPrintf("invalid offset [%s]", offsetStr);
		return;
	}
	if (isOutOfBounds(offset)) {
		return;
	}
	int bit = atoi(bitStr);
	if (absI(bit) == absI(ATOI_ERROR_CODE)) {
		efiPrintf("invalid bit [%s]", bitStr);
		return;
	}
	int value = atoi(valueStr);
	if (absI(value) == absI(ATOI_ERROR_CODE)) {
		efiPrintf("invalid value [%s]", valueStr);
		return;
	}
	int *ptr = (int *) (&((char *) engineConfiguration)[offset]);
	*ptr ^= (-value ^ *ptr) & (1 << bit);
	/**
	 * this response is part of rusEfi console API
	 */
	efiPrintf("bit%s%d/%d is %d", CONSOLE_DATA_PROTOCOL_TAG, offset, bit, value);
	incrementGlobalConfigurationVersion("setBit");
}

static void setShort(const int offset, const int value) {
	if (isOutOfBounds(offset))
		return;
	uint16_t *ptr = (uint16_t *) (&((char *) engineConfiguration)[offset]);
	*ptr = (uint16_t) value;
	getShort(offset);
	incrementGlobalConfigurationVersion("setShort");
}

static void setByte(const int offset, const int value) {
	if (isOutOfBounds(offset))
		return;
	uint8_t *ptr = (uint8_t *) (&((char *) engineConfiguration)[offset]);
	*ptr = (uint8_t) value;
	getByte(offset);
	incrementGlobalConfigurationVersion("setByte");
}

static void getBit(int offset, int bit) {
	if (isOutOfBounds(offset))
		return;
	int *ptr = (int *) (&((char *) engineConfiguration)[offset]);
	int value = (*ptr >> bit) & 1;
	/**
	 * this response is part of rusEfi console API
	 */
	efiPrintf("bit%s%d/%d is %d", CONSOLE_DATA_PROTOCOL_TAG, offset, bit, value);
}

static void getInt(int offset) {
	if (isOutOfBounds(offset))
		return;
	int *ptr = (int *) (&((char *) engineConfiguration)[offset]);
	int value = *ptr;
	/**
	 * this response is part of rusEfi console API
	 */
	efiPrintf("int%s%d is %d", CONSOLE_DATA_PROTOCOL_TAG, offset, value);
}

static void setInt(const int offset, const int value) {
	if (isOutOfBounds(offset))
		return;
	int *ptr = (int *) (&((char *) engineConfiguration)[offset]);
	*ptr = value;
	getInt(offset);
	incrementGlobalConfigurationVersion("setInt");
}

static void getFloat(int offset) {
	if (isOutOfBounds(offset))
		return;
	float *ptr = (float *) (&((char *) engineConfiguration)[offset]);
	float value = *ptr;
	/**
	 * this response is part of rusEfi console API
	 */
	efiPrintf("float%s%d is %.5f", CONSOLE_DATA_PROTOCOL_TAG, offset, value);
}

static void setFloat(const char *offsetStr, const char *valueStr) {
	int offset = atoi(offsetStr);
	if (absI(offset) == absI(ATOI_ERROR_CODE)) {
		efiPrintf("invalid offset [%s]", offsetStr);
		return;
	}
	if (isOutOfBounds(offset))
		return;
	float value = atoff(valueStr);
	if (std::isnan(value)) {
		efiPrintf("invalid value [%s]", valueStr);
		return;
	}
	float *ptr = (float *) (&((char *) engineConfiguration)[offset]);
	*ptr = value;
	getFloat(offset);
	incrementGlobalConfigurationVersion("setFloat");
}

static void initConfigActions() {
	addConsoleActionSS("set_float", (VoidCharPtrCharPtr) setFloat);
	addConsoleActionII("set_int", (VoidIntInt) setInt);
	addConsoleActionII("set_short", (VoidIntInt) setShort);
	addConsoleActionII("set_byte", (VoidIntInt) setByte);
	addConsoleActionSSS("set_bit", setBit);

	addConsoleActionI("get_float", getFloat);
	addConsoleActionI("get_int", getInt);
	addConsoleActionI("get_short", getShort);
	addConsoleActionI("get_byte", getByte);
	addConsoleActionII("get_bit", getBit);
}
#endif /* EFI_UNIT_TEST */

// one-time start-up
// this method is used by real firmware and simulator and unit test
void commonInitEngineController() {
#if EFI_PROD_CODE
	addConsoleAction("sensorinfo", printSensorInfo);
	addConsoleAction("reset_accel", resetAccel);
#endif /* EFI_PROD_CODE */

#if EFI_SIMULATOR || EFI_UNIT_TEST
	printf("commonInitEngineController\n");
#endif

#if !EFI_UNIT_TEST
	initConfigActions();
#endif /* EFI_UNIT_TEST */

#if EFI_ENGINE_CONTROL
	/**
	 * This has to go after 'enginePins.startPins()' in order to
	 * properly detect un-assigned output pins
	 */
	prepareOutputSignals();

	engine->injectionEvents.addFuelEvents();
#endif // EFI_ENGINE_CONTROL


#if EFI_PROD_CODE || EFI_SIMULATOR
	initSettings();

	if (hasFirmwareError()) {
		return;
	}
#endif

#if ! EFI_UNIT_TEST && EFI_ENGINE_CONTROL
	initBenchTest();
#endif /* ! EFI_UNIT_TEST && EFI_ENGINE_CONTROL */

#if EFI_ALTERNATOR_CONTROL
	initAlternatorCtrl();
#endif /* EFI_ALTERNATOR_CONTROL */

#if EFI_ADVANCED_FUEL_PUMP
	initFuelPumpPwm();
#endif

#if EFI_VVT_PID
	initVvtActuators();
#endif /* EFI_VVT_PID */

#if !EFI_UNIT_TEST
	// This is tested independently - don't configure sensors for tests.
	// This lets us selectively mock them for each test.
	initNewSensors();
#endif /* EFI_UNIT_TEST */

	initSensors();

	initAccelEnrichment();

	initScriptImpl();

	initGpPwm();
	initExhaustCutout();
	initImrc();

#if EFI_IDLE_CONTROL
	startIdleThread();
#endif /* EFI_IDLE_CONTROL */

#if EFI_TCU
	initGearController();
#endif

	initButtonDebounce();

#if EFI_ELECTRONIC_THROTTLE_BODY
	initElectronicThrottle();
#endif /* EFI_ELECTRONIC_THROTTLE_BODY */

#if EFI_MAP_AVERAGING && defined (MODULE_MAP_AVERAGING)
	engine->module<MapAveragingModule>()->init();
#else
	efiPrintf("No MapAveraging support!");
#endif /* EFI_MAP_AVERAGING */

#if EFI_BOOST_CONTROL
	initBoostCtrl();
#endif /* EFI_BOOST_CONTROL */

#if EFI_LAUNCH_CONTROL
	initLaunchControl();
#endif

  engine->tractionController.init();

#if EFI_ENGINE_CONTROL
  initIgnitionAdvanceControl();
#endif // EFI_ENGINE_CONTROL

#if EFI_UNIT_TEST
	engine->rpmCalculator.Register();
#endif /* EFI_UNIT_TEST */

#if EFI_AUX_VALVES
	initAuxValves();
#endif /* EFI_AUX_VALVES */

#ifdef MODULE_TACHOMETER
	engine->module<TachometerModule>()->init();
#endif

	initSpeedometer();

#if EFI_ENGINE_CONTROL
	initStft();
#endif // EFI_ENGINE_CONTROL
#if EFI_LTFT_CONTROL
	initLtft();
#endif
#if EFI_OIL_LIFE_MONITOR
	initOilLifeMonitor();
#endif
}

bool validateBoardConfig() {
  // todo: remove placeholder June 2026
  return true;
}

static bool validateGdi() {
	auto lobes = engineConfiguration->hpfpCamLobes;
	if (!lobes) {
		return true;
	}
#if EFI_HPFP
	int expectedLastLobeProfileAngle = 360 / lobes;
  float actualLastAngle = config->hpfpLobeProfileAngle[efi::size(config->hpfpLobeProfileAngle) - 1];
	if (expectedLastLobeProfileAngle != actualLastAngle) {
		criticalError("Last HPFP angle expected %d got %f", expectedLastLobeProfileAngle, actualLastAngle);
		return false;
	}
#endif // EFI_HPFP
	return true;
}

// Returns false if there's an obvious problem with the loaded configuration
// previousConfiguration: nullptr on start-up, the currently running configuration on burn
static bool validateConfig(const engine_configuration_s* previousConfiguration) {
  if (!get_board_override_result(custom_board_validateConfig, true, previousConfiguration)) {
    return false;
  }
#if defined(HW_HELLEN_UAEFI)
  // todo: make this board-specific validation callback!
  pickEtbOrStepper();
#endif
  if (!validateGdi()) {
    return false;
  }
#if EFI_ELECTRONIC_THROTTLE_BODY
  if (engineConfiguration->etbMinimumPosition + 1 >= engineConfiguration->etbMaximumPosition) {
		criticalError("Broken ETB min/max %d %d",
		  engineConfiguration->etbMinimumPosition,
		  engineConfiguration->etbMaximumPosition);
		return false;
  }
#endif

  if (engineConfiguration->knockFrequency != 0 && engineConfiguration->knockFrequency < 100) {
    // todo: migrate from hard error to soft error
		criticalError("knock frequency setting uses HZ not KHz: %f", engineConfiguration->knockFrequency);
		return false;
  }

#if EFI_WHEEL_SPEED_SENSORS
  // The configurable Source1/Source2 selector wins (see init_aux_speed_sensor.cpp), so this is
  // not fatal - just flag a tune that probably doesn't do what the user expects.
  if (isConfigurableWheelSlipRatioActive() && engineConfiguration->useAuxSpeedForSlipRatio) {
    configError("Wheel Slip Ratio: both the configurable Source1/Source2 selector and "
        "'Use Aux Speed for slip ratio' are enabled - the configurable selector wins");
  }
#endif // EFI_WHEEL_SPEED_SENSORS


  // the only step which is allowed to modify configuration - everything else in this method is read-only validation
  applyDefaultsOrFixAfterBurn(previousConfiguration);
	if (engineConfiguration->cylindersCount > MAX_CYLINDER_COUNT) {
		criticalError("Invalid cylinder count: %d", engineConfiguration->cylindersCount);
		return false;
	}
#if EFI_PROD_CODE && (BOARD_MC33810_COUNT > 0)
    float maxConfiguredCorr = config->dwellVoltageCorrValues[0];
    for (size_t i = 0;i<efi::size(config->dwellVoltageCorrValues);i++) {
        maxConfiguredCorr = std::max(maxConfiguredCorr, (float)config->dwellVoltageCorrValues[i]);
    }
    float maxConfiguredDwell = config->sparkDwellValues[0];
    for (size_t i = 0;i<efi::size(config->sparkDwellValues);i++) {
        maxConfiguredDwell = std::max(maxConfiguredDwell, (float)config->sparkDwellValues[i]);
    }
    int maxAllowedDwell = getMc33810maxDwellTimer(engineConfiguration->mc33810maxDwellTimer);
        if (maxConfiguredCorr * maxConfiguredDwell > maxAllowedDwell) {
            criticalError("Dwell=%.2f/corr=%.2f while 33810 limit %d", maxConfiguredDwell, maxConfiguredCorr, maxAllowedDwell);
        }

#endif // EFI_PROD_CODE && (BOARD_MC33810_COUNT > 0)
	if (engineConfiguration->adcVcc > 5.0f || engineConfiguration->adcVcc < 1.0f) {
    criticalError("Invalid adcVcc: %f", engineConfiguration->adcVcc);
		return false;
	}

#if EFI_ENGINE_CONTROL
	ensureArrayIsAscending("Injector deadtime vBATT", engineConfiguration->injector.battLagCorrBattBins);
	ensureArrayIsAscending("Injector deadtime Pressure", engineConfiguration->injector.battLagCorrPressBins);

	// Fueling
	{
		ensureArrayIsAscending("VE load", config->veLoadBins);
		ensureArrayIsAscending("VE RPM", config->veRpmBins);

  		ensureArrayIsAscending("Second VE load", secondTablesGetState()->secondVeLoadBins);
  		ensureArrayIsAscending("Second VE RPM", secondTablesGetState()->secondVeRpmBins);

		ensureArrayIsAscending("Lambda/AFR load", config->lambdaLoadBins);
		ensureArrayIsAscending("Lambda/AFR RPM", config->lambdaRpmBins);

		ensureArrayIsAscending("Fuel CLT mult", config->cltFuelCorrBins);
		ensureArrayIsAscending("Fuel IAT mult", config->iatFuelCorrBins);

		ensureArrayIsAscendingOrDefault("Boost CLT mult", config->cltBoostCorrBins);
		ensureArrayIsAscendingOrDefault("Boost IAT mult", config->iatBoostCorrBins);

		ensureArrayIsAscending("Injection phase load", config->injPhaseLoadBins);
		ensureArrayIsAscending("Injection phase RPM", config->injPhaseRpmBins);

		ensureArrayIsAscendingOrDefault("Fuel Level Sensor", config->fuelLevelBins);

		ensureArrayIsAscendingOrDefault("STFT Rpm", config->fuelTrimRpmBins);
		ensureArrayIsAscendingOrDefault("STFT Load", config->fuelTrimLoadBins);

		ensureArrayIsAscendingOrDefault("knock rpm", config->maxKnockRetardRpmBins);
		ensureArrayIsAscendingOrDefault("knock tps", config->maxKnockRetardLoadBins);

		ensureArrayIsAscendingOrDefault("TC slip", engineConfiguration->tractionControlSlipBins);
		ensureArrayIsAscendingOrDefault("TC speed", engineConfiguration->tractionControlSpeedBins);
		ensureArrayIsAscendingOrDefault("TC lua mult", engineConfiguration->tractionControlLuaMultBins);

		ensureArrayIsAscending("TPS/TPS AE from", config->tpsTpsAccelFromRpmBins);
		ensureArrayIsAscending("TPS/TPS AE to", config->tpsTpsAccelToRpmBins);

		ensureArrayIsAscendingOrDefault("TPS TPS RPM correction", config->tpsTspCorrValuesBins);

		ensureArrayIsAscendingOrDefault("Staging Load", config->injectorStagingLoadBins);
		ensureArrayIsAscendingOrDefault("Staging RPM", config->injectorStagingRpmBins);
	}

	// Ignition
	{
		ensureArrayIsAscending("Dwell RPM", config->sparkDwellRpmBins);

		ensureArrayIsAscending("Ignition load", config->ignitionLoadBins);
		ensureArrayIsAscending("Ignition RPM", config->ignitionRpmBins);

		ensureArrayIsAscending("Second Ignition load", secondTablesGetState()->secondIgnitionLoadBins);
		ensureArrayIsAscending("Second Ignition RPM", secondTablesGetState()->secondIgnitionRpmBins);
		ensureArrayIsAscendingOrDefault("Ign Trim Rpm", config->ignTrimRpmBins);
   		ensureArrayIsAscendingOrDefault("Ign Trim Load", config->ignTrimLoadBins);

		ensureArrayIsAscending("Ignition CLT corr CLT", config->ignitionCltCorrTempBins);
  		ensureArrayIsAscending("Ignition CLT corr Load", config->ignitionCltCorrLoadBins);

		ensureArrayIsAscending("Ignition IAT corr IAT", config->ignitionIatCorrTempBins);
		ensureArrayIsAscending("Ignition IAT corr Load", config->ignitionIatCorrLoadBins);
	}

	ensureArrayIsAscendingOrDefault("Map estimate TPS", config->mapEstimateTpsBins);
	ensureArrayIsAscendingOrDefault("Map estimate RPM", config->mapEstimateRpmBins);
#endif // EFI_ENGINE_CONTROL

	ensureArrayIsAscendingOrDefault("Script Curve 1", config->scriptCurve1Bins);
	ensureArrayIsAscendingOrDefault("Script Curve 2", config->scriptCurve2Bins);
	ensureArrayIsAscendingOrDefault("Script Curve 3", config->scriptCurve3Bins);
	ensureArrayIsAscendingOrDefault("Script Curve 4", config->scriptCurve4Bins);
	ensureArrayIsAscendingOrDefault("Script Curve 5", config->scriptCurve5Bins);
	ensureArrayIsAscendingOrDefault("Script Curve 6", config->scriptCurve6Bins);

// todo: huh? why does this not work on CI?	ensureArrayIsAscendingOrDefault("Dwell Correction Voltage", engineConfiguration->dwellVoltageCorrVoltBins);

#if EFI_ENGINE_CONTROL
	ensureArrayIsAscending("MAF transfer function", config->mafDecodingBins);

	// Cranking tables
	ensureArrayIsAscending("Cranking fuel mult", config->crankingFuelBins);
	ensureArrayIsAscending("Cranking duration", config->crankingCycleBins);
	ensureArrayIsAscending("Cranking Fuel CLT", config->crankingCycleFuelCltBins);
	ensureArrayIsAscending("Cranking TPS", config->crankingTpsBins);

	// Idle tables
	ensureArrayIsAscending("Idle target RPM", config->cltIdleRpmBins);
	ensureArrayIsAscending("Idle warmup mult CLT", config->cltIdleCorrBins);
	ensureArrayIsAscending("Idle warmup mult RPM", config->rpmIdleCorrBins);
#endif // EFI_ENGINE_CONTROL
	ensureArrayIsAscendingOrDefault("Idle coasting RPM", config->iacCoastingRpmBins);
	ensureArrayIsAscendingOrDefault("Idle VE RPM", config->idleVeRpmBins);
	ensureArrayIsAscendingOrDefault("Idle VE Load", config->idleVeLoadBins);
	ensureArrayIsAscendingOrDefault("Idle timing", config->idleAdvanceBins);

	for (size_t index = 0; index < efi::size(engineConfiguration->vrThreshold); index++) {
		auto& cfg = engineConfiguration->vrThreshold[index];

		if (cfg.pin == Gpio::Unassigned) {
			continue;
		}
		ensureArrayIsAscending("VR threshold", cfg.rpmBins);
	}

#if EFI_BOOST_CONTROL
	// Boost
	ensureArrayIsAscending("Boost control Load [open loop]", config->boostOpenLoopLoadBins);
	ensureArrayIsAscending("Boost control Load [closed loop]", config->boostClosedLoopLoadBins);
	ensureArrayIsAscending("Boost control RPM [open+closed loop]", config->boostRpmBins);
#endif // EFI_BOOST_CONTROL

#if EFI_ANTILAG_SYSTEM
	// ALS
	ensureArrayIsAscendingOrDefault("ign ALS TPS", config->alsIgnRetardLoadBins);
	ensureArrayIsAscendingOrDefault("ign ALS RPM", config->alsIgnRetardrpmBins);
	ensureArrayIsAscendingOrDefault("fuel ALS TPS", config->alsFuelAdjustmentLoadBins);
	ensureArrayIsAscendingOrDefault("fuel ALS RPM", config->alsFuelAdjustmentrpmBins);
#endif // EFI_ANTILAG_SYSTEM

#if EFI_ELECTRONIC_THROTTLE_BODY
	// ETB
	ensureArrayIsAscending("Pedal map pedal", config->pedalToTpsPedalBins);
	ensureArrayIsAscending("Pedal map RPM", config->pedalToTpsRpmBins);
#endif // EFI_ELECTRONIC_THROTTLE_BODY

	if (isGdiEngine()) {
		ensureArrayIsAscending("HPFP compensation", config->hpfpCompensationRpmBins);
		ensureArrayIsAscending("HPFP deadtime", config->hpfpDeadtimeVoltsBins);
		ensureArrayIsAscending("HPFP lobe profile", config->hpfpLobeProfileQuantityBins);
		ensureArrayIsAscending("HPFP target rpm", config->hpfpTargetRpmBins);
		ensureArrayIsAscending("HPFP target load", config->hpfpTargetLoadBins);

		ensureArrayIsAscending("HPFP fuel mass compensation fuel pressure", config->hpfpFuelMassCompensationFuelPressure);
		ensureArrayIsAscending("HPFP fuel mass compensation fuel mass", config->hpfpFuelMassCompensationFuelMass);

	}

	// VVT
	if (isBrainPinValid(engineConfiguration->camInputs[0])) {
		ensureArrayIsAscending("VVT intake load", config->vvtTable1LoadBins);
		ensureArrayIsAscending("VVT intake RPM", config->vvtTable1RpmBins);
	}

#if CAM_INPUTS_COUNT != 1
	if (isBrainPinValid(engineConfiguration->camInputs[1])) {
		ensureArrayIsAscending("VVT exhaust load", config->vvtTable2LoadBins);
		ensureArrayIsAscending("VVT exhaust RPM", config->vvtTable2RpmBins);
	}
#endif

	if (engineConfiguration->enableOilPressureProtect) {
		ensureArrayIsAscending("Oil pressure protection", config->minimumOilPressureBins);
	}


	return true;
}

bool validateConfigOnStartUpOrBurn() {
	// start-up: activeConfiguration is still void-prepared, there is no meaningful previous configuration
	return validateConfig(nullptr);
}

bool validateConfigOnStartUpOrBurn(bool isRunningOnBurn) {
	ConfigurationWizard::onConfigOnStartUpOrBurn(isRunningOnBurn);
	// burn: activeConfiguration still holds the configuration the ECU is currently running on
	return validateConfig(&activeConfiguration);
}

#if !EFI_UNIT_TEST

void commonEarlyInit() {
	// note: LED blinking is started even earlier, see startStatusThreads() call in runRusEfi()

#if EFI_SHAFT_POSITION_INPUT
	// todo: figure out better startup logic
	initTriggerCentral();
#endif /* EFI_SHAFT_POSITION_INPUT */

	/**
	 * Initialize hardware drivers
	 */
	initHardware();

	initQcBenchControls();

#if EFI_FILE_LOGGING
	initMmcCard();
#endif /* EFI_FILE_LOGGING */

#if EFI_ENGINE_EMULATOR
	initEngineEmulator();
#endif

#if EFI_LUA
	startLua();
#endif // EFI_LUA

#if EFI_CAN_SERIAL
	// needs to be called after initCan() inside initHardware()
	startCanConsole();
#endif /* EFI_CAN_SERIAL */

}

// one-time start-up
void initRealHardwareEngineController() {
	commonInitEngineController();
	initWarningRunningPins();

#if EFI_LOGIC_ANALYZER
	if (engineConfiguration->isWaveAnalyzerEnabled) {
		initWaveAnalyzer();
	}
#endif /* EFI_LOGIC_ANALYZER */

	if (hasFirmwareError()) {
		return;
	}

	engineStateBlinkingTask.start();

	initVrThresholdPwm();
}

/**
 * See also SIGNATURE_HASH
 */
int getRusEfiVersion() {
	return VCS_DATE;
}
#endif /* EFI_UNIT_TEST */

std::optional<custom_validate_config_type> custom_board_validateConfig;
std::optional<custom_fix_configuration_type> custom_board_fix_configuration;
