ElDominio/rusefi/firmware/hw_layer/hardware.cpp

/**
 * @file    hardware.cpp
 * @brief   Hardware package entry point
 *
 * @date May 27, 2013
 * @author Andrey Belomutskiy, (c) 2012-2020
 */

#include "pch.h"


#include "trigger_input.h"
#include "can_hw.h"
#include "hardware.h"
#include "rtc_helper.h"
#include "bench_test.h"
#include "yaw_rate_sensor.h"
#include "pin_repository.h"
#include "logic_analyzer.h"
#include "smart_gpio.h"
#include "accelerometer.h"
#include "eficonsole.h"
#include "console_io.h"
#include "idle_thread.h"
#include "odometer.h"
#include "kline.h"
#include "dac.h"

#if EFI_PROD_CODE
#include "mpu_util.h"
#endif /* EFI_PROD_CODE */

#include "mmc_card.h"

#include "adc_device.h"
#include "idle_hardware.h"

#include "histogram.h"
#include "gps_uart.h"
#include "sent.h"
#include "cdm_ion_sense.h"
#include "trigger_central.h"
#include "vvt.h"
#include "trigger_emulator_algo.h"
#include "boost_control.h"
#if EFI_SOFTWARE_KNOCK
#include "software_knock.h"
#endif
#include "trigger_scope.h"
#include "init.h"
#if EFI_MC33816
#include "mc33816.h"
#endif /* EFI_MC33816 */
#if EFI_WS2812
#include "WS2812.h"
#endif /* EFI_WS2812 */

#if EFI_MAP_AVERAGING && defined (MODULE_MAP_AVERAGING)
#include "map_averaging.h"
#endif

#if EFI_CONFIGURATION_STORAGE
#include "flash_main.h"
#endif

#if HAL_USE_PAL && EFI_PROD_CODE
#include "digital_input_exti.h"
#endif // HAL_USE_PAL

#include "board_overrides.h"

std::optional<setup_custom_board_overrides_type> custom_board_InitHardwareEarly;
std::optional<setup_custom_board_overrides_type> custom_board_InitHardware;
std::optional<setup_custom_board_overrides_type> custom_board_InitHardwareExtra;
std::optional<setup_custom_board_overrides_type> custom_board_StopHardware;
std::optional<setup_custom_board_overrides_type> custom_board_StartHardware;
std::optional<setup_custom_board_overrides_type> custom_board_BeforeTuneDefaults;

std::optional<setup_custom_bool_type> custom_board_isBoardWithPowerManagement;
std::optional<setup_custom_bool_type> custom_board_boardAllowTriggerActions;

std::optional<setup_custom_bool_type> custom_board_getAcrState;

std::optional<setup_custom_board_engine_type_type> custom_board_AfterTuneDefaults;
std::optional<setup_custom_board_engine_type_type> custom_board_applyUnknownType;

#if HAL_USE_ADC

static AdcToken fastMapSampleIndex;

#if HAL_TRIGGER_USE_ADC
static AdcToken triggerSampleIndex;
#endif // HAL_TRIGGER_USE_ADC

/**
 * This method is not in the adc* lower-level file because it is more business logic then hardware.
 */
void onFastAdcComplete(adcsample_t*) {
	ScopePerf perf(PE::AdcCallbackFast);

#if HAL_TRIGGER_USE_ADC
	// we need to call this ASAP, because trigger processing is time-critical
	triggerAdcCallback(getFastAdc(triggerSampleIndex));
#endif /* HAL_TRIGGER_USE_ADC */

	/**
	 * this callback is executed 10 000 times a second, it needs to be as fast as possible
	 */
	efiAssertVoid(ObdCode::CUSTOM_STACK_ADC, hasLotsOfRemainingStack(), "lowstck#9b");

	auto mapRaw = adcRawValueToScaledVoltage(getFastAdc(fastMapSampleIndex), engineConfiguration->map.sensor.hwChannel);
	engine->outputChannels.rawMapFast = mapRaw;
#if EFI_MAP_AVERAGING && defined (MODULE_MAP_AVERAGING)
	mapAveragingAdcCallback(mapRaw);
#endif /* EFI_MAP_AVERAGING */
}
#endif /* HAL_USE_ADC */

static void calcFastAdcIndexes() {
#if HAL_USE_ADC
	fastMapSampleIndex = enableFastAdcChannel("Fast MAP", engineConfiguration->map.sensor.hwChannel);

#if HAL_TRIGGER_USE_ADC
	triggerSampleIndex = enableFastAdcChannel("Trigger ADC", getAdcChannelForTrigger());
#endif /* HAL_TRIGGER_USE_ADC */

#endif/* HAL_USE_ADC */
}

/**
 * this method is NOT currently invoked on ECU start
 * todo: reduce code duplication by moving more logic into startHardware method
 */
void applyNewHardwareSettings() {
    /**
     * All 'stop' methods need to go before we begin starting pins.
     *
     * We take settings from 'activeConfiguration' not 'engineConfiguration' while stopping hardware.
     * Some hardware is restart unconditionally on change of parameters while for some systems we make extra effort and restart only
     * relevant settings were changes.
     *
     */
	ButtonDebounce::stopConfigurationList();

#if EFI_PROD_CODE
	stopSensors();
#endif // EFI_PROD_CODE

#if EFI_PROD_CODE && EFI_SHAFT_POSITION_INPUT
	stopTriggerInputPins();
#endif /* EFI_SHAFT_POSITION_INPUT */

#if EFI_PROD_CODE && EFI_SENT_SUPPORT
	stopSent();
#endif // EFI_SENT_SUPPORT

#if EFI_CAN_SUPPORT
	stopCanPins();
#endif /* EFI_CAN_SUPPORT */

	stopKLine();


	stopHardware();

#if HAL_USE_SPI
	stopSpiModules();
#endif /* HAL_USE_SPI */

	if (isPinOrModeChanged(clutchUpPin, clutchUpPinMode)) {
		// bug? duplication with stopSwitchPins?
		efiSetPadUnused(activeConfiguration.clutchUpPin);
	}

	enginePins.unregisterPins();

#if EFI_PROD_CODE
	reconfigureSensors();
#endif /* EFI_PROD_CODE */

	ButtonDebounce::startConfigurationList();

	/*******************************************
	 * Start everything back with new settings *
	 ******************************************/
	startHardware();

#if EFI_PROD_CODE && (BOARD_EXT_GPIOCHIPS > 0)
	/* TODO: properly restart gpio chips...
	 * This is only workaround for "CS pin lost" bug
	 * see: https://github.com/rusefi/rusefi/issues/2107
	 * We should provide better way to gracefully stop all
	 * gpio chips: set outputs to safe state, release all
	 * on-chip resources (gpios, SPIs, etc) and then restart
	 * with updated settings.
	 * Following code just re-inits CS pins for all external
	 * gpio chips, but does not update CS pin definition in
	 * gpio chips private data/settings. So changing CS pin
	 * on-fly does not work */
	startSmartCsPins();
#endif /* (BOARD_EXT_GPIOCHIPS > 0) */

    startKLine();

#if EFI_PROD_CODE && EFI_IDLE_CONTROL
	if (isIdleHardwareRestartNeeded()) {
		 initIdleHardware();
	}
#endif

#if EFI_BOOST_CONTROL
	startBoostPin();
#endif
#if EFI_EMULATE_POSITION_SENSORS
	startTriggerEmulatorPins();
#endif /* EFI_EMULATE_POSITION_SENSORS */
#if EFI_LOGIC_ANALYZER
	startLogicAnalyzerPins();
#endif /* EFI_LOGIC_ANALYZER */
#if EFI_VVT_PID
	startVvtControlPins();
#endif /* EFI_VVT_PID */

#if EFI_PROD_CODE && EFI_SENT_SUPPORT
	startSent();
#endif

	calcFastAdcIndexes();
}

#if EFI_PROD_CODE && EFI_BOR_LEVEL
void setBor(int borValue) {
	efiPrintf("setting BOR to %d", borValue);
	BOR_Set((BOR_Level_t)borValue);
}
#endif /* EFI_BOR_LEVEL */

// Called before configuration is loaded
void boardInitHardwareEarly() {
  // forcing migration to custom_board_InitHardwareEarly
}
void boardInitHardware() {
  // time to force migration to custom_board_InitHardware
}
void boardInitHardwareExtra() {
  // forcing migration to custom_board_InitHardwareExtra
}

// This function initializes hardware that can do so before configuration is loaded
void initHardwareNoConfig() {
	efiAssertVoid(ObdCode::CUSTOM_IH_STACK, hasLotsOfRemainingStack(), "init h");

	efiPrintf("initHardware()");

#if EFI_PROD_CODE
	initPinRepository();
#endif

#if EFI_PROD_CODE
	call_board_override(custom_board_InitHardwareEarly);
#endif

#if EFI_HISTOGRAMS
	/**
	 * histograms is a data structure for CPU monitor, it does not depend on configuration
	 */
	initHistogramsModule();
#endif /* EFI_HISTOGRAMS */

#if EFI_GPIO_HARDWARE
	/**
	 * We need the LED_ERROR pin even before we read configuration
	 */
	initPrimaryPins();
#endif // EFI_GPIO_HARDWARE

#if EFI_PROD_CODE && EFI_SIGNAL_EXECUTOR_ONE_TIMER
	// it's important to initialize this pretty early in the game before any scheduling usages
	initSingleTimerExecutorHardware();
#endif // EFI_PROD_CODE && EFI_SIGNAL_EXECUTOR_ONE_TIMER

#if EFI_PROD_CODE && EFI_RTC
	initRtc();
#endif // EFI_PROD_CODE && EFI_RTC

#if EFI_CONFIGURATION_STORAGE
	initFlash();
#endif

#if EFI_FILE_LOGGING
	initEarlyMmcCard();
#endif // EFI_FILE_LOGGING

#if HAL_USE_PAL && EFI_PROD_CODE
	// this should be initialized before detectBoardType()
	efiExtiInit();
#endif // HAL_USE_PAL
}

void stopHardware() {
	// board releases its user-configurable pins while activeConfiguration still describes them
	call_board_override(custom_board_StopHardware);

	stopSwitchPins();

#if EFI_PROD_CODE && (BOARD_EXT_GPIOCHIPS > 0)
	stopSmartCsPins();
#endif /* (BOARD_EXT_GPIOCHIPS > 0) */

#if EFI_LOGIC_ANALYZER
	stopLogicAnalyzerPins();
#endif /* EFI_LOGIC_ANALYZER */

#if EFI_EMULATE_POSITION_SENSORS
	stopTriggerEmulatorPins();
#endif /* EFI_EMULATE_POSITION_SENSORS */

#if EFI_VVT_PID
	stopVvtControlPins();
#endif /* EFI_VVT_PID */
}

/**
 * This method is invoked both on ECU start and configuration change
 * At the moment we have too many system which handle ECU start and configuration change separately
 * TODO: move move hardware code here
 */
void startHardware() {
#if EFI_SHAFT_POSITION_INPUT
	initStartStopButton();
#endif

#if EFI_PROD_CODE && EFI_SHAFT_POSITION_INPUT
	startTriggerInputPins();
#endif /* EFI_SHAFT_POSITION_INPUT */

#if EFI_ENGINE_CONTROL
	enginePins.startPins();
#endif /* EFI_ENGINE_CONTROL */

#if EFI_SHAFT_POSITION_INPUT
	validateTriggerInputs();

#endif // EFI_SHAFT_POSITION_INPUT

	startSwitchPins();

#if EFI_CAN_SUPPORT
	startCanPins();
#endif /* EFI_CAN_SUPPORT */

	// board claims its user-configurable pins from engineConfiguration; runs on both boot and burn
	call_board_override(custom_board_StartHardware);
}

PUBLIC_API_WEAK void setPinConfigurationOverrides() { }

#if HAL_USE_I2C
const I2CConfig i2cfg = {
    OPMODE_I2C,
    400000,
    FAST_DUTY_CYCLE_2,
};
#endif

void initHardware() {
	if (hasFirmwareError()) {
		return;
	}

#if EFI_PROD_CODE && STM32_I2C_USE_I2C3
	if (engineConfiguration->useEeprom) {
	    i2cStart(&EE_U2CD, &i2cfg);
	}
#endif // STM32_I2C_USE_I2C3

	call_board_override(custom_board_InitHardware);
#if EFI_PROD_CODE
	// this applies some board configurations
	call_board_override(custom_board_OnConfigurationChange, nullptr);
#endif // EFI_PROD_CODE

	call_board_override(custom_board_InitHardwareExtra);

#if HAL_USE_ADC
	initAdcInputs();
#endif /* HAL_USE_ADC */

#if EFI_SOFTWARE_KNOCK
	initSoftwareKnock();
#endif /* EFI_SOFTWARE_KNOCK */

#ifdef TRIGGER_SCOPE
	initTriggerScope();
#endif // TRIGGER_SCOPE

#if HAL_USE_SPI
	initSpiModules();
#endif /* HAL_USE_SPI */

#if (EFI_PROD_CODE && BOARD_EXT_GPIOCHIPS > 0) || EFI_SIMULATOR
	// initSmartGpio depends on 'initSpiModules'
	initSmartGpio();
#endif

	// output pins potentially depend on 'initSmartGpio'
	initMiscOutputPins();

#if EFI_MC33816
	initMc33816();
#endif /* EFI_MC33816 */

#if EFI_CAN_SUPPORT
#if EFI_SIMULATOR
	// Set CAN device name
	CAND1.deviceName = "can0";
	CAND2.deviceName = "can1";
	CAND3.deviceName = "can2";
#endif

	initCan();
#endif /* EFI_CAN_SUPPORT */


#if EFI_PROD_CODE && EFI_SHAFT_POSITION_INPUT
	onEcuStartTriggerImplementation();
#endif /* EFI_SHAFT_POSITION_INPUT */
	onEcuStartDoSomethingTriggerInputPins();

#if EFI_WS2812
	initWS2812();
#endif /* EFI_LED_WS2812 */

#if EFI_ONBOARD_MEMS
	initAccelerometer();
#endif

#if EFI_BOSCH_YAW
	initBoschYawRateSensor();
#endif /* EFI_BOSCH_YAW */

#if EFI_UART_GPS
	initGps();
#endif

#if EFI_CDM_INTEGRATION
	cdmIonInit();
#endif // EFI_CDM_INTEGRATION

#if EFI_PROD_CODE && EFI_SENT_SUPPORT
	initSent();
#endif

	initKLine();

#if EFI_DAC
	initDac();
#endif

	calcFastAdcIndexes();

	startHardware();

	efiPrintf("initHardware() OK!");
}
