ElDominio/rusefi/firmware/controllers/algo/engine_state_machine.h

#pragma once

#include "engine_module.h"
#include "hysteresis.h"
#include "engine_state_machine_state_generated.h"
#include <rusefi/timer.h>

enum class PopsAndBangsState : uint8_t {
	Inactive = 0,
	Active   = 1,
	Expired  = 2,
};

enum class EngineStateMachineState : uint8_t {
	Off          = 0,
	Cranking     = 1,
	Afterstart   = 2,
	Idle         = 3,
	Coasting     = 4,
	Transient    = 5,
	WOT          = 6,
	Cruising     = 7,
	Overrun      = 8,
	LaunchControl = 9,
	Upshifting   = 10,
	Downshifting = 11,
	Limp         = 12,
	Eco          = 13,
	Accelerating = 14,
	Decelerating = 15,
};

// A shift window that stays open longer than this is considered stale and is closed.
static constexpr efitimems_t SM_SHIFT_TIMEOUT_MS = 3000;

class EngineStateMachine : public engine_state_machine_state_s, public EngineModule {
public:
	using interface_t = EngineStateMachine;

	void onSlowCallback() override;

	EngineStateMachineState getCurrentState() const;
	bool isEnabled() const;

	// RPM rate of change from the last slow callback (RPM/s). Used by DFCO for the
	// no-VSS Decel fuel-cut fallback where engineSmIsDecelerating cannot fire.
	float getLastRpmRate() const { return m_lastRpmRate; }

	// Drives the P&B state machine off the given overrun state.
	// Public so unit tests can call it directly without needing a full slow-callback setup.
	void updatePopsAndBangs(bool isOverrun);

	// Drives the Eco mode overlay: engages after the engine has been Cruising (brief AE-driven
	// Transient blips tolerated) continuously for ecoModeCruisingTime with MAP at or below
	// ecoModeMapLimit, drops instantly on leaving Cruising/Transient or exceeding the MAP limit,
	// and can be inhibited by a manual switch / Lua gauge. Mutually exclusive with Sport Mode
	// (engineSmIsSportMode out-votes eco, same as Limp). Takes the current state directly so
	// unit tests can drive it without standing up the full state determination.
	void updateEcoMode(EngineStateMachineState currentState);
	void updateSportMode();
	void updateGhostCam();
	void updateSportPedal();

	// P&B spark-cut overlay: returns the spark skip ratio (0..1) to feed the hard spark
	// limiter. Non-zero only while a cut window is open (every popsAndBangsCutEveryRevs
	// revolutions, held for popsAndBangsCutDurationMs), so raw fuel charges the exhaust and
	// is re-lit when the window closes. Returns 0 outside the window.
	float getPopsAndBangsSparkSkipRatio();

	// Latches the engine into Limp mode. Once latched, the engineSmIsLimp overlay stays set
	// (published every slow callback) and the configured limp limits — rev / boost / ETB /
	// timing / AFR — are enforced by their respective subsystems until power cycle.
	//
	// Currently the only caller is LimpManager::reportEtbJammed (ETB jam). Other fault
	// conditions could call this in the future — see the TODO in onSlowCallback().
	void reportLimpCondition();

private:
	EngineStateMachineState determineState(float rpm, float tps, float vss);
	void updateShiftDetection(float tps, float rpm, float vss, efitimems_t nowMs);
	void updateShiftAccumulator(float rpm, float vss, efitimems_t nowMs);
	bool evaluateShiftDirection(bool isUpshift, float currentVss);
	// Steady-state clutch read (not edge-triggered) used to decide whether the transmission is
	// currently transmitting road load to the engine. Defaults to "always engaged" when no
	// clutch switch is configured, per smUpshiftClutchSwitch/smDownshiftClutchSwitch.
	bool isTransmissionEngaged() const;

	// Remaining slow-callback hold-off periods after AE threshold drops
	uint8_t m_transientHoldoffRemaining = 0;

	// Current computed state — uint8_t stores are atomic in hardware on Cortex-M
	EngineStateMachineState m_currentState = EngineStateMachineState::Off;

	// Shift detection window state
	bool         m_shiftWindowOpen   = false;
	bool         m_shiftIsUpshift    = false;
	efitimems_t  m_shiftWindowOpenMs = 0;
	// Raw physical clutch switch states from the previous call, used for edge detection.
	// Tracked independently of which direction(s) are configured to use which switch, so a
	// switch can be consulted for early-open/early-close even when it isn't the one assigned
	// to the direction currently being evaluated (see smSecondClutchSwitchAvailable).
	bool         m_prevClutchUp      = false;
	bool         m_prevClutchDown    = false;

	// Shift latch: once a direction is confirmed, Upshifting/Downshifting is held true until
	// this deadline, masking flicker from the accumulator (smShiftLatchTimeMs).
	// Tracked separately from m_shiftIsUpshift so a new window opening in the opposite
	// direction doesn't retroactively flip the direction of a still-active latch.
	bool         m_shiftLatched         = false;
	bool         m_shiftLatchedIsUpshift = false;
	efitimems_t  m_shiftLatchUntilMs     = 0;

	// Shift-direction accumulator: integrates pre-shift rate signal into -100..+100.
	// Positive = upshift evidence, negative = downshift evidence.
	// Runs only while the clutch is engaged (window closed); frozen during the shift window;
	// reset to 0 when the window closes (shift complete).
	float        m_shiftAccumulator     = 0;
	efitimems_t  m_accumulatorLastMs    = 0;
	float        m_accumulatorLastRpm   = 0;
	float        m_accumulatorLastVss   = 0;

	// Continuous dwell in the Accelerating state / Decelerating+Overrun states, used by the
	// smAccumulatorSnapTimeMs override: reset the instant we leave the respective state(s), so
	// hasElapsedMs() measures time since the most recent entry (see updateShiftAccumulator()).
	Timer        m_accelStateTimer;
	Timer        m_decelStateTimer;

	// Accelerating hold: reset every tick the rate threshold is met, so a fresh crossing
	// extends the hold back to the full smAccelHoldMs duration (see determineState()).
	Timer m_accelHoldTimer;

	// RPM rate of change (RPM/s), recomputed only once every smRpmRateWindowMs (floored to one
	// slow-callback tick, 50 ms) rather than on every tick -- so the value visibly updates at
	// the cadence the user configures instead of continuously. Between recomputes this holds
	// the last computed rate. Stored for use by determineState() on the next tick (one
	// slow-callback lag on top of the window itself — acceptable for state detection).
	float        m_lastRpmRate          = 0;

	// Anchor sample (timestamp, RPM) that the next recompute will be measured against.
	efitimems_t m_rpmRateAnchorMs  = 0;
	float       m_rpmRateAnchorRpm = 0;
	bool        m_rpmRateHasAnchor = false;

	// Returns m_lastRpmRate unchanged (held) until at least smRpmRateWindowMs has elapsed since
	// the last recompute, at which point it computes RPM/s over the *actual* elapsed time since
	// the anchor sample (not the nominal window, so the result stays exact RPM/s regardless of
	// tick jitter) and re-anchors on (nowMs, rpm). Returns 0 on the very first-ever call, when
	// there's no anchor yet.
	float recordRpmSampleAndComputeRate(float rpm, efitimems_t nowMs);

	void updateTempOverlay();

	// Limp mode latch — set by reportLimpCondition(), never auto-cleared (matches the old
	// ETB-jam behaviour which persisted until reboot). TODO: an un-latch path (e.g. a
	// settings command or a clean key cycle) could be added later if desired.
	bool m_limpModeLatched = false;

	// Eco mode overlay state
	bool isEcoModeSwitchAsserted() const; // manual switch / Lua gauge currently asserting
	bool isEcoModeInhibited() const;      // asserted in Inhibit mode
	Timer m_ecoCruiseTimer;               // measures continuous time in the Cruising state

	// Eco mode's own actuation (ecoThrottleMult, VVT override) is a real RPM-rate transient but
	// not driver-initiated; misreading it as Accelerating/Decelerating would bounce eco straight
	// back off. Armed for smTransientHoldoffCallbacks ticks on any engineSmIsEcoMode edge (see
	// onSlowCallback()) and consumed by determineState() to suppress the RPM-rate check.
	bool    m_prevEcoModeActive        = false;
	uint8_t m_ecoSettleHoldoffRemaining = 0;

	// Pops and Bangs state machine
	bool isPopsAndBangsBlocked() const;
	PopsAndBangsState m_pnbState  = PopsAndBangsState::Inactive;
	bool m_wasPnbOverrun          = false;
	Timer m_pnbOverrunTimer;
	Timer m_pnbActiveTimer;

	// P&B spark-cut overlay state
	bool m_pnbCutActive           = false;  // currently inside a spark-cut window
	uint32_t m_pnbLastFireRev     = 0;      // revolution counter at the last resume-firing point
	float m_pnbCutDurationMs      = 0;      // duration chosen for the current cut window
	Timer m_pnbCutWindowTimer;              // measures the current cut window
};
