ElDominio/rusefi/firmware/config/boards/hellen/alphax-silver/board_engine_configuration.txt

bit boardUseTempPullUp,"With Pull Ups","Piggyback Mode"
bit boardSelTachPullUp,"+12V","+5V"
bit boardEnHall1PullUp,"Enable","Disable"
bit boardEnHall2PullUp,"Enable","Disable"
bit boardEnHall34PullUp,"Enable","Disable"
